OpeningDesign/Aalseth_Residence/Transfer/20181026 - from Sanitary District - Design drawings/3196 Aalseth.pdf

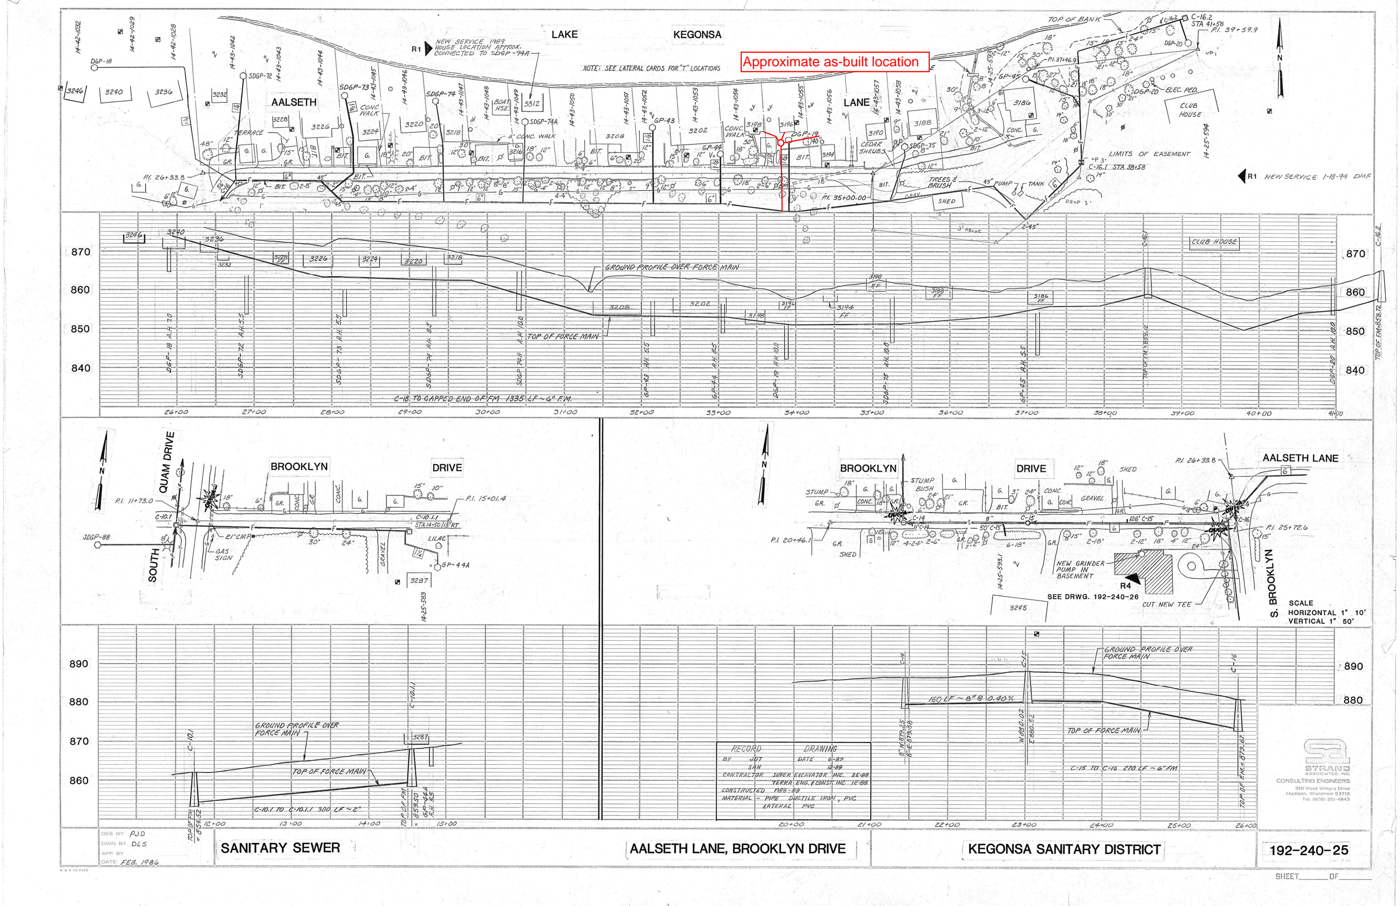
[picture p3: page 1]
