OpeningDesign/Aalseth_Residence/Transfer/20181026 - from Sanitary District - Design drawings/DH152-160002.pdf

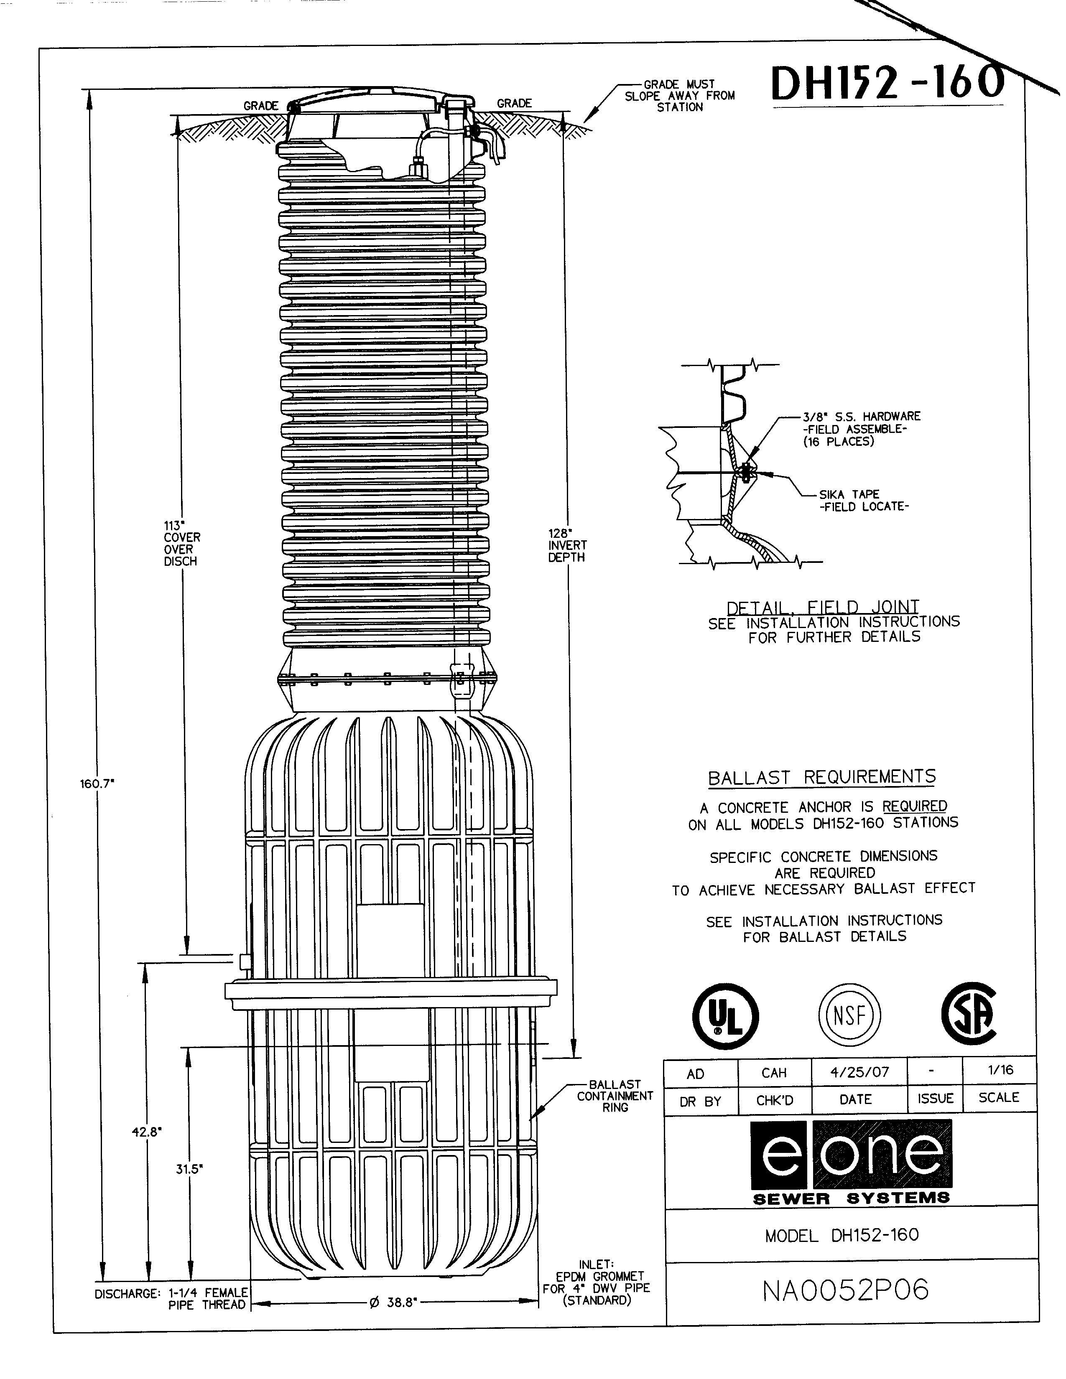
[picture p4: page 1]
