OpeningDesign/Aalseth_Residence/Transfer/20181026 - from Sanitary District - Design drawings/Easement and GP Lateral Card.pdf

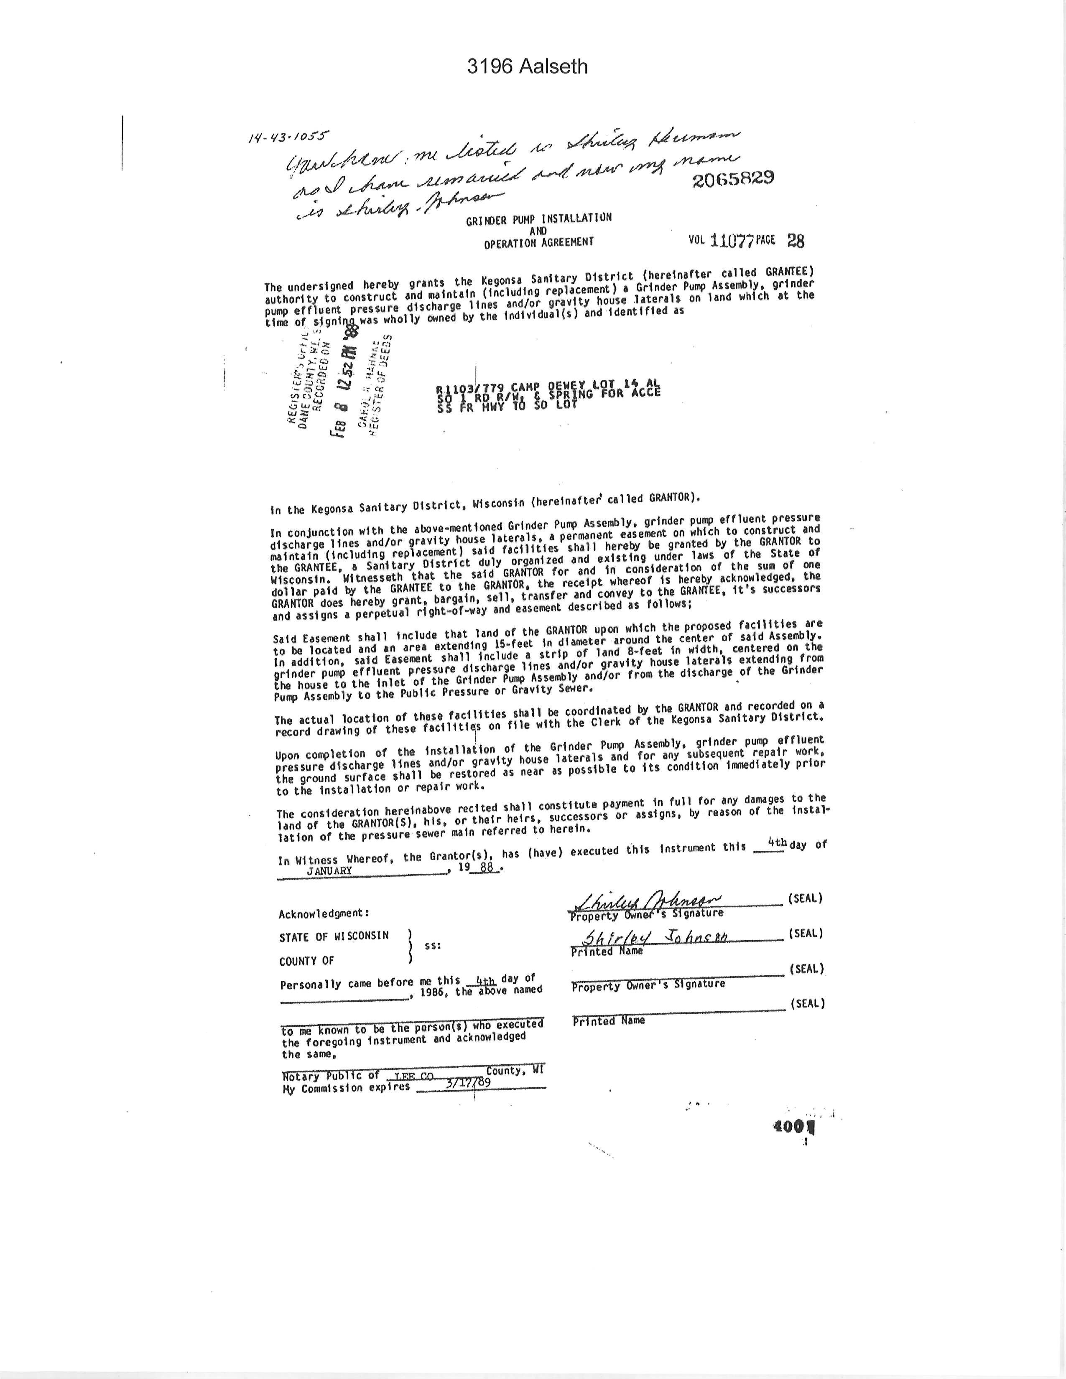
[picture p5: page 1]
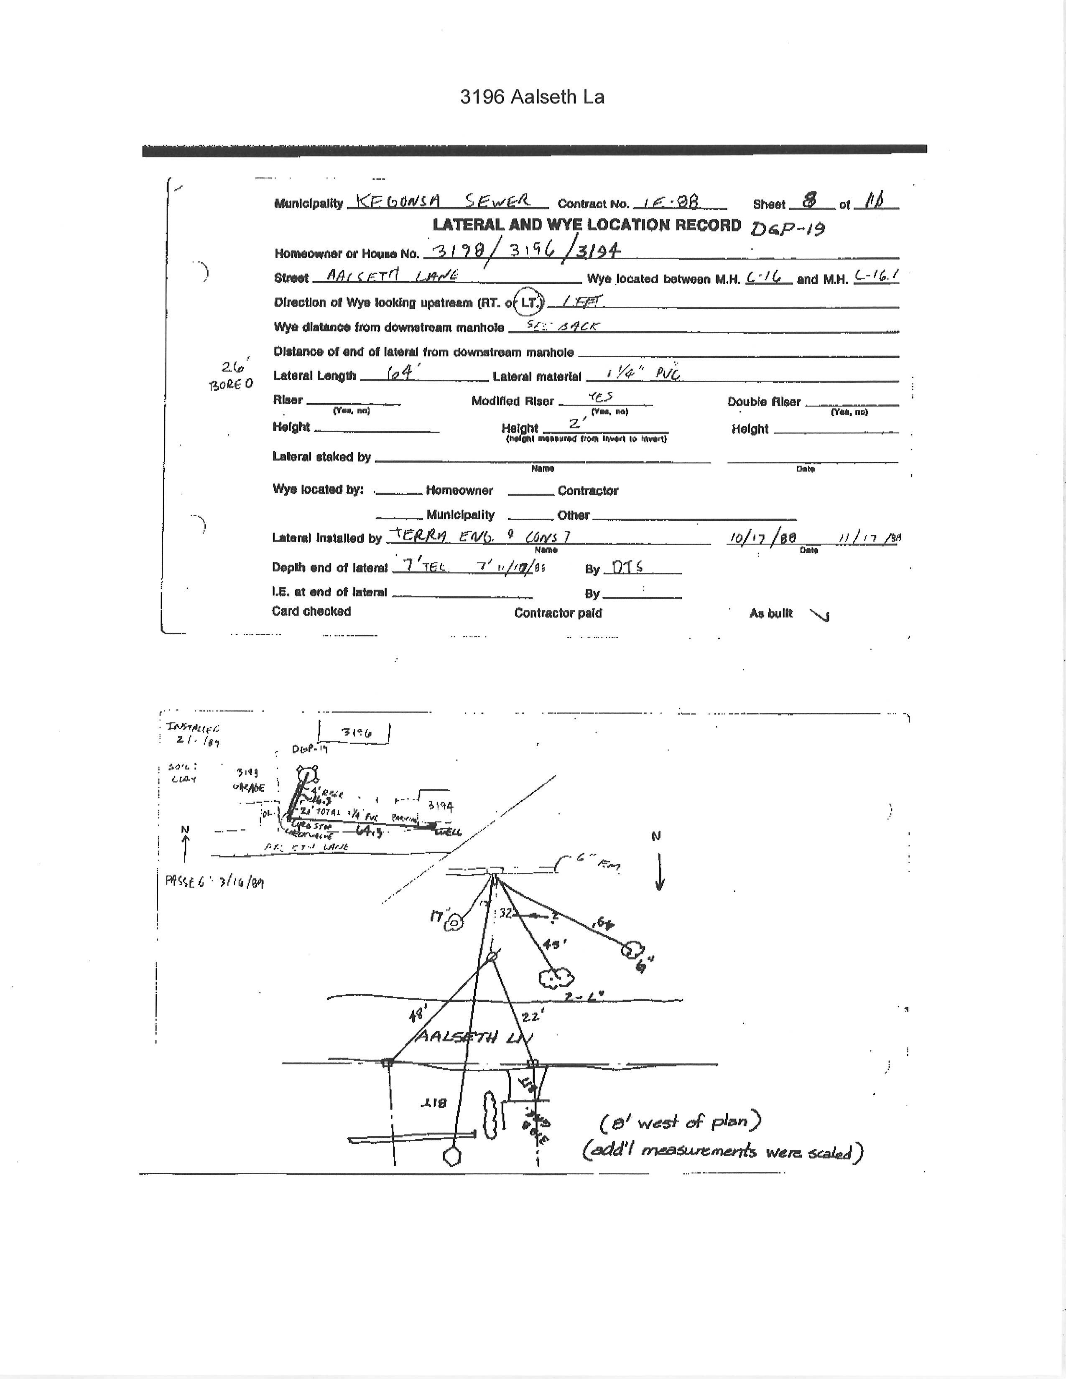
[picture p6: page 2]
