OpeningDesign/Aalseth_Residence/Transfer/20181026 - from Sanitary District - Design drawings/GP Detail.pdf

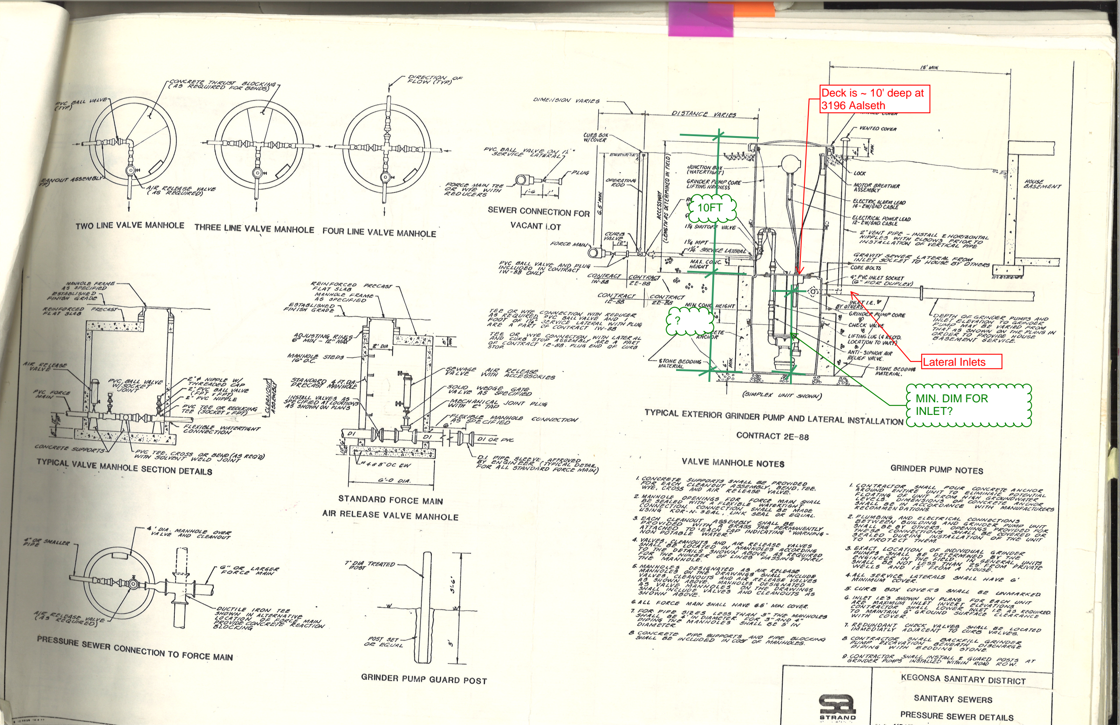
[picture p7: page 1]
