OpeningDesign/Aalseth_Residence/Transfer/20191013 - from STRUCT - stair details/2019-10-13 Cantilevered Stair Details.pdf

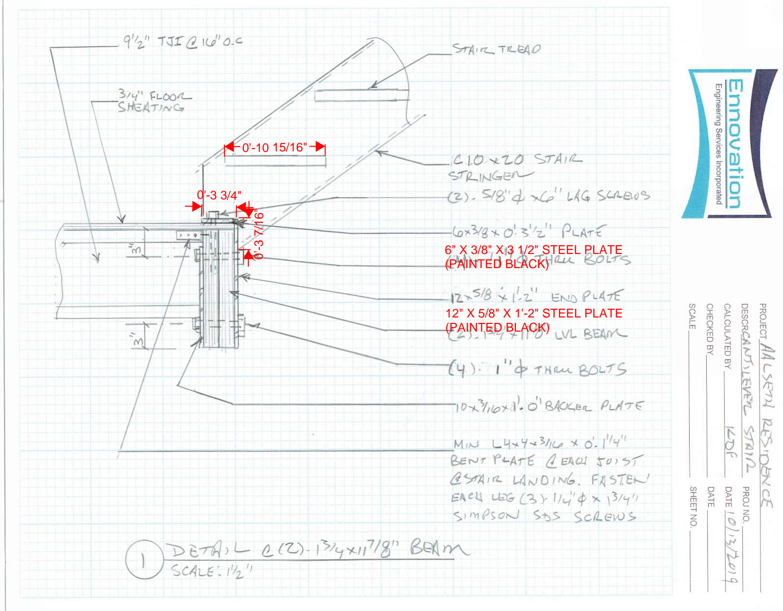
[picture p8: page 1]
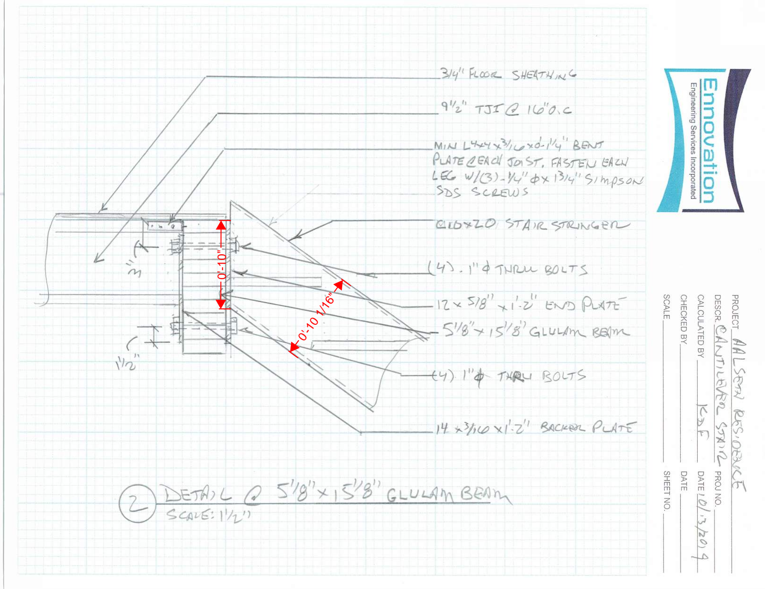
[picture p9: page 2]
