OpeningDesign/Aalseth_Residence/Models & CAD/BIM/Renderings/20191110 - stair/Enscape_2019-11-10-22-44-05.png

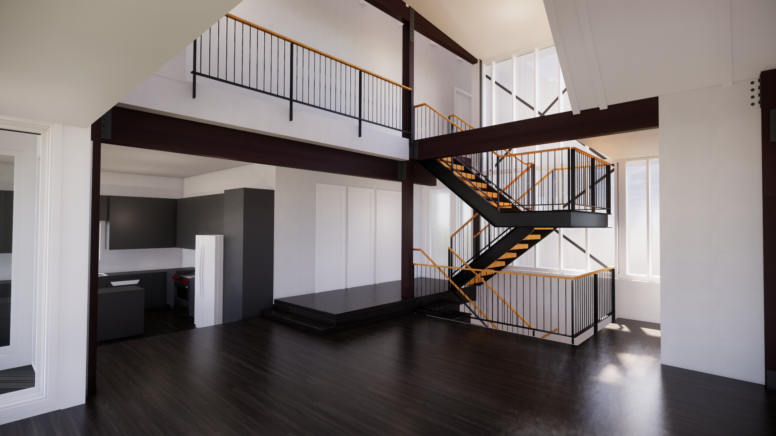
Models & CAD/BIM/Renderings/20191110 - stair/Enscape_2019-11-10-22-44-05.png
