OpeningDesign/Aalseth_Residence/Models & CAD/BIM/Renderings/20191110 - stair/Enscape_2019-11-10-23-39-31.png

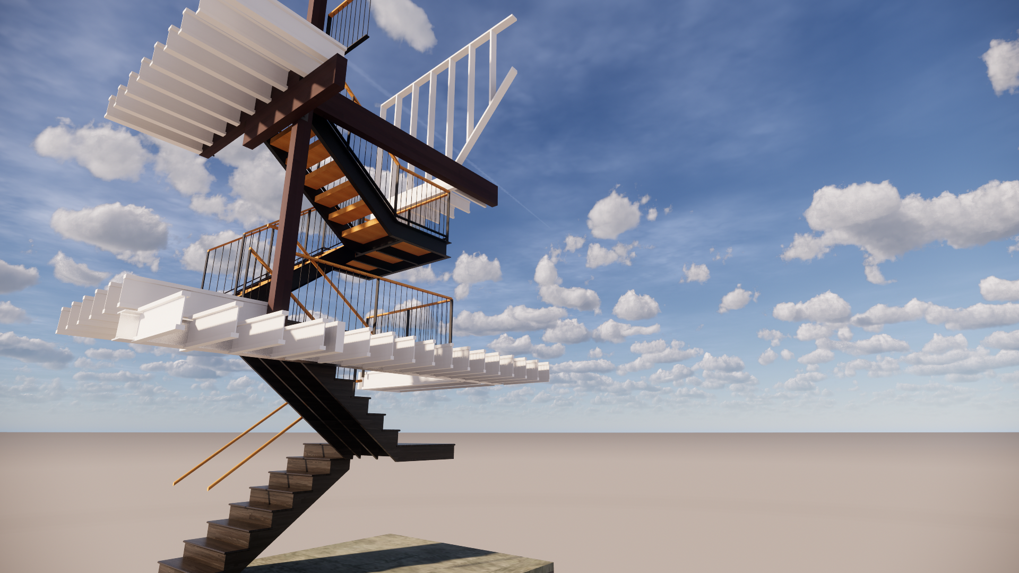
Models & CAD/BIM/Renderings/20191110 - stair/Enscape_2019-11-10-23-39-31.png
