OpeningDesign/Aalseth_Residence/Research and CA/Research and Submittals/_Existing Conditions & Code Research/Existing Conditions/2018-06-04_13-52-42_chrome.jpg

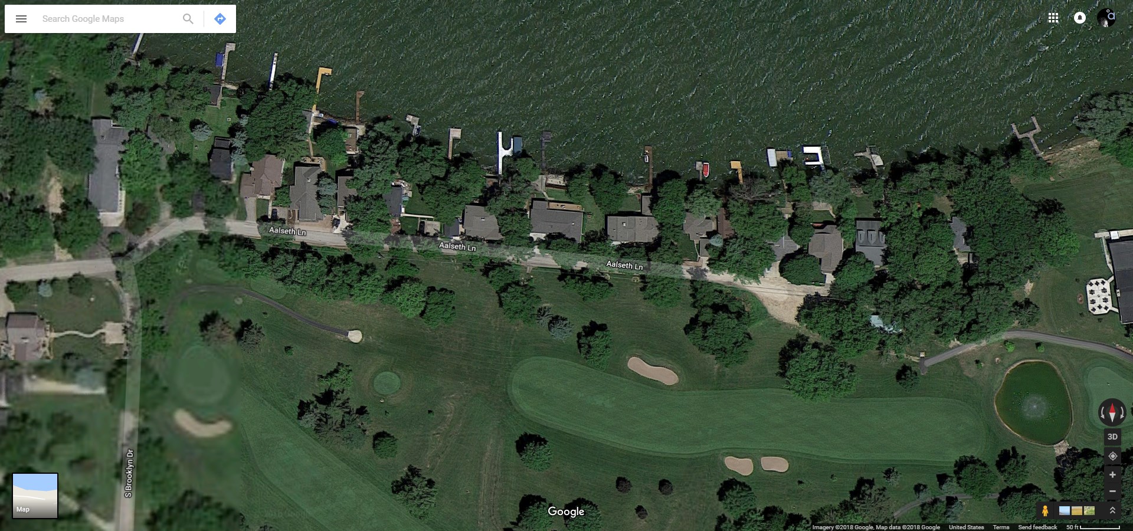
Research and CA/Research and Submittals/_Existing Conditions & Code Research/Existing Conditions/2018-06-04_13-52-42_chrome.jpg
