OpeningDesign/Aalseth_Residence/Research and CA/Research and Submittals/_Existing Conditions & Code Research/Existing Conditions/topo.jpg

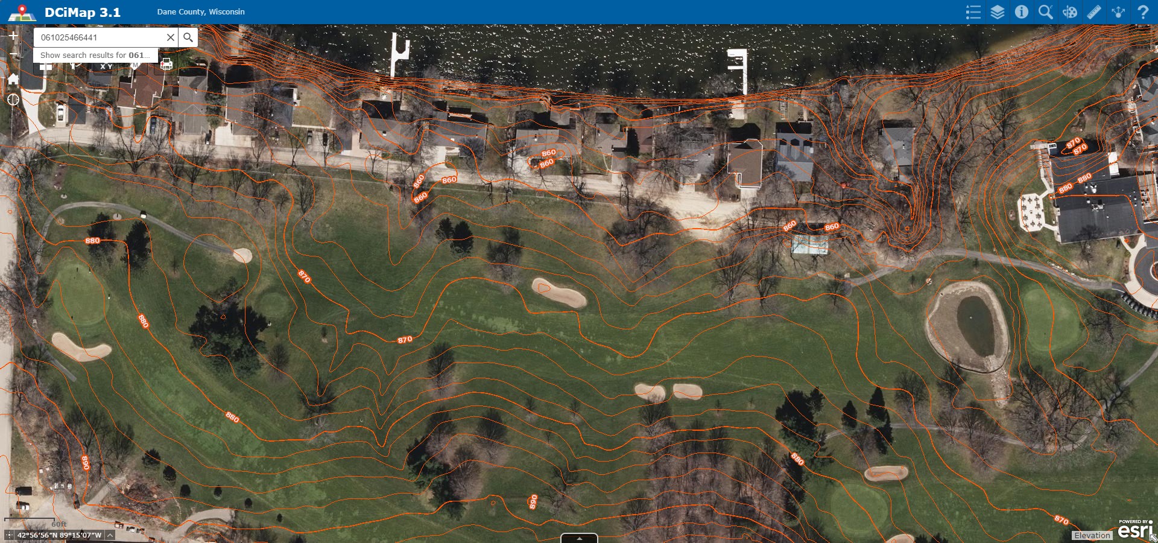
Research and CA/Research and Submittals/_Existing Conditions & Code Research/Existing Conditions/topo.jpg
