OpeningDesign/Aalseth_Residence/Research and CA/Research and Submittals/_Existing Conditions & Code Research/Existing Conditions/zoning area map.png

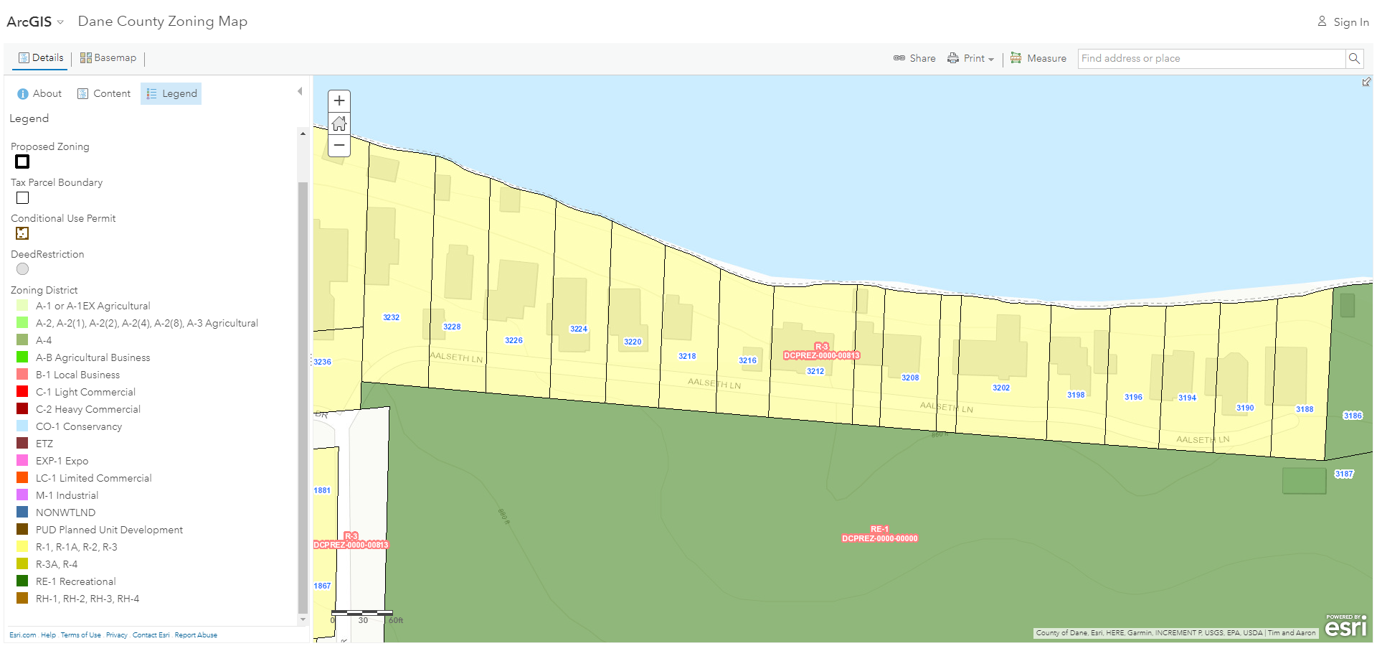
Research and CA/Research and Submittals/_Existing Conditions & Code Research/Existing Conditions/zoning area map.png
