OpeningDesign/Aalseth_Residence/Research and CA/Research and Submittals/A10 Foundations/A1010 Standard Foundations/Holddowns/2018-12-19_11-43-12.png

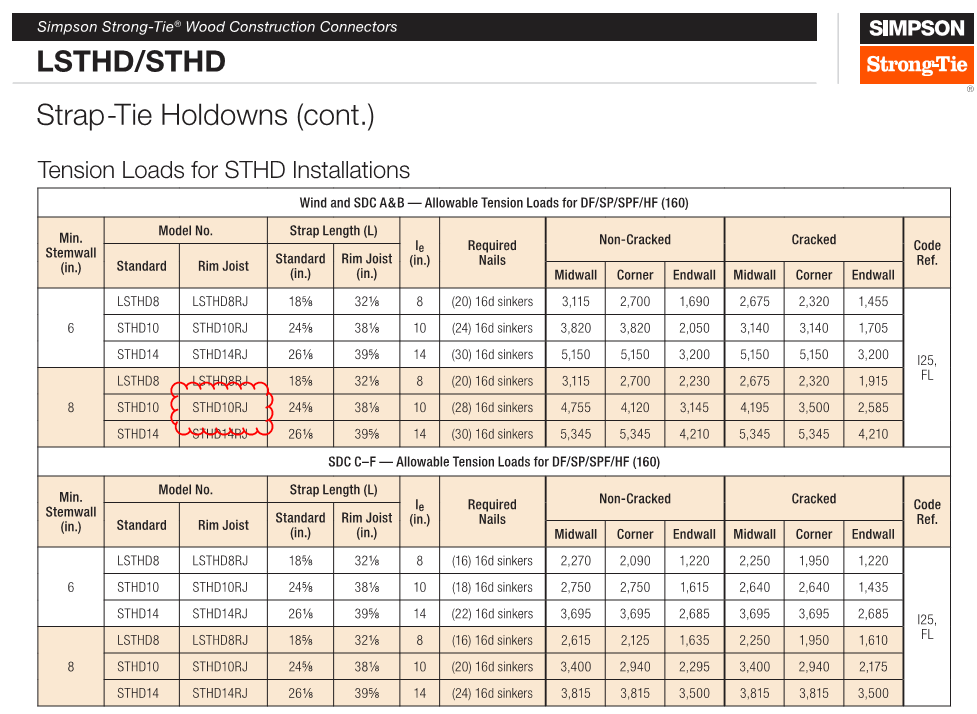
Research and CA/Research and Submittals/A10 Foundations/A1010 Standard Foundations/Holddowns/2018-12-19_11-43-12.png
