OpeningDesign/Aalseth_Residence/Research and CA/Site Reports and Photos/20190711_182300.jpg

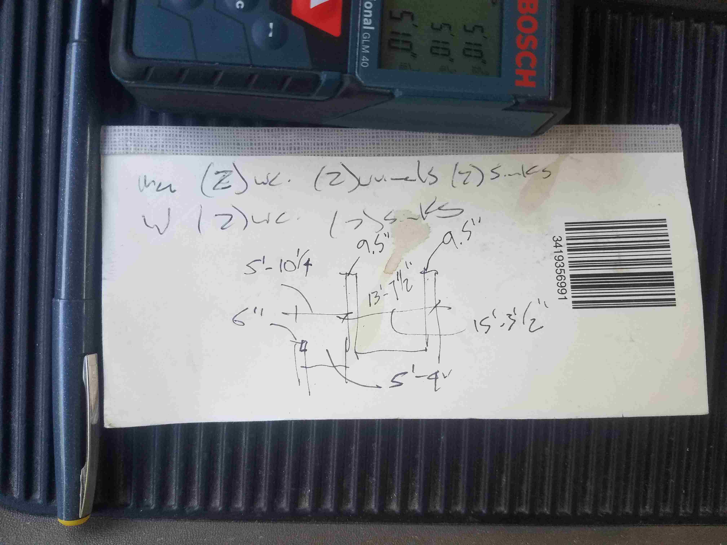
Research and CA/Site Reports and Photos/20190711_182300.jpg
