OpeningDesign/Aalseth_Residence/Transfer/20180706 - owner review/Enscape_2018-07-06-13-01-36.png

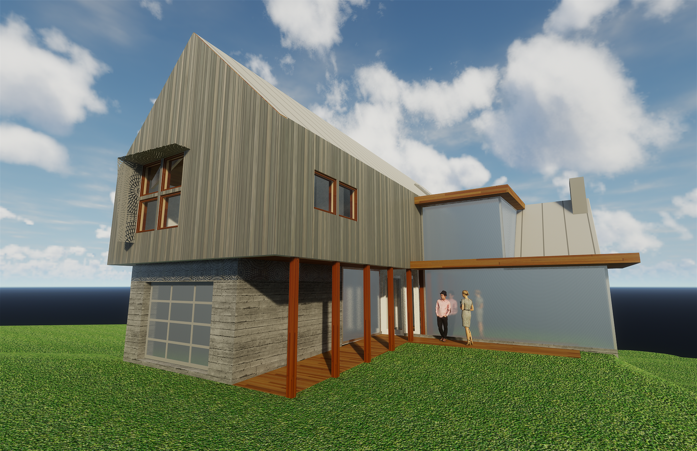
Transfer/20180706 - owner review/Enscape_2018-07-06-13-01-36.png
