OpeningDesign/Aalseth_Residence/Transfer/20180706 - owner review/jpgs/20180706 - Aalseth_Residence - Schematic Drawings Page 005.jpg

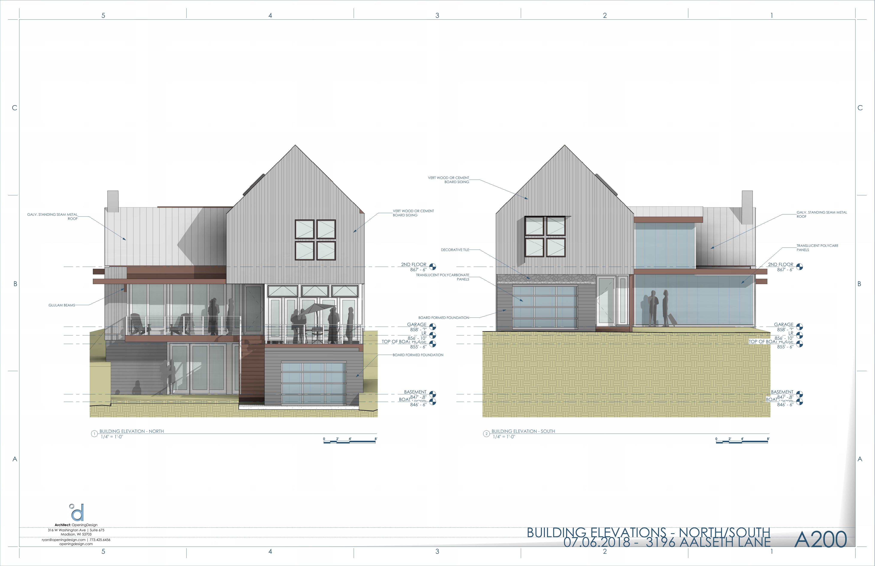
Transfer/20180706 - owner review/jpgs/20180706 - Aalseth_Residence - Schematic Drawings Page 005.jpg
