OpeningDesign/Aalseth_Residence/Transfer/20180711 - DWG to civil/20180711 - Aalseth_Residence - marked up Page 007.jpg

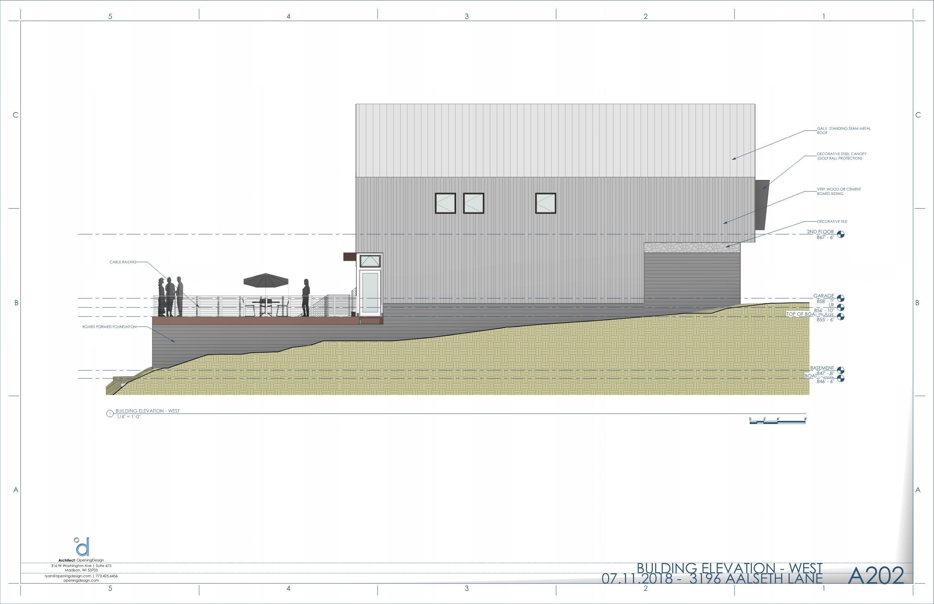
Transfer/20180711 - DWG to civil/20180711 - Aalseth_Residence - marked up Page 007.jpg
