OpeningDesign/Aalseth_Residence/Transfer/20181002 - from civil - marked up drawings/DitchVelocity Page 001.jpg

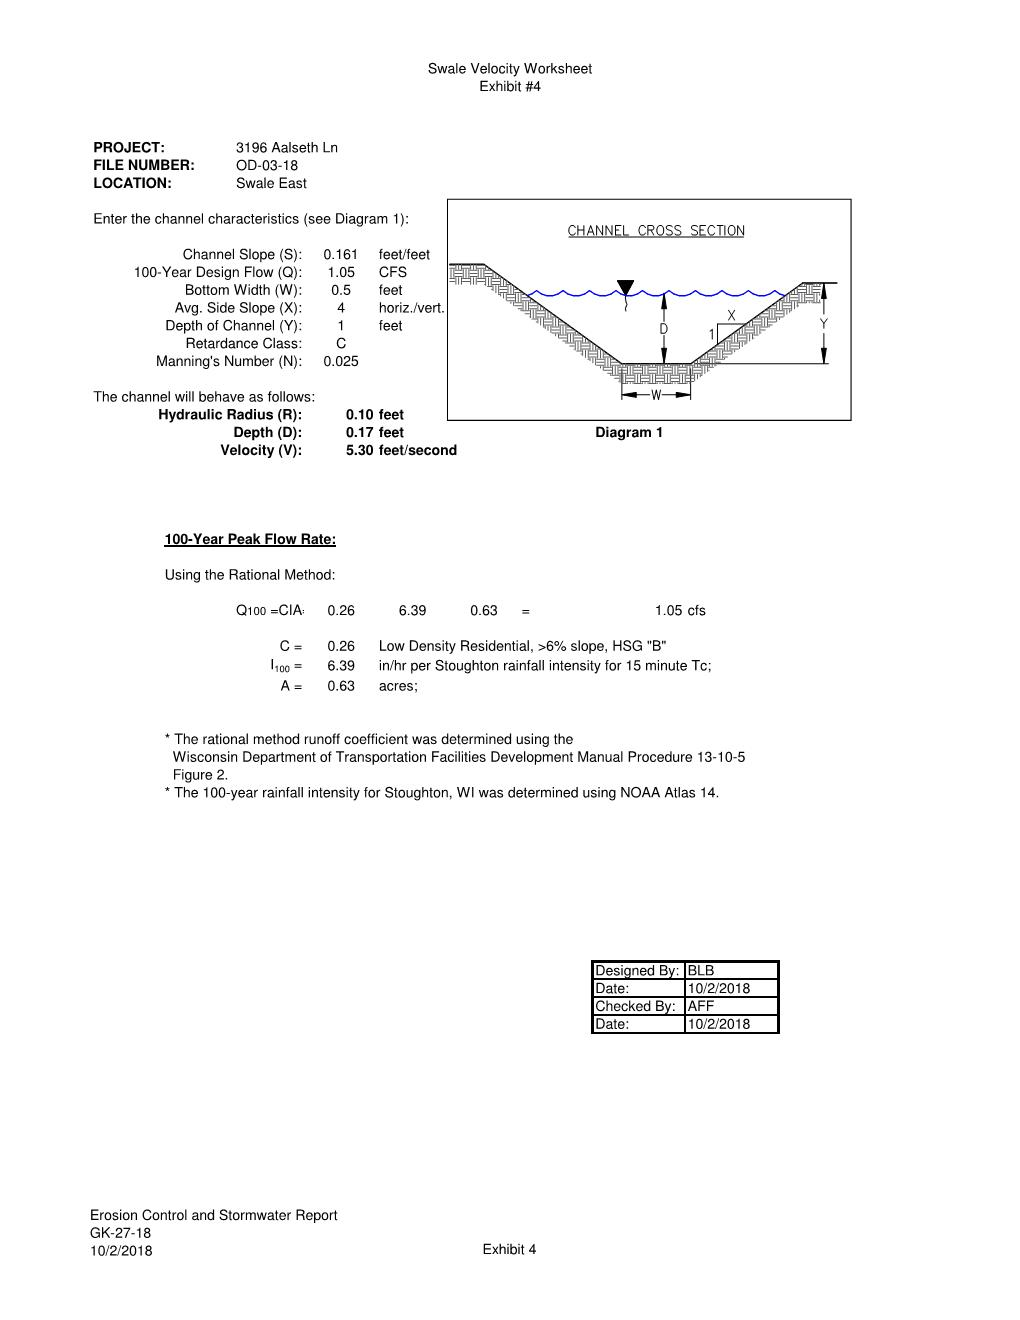
Transfer/20181002 - from civil - marked up drawings/DitchVelocity Page 001.jpg
