OpeningDesign/Aalseth_Residence/Transfer/20181002 - from civil - marked up drawings/ErosionMat.jpg

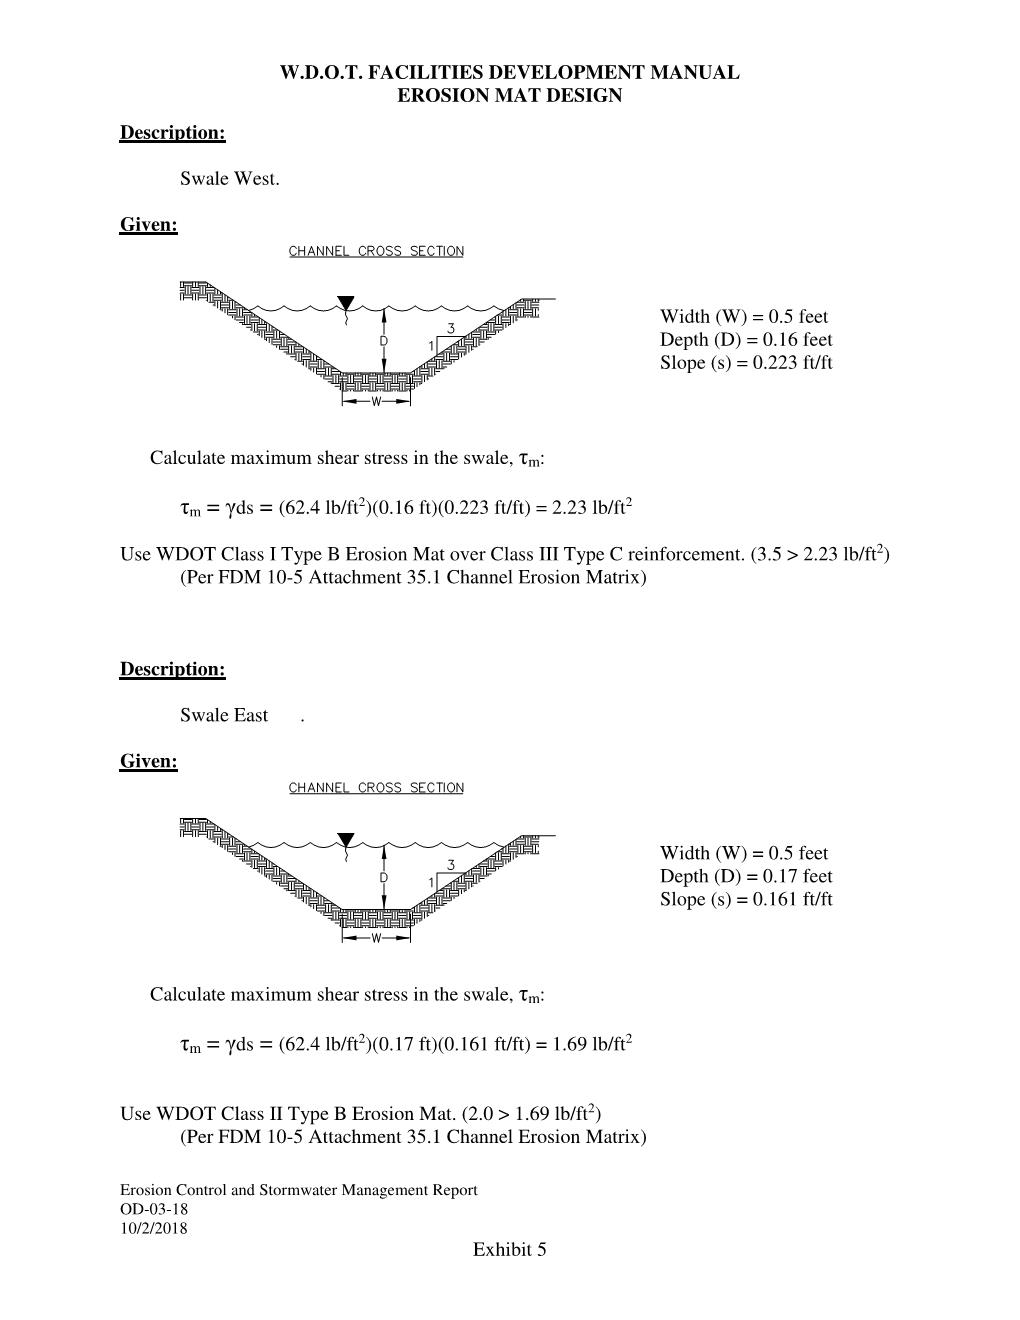
Transfer/20181002 - from civil - marked up drawings/ErosionMat.jpg
