OpeningDesign/Aalseth_Residence/Transfer/20181002 - from civil - marked up drawings/SwaleDetails.jpg

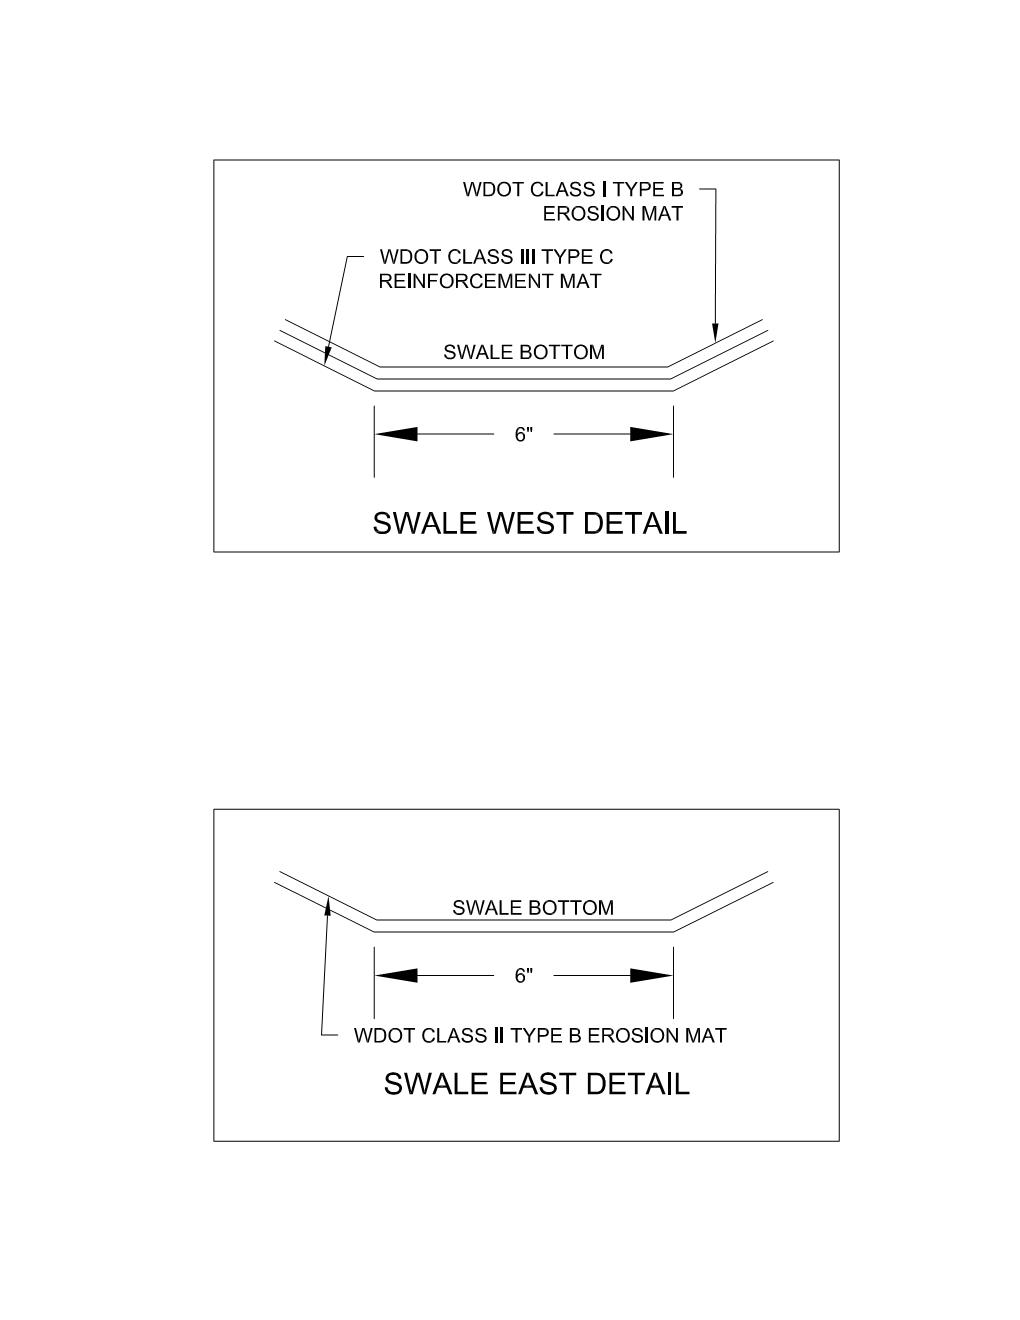
Transfer/20181002 - from civil - marked up drawings/SwaleDetails.jpg
