OpeningDesign/Aalseth_Residence/Transfer/20190108 - from Dane County - Notice to submit a location survey/20190125_095326.jpg

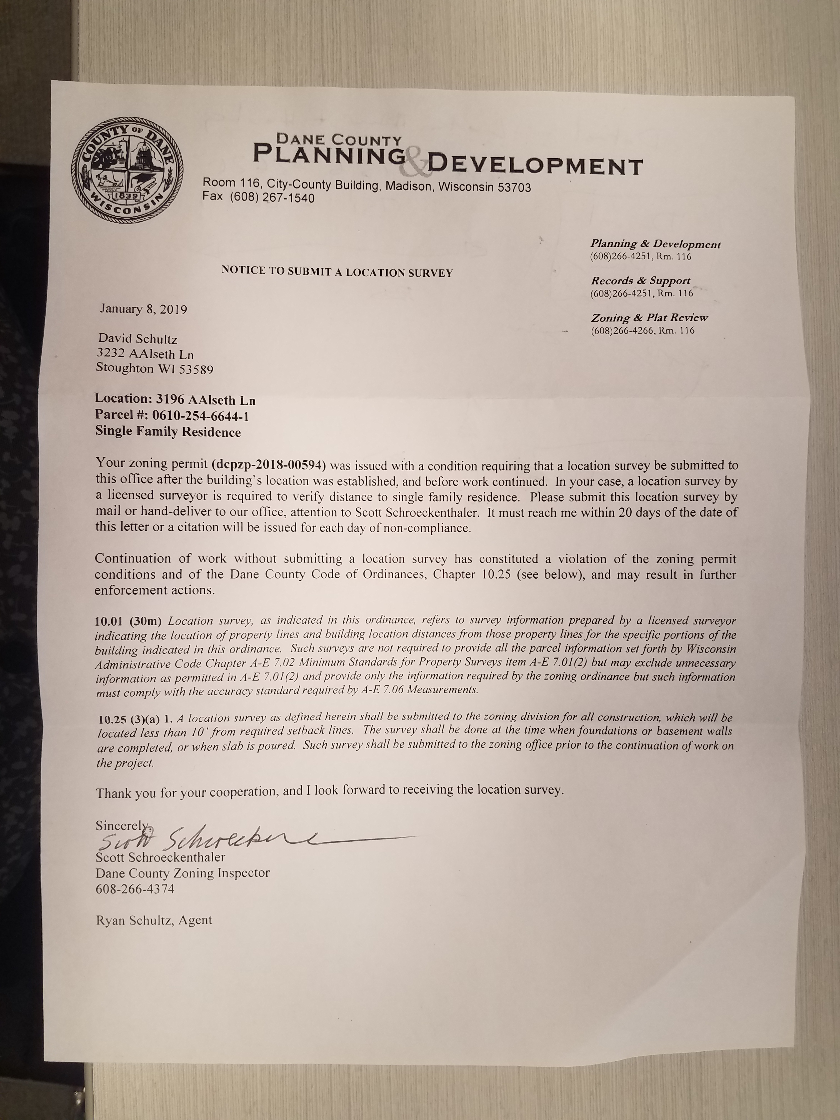
Transfer/20190108 - from Dane County - Notice to submit a location survey/20190125_095326.jpg
