OpeningDesign/Aalseth_Residence/Transfer/20190110 - ASK-01 - seam detail in concrete/20190110 - ASK-01 - seam detail in concrete2.jpg

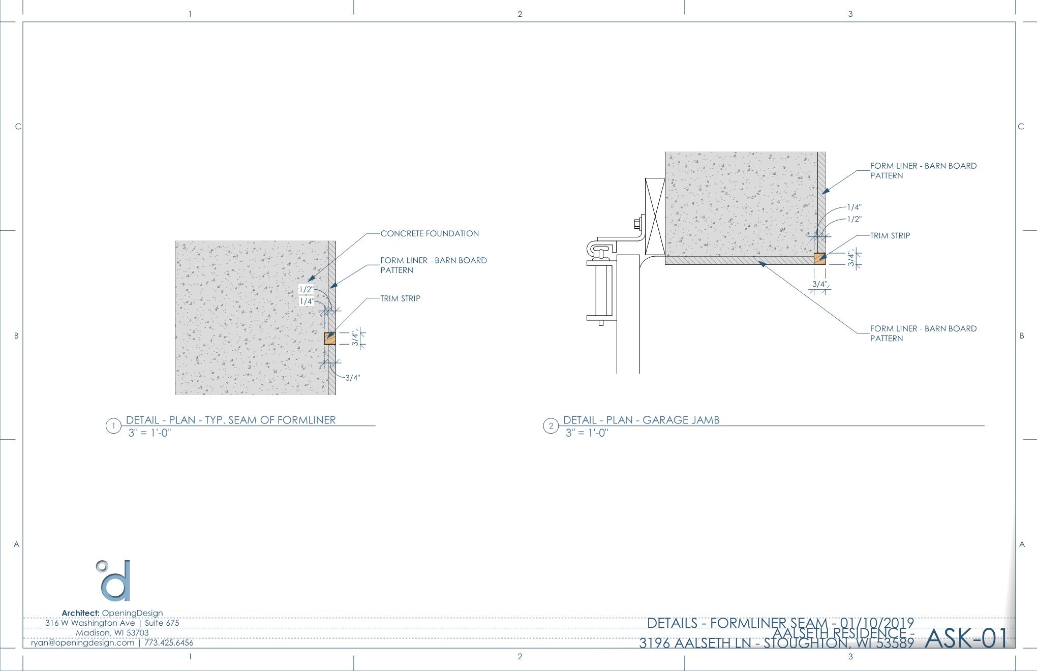
Transfer/20190110 - ASK-01 - seam detail in concrete/20190110 - ASK-01 - seam detail in concrete2.jpg
