OpeningDesign/Aalseth_Residence/Transfer/20190110 - ASK-01 - seam detail in concrete/201901101700 - ASK-01 - seam detail in concrete.jpg

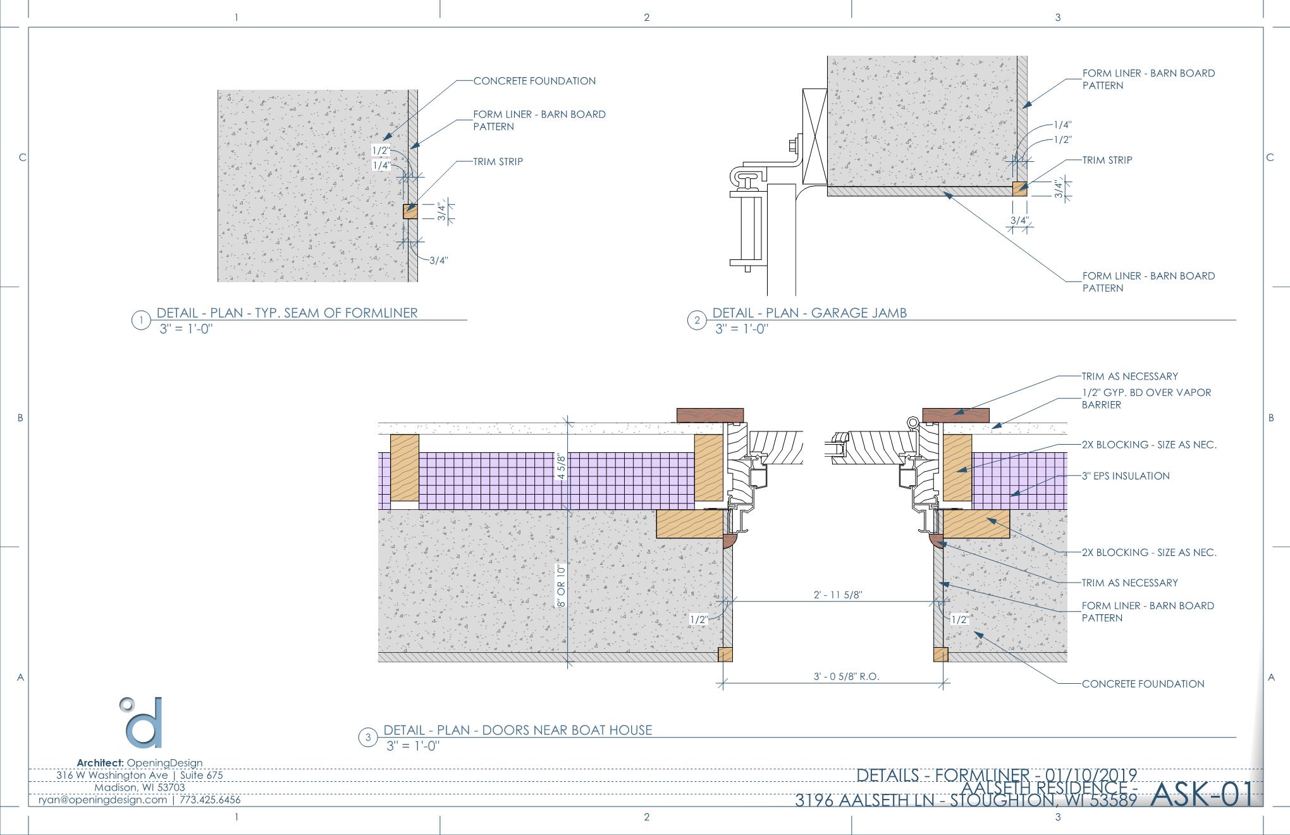
Transfer/20190110 - ASK-01 - seam detail in concrete/201901101700 - ASK-01 - seam detail in concrete.jpg
