OpeningDesign/Aalseth_Residence/Transfer/20190323 - meeting with potential owners/2019-03-21 18.45.19.jpg

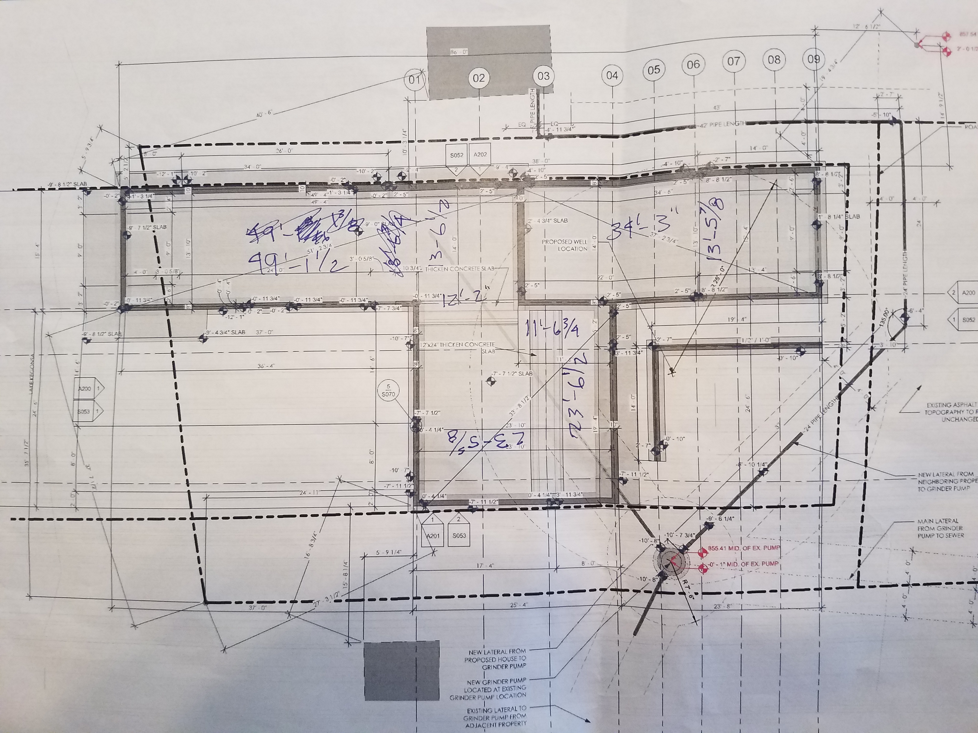
Transfer/20190323 - meeting with potential owners/2019-03-21 18.45.19.jpg
