OpeningDesign/Aalseth_Residence/Transfer/20190323 - meeting with potential owners/2019-03-23 11.27.37.jpg

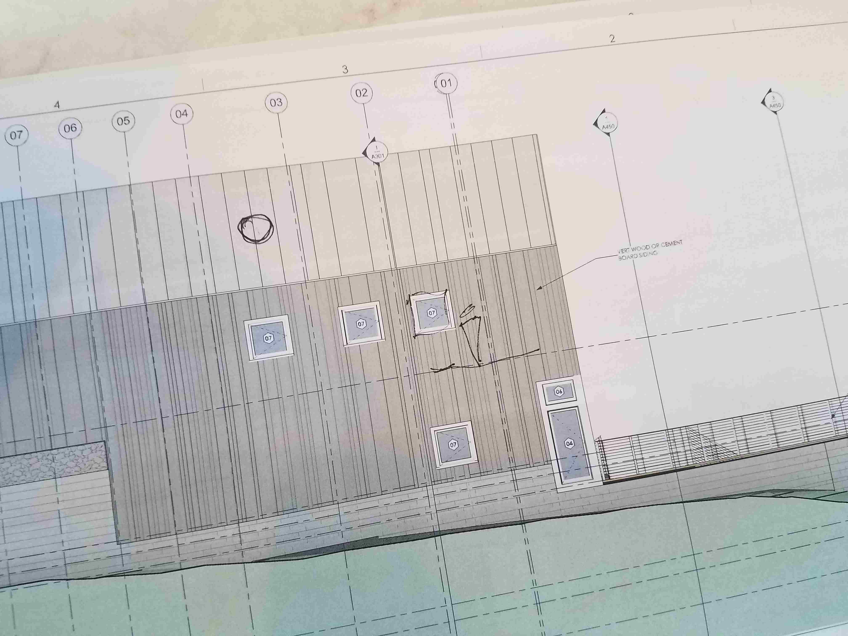
Transfer/20190323 - meeting with potential owners/2019-03-23 11.27.37.jpg
