OpeningDesign/Aalseth_Residence/Transfer/20190409 - Internal for Review/3196 Aalseth Lane 102.jpg

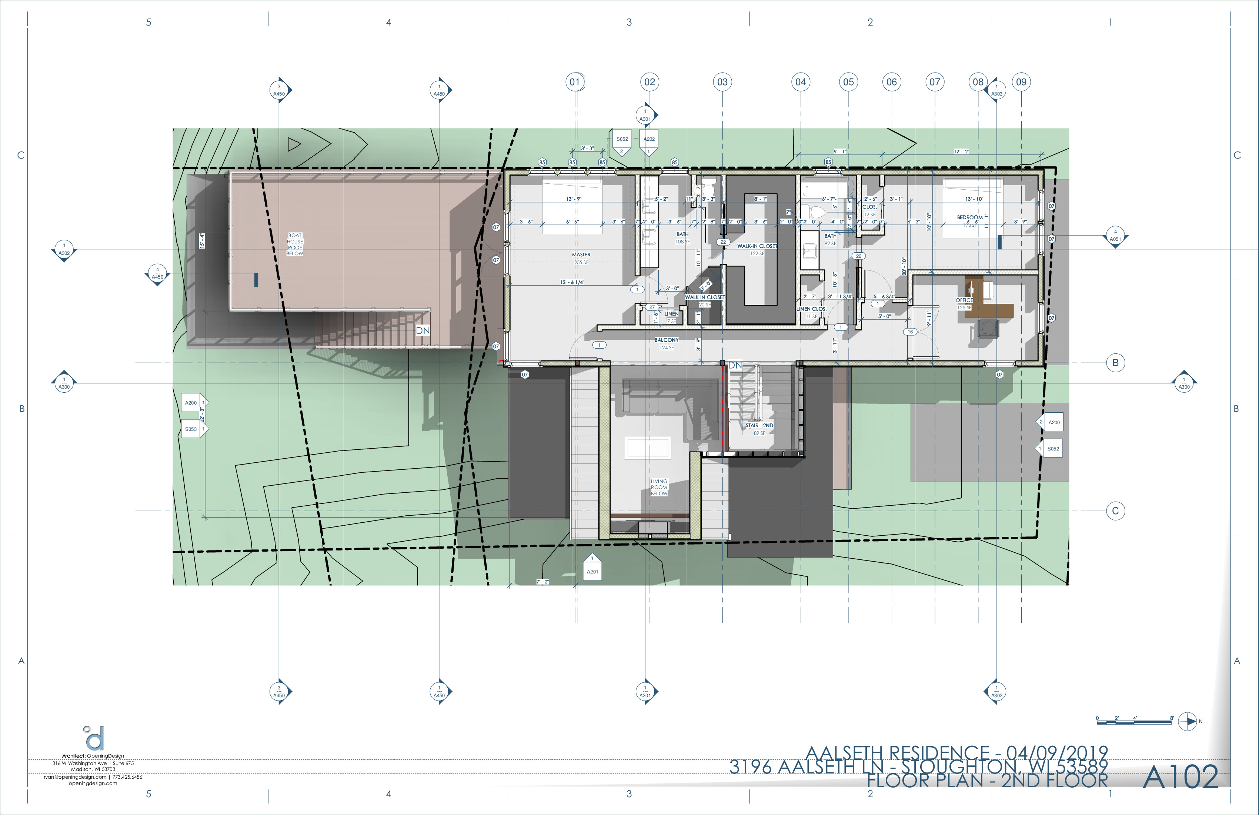
Transfer/20190409 - Internal for Review/3196 Aalseth Lane 102.jpg
