OpeningDesign/Aalseth_Residence/Transfer/20190414 - TO CONC. SUB - LATEST DETAILS/20190414 - 3196 Aalseth Lane - Foundation Details Page 001.jpg

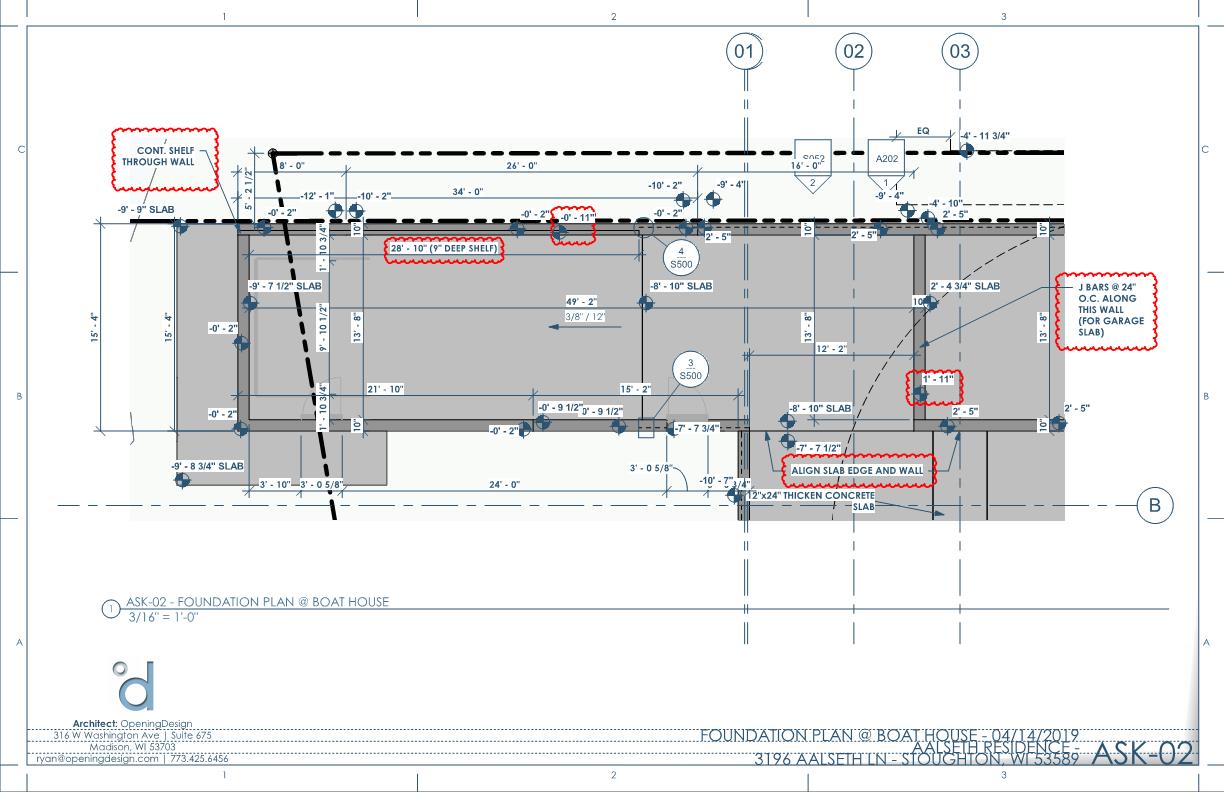
Transfer/20190414 - TO CONC. SUB - LATEST DETAILS/20190414 - 3196 Aalseth Lane - Foundation Details Page 001.jpg
