OpeningDesign/Aalseth_Residence/Transfer/20190603 - to conc sub - location of footings/20190603 - 3196 Aalseth Lane.jpg

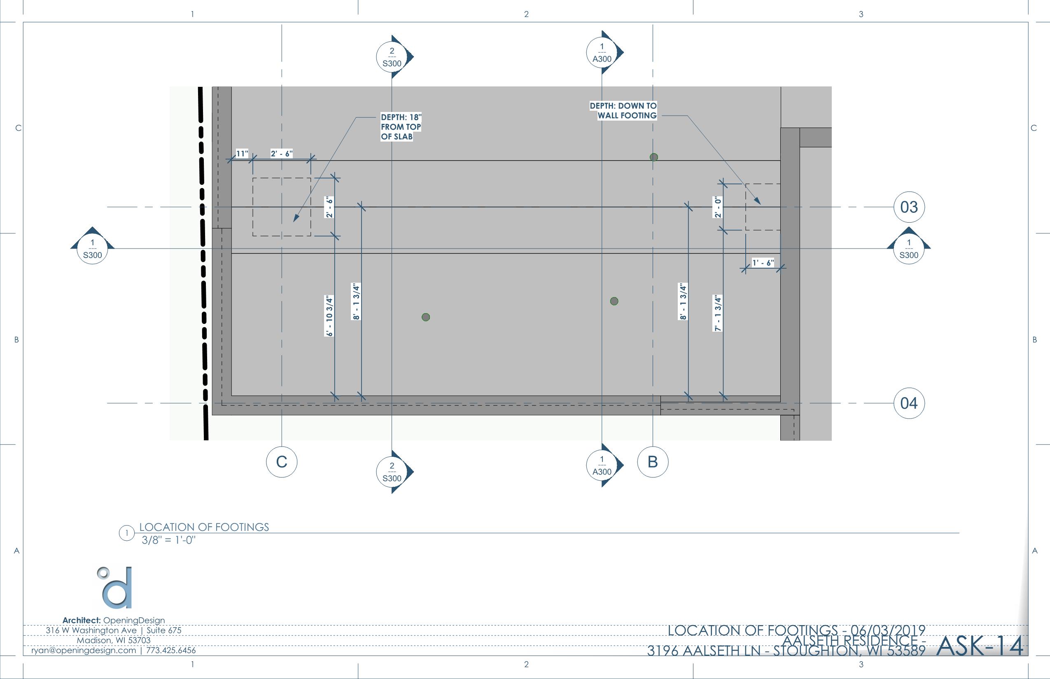
Transfer/20190603 - to conc sub - location of footings/20190603 - 3196 Aalseth Lane.jpg
