OpeningDesign/Aalseth_Residence/Transfer/20190605 - to concrete conc - knee wall clarifications/20190605 - 3196 Aalseth Lane.jpg

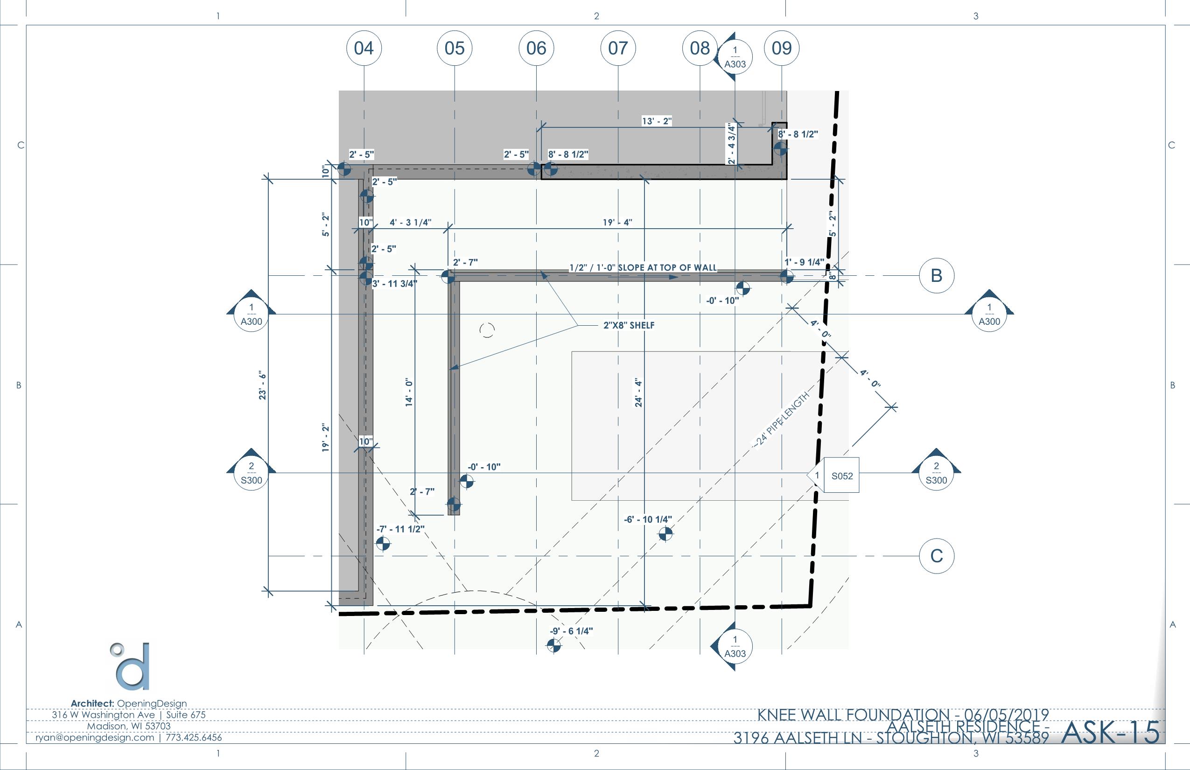
Transfer/20190605 - to concrete conc - knee wall clarifications/20190605 - 3196 Aalseth Lane.jpg
