OpeningDesign/Aalseth_Residence/Transfer/20190711 - from Lumber Yard - TJI spec/SCHULTZ AALSETH LIVING ROOM JOIST CANTILEVER Page 002.jpg

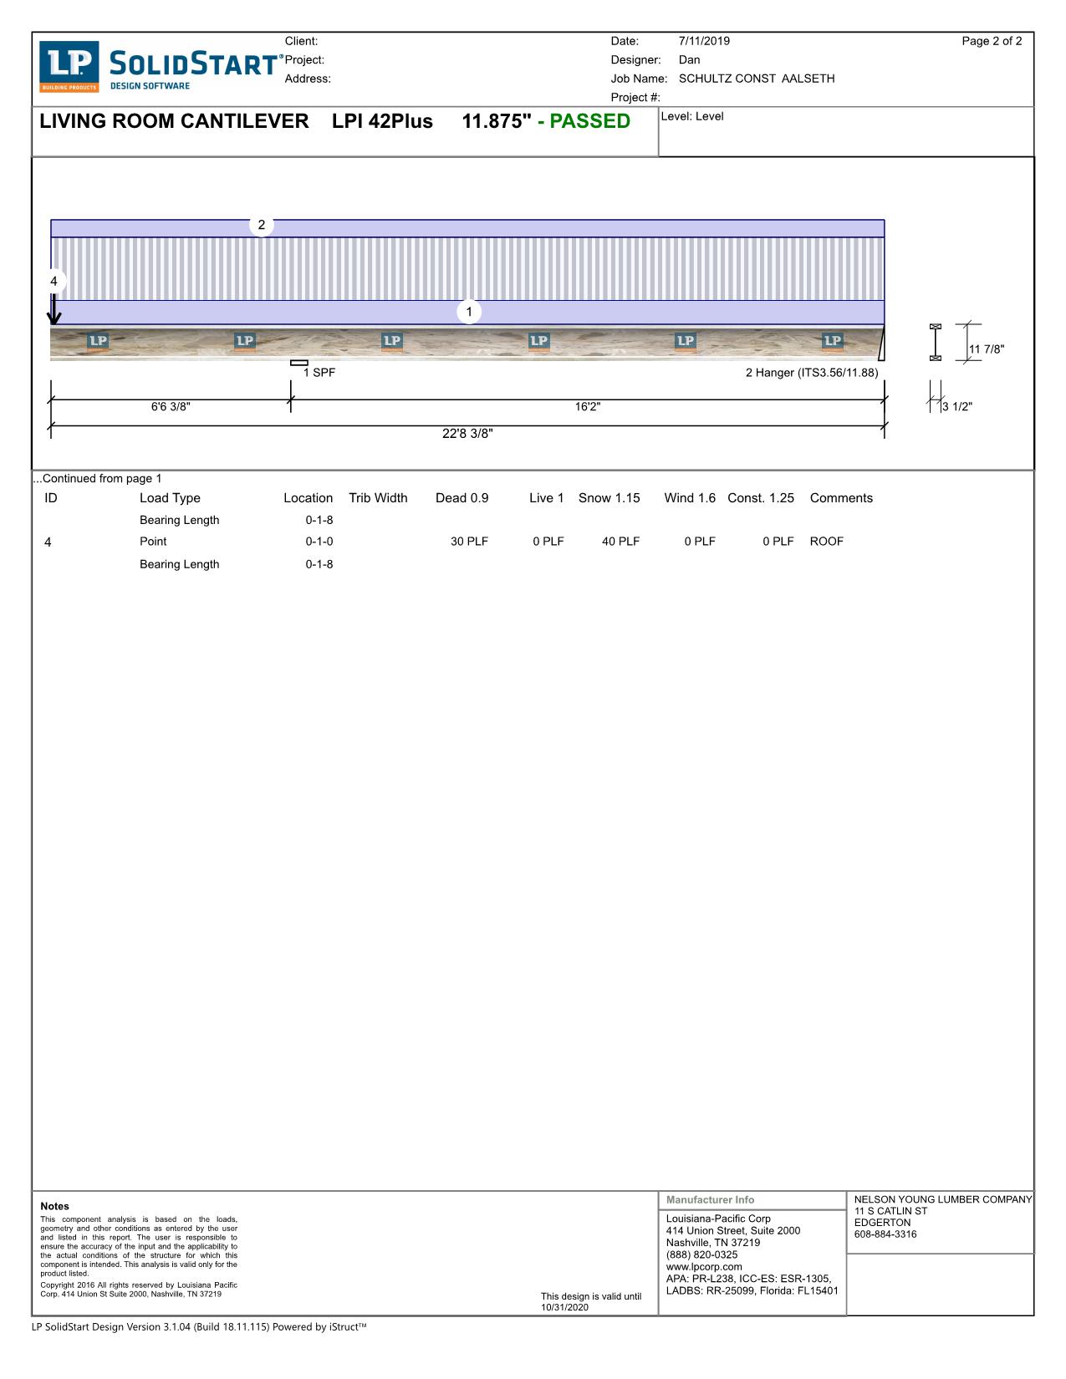
Transfer/20190711 - from Lumber Yard - TJI spec/SCHULTZ AALSETH LIVING ROOM JOIST CANTILEVER Page 002.jpg
