OpeningDesign/Aalseth_Residence/Transfer/20190603 - to steel fabricator - steel details/20190603 - 3196 Aalseth Lane - steel details.pdf

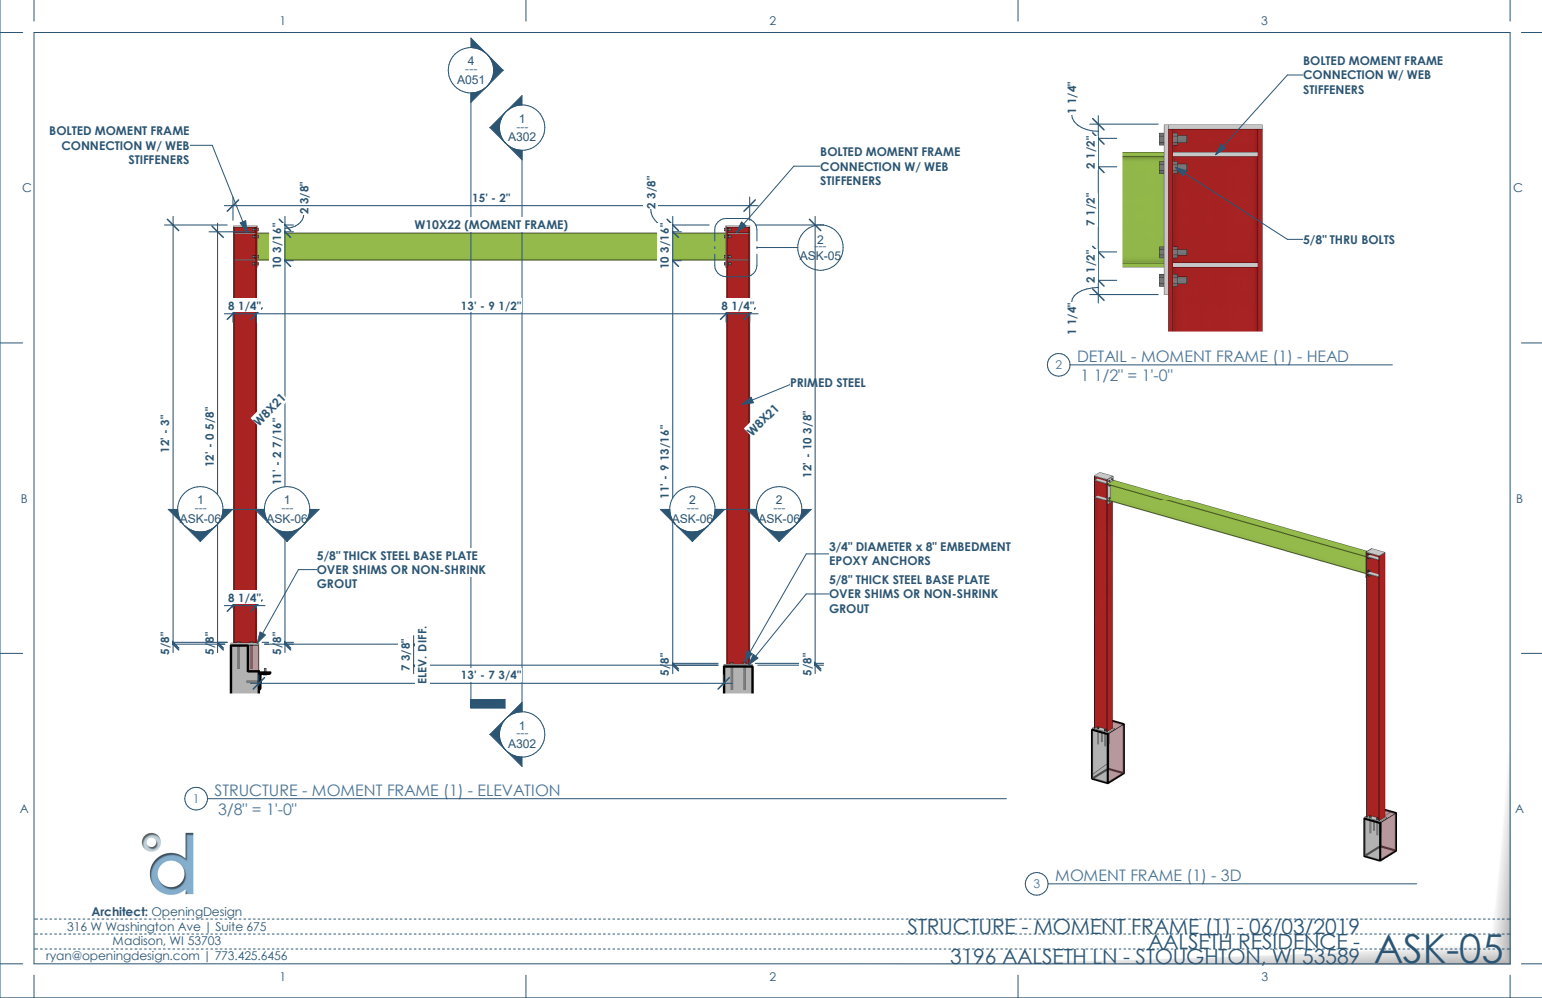
[picture p71: page 1]
PRIMED STEEL; --- ASK-05; W10X22 (MOMENT FRAME); STIFFENERS; ELEV. DIFF.; ASK-06; 5/8" THRU BOLTS; Madison, WI 53703; ryan@openingdesign.com | 773.425.6456; 3196 AALSETH LN - STOUGHTON, WI 53589 AALSETH RESIDENCE - STRUCTURE - MOMENT FRAME (1) - 06/03/2019 ASK-05; MOMENT FRAME (1) - 3D

BOLTED MOMENT FRAME
CONNECTION W/ WEB
STIFFENERS

DETAIL - MOMENT FRAME (1) - HEAD

3/4" DIAMETER x 8" EMBEDMENT
EPOXY ANCHORS
5/8" THICK STEEL BASE PLATE
OVER SHIMS OR NON-SHRINK
GROUT

STRUCTURE - MOMENT FRAME (1) - ELEVATION

Architect: OpeningDesign
316 W Washington Ave | Suite 675

3/4" DIAMETER x 8" EMBEDMENT; EPOXY ANCHORS; GROUT; Architect: OpeningDesign; ryan@openingdesign.com | 773.425.6456; 3196 AALSETH LN - STOUGHTON, WI 53589 AALSETH RESIDENCE - STRUCTURE - MOMENT FRAME (1) - BASE PLATES - 06/03/2019; ASK-06

OVER SHIMS OR NON-SHRINK

5/8" THICK STEEL BASE PLATE

1 PLAN DETAIL AT MOMENT FRAME (1) (EAST)

2 PLAN DETAIL AT MOMENT FRAME (1) (WEST)

C | B

ASK-08; Architect: OpeningDesign; ryan@openingdesign.com | 773.425.6456; 3196 AALSETH LN - STOUGHTON, WI 53589 AALSETH RESIDENCE - MOMENT FRAME (2) - 06/03/2019 ASK-07; STRUCTURE - MOMENT FRAME (2) - ELEVATION; MOMENT FRAME (2) - 3D

4"x6"x1/4" SHEAR TAB WITH (2)
3/4" DIAMETER A325 BOLTS

5/8" THICK STEEL BASE PLATE
OVER SHIMS OR NON-SHRINK
GROUT

3/4" DIAMETER x 8" EMBEDMENT; EPOXY ANCHORS; -SHRINK; GROUT; Architect: OpeningDesign; ryan@openingdesign.com | 773.425.6456; 3196 AALSETH LN - STOUGHTON, WI 53589 AALSETH RESIDENCE - STRUCTURE - MOMENT FRAME (2) - PLAN DETAILS - 06/03/2019; ASK-08

5/8" THICK STEEL BASE PLATE

OVER SHIMS OR NON

2 MOMENT FRAME (2) -BASE - WEST

MOMENT FRAME (2) -BASE - EAST

ASK-10; 3/4" DIAMETER X 5" EMBEDMENT EXPANSION ANCHORS @ 24" O.C.; 3/4" DIAMETER x 2" EMBEDMENT EXPANSION ANCHORS @ 3' -O" O.C.; GALVANIZED L6X4X1/2 (LLV) BEARING ANGLE; Architect: OpeningDesign; ryan@openingdesign.com | 773.425.6456; 3196 AALSETH LN - STOUGHTON, WI 53589 AALSETH RESIDENCE - BOAT HOUSE - STEEL ANGLES - 06/03/2019 ASK-11

STEEL ANGLE - BOAT HOUSE - LOOKING EAST

STEEL ANGLE - BOAT HOUSE - LOOKING WEST

01.1

(RAW STEEL); ASK-12; Architect: OpeningDesign; ryan@openingdesign.com | 773.425.6456; 3196 AALSETH LN - STOUGHTON, WI 53589 AALSETH RESIDENCE - GLULAM CONNECTIONS - 06/03/2019 ASK-12; GLULAM CONNECTIONS; Count; Type; Type Mark

5"x5"x5/16" BENT PLATE STEEL
(RAW STEEL)

3/4" LAG BOLT (THRU BOLT IF
PLATE ON OPP. SIDE OF STRUCT
MEMBER)

5/16" PLATE STEEL (RAW STEEL)

GLULAM CONNECTION (1) - VIEW 1

GLULAM CONNECTION (1) - VIEW 2

13 | GLULAM CONNECTION (1) | GL1
5 | GLULAM CONNECTION (2) | GL2

GLULAM CONNECTION (2) - VIEW 1

C | B

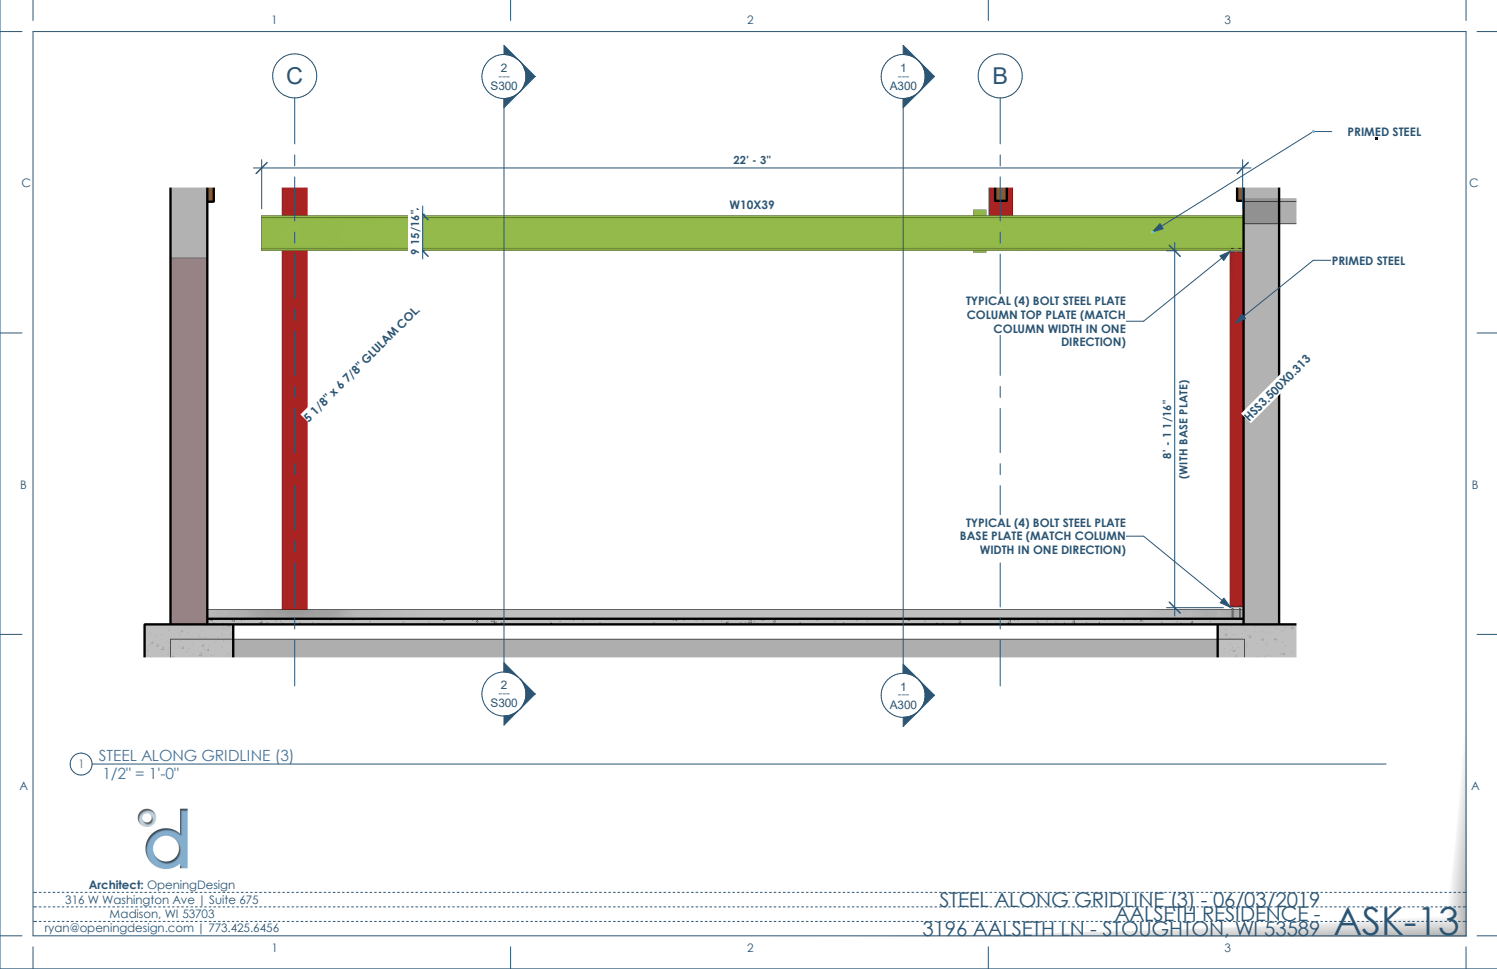
[picture p72: page 7]
PRIMED STEEL; HSS3.500X0.313; 5 1/8" x 6 7/8" GLULAM COL.; DIRECTION); Architect: OpeningDesign; ryan@openingdesign.com | 773.425.6456; 3196 AALSETH LN - STOUGHTON, WI 53589 AALSETH RESIDENCE - STEEL ALONG GRIDLINE (3) - 06/03/2019 ASK-13

TYPICAL (4) BOLT STEEL PLATE
COLUMN TOP PLATE (MATCH
COLUMN WIDTH IN ONE

(WITH BASE PLATE)

BASE PLATE (MATCH COLUMN
WIDTH IN ONE DIRECTION)

STEEL ALONG GRIDLINE (3)
