OpeningDesign/Aalseth_Residence/Research and CA/Research and Submittals/B20 Exterior Vertical Enclosures/B2050 Exterior Doors and Grilles/Garage Doors/Wayne Dalton/452/Track-Selection-Guide-Sectional-Steel-Doors.pdf

# Track Selection Guide

# Wayne Dalton Commercial Sectional Doors

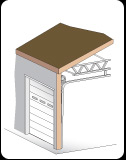
[picture p73: figure]
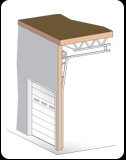
[picture p74: figure]
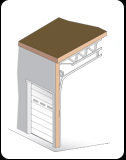
[picture p75: figure]

Standard Lift | High Lift | Roof Pitch
| (break-away standard; | (standard or high lift)
| no break-away available)

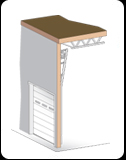
[picture p76: figure]
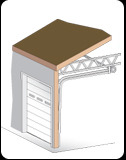
[picture p77: figure]
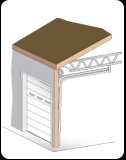
[picture p78: figure]

Vertical Lift | Low Headroom | Low Headroom
(break-away standard; | (rear mount torsion) | (front mount torsion)
no break-away available)
