OpeningDesign/Aalseth_Residence/Transfer/20181019 - to Dane County Zoning - Permit/Driveway Construction Permit.pdf

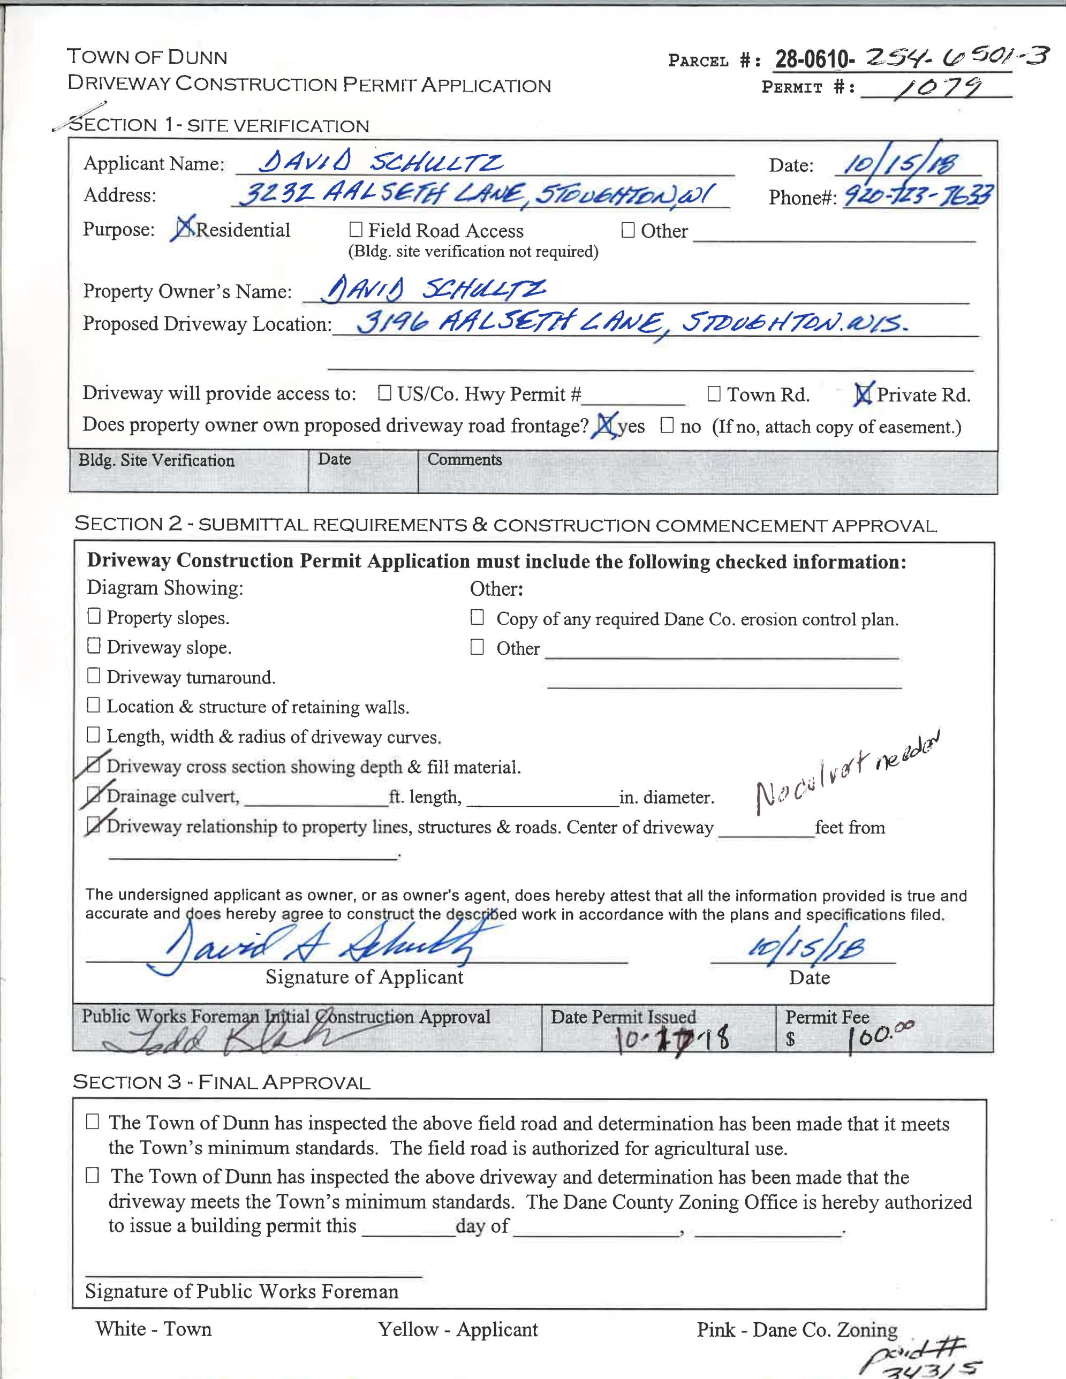
[picture p79: page 1]
