OpeningDesign/Aalseth_Residence/Research and CA/Research and Submittals/B20 Exterior Vertical Enclosures/B2050 Exterior Doors and Grilles/Garage Doors/Wayne Dalton/452/Door-Panel-SectionGuide-Aluminum-451-452.pdf

# Panel/Section Selection Guide

# Aluminum Full View Models 451 & 452

Door Width | Number of Panels | Door Height | Number of Sections
Up to 9'2" Wide | 2 | Up to 8’1" | 4
9'3" to 12'2" | 3 | 8'2" to 10'1" | 5
12'3" to 14'2" | 4 | 10'2" to 12'1" | 6
14'2" to 16'1"* | 4 | 14'2" to 16'1" | 8
16'2" & Up | Call
| Factory** | 16'2" & Up | Call Factory**

*Model 451 Only
**For assistance from the plant, please call (800) 827-3667
