OpeningDesign/Aalseth_Residence/Transfer/20190321 - to lumber yard - latest plans with door and window schedule/Sheet A600 - 3196 Aalseth Lane - Schedules.pdf

C

C

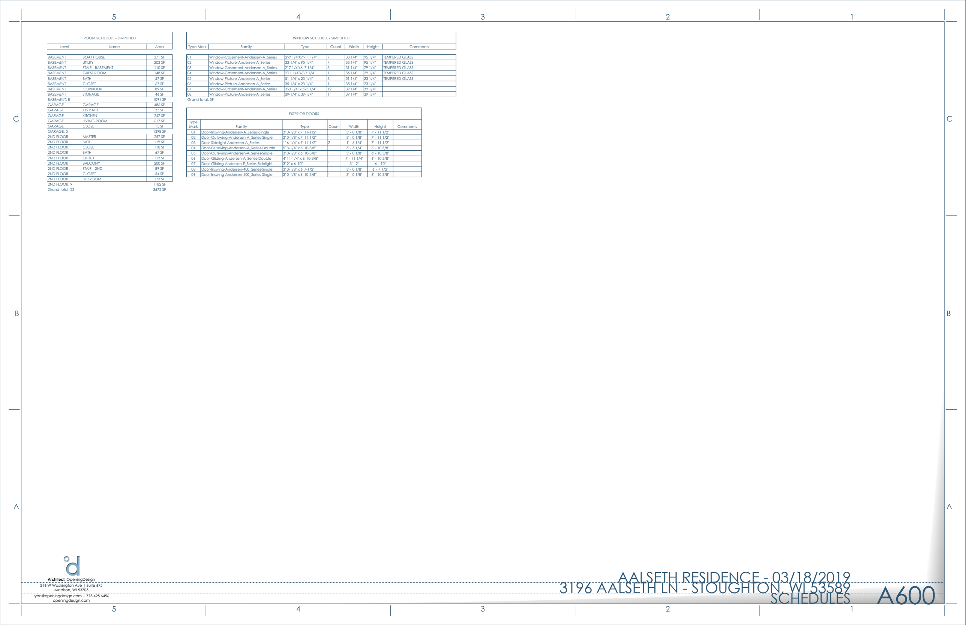
[picture p80: page 1]

5 | 4 | 3 | 2 | 1

A

B

A

B

5 | 4 | 3 | 2 | 1
316 W Washington Ave | Suite 675
Madison, WI 53703
ryan@openingdesign.com | 773.425.6456
openingdesign.com

Architect: OpeningDesign
A600

# 3196 AALSETH LN - STOUGHTON, WI 53589 SCHEDULES

# AALSETH RESIDENCE - 03/18/2019

ROOM SCHEDULE - SIMPLIFIED

Level | Name | Area
BASEMENT | BOAT HOUSE | 371 SF
BASEMENT | UTILITY | 203 SF
BASEMENT | STAIR - BASEMENT | 110 SF
BASEMENT | GUEST ROOM | 148 SF
BASEMENT | BATH | 57 SF
BASEMENT | CLOSET | 67 SF
BASEMENT | CORRIDOR | 89 SF
BASEMENT | STORAGE | 46 SF
BASEMENT: 8 | | 1091 SF
GARAGE | GARAGE | 486 SF
GARAGE | 1/2 BATH | 33 SF
GARAGE | KITCHEN | 247 SF
GARAGE | LIVING ROOM | 617 SF
GARAGE | CLOSET | 15 SF
GARAGE: 5 | | 1398 SF
2ND FLOOR | MASTER | 257 SF
2ND FLOOR | BATH | 119 SF
2ND FLOOR | CLOSET | 110 SF
2ND FLOOR | BATH | 67 SF
2ND FLOOR | OFFICE | 113 SF
2ND FLOOR | BALCONY | 200 SF
2ND FLOOR | STAIR - 2ND | 89 SF
2ND FLOOR | CLOSET | 54 SF
2ND FLOOR | BEDROOM | 173 SF
2ND FLOOR: 9 | | 1182 SF
Grand total: 22 | | 3672 SF

EXTERIOR DOORS

Type Mark | Family | Type | Count | Width | Height | Comments
01 | Door-Inswing-Andersen-A_Series-Single | 3' 0-1/8" x 7' 11-1/2" | 1 | 3' - 0 1/8" | 7' - 11 1/2"
02 | Door-Outswing-Andersen-A_Series-Single | 3' 0-1/8" x 7' 11-1/2" | 1 | 3' - 0 1/8" | 7' - 11 1/2"
03 | Door-Sidelight-Andersen-A_Series | 1' 6-1/4" x 7' 11-1/2" | 2 | 1' - 6 1/4" | 7' - 11 1/2"
04 | Door-Outswing-Andersen-A_Series-Double | 5' 3-1/4" x 6' 10-3/8" | 1 | 5' - 3 1/4" | 6' - 10 3/8"
05 | Door-Outswing-Andersen-A_Series-Single | 3' 0-1/8" x 6' 10-3/8" | 1 | 3' - 0 1/8" | 6' - 10 3/8"
06 | Door-Gliding-Andersen-A_Series-Double | 4' 11-1/4" x 6' 10-3/8" | 1 | 4' - 11 1/4" | 6' - 10 3/8"
07 | Door-Gliding-Andersen-E_Series-Sidelight | 3' 2" x 6' 10" | 1 | 3' - 2" | 6' - 10"
08 | Door-Inswing-Andersen-400_Series-Single | 3' 0-1/8" x 6' 7-1/2" | 1 | 3' - 0 1/8" | 6' - 7 1/2"
09 | Door-Inswing-Andersen-400_Series-Single | 3' 0-1/8" x 6' 10-3/8" | 1 | 3' - 0 1/8" | 6' - 10 3/8"

WINDOW SCHEDULE - SIMPLIFIED

Type Mark | Family | Type | Count | Width | Height | Comments
01 | Window-Casement-Andersen-A_Series | 2'-9 1/4"X7'-11 1/4" | 7 | 33 1/4" | 95 1/4" | TEMPERED GLASS
02 | Window-Picture-Andersen-A_Series | 33-1/4" x 95-1/4" | 4 | 33 1/4" | 95 1/4" | TEMPERED GLASS
03 | Window-Casement-Andersen-A_Series | 2'-7 1/4"x6'-7 1/4" | 3 | 31 1/4" | 79 1/4" | TEMPERED GLASS
04 | Window-Casement-Andersen-A_Series | 2'11 1/4"x6'-7 1/4" | 1 | 35 1/4" | 79 1/4" | TEMPERED GLASS
05 | Window-Picture-Andersen-A_Series | 51-1/4" x 23-1/4" | 3 | 51 1/4" | 23 1/4" | TEMPERED GLASS
06 | Window-Picture-Andersen-A_Series | 35-1/4" x 23-1/4" | 1 | 35 1/4" | 23 1/4"
07 | Window-Casement-Andersen-A_Series | 3'-3 1/4" x 3'-3 1/4" | 19 | 39 1/4" | 39 1/4"
08 | Window-Picture-Andersen-A_Series | 39-1/4" x 39-1/4" | 1 | 39 1/4" | 39 1/4"
Grand total: 39
