OpeningDesign/Aalseth_Residence/Transfer/20190321 - to lumber yard - latest plans with door and window schedule/20190318 - 3196 Aalseth Lane Page 006.jpg

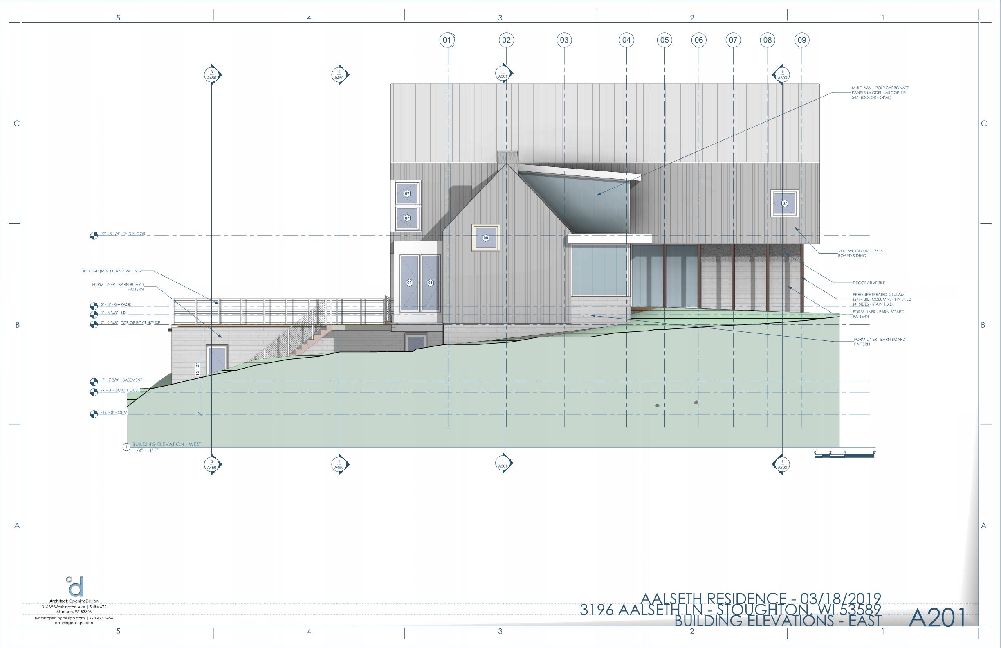
Transfer/20190321 - to lumber yard - latest plans with door and window schedule/20190318 - 3196 Aalseth Lane Page 006.jpg
