OpeningDesign/Aalseth_Residence/Transfer/20181212 - to excavator - small changes/2018-12-12_11-40-07_RevitAutodesk_Revit_2019_-_[3196_Aalseth_Lane.rvt_-_SheRevit.png

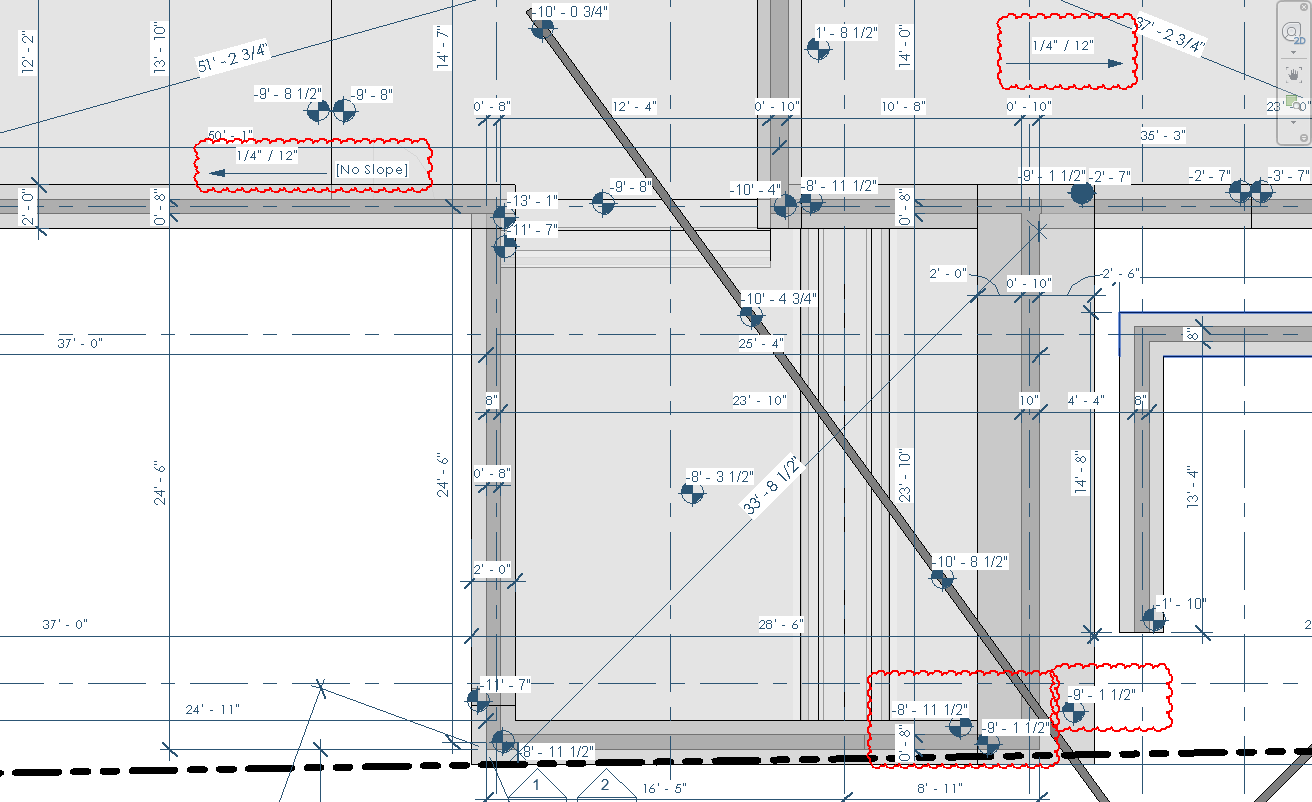
Transfer/20181212 - to excavator - small changes/2018-12-12_11-40-07_RevitAutodesk_Revit_2019_-_[3196_Aalseth_Lane.rvt_-_SheRevit.png
