OpeningDesign/Aalseth_Residence/Transfer/20190719 - from Lumber Yard - Truss Shop Drawings/20190719 - Aalseth - Truss.pdf

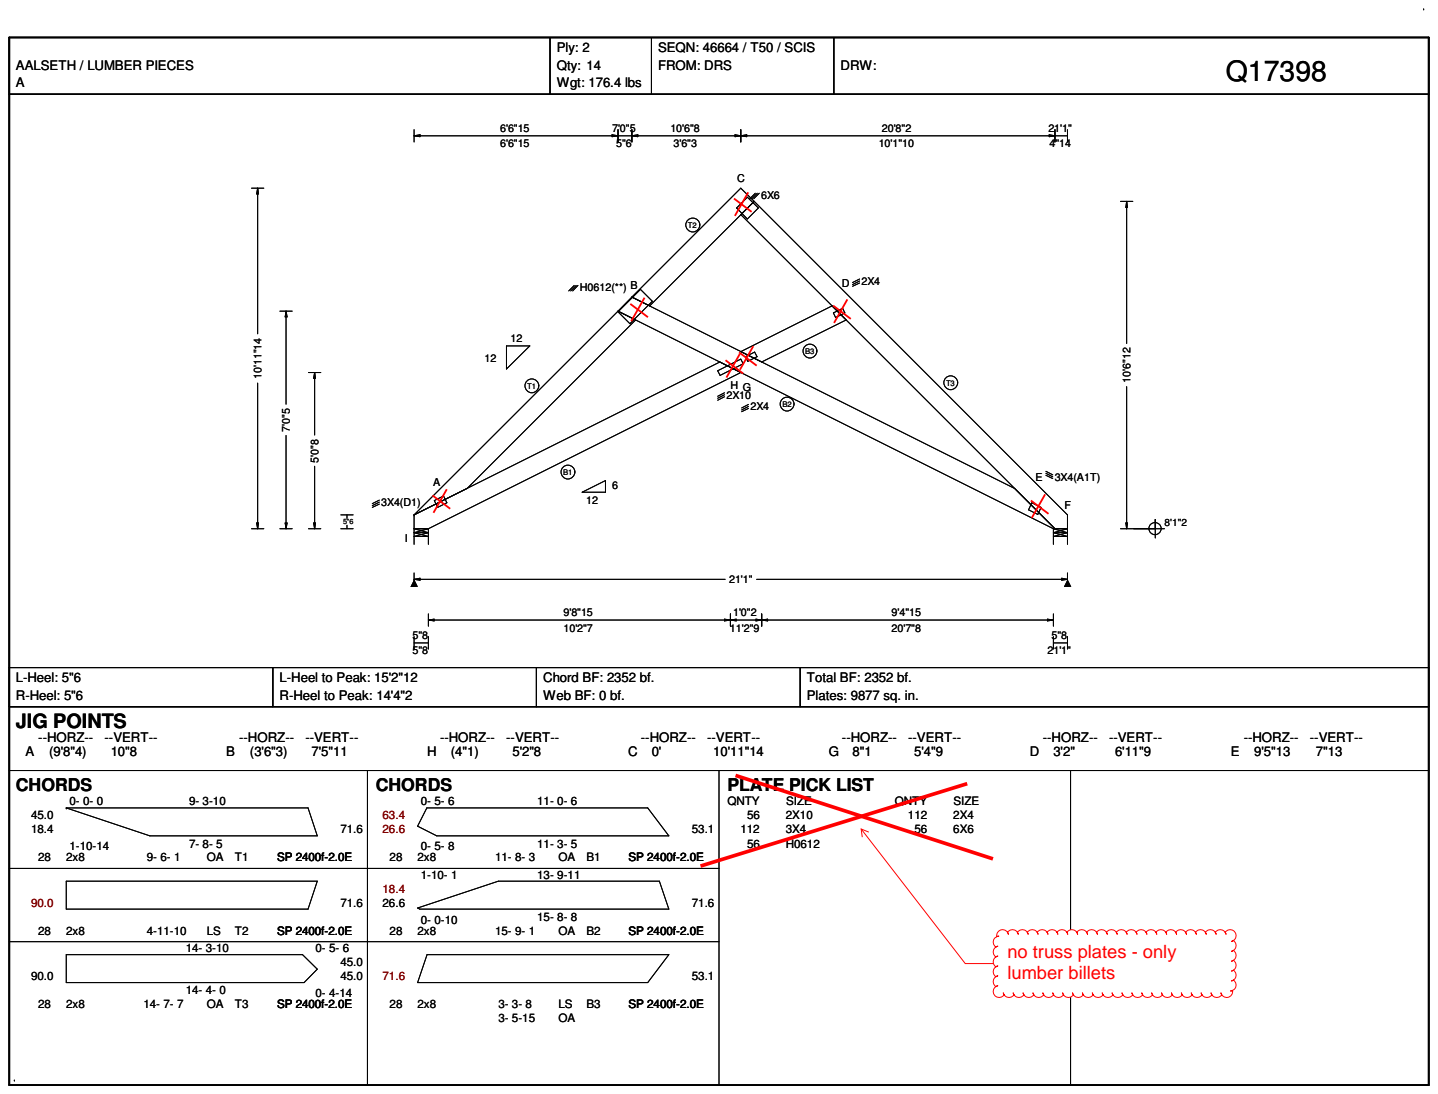
[picture p108: page 1]
L-Heel: 5"6 R-Heel: 5"6; Ply: 2 Qty: 14 Wgt: 176.4 lbs; SEQN: 46664 / T50 / SCIS; FROM: DRS; DRW:; JIG POINTS; --HORZ-- --VERT--; CHORDS; QNTY; SIZE

Q17398 AALSETH / LUMBER PIECES A

L-Heel to Peak: 15'2"12
R-Heel to Peak: 14'4"2

Chord BF: 2352 bf.
Web BF: 0 bf.

Total BF: 2352 bf.
Plates: 9877 sq. in.

PLATE PICK LIST

A

20'8"2

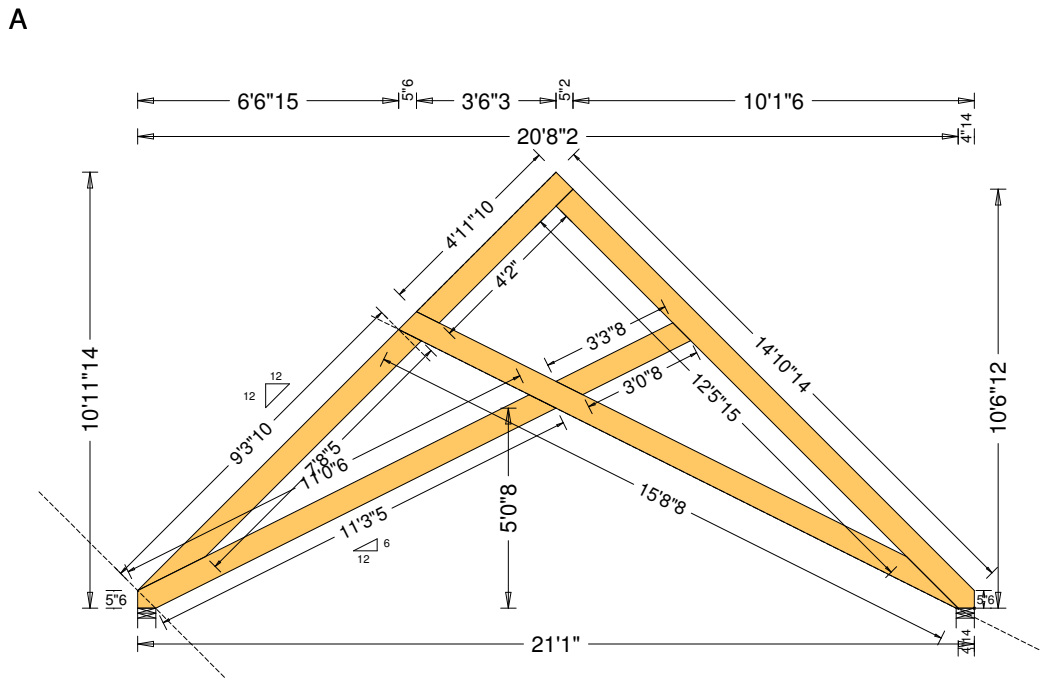
[picture p109: page 2]

A

6X6

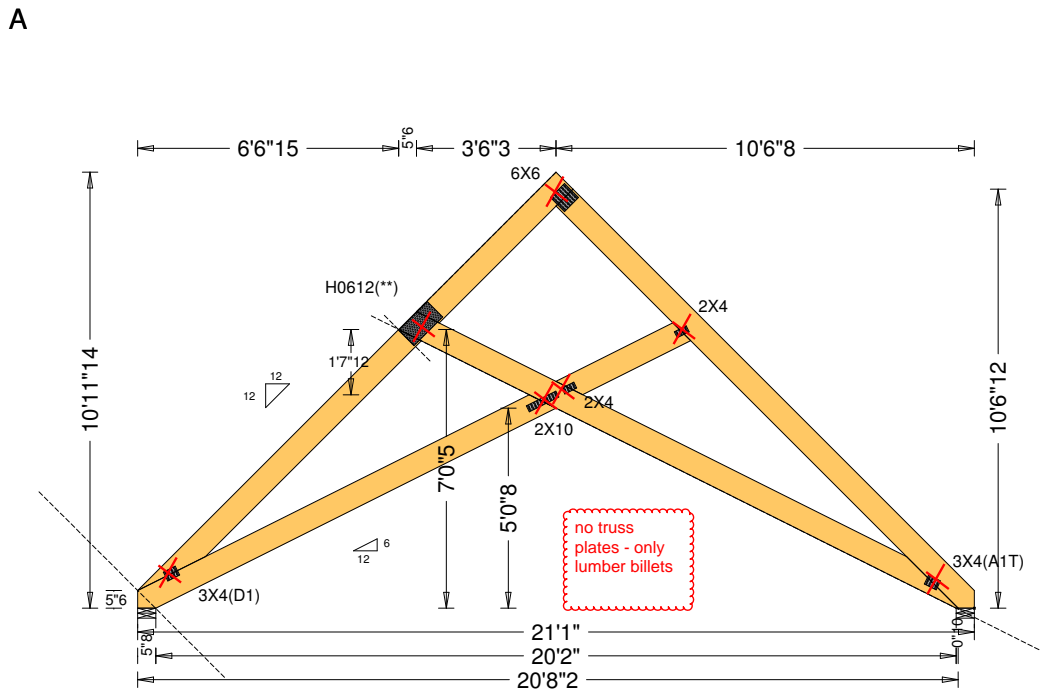
[picture p110: page 3]
