OpeningDesign/Aalseth_Residence/Transfer/20190731 - to Glazer - Polycarbonate/20190731 - 3196 Aalseth.pdf

B | C
C | B

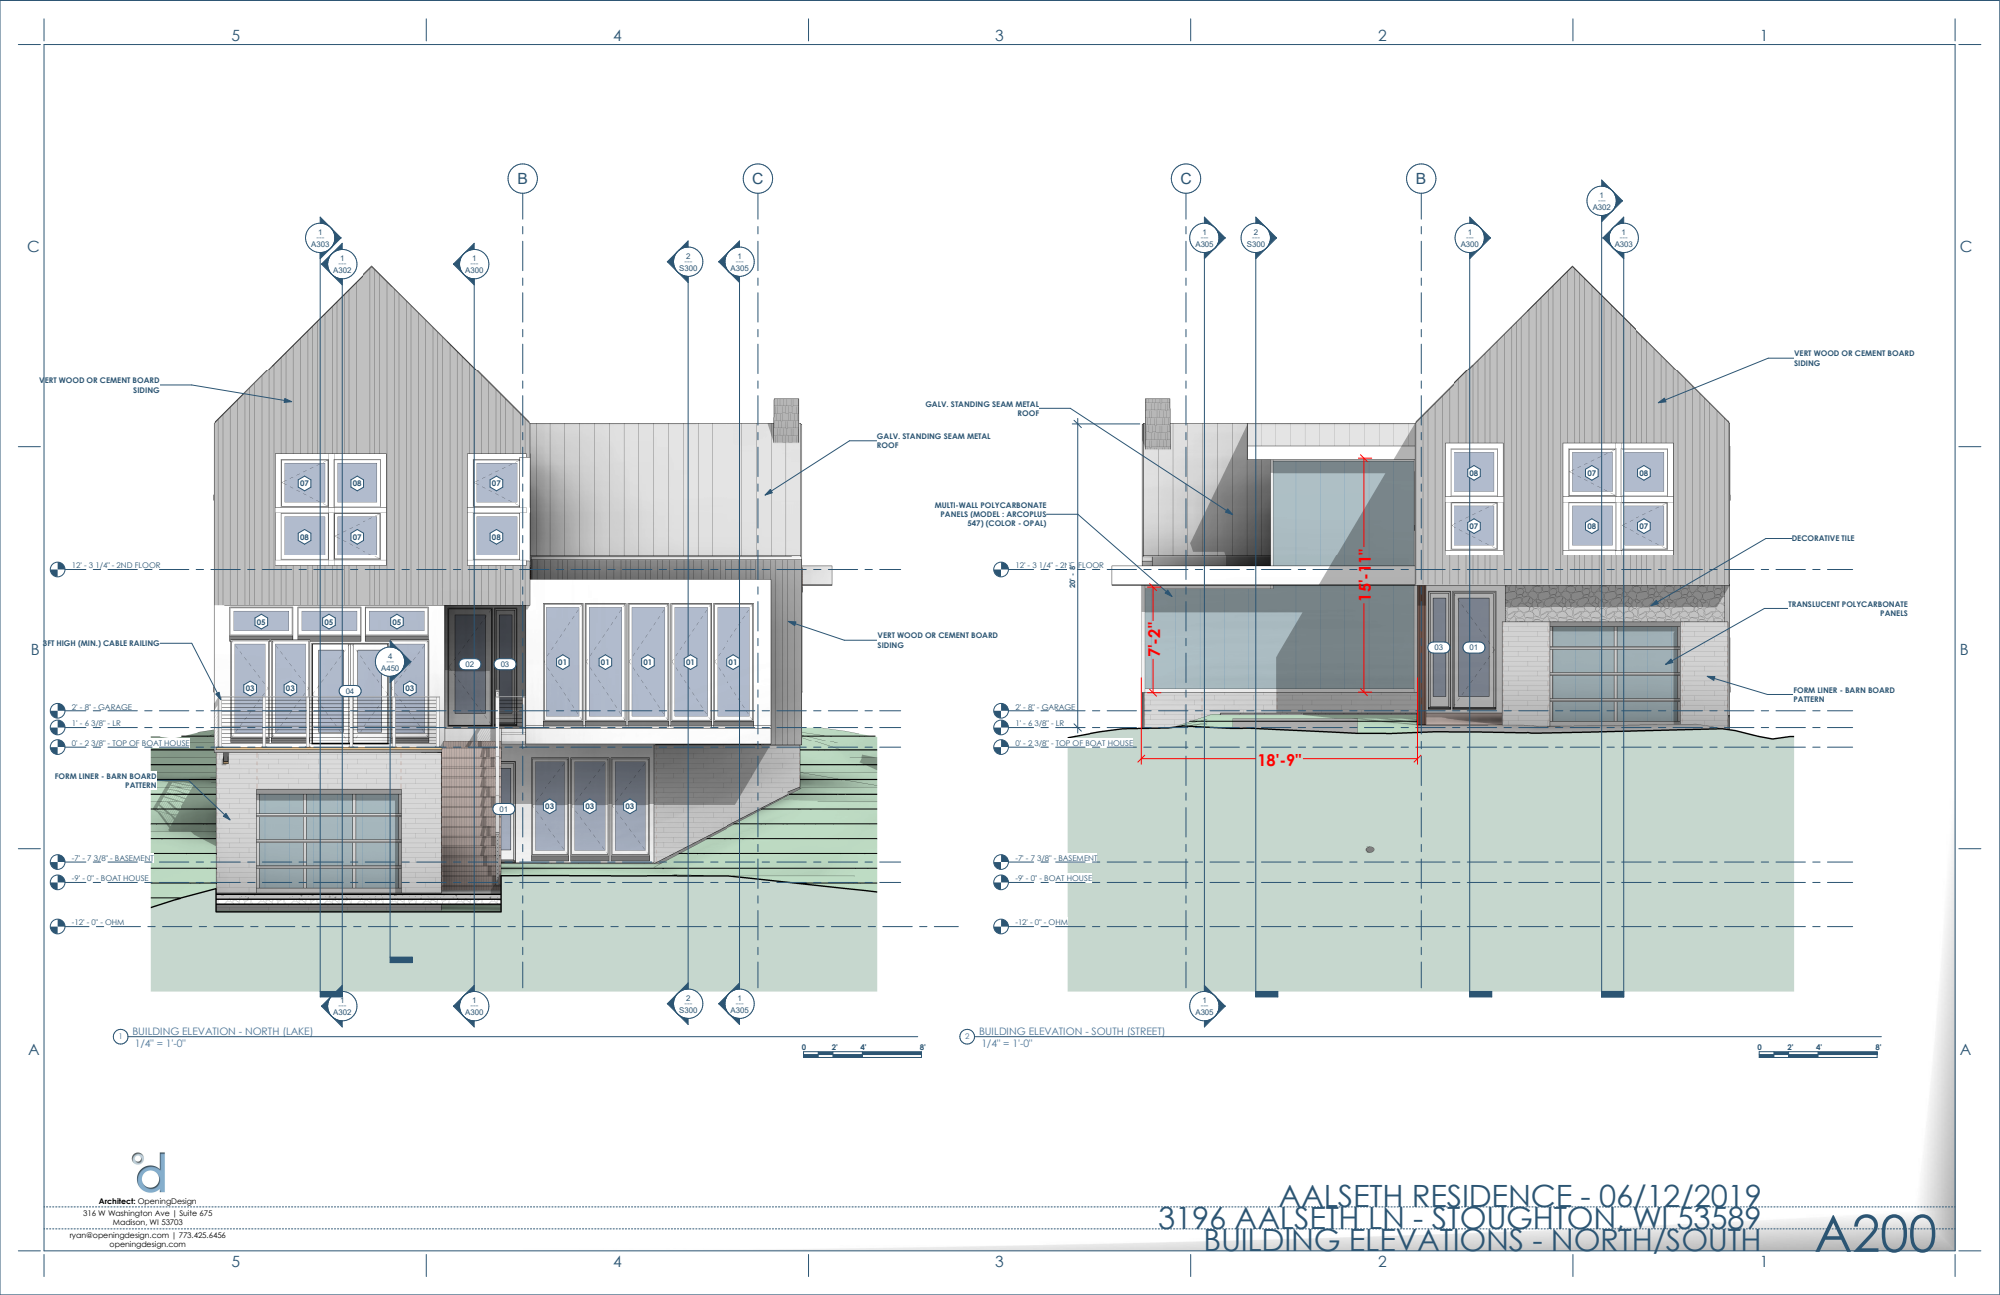
[picture p111: page 1]
2' - 8" - GARAGE; 12' - 3 1/4" - 2ND FLOOR; -9' - 0" - BOAT HOUSE; -7' - 7 3/8" - BASEMENT; -12' - 0" - OHM; PATTERN; SIDING; DECORATIVE TILE; TRANSLUCENT POLYCARBONATE PANELS; 547) (COLOR - OPAL); ROOF; Madison, WI 53703; openingdesign.com; BUILDING ELEVATION - SOUTH (STREET)

VERT WOOD OR CEMENT BOARD
SIDING

GALV. STANDING SEAM METAL

ROOF

MULTI-WALL POLYCARBONATE
PANELS (MODEL : ARCOPLUS

3FT HIGH (MIN.) CABLE RAILING

FORM LINER - BARN BOARD
PATTERN

0' - 2 3/8" - TOP OF BOAT HOUSE

BUILDING ELEVATION - NORTH (LAKE)

AALSETH RESIDENCE - 06/12/2019
BUILDING ELEVATIONS - NORTH/SOUTH

Architect: OpeningDesign
316 W Washington Ave | Suite 675

3196 AALSETH LN - STOUGHTON, WI 53589

ryan@openingdesign.com | 773.425.6456

02 | 03

01.1

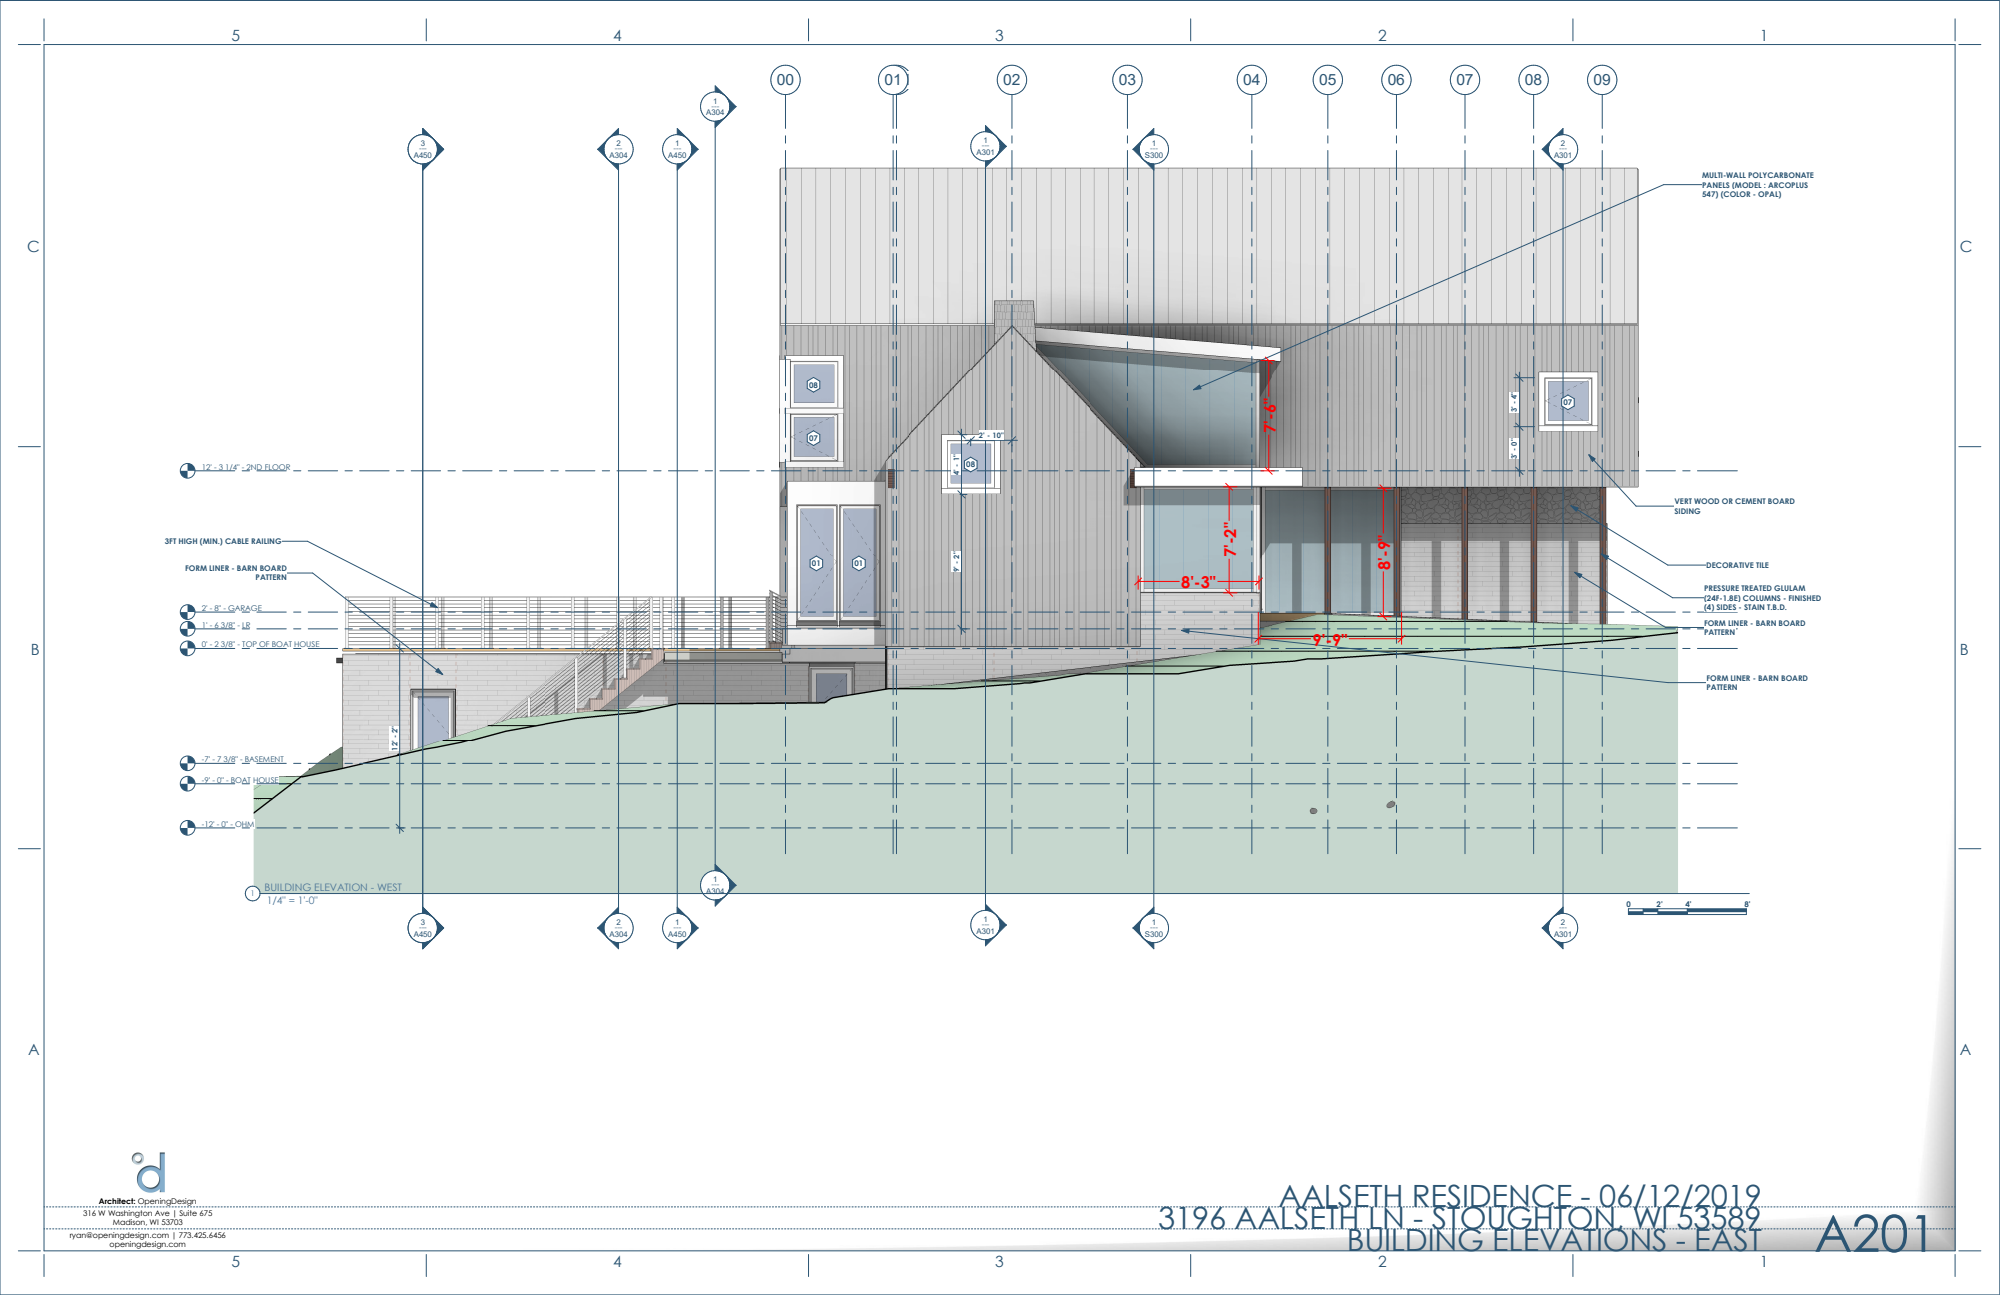
[picture p112: page 2]
2' - 8" - GARAGE; 12' - 3 1/4" - 2ND FLOOR; -9' - 0" - BOAT HOUSE; -7' - 7 3/8" - BASEMENT; -12' - 0" - OHM; DECORATIVE TILE; PATTERN; Madison, WI 53703; openingdesign.com

MULTI-WALL POLYCARBONATE
PANELS (MODEL : ARCOPLUS
547) (COLOR - OPAL)

VERT WOOD OR CEMENT BOARD
SIDING

3FT HIGH (MIN.) CABLE RAILING

FORM LINER - BARN BOARD

PRESSURE TREATED GLULAM
(24F-1.8E) COLUMNS - FINISHED
(4) SIDES - STAIN T.B.D.

PATTERN

0' - 2 3/8" - TOP OF BOAT HOUSE

BUILDING ELEVATION - WEST

AALSETH RESIDENCE - 06/12/2019
BUILDING ELEVATIONS - EAST

Architect: OpeningDesign
316 W Washington Ave | Suite 675

3196 AALSETH LN - STOUGHTON, WI 53589

ryan@openingdesign.com | 773.425.6456
