OpeningDesign/Aalseth_Residence/Transfer/20190715 - to Framer - Latest Set/20190612 - 3196 Aalseth - 11x17.pdf

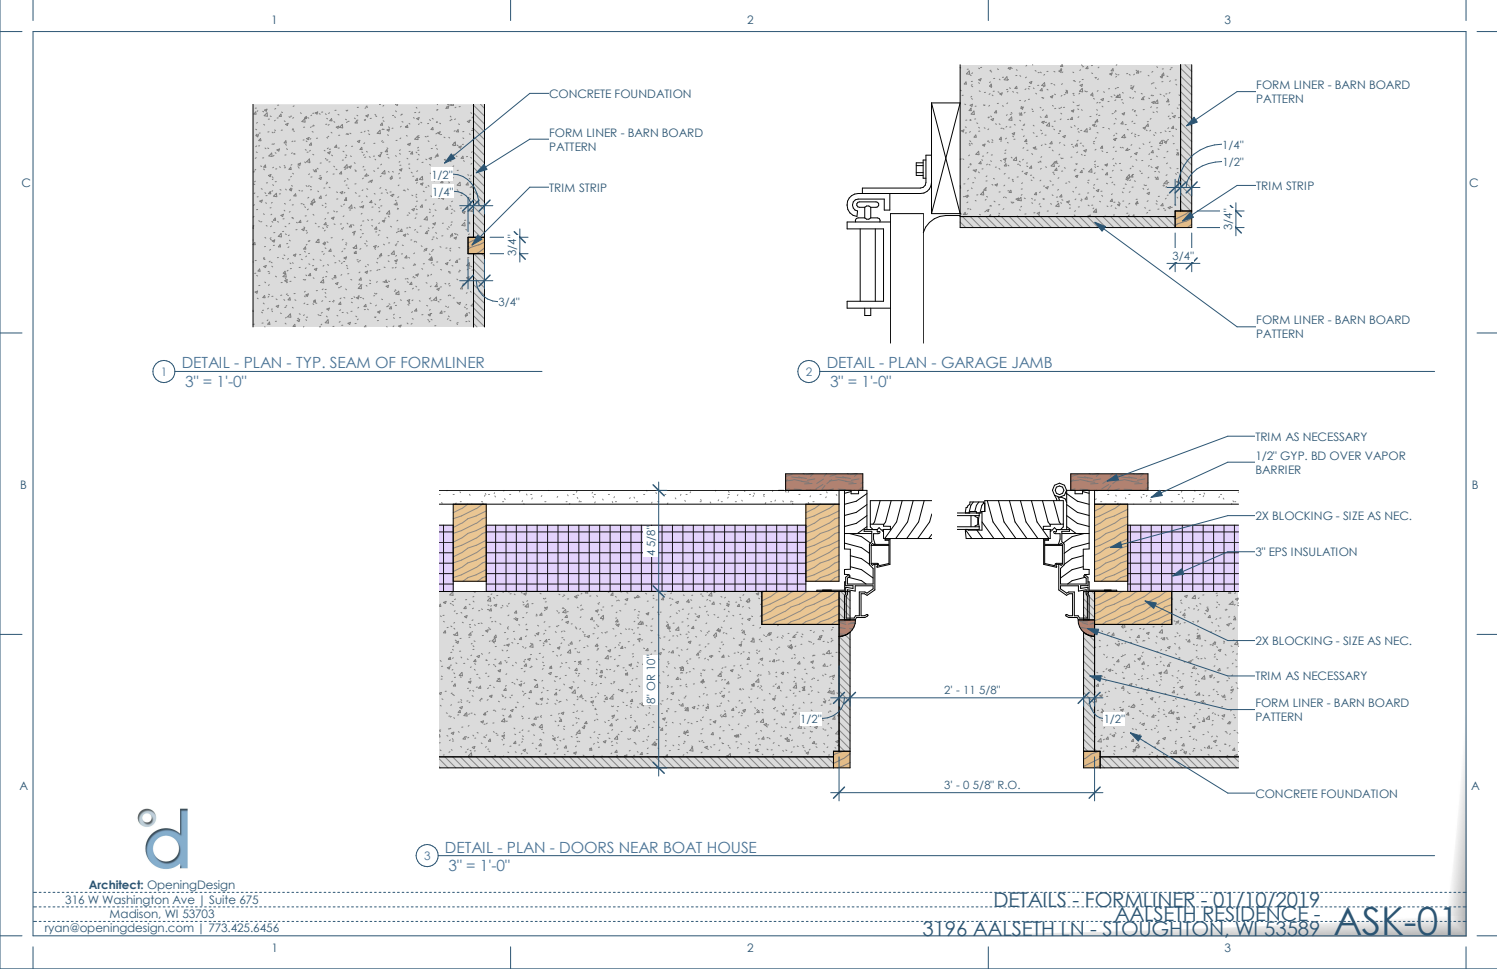
[picture p113: page 1]
TRIM STRIP; CONCRETE FOUNDATION; 3" EPS INSULATION; Madison, WI 53703; ryan@openingdesign.com | 773.425.6456; 3196 AALSETH LN - STOUGHTON, WI 53589 AALSETH RESIDENCE - DETAILS - FORMLINER - 01/10/2019 ASK-01

FORM LINER - BARN BOARD
PATTERN

DETAIL - PLAN - TYP. SEAM OF FORMLINER

DETAIL - PLAN - GARAGE JAMB

TRIM AS NECESSARY
1/2" GYP. BD OVER VAPOR
BARRIER

2X BLOCKING - SIZE AS NEC.

DETAIL - PLAN - DOORS NEAR BOAT HOUSE

Architect: OpeningDesign
316 W Washington Ave | Suite 675

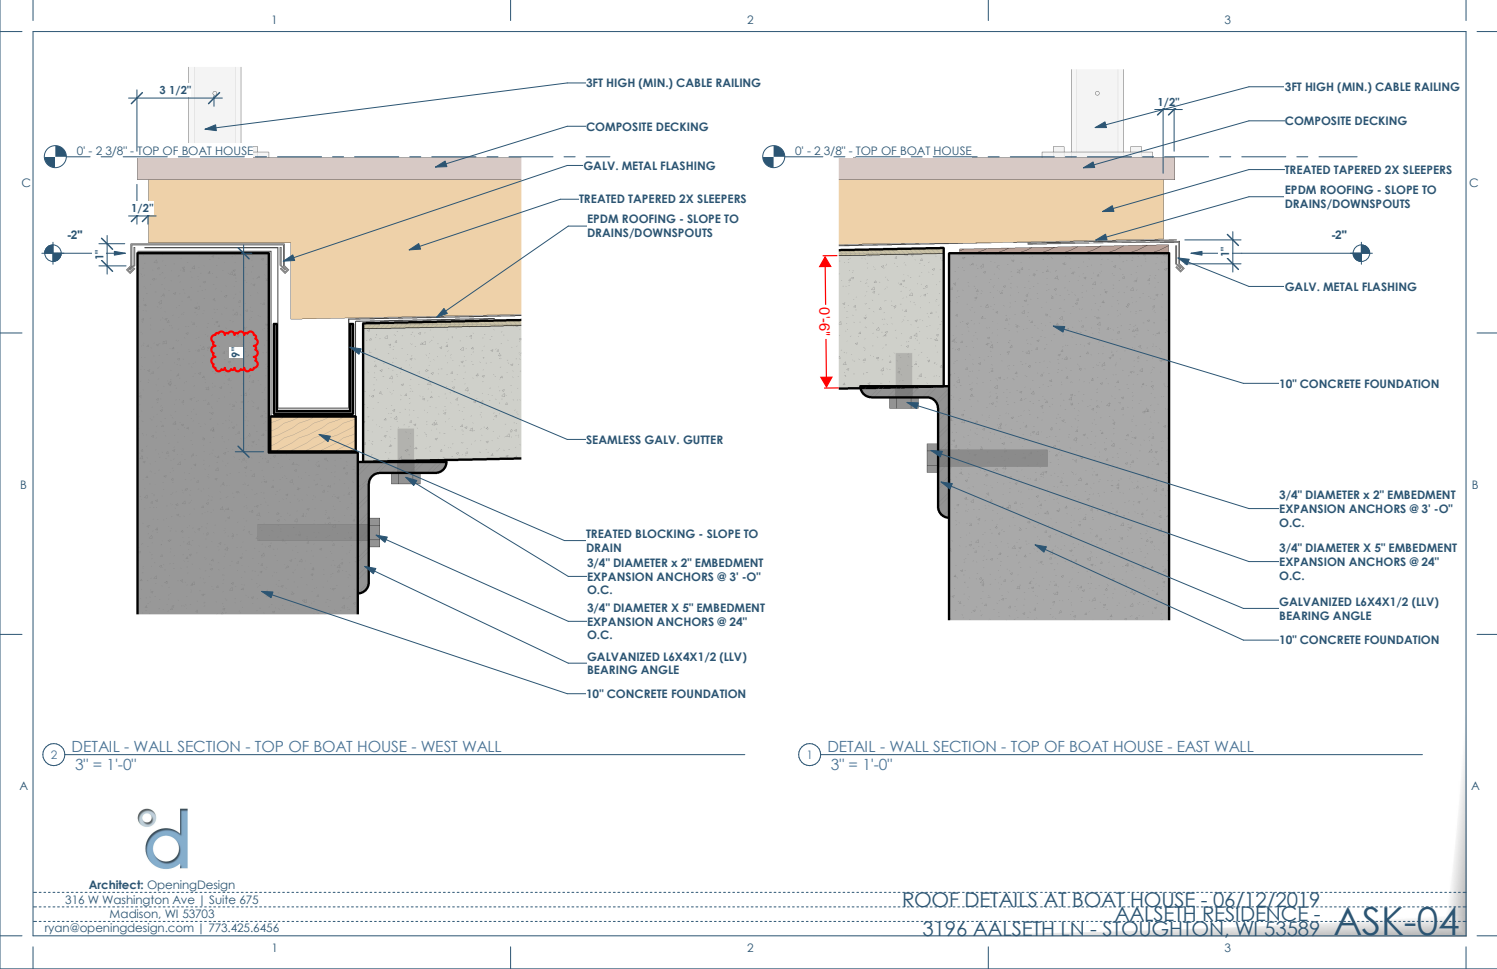
[picture p114: page 2]
COMPOSITE DECKING; 10" CONCRETE FOUNDATION; GALVANIZED L6X4X1/2 (LLV) BEARING ANGLE; 3/4" DIAMETER X 5" EMBEDMENT EXPANSION ANCHORS @ 24" O.C.; 3/4" DIAMETER x 2" EMBEDMENT EXPANSION ANCHORS @ 3' -O" O.C.; Architect: OpeningDesign; ryan@openingdesign.com | 773.425.6456; 3196 AALSETH LN - STOUGHTON, WI 53589 AALSETH RESIDENCE - ROOF DETAILS AT BOAT HOUSE - 06/12/2019 ASK-04

3FT HIGH (MIN.) CABLE RAILING

0' - 2 3/8" - TOP OF BOAT HOUSE9"

0' - 2 3/8" - TOP OF BOAT HOUSE

GALV. METAL FLASHING

TREATED TAPERED 2X SLEEPERS
EPDM ROOFING - SLOPE TO
DRAINS/DOWNSPOUTS

SEAMLESS GALV. GUTTER

TREATED BLOCKING - SLOPE TO
DRAIN
3/4" DIAMETER x 2" EMBEDMENT
EXPANSION ANCHORS @ 3' -O"
3/4" DIAMETER X 5" EMBEDMENT
EXPANSION ANCHORS @ 24"

DETAIL - WALL SECTION - TOP OF BOAT HOUSE - WEST WALL

DETAIL - WALL SECTION - TOP OF BOAT HOUSE - EAST WALL

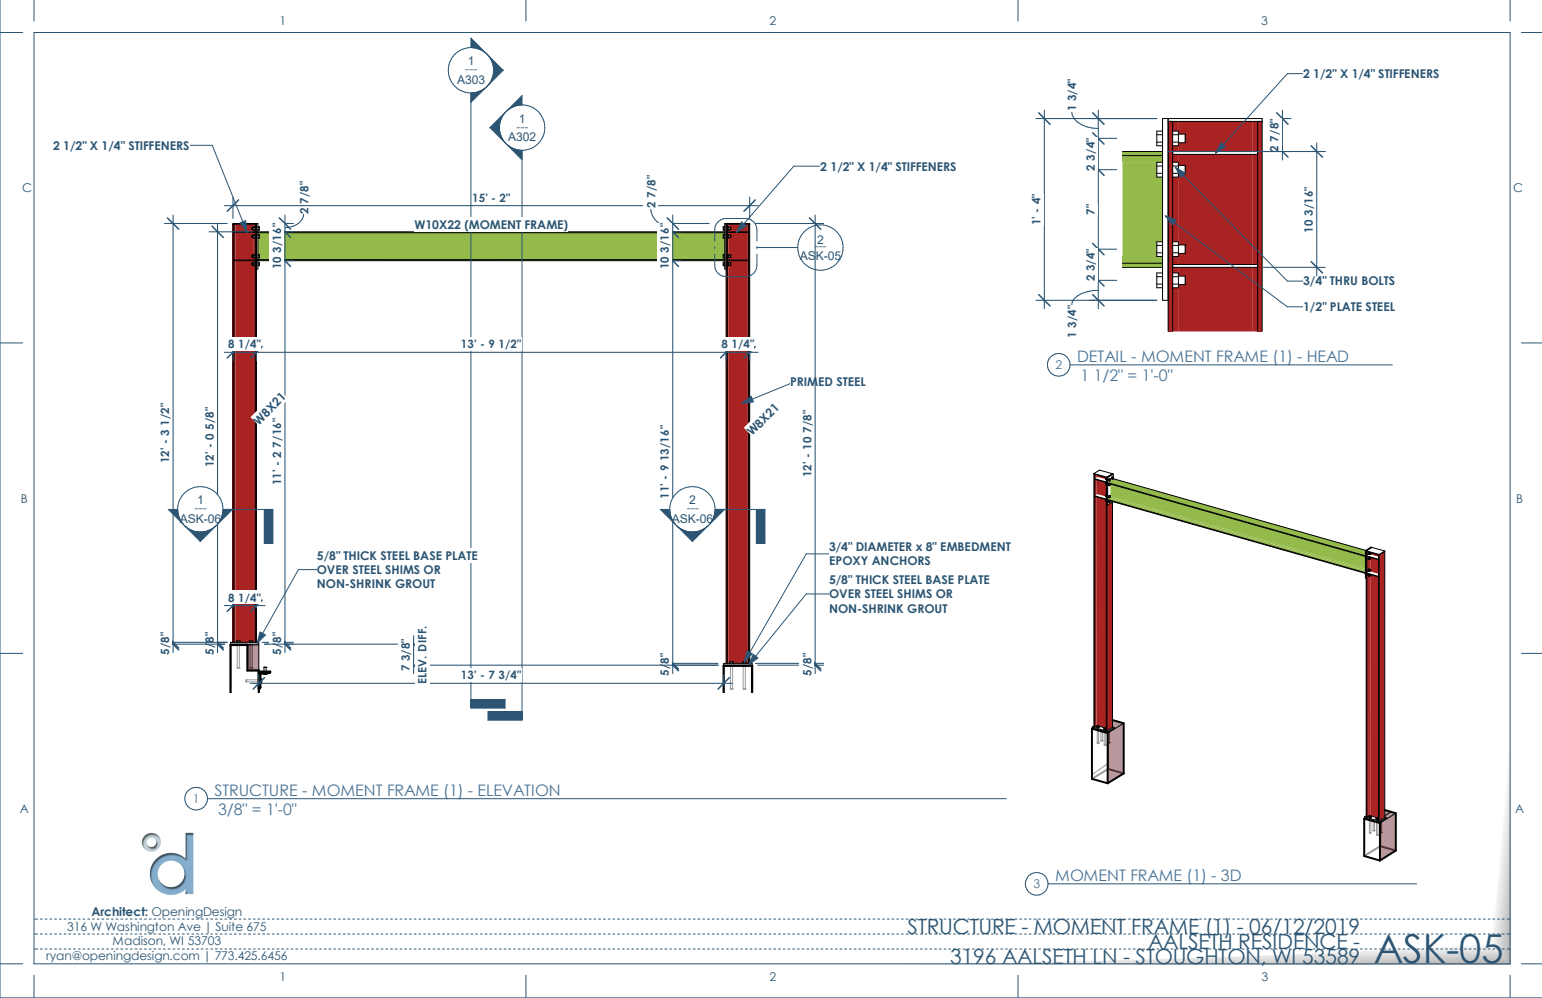
[picture p115: page 3]
PRIMED STEEL; --- ASK-05; W10X22 (MOMENT FRAME); 2 1/2" X 1/4" STIFFENERS; ELEV. DIFF.; ASK-06; 3/4" THRU BOLTS; 1/2" PLATE STEEL; Architect: OpeningDesign; ryan@openingdesign.com | 773.425.6456; 3196 AALSETH LN - STOUGHTON, WI 53589 AALSETH RESIDENCE - STRUCTURE - MOMENT FRAME (1) - 06/12/2019 ASK-05; MOMENT FRAME (1) - 3D

DETAIL - MOMENT FRAME (1) - HEAD

3/4" DIAMETER x 8" EMBEDMENT
EPOXY ANCHORS
5/8" THICK STEEL BASE PLATE
OVER STEEL SHIMS OR
NON-SHRINK GROUT

STRUCTURE - MOMENT FRAME (1) - ELEVATION

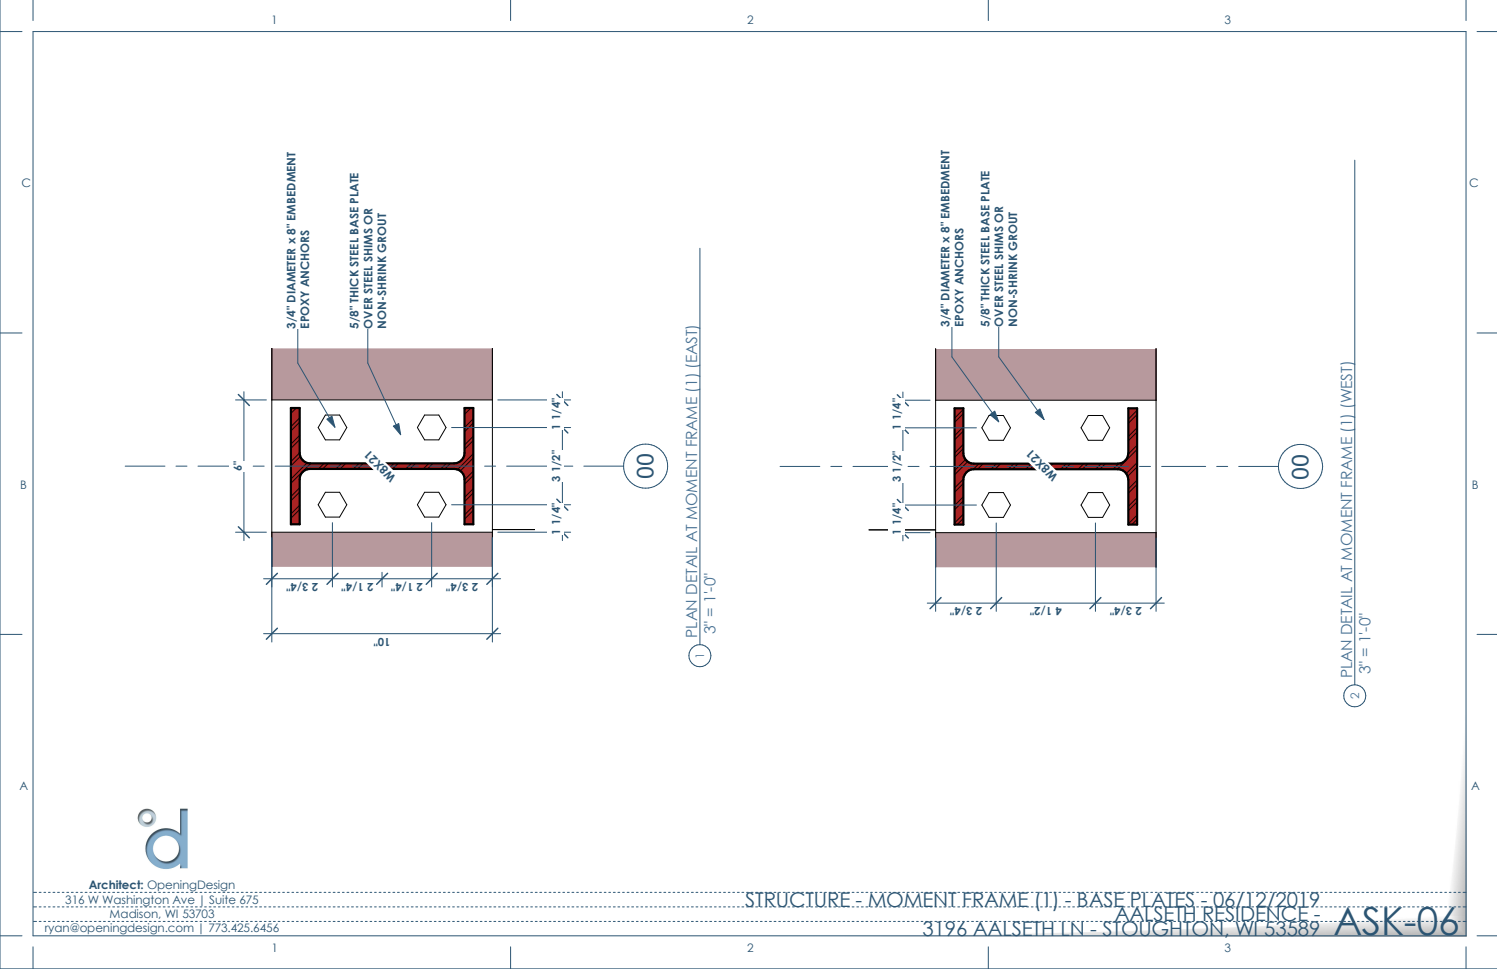
[picture p116: page 4]
3/4" DIAMETER x 8" EMBEDMENT; EPOXY ANCHORS; Architect: OpeningDesign; ryan@openingdesign.com | 773.425.6456; 3196 AALSETH LN - STOUGHTON, WI 53589 AALSETH RESIDENCE - STRUCTURE - MOMENT FRAME (1) - BASE PLATES - 06/12/2019; ASK-06

5/8" THICK STEEL BASE PLATE

OVER STEEL SHIMS OR

NON-SHRINK GROUT

1 PLAN DETAIL AT MOMENT FRAME (1) (EAST)

2 PLAN DETAIL AT MOMENT FRAME (1) (WEST)

C | B

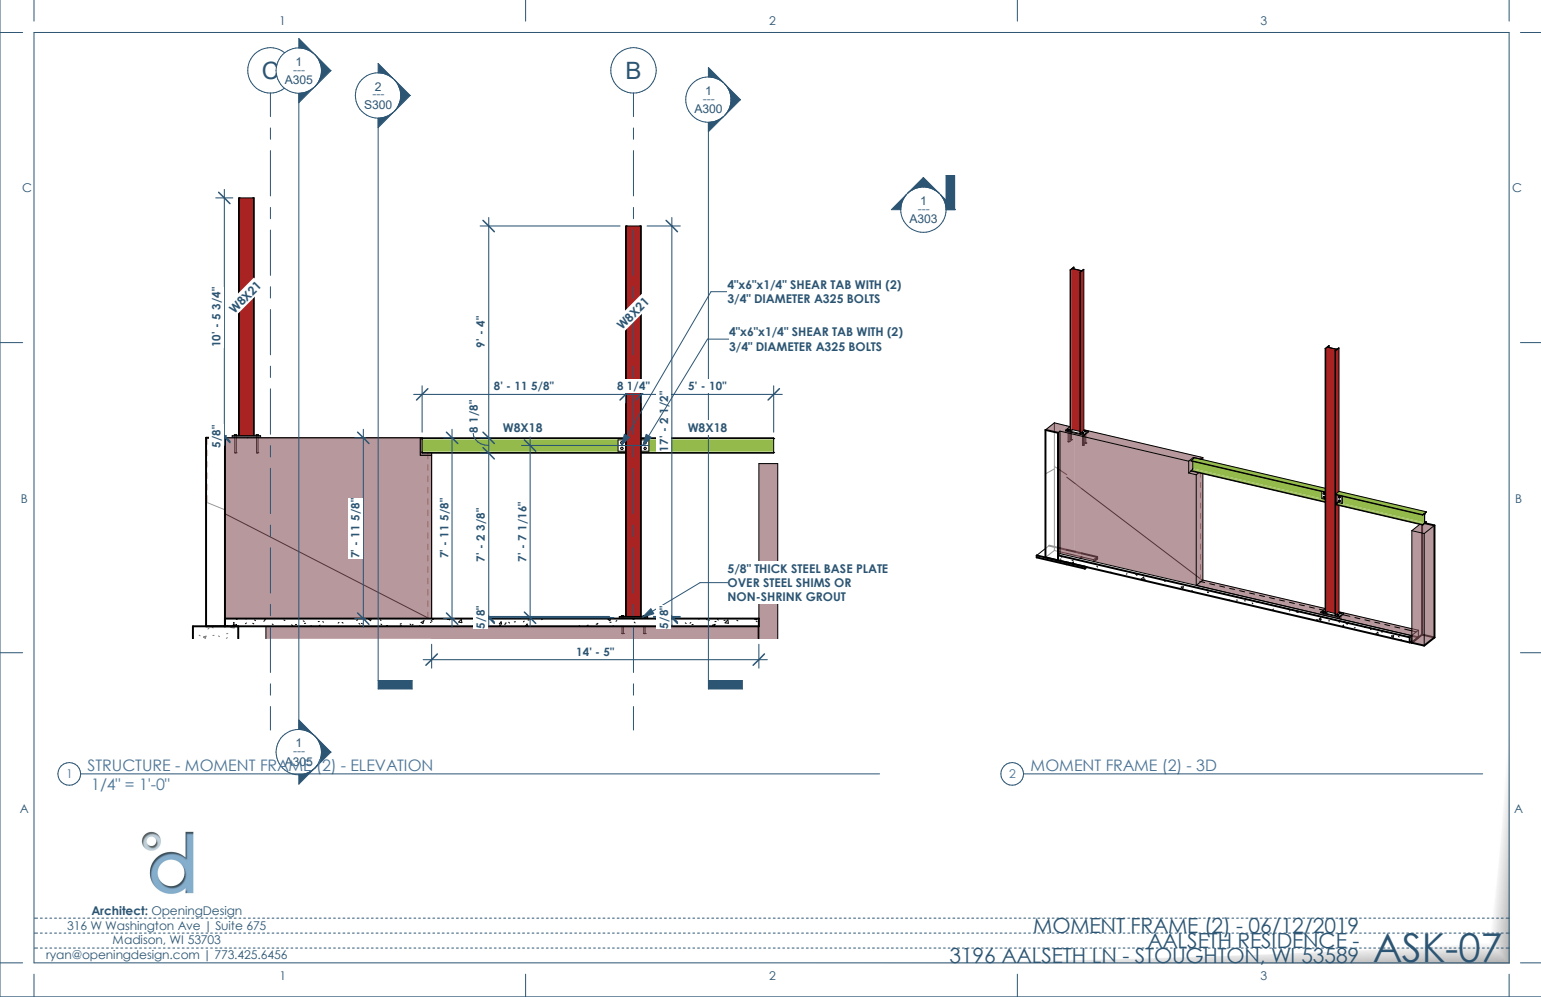
[picture p117: page 5]
Architect: OpeningDesign; ryan@openingdesign.com | 773.425.6456; 3196 AALSETH LN - STOUGHTON, WI 53589 AALSETH RESIDENCE - MOMENT FRAME (2) - 06/12/2019 ASK-07; STRUCTURE - MOMENT FRAME (2) - ELEVATION; MOMENT FRAME (2) - 3D

4"x6"x1/4" SHEAR TAB WITH (2)
3/4" DIAMETER A325 BOLTS

5/8" THICK STEEL BASE PLATE
OVER STEEL SHIMS OR
NON-SHRINK GROUT

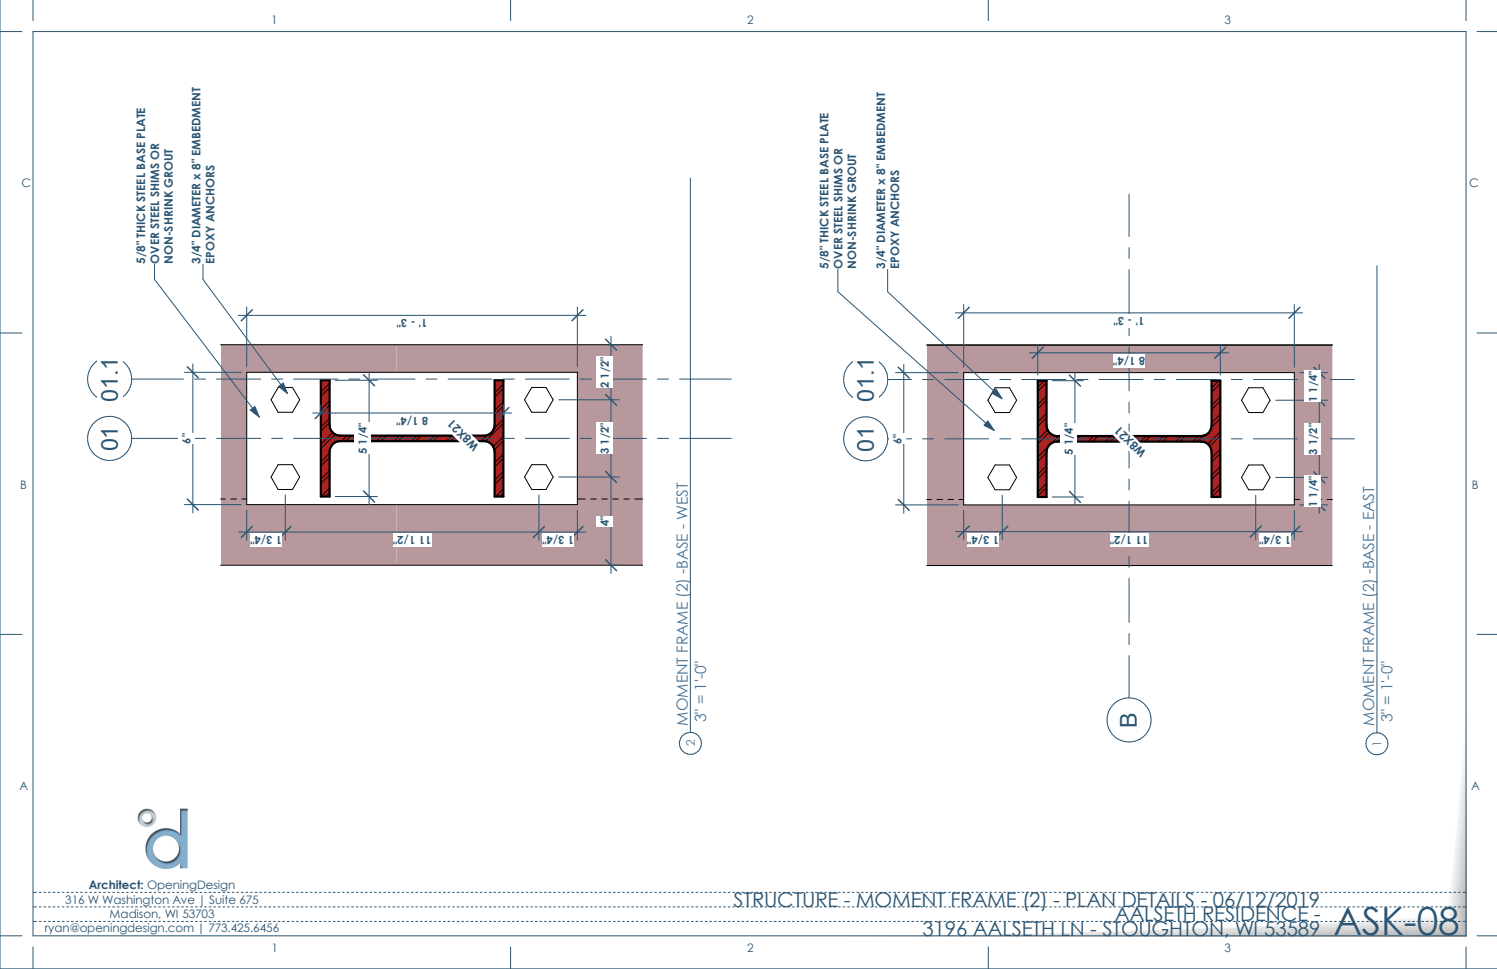
[picture p118: page 6]
NON; 3/4" DIAMETER x 8" EMBEDMENT; EPOXY ANCHORS; -SHRINK GROUT; Architect: OpeningDesign; ryan@openingdesign.com | 773.425.6456; 3196 AALSETH LN - STOUGHTON, WI 53589 AALSETH RESIDENCE - STRUCTURE - MOMENT FRAME (2) - PLAN DETAILS - 06/12/2019; ASK-08

5/8" THICK STEEL BASE PLATE

OVER STEEL SHIMS OR

2 MOMENT FRAME (2) -BASE - WEST

MOMENT FRAME (2) -BASE - EAST

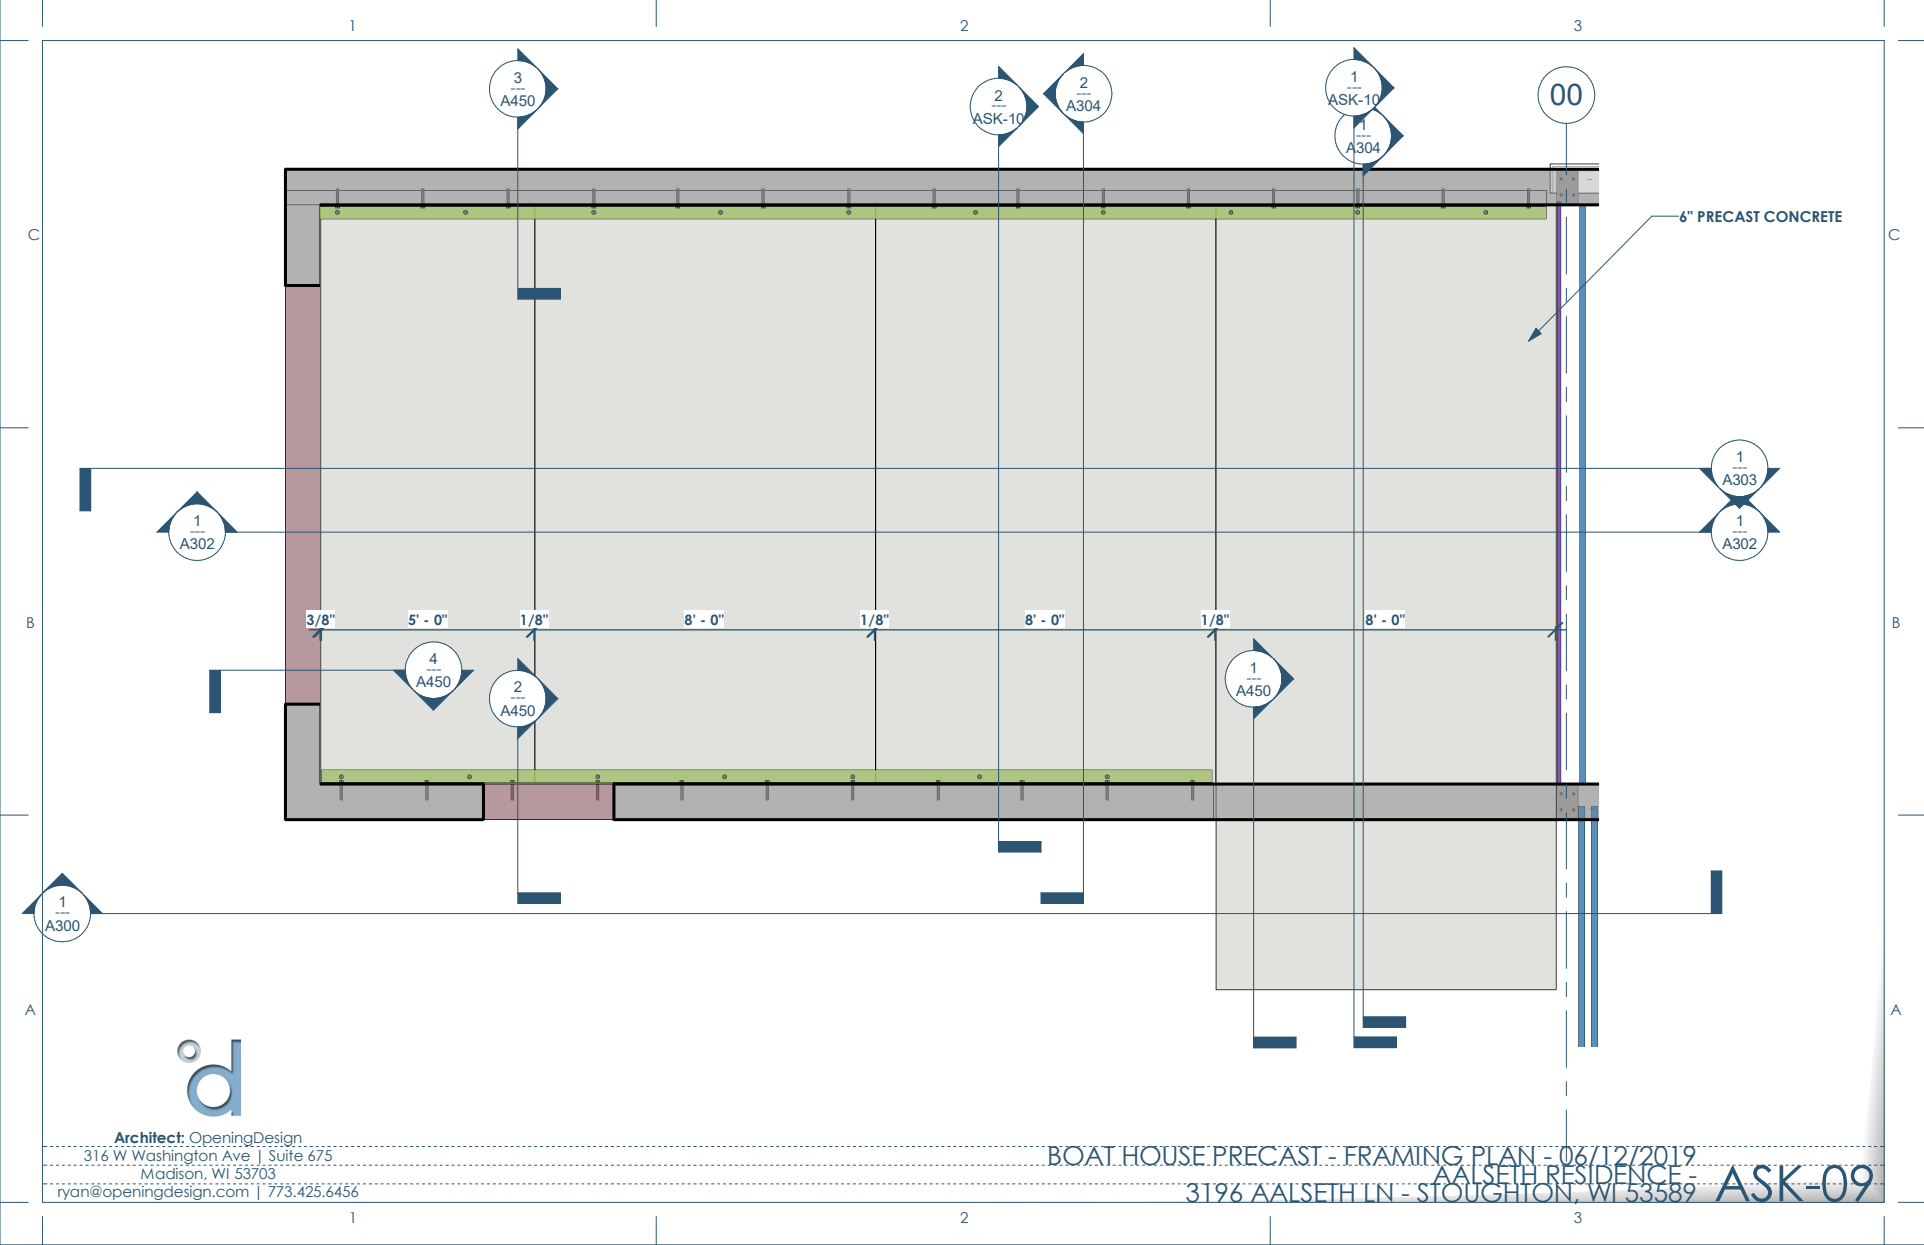
[picture p119: page 7]
ASK-10; 6" PRECAST CONCRETE; Architect: OpeningDesign; ryan@openingdesign.com | 773.425.6456; 3196 AALSETH LN - STOUGHTON, WI 53589 AALSETH RESIDENCE - BOAT HOUSE PRECAST - FRAMING PLAN - 06/12/2019 ASK-09

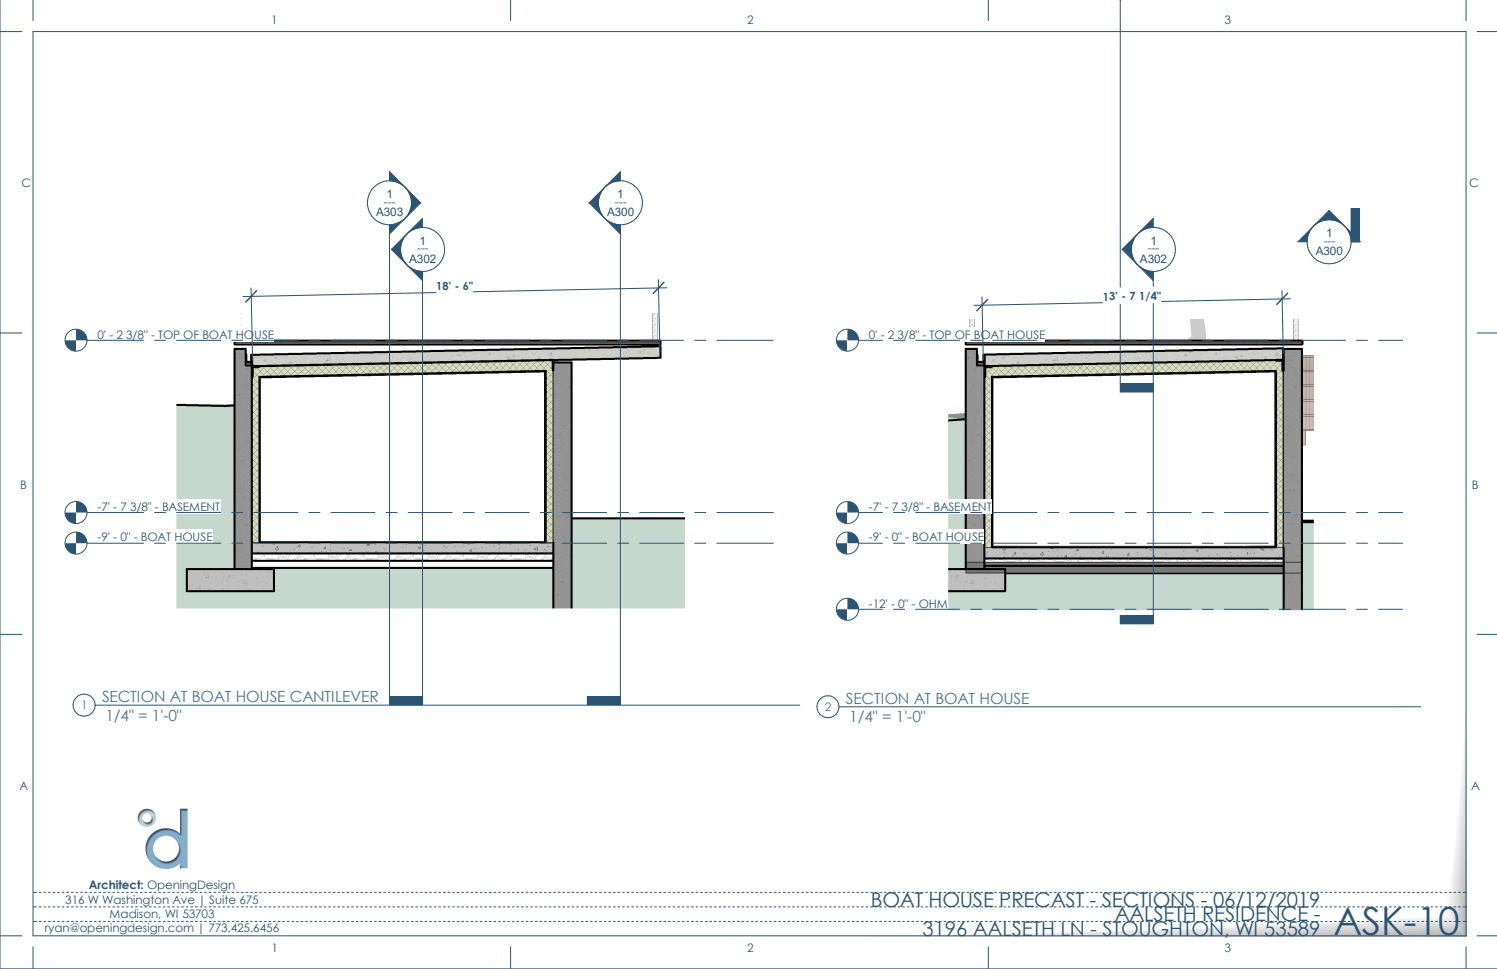
[picture p120: page 8]
-9' - 0" - BOAT HOUSE; -7' - 7 3/8" - BASEMENT; -12' - 0" - OHM; Architect: OpeningDesign; ryan@openingdesign.com | 773.425.6456; 3196 AALSETH LN - STOUGHTON, WI 53589 AALSETH RESIDENCE - BOAT HOUSE PRECAST - SECTIONS - 06/12/2019 ASK-10

0' - 2 3/8" - TOP OF BOAT HOUSE

SECTION AT BOAT HOUSE CANTILEVER

SECTION AT BOAT HOUSE

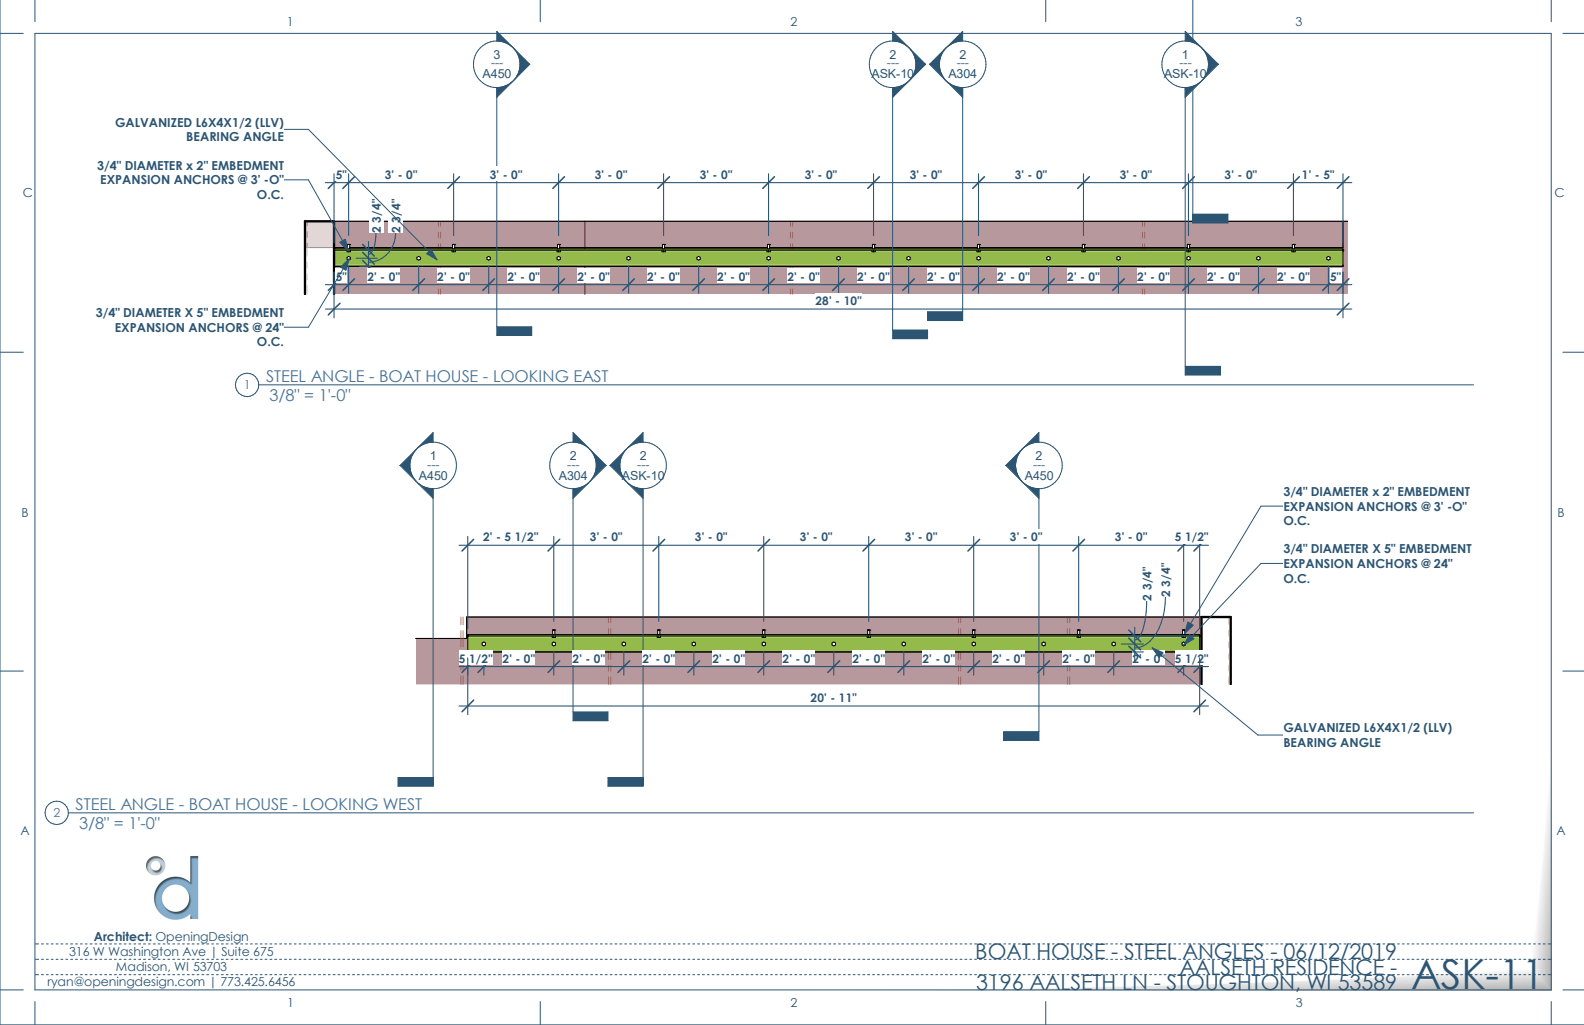
[picture p121: page 9]
ASK-10; 3/4" DIAMETER X 5" EMBEDMENT EXPANSION ANCHORS @ 24" O.C.; 3/4" DIAMETER x 2" EMBEDMENT EXPANSION ANCHORS @ 3' -O" O.C.; GALVANIZED L6X4X1/2 (LLV) BEARING ANGLE; Architect: OpeningDesign; ryan@openingdesign.com | 773.425.6456; 3196 AALSETH LN - STOUGHTON, WI 53589 AALSETH RESIDENCE - BOAT HOUSE - STEEL ANGLES - 06/12/2019 ASK-11

STEEL ANGLE - BOAT HOUSE - LOOKING EAST

STEEL ANGLE - BOAT HOUSE - LOOKING WEST

01.1

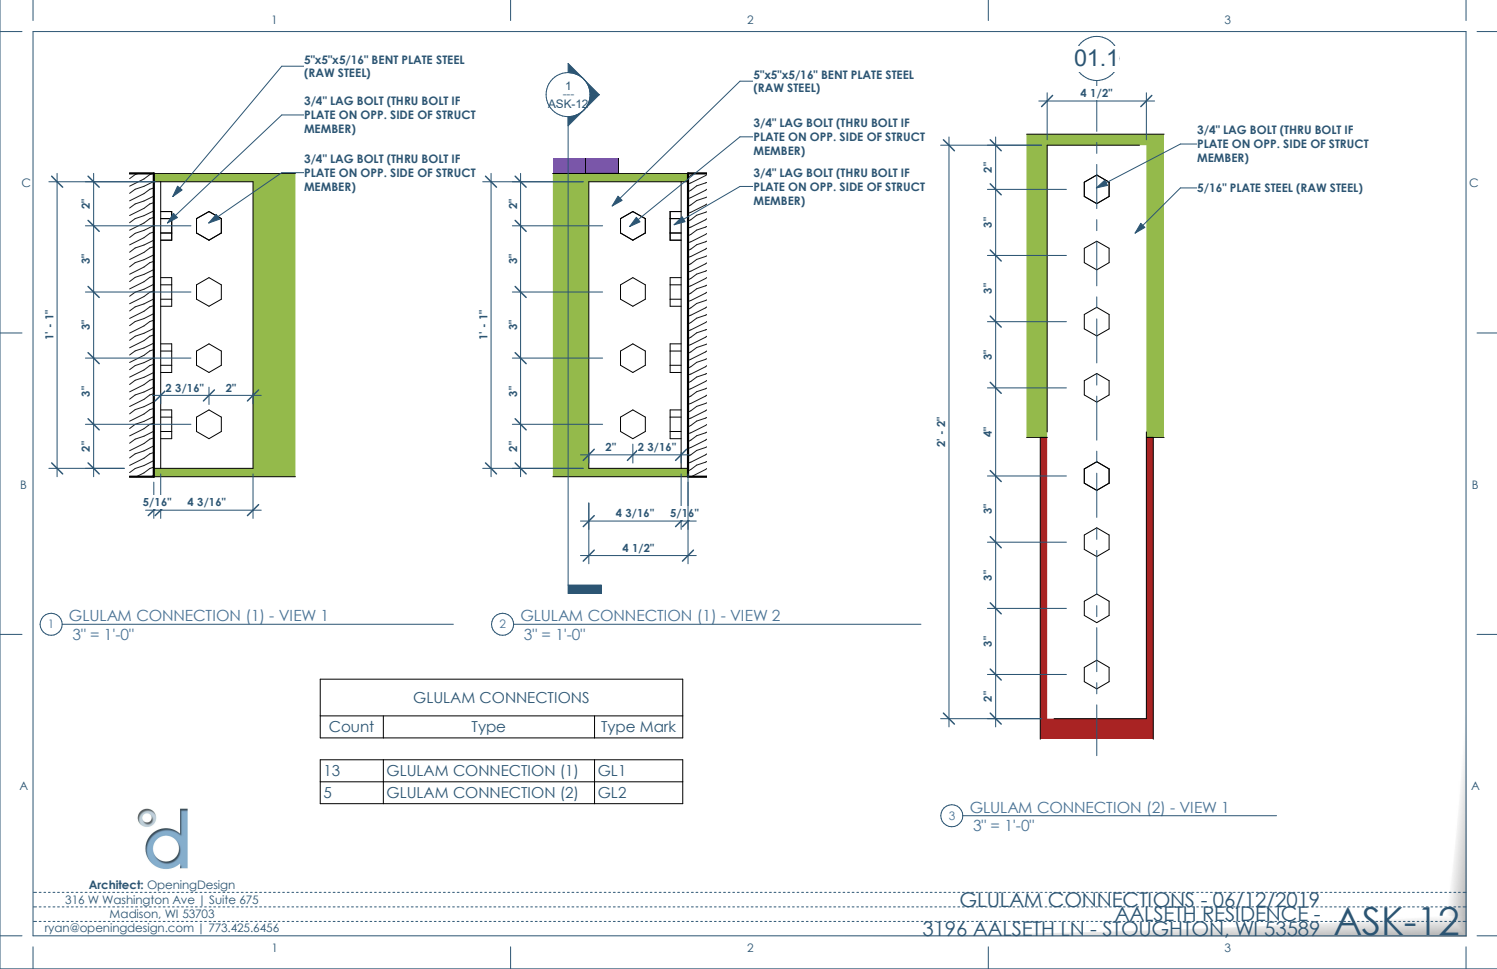
[picture p122: page 10]
(RAW STEEL); ASK-12; Architect: OpeningDesign; ryan@openingdesign.com | 773.425.6456; 3196 AALSETH LN - STOUGHTON, WI 53589 AALSETH RESIDENCE - GLULAM CONNECTIONS - 06/12/2019 ASK-12; GLULAM CONNECTIONS; Count; Type; Type Mark

5"x5"x5/16" BENT PLATE STEEL
(RAW STEEL)

3/4" LAG BOLT (THRU BOLT IF
PLATE ON OPP. SIDE OF STRUCT
MEMBER)

5/16" PLATE STEEL (RAW STEEL)

GLULAM CONNECTION (1) - VIEW 1

GLULAM CONNECTION (1) - VIEW 2

13 | GLULAM CONNECTION (1) | GL1
5 | GLULAM CONNECTION (2) | GL2

GLULAM CONNECTION (2) - VIEW 1

C | B
C

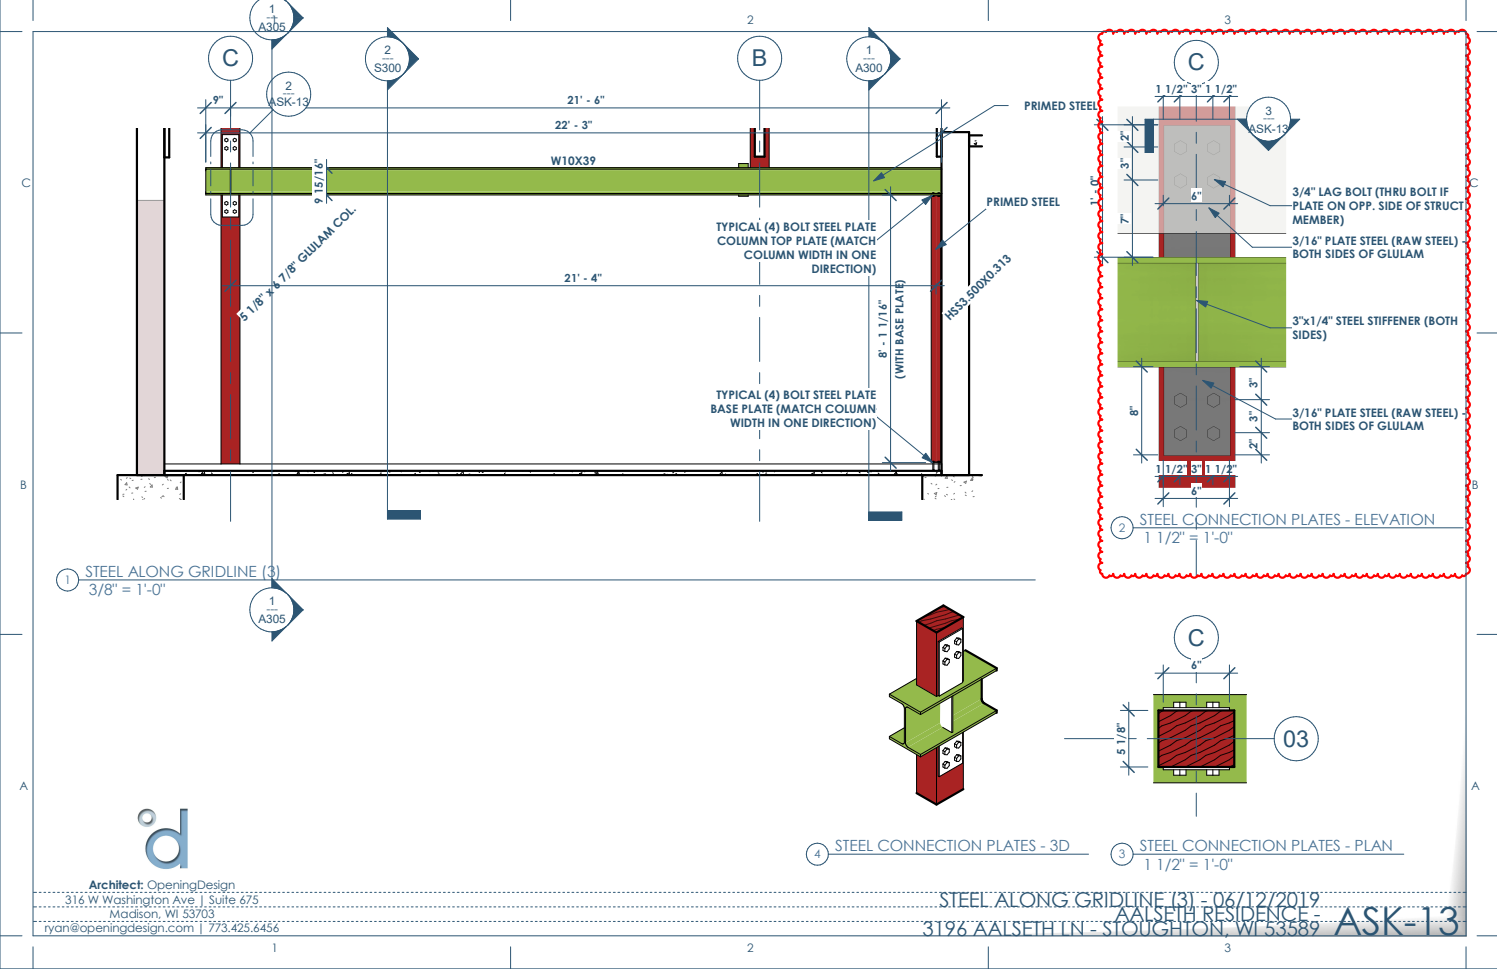
[picture p123: page 11]
PRIMED STEEL; HSS3.500X0.313; 5 1/8" x 6 7/8" GLULAM COL.; DIRECTION); ASK-13; Architect: OpeningDesign; ryan@openingdesign.com | 773.425.6456; 3196 AALSETH LN - STOUGHTON, WI 53589 AALSETH RESIDENCE - STEEL ALONG GRIDLINE (3) - 06/12/2019 ASK-13

3/4" LAG BOLT (THRU BOLT IF
PLATE ON OPP. SIDE OF STRUCT
MEMBER)
3/16" PLATE STEEL (RAW STEEL) -
BOTH SIDES OF GLULAM

TYPICAL (4) BOLT STEEL PLATE COLUMN TOP PLATE (MATCH COLUMN WIDTH IN ONE

(WITH BASE PLATE)

3"x1/4" STEEL STIFFENER (BOTH
SIDES)

TYPICAL (4) BOLT STEEL PLATE BASE PLATE (MATCH COLUMN WIDTH IN ONE DIRECTION)

STEEL CONNECTION PLATES - ELEVATION

STEEL ALONG GRIDLINE (3)

STEEL CONNECTION PLATES - PLAN 4

STEEL CONNECTION PLATES - 3D
