OpeningDesign/Aalseth_Residence/Transfer/20190414 - TO CONC. SUB - LATEST DETAILS/20190414 - 3196 Aalseth Lane - Foundation Details.pdf

02 | 03

01.1

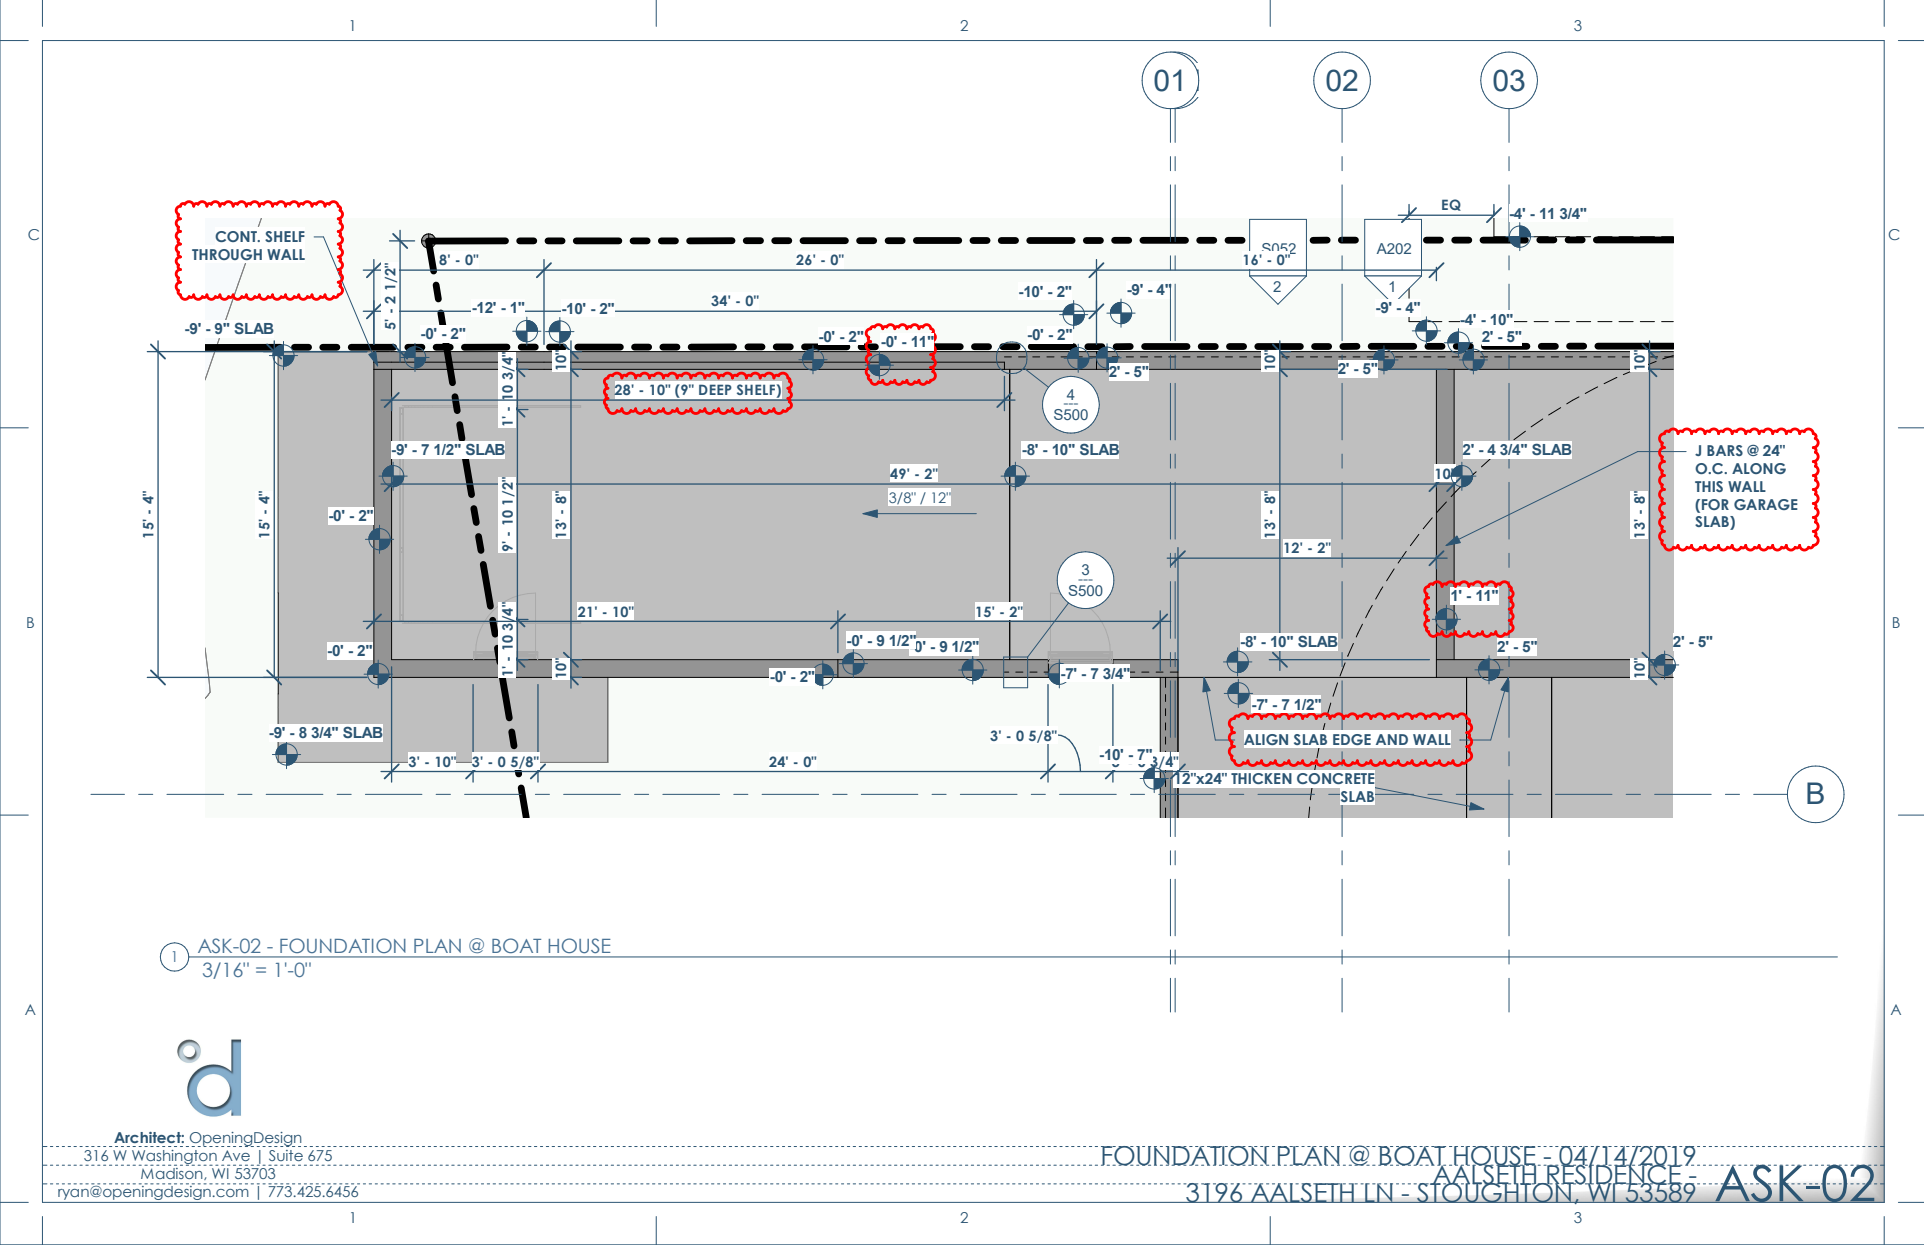
[picture p124: page 1]
-9' - 8 3/4" SLAB; -9' - 9" SLAB; -9' - 7 1/2" SLAB; -8' - 10" SLAB; 2' - 4 3/4" SLAB; 12"x24" THICKEN CONCRETE SLAB; 01 --- S500 3 28' - 10" (9" DEEP SHELF); CONT. SHELF THROUGH WALL; J BARS @ 24" O.C. ALONG THIS WALL (FOR GARAGE SLAB); Madison, WI 53703; ryan@openingdesign.com | 773.425.6456; 3196 AALSETH LN - STOUGHTON, WI 53589 AALSETH RESIDENCE - FOUNDATION PLAN @ BOAT HOUSE - 04/14/2019 ASK-02

-8' - 10" SLAB

ALIGN SLAB EDGE AND WALL

3/16" = 1'-0" ¹ ASK-02 - FOUNDATION PLAN @ BOAT HOUSE

Architect: OpeningDesign
316 W Washington Ave | Suite 675

02

03

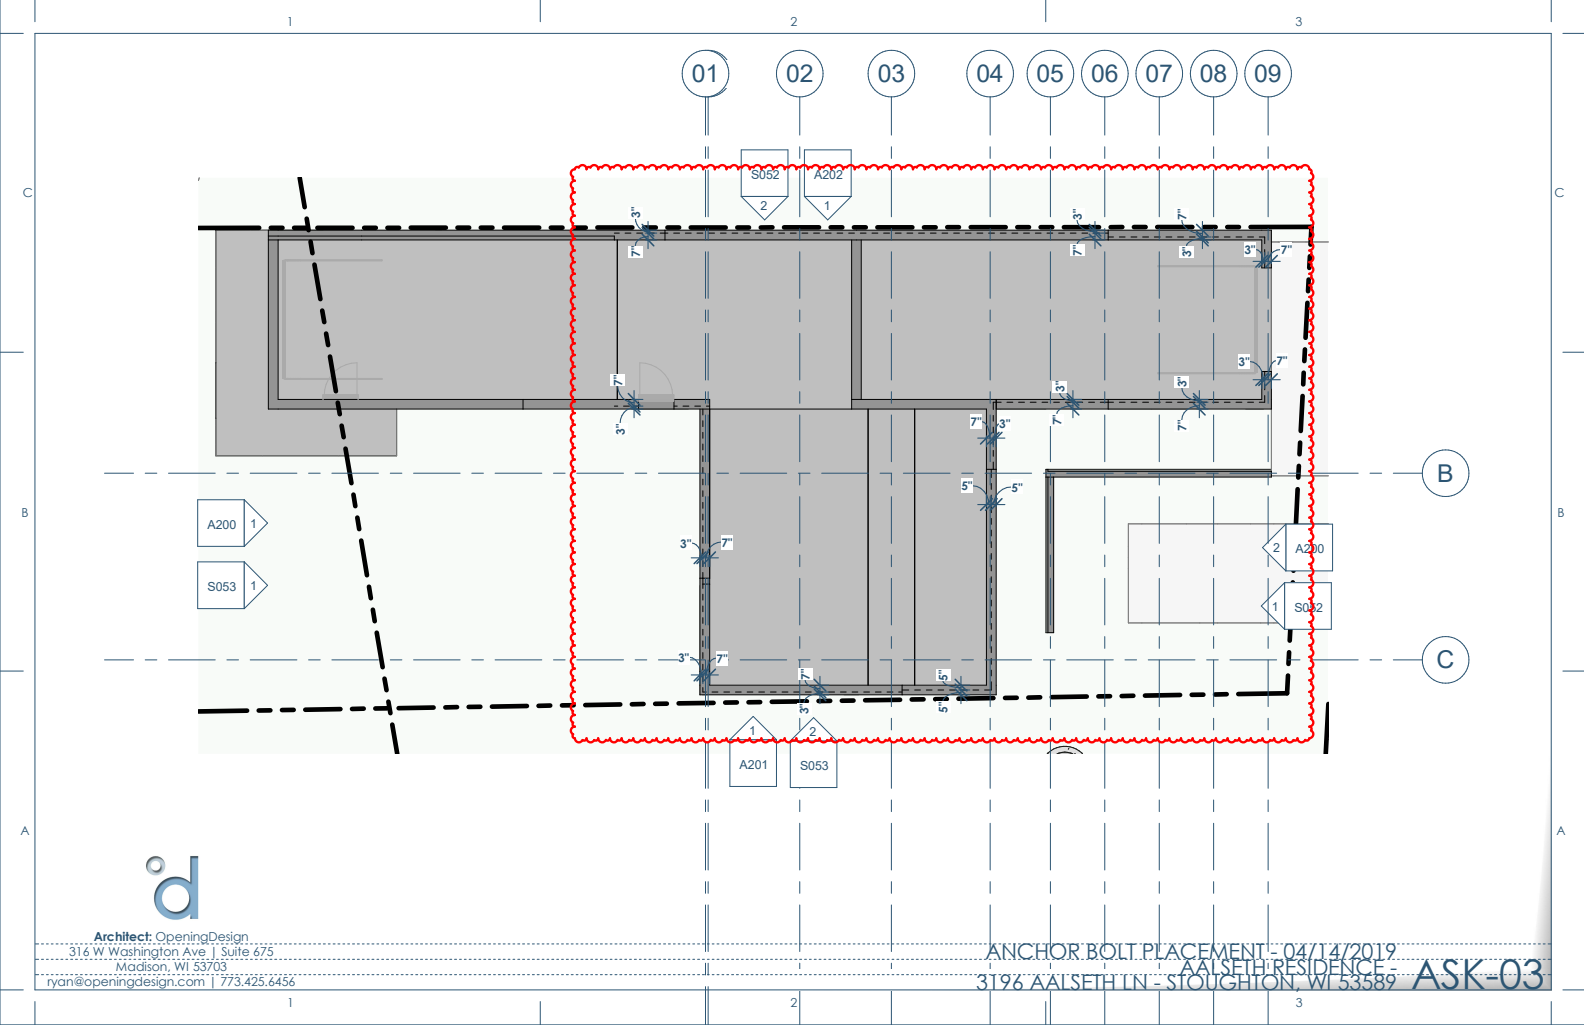
[picture p125: page 2]
Architect: OpeningDesign; ryan@openingdesign.com | 773.425.6456; 3196 AALSETH LN - STOUGHTON, WI 53589 AALSETH RESIDENCE - ANCHOR BOLT PLACEMENT - 04/14/2019 ASK-03

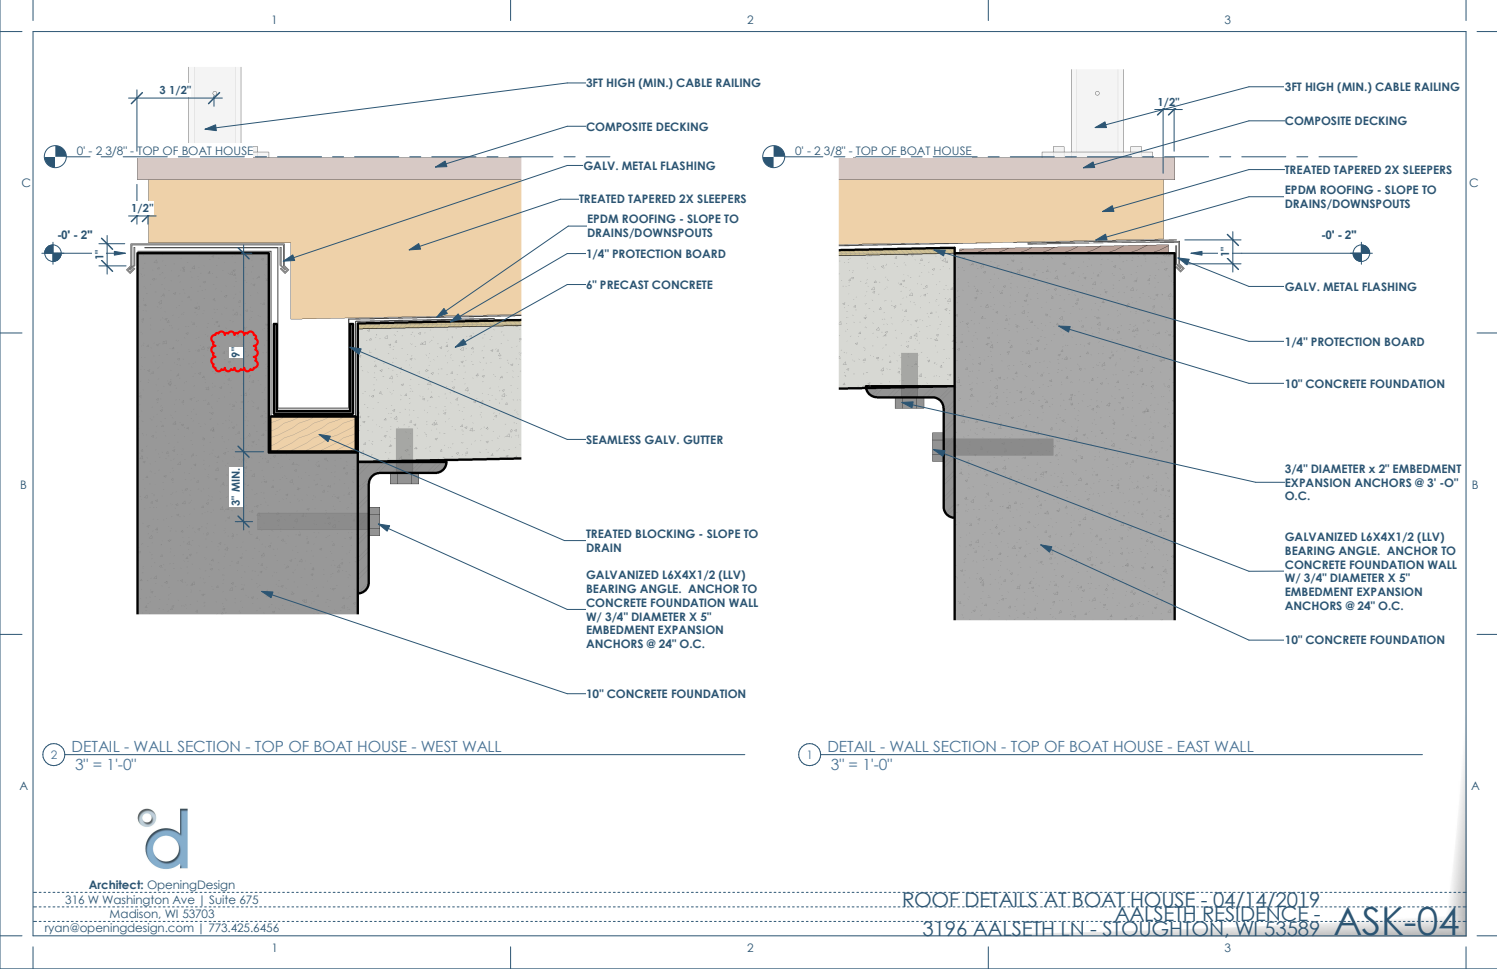
[picture p126: page 3]
COMPOSITE DECKING; 1/4" PROTECTION BOARD; 10" CONCRETE FOUNDATION; 3/4" DIAMETER x 2" EMBEDMENT EXPANSION ANCHORS @ 3' -O" O.C.; 3" MIN. 9"; 6" PRECAST CONCRETE; Architect: OpeningDesign; ryan@openingdesign.com | 773.425.6456; 3196 AALSETH LN - STOUGHTON, WI 53589 AALSETH RESIDENCE - ROOF DETAILS AT BOAT HOUSE - 04/14/2019 ASK-04

3FT HIGH (MIN.) CABLE RAILING

0' - 2 3/8" - TOP OF BOAT HOUSE

GALV. METAL FLASHING

TREATED TAPERED 2X SLEEPERS
EPDM ROOFING - SLOPE TO
DRAINS/DOWNSPOUTS

1/4" PROTECTION BOARD

SEAMLESS GALV. GUTTER

TREATED BLOCKING - SLOPE TO
DRAIN

GALVANIZED L6X4X1/2 (LLV)
BEARING ANGLE. ANCHOR TO
CONCRETE FOUNDATION WALL
W/ 3/4" DIAMETER X 5"
EMBEDMENT EXPANSION
ANCHORS @ 24" O.C.

3" = 1'-0" ¹ DETAIL - WALL SECTION - TOP OF BOAT HOUSE - EAST WALL 3" = 1'-0" ² DETAIL - WALL SECTION - TOP OF BOAT HOUSE - WEST WALL
