OpeningDesign/Aalseth_Residence/Transfer/20190506 - to HVAC contractor - newly proposed duct routing/20190506 - 3196 Aalseth Lane.pdf

02

03

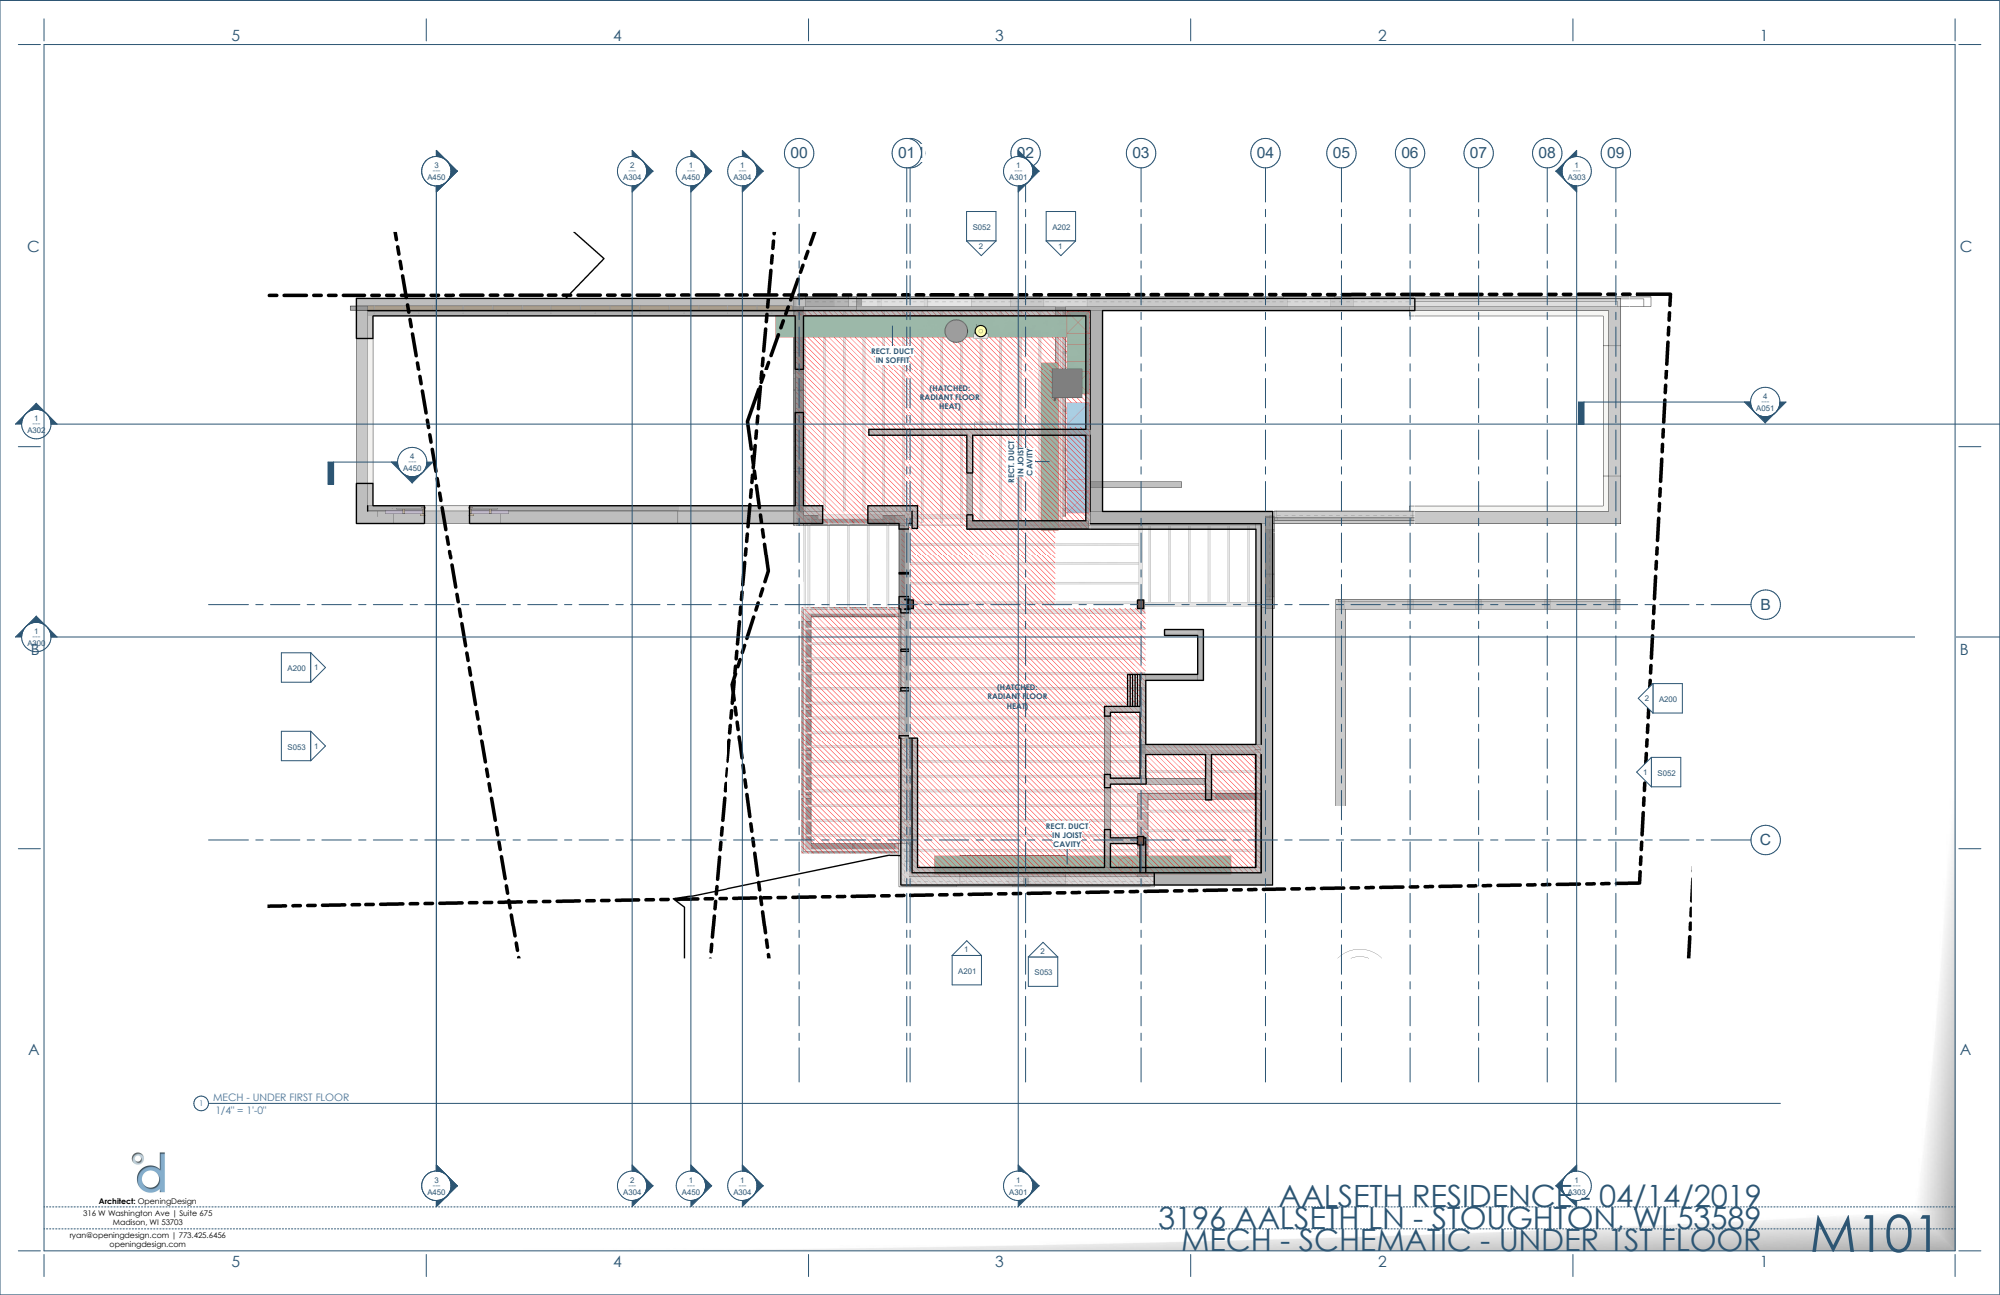
[picture p127: page 1]
(HATCHED: RADIANT FLOOR HEAT); RECT. DUCT; IN JOIST; CAVITY; RECT. DUCT IN SOFFIT; RECT. DUCT IN JOIST CAVITY; Madison, WI 53703; openingdesign.com; AALSETH RESIDENCE - 04/14/2019

1/4" = 1'-0" ¹ MECH - UNDER FIRST FLOOR

Architect: OpeningDesign
316 W Washington Ave | Suite 675

3196 AALSETH LN - STOUGHTON, WI 53589
MECH - SCHEMATIC - UNDER 1ST FLOOR

ryan@openingdesign.com | 773.425.6456

02

03

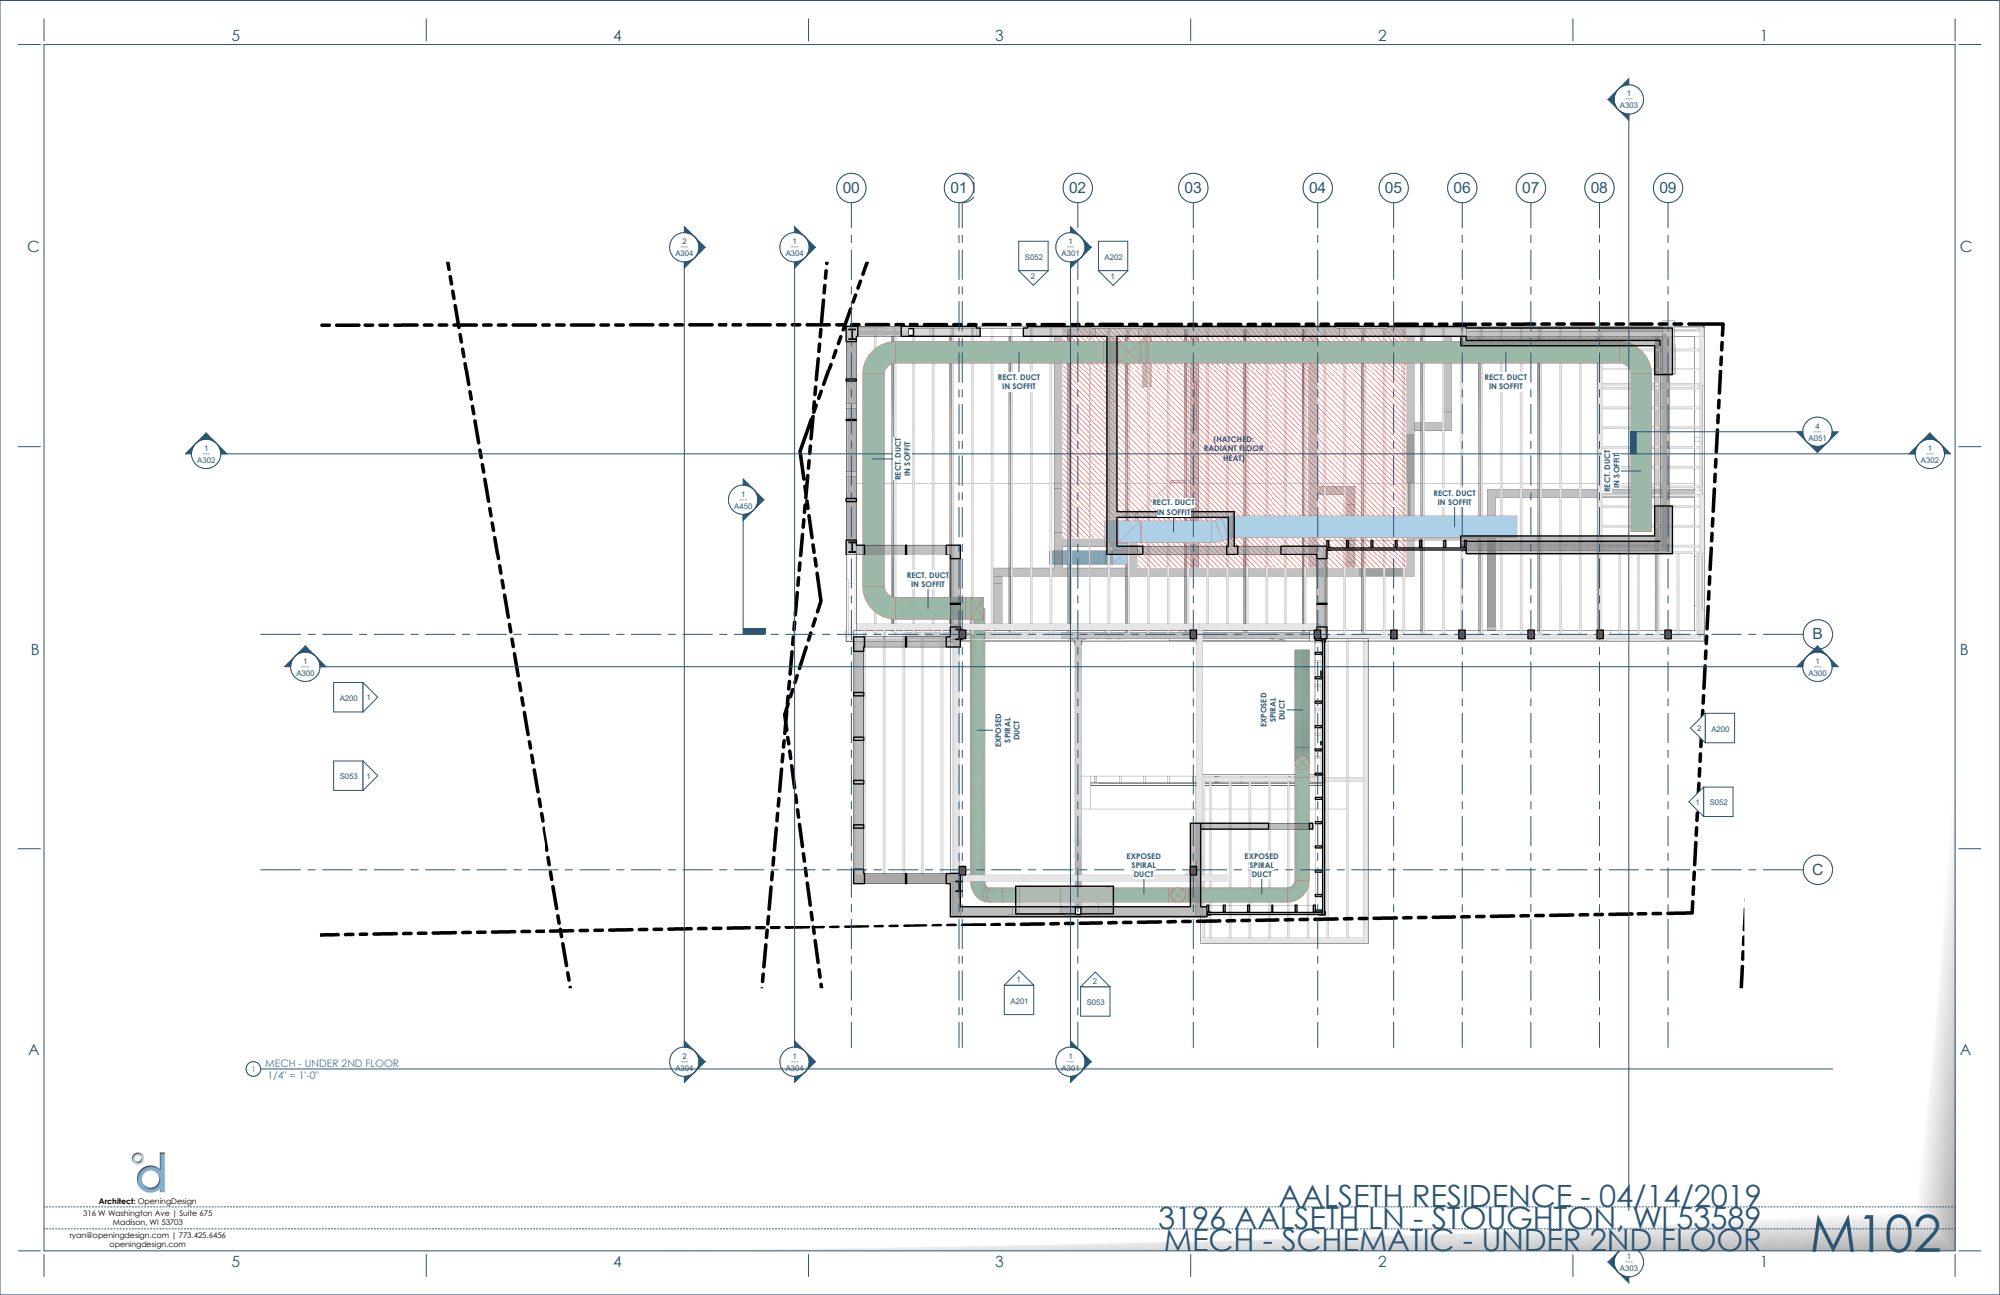
[picture p128: page 2]
09 EXPOSED SPIRAL DUCT; RECT. DUCT IN SOFFIT; RECT. DUCT; IN SOFFIT; EXPOSED SPIRAL; DUCTEXPOSED SPIRAL; DUCT; (HATCHED: RADIANT FLOOR HEAT); EXPOSED SPIRAL DUCT

MECH - UNDER 2ND FLOOR

MECH - SCHEMATIC - UNDER 2ND FLOOR

02

03

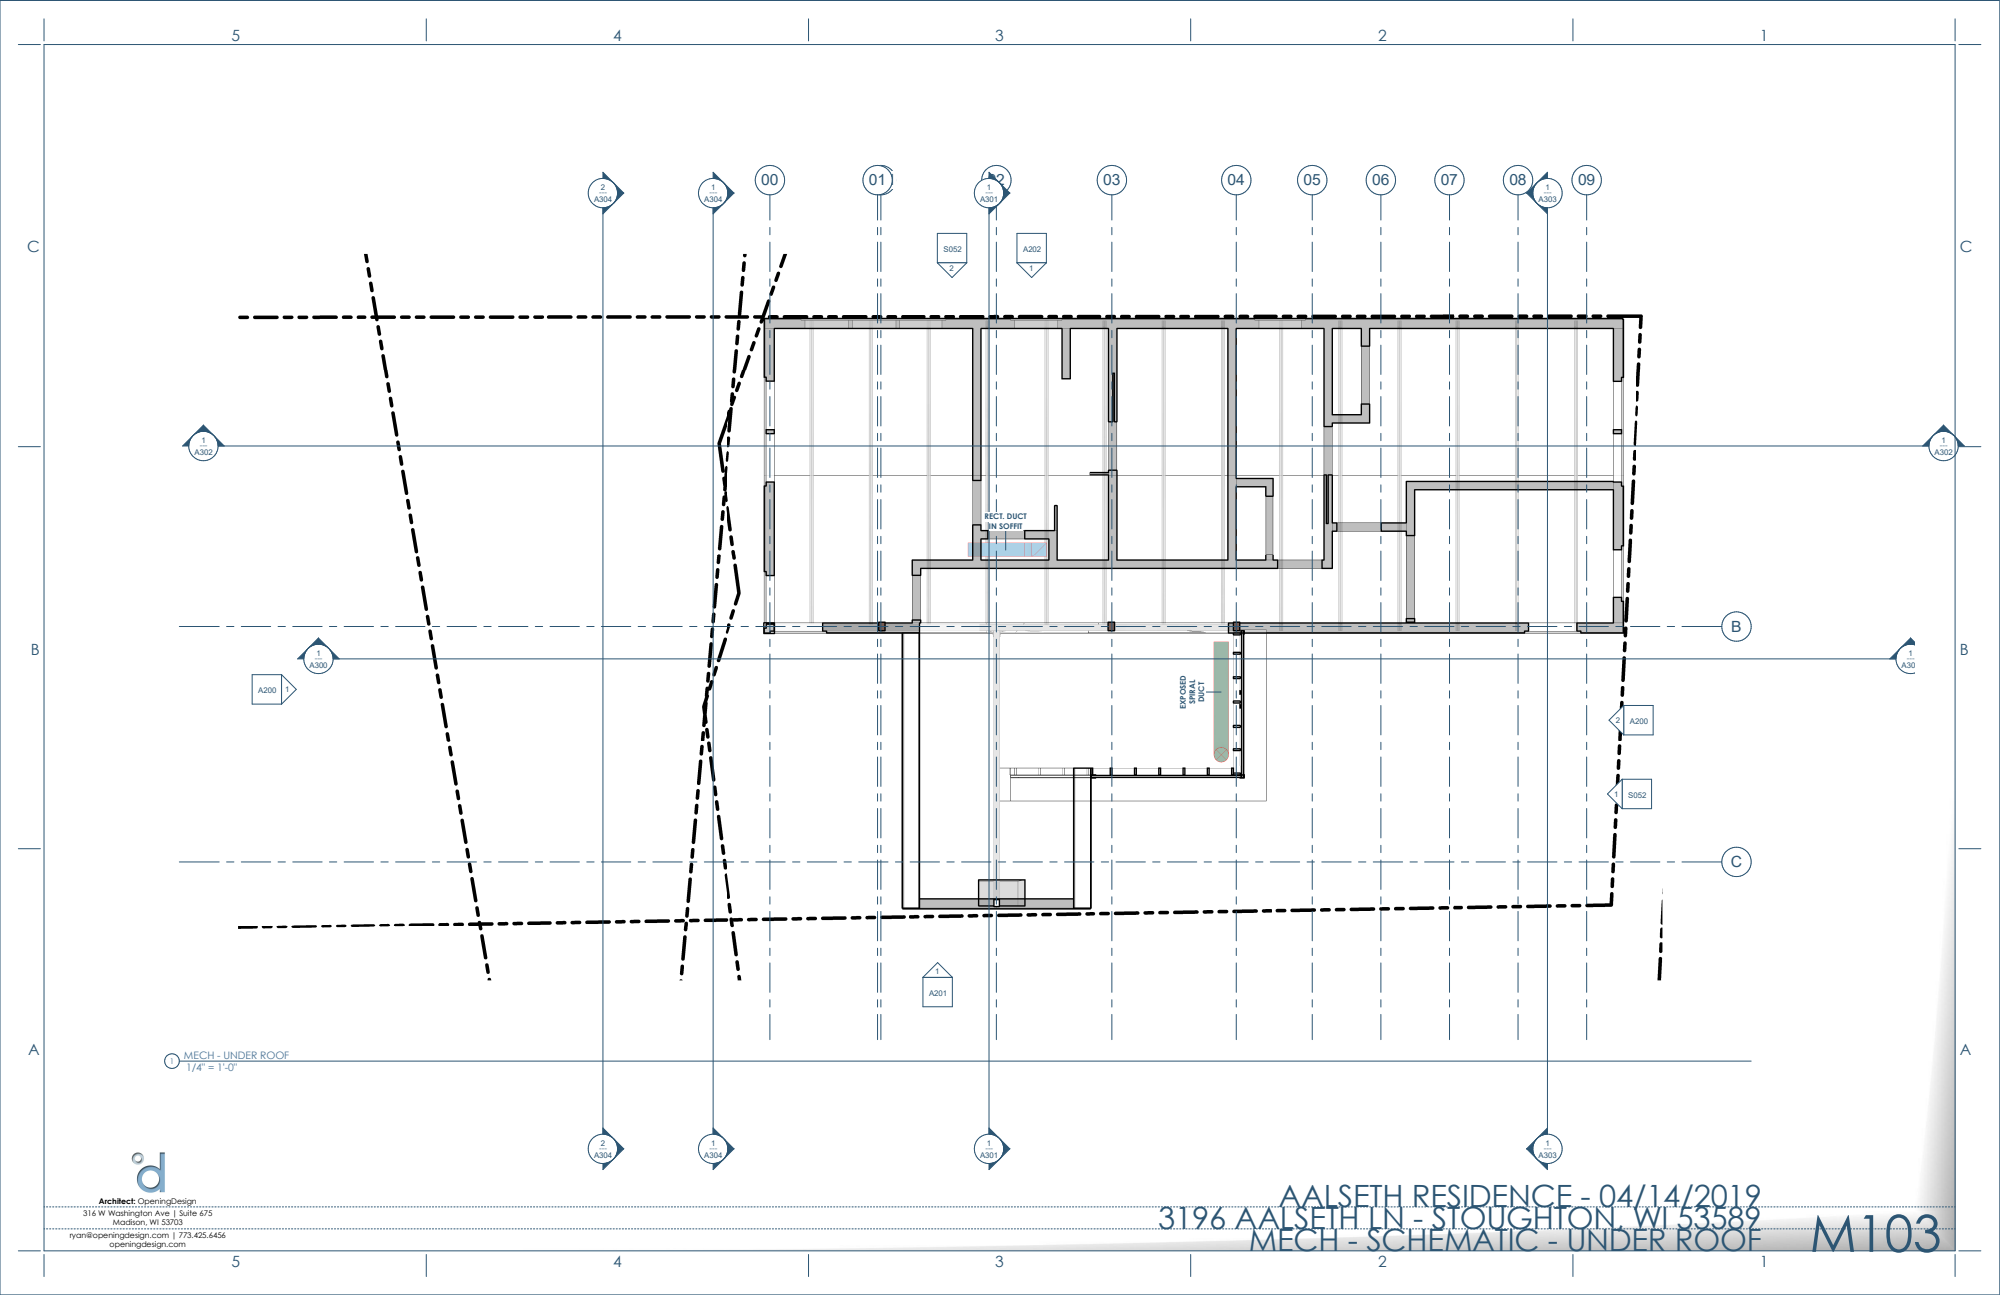
[picture p129: page 3]
09 EXPOSED SPIRAL DUCT; RECT. DUCT IN SOFFIT

MECH - UNDER ROOF

MECH - SCHEMATIC - UNDER ROOF
