OpeningDesign/Aalseth_Residence/Transfer/20190110 - ASK-01 - seam detail in concrete/20190110 - ASK-01 - seam detail in concrete.pdf

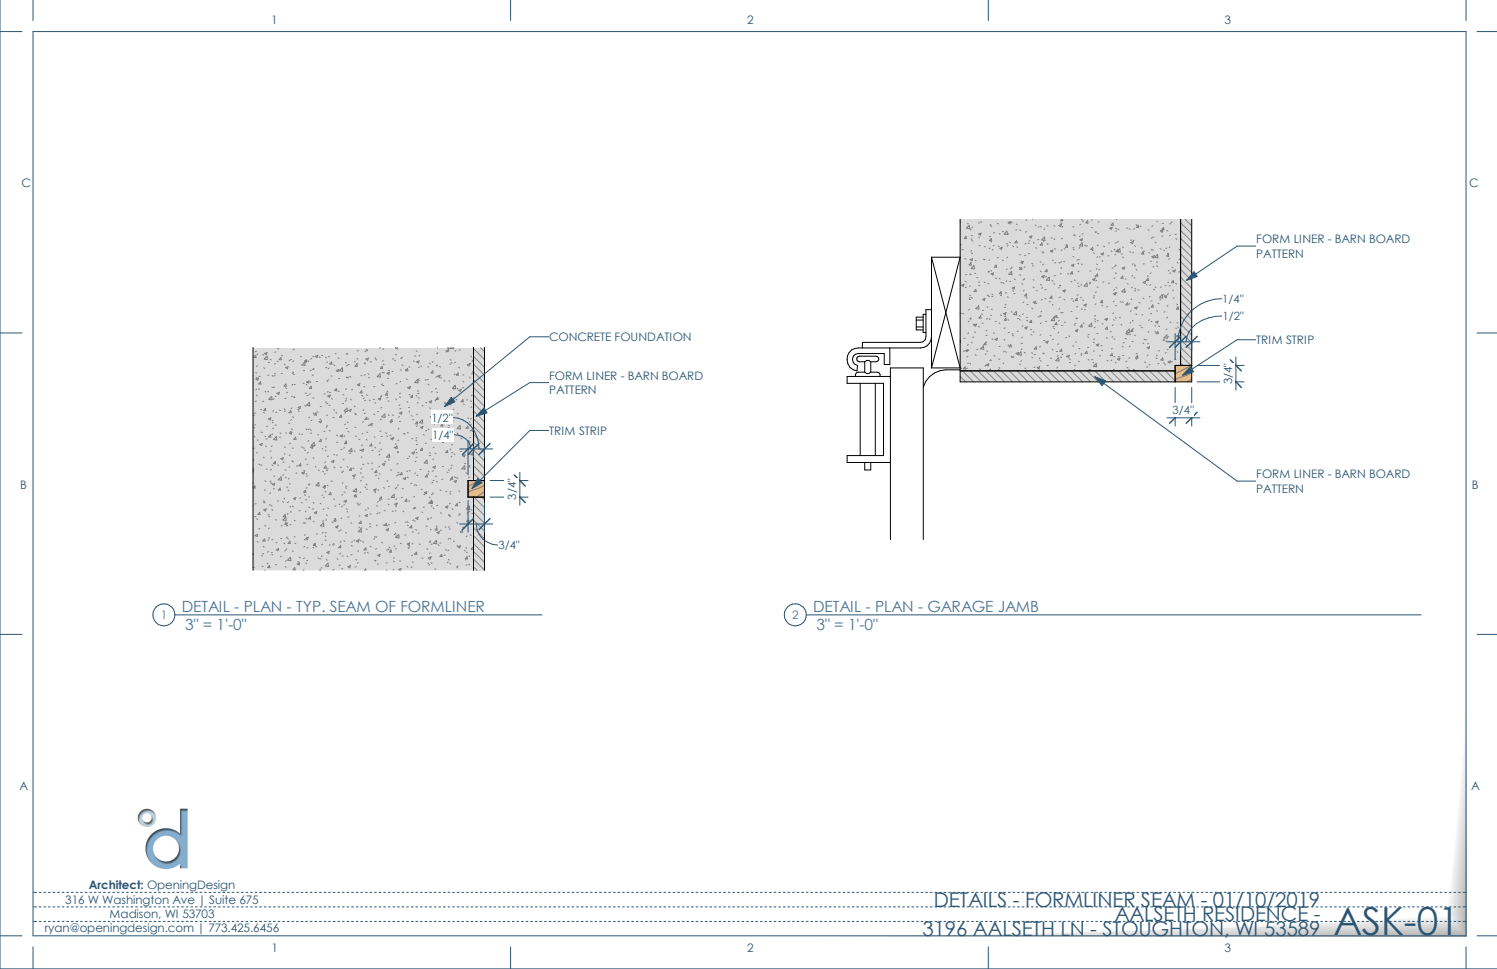
[picture p130: page 1]
TRIM STRIP; CONCRETE FOUNDATION; Madison, WI 53703; ryan@openingdesign.com | 773.425.6456; 3196 AALSETH LN - STOUGHTON, WI 53589 AALSETH RESIDENCE - DETAILS - FORMLINER SEAM - 01/10/2019 ASK-01

FORM LINER - BARN BOARD
PATTERN

DETAIL - PLAN - TYP. SEAM OF FORMLINER

DETAIL - PLAN - GARAGE JAMB

Architect: OpeningDesign
316 W Washington Ave | Suite 675
