OpeningDesign/Aalseth_Residence/Transfer/20190601 - to structural - beam proposal/20190601 - 3196 Aalseth Lane - Beam Proposal.pdf

02

03

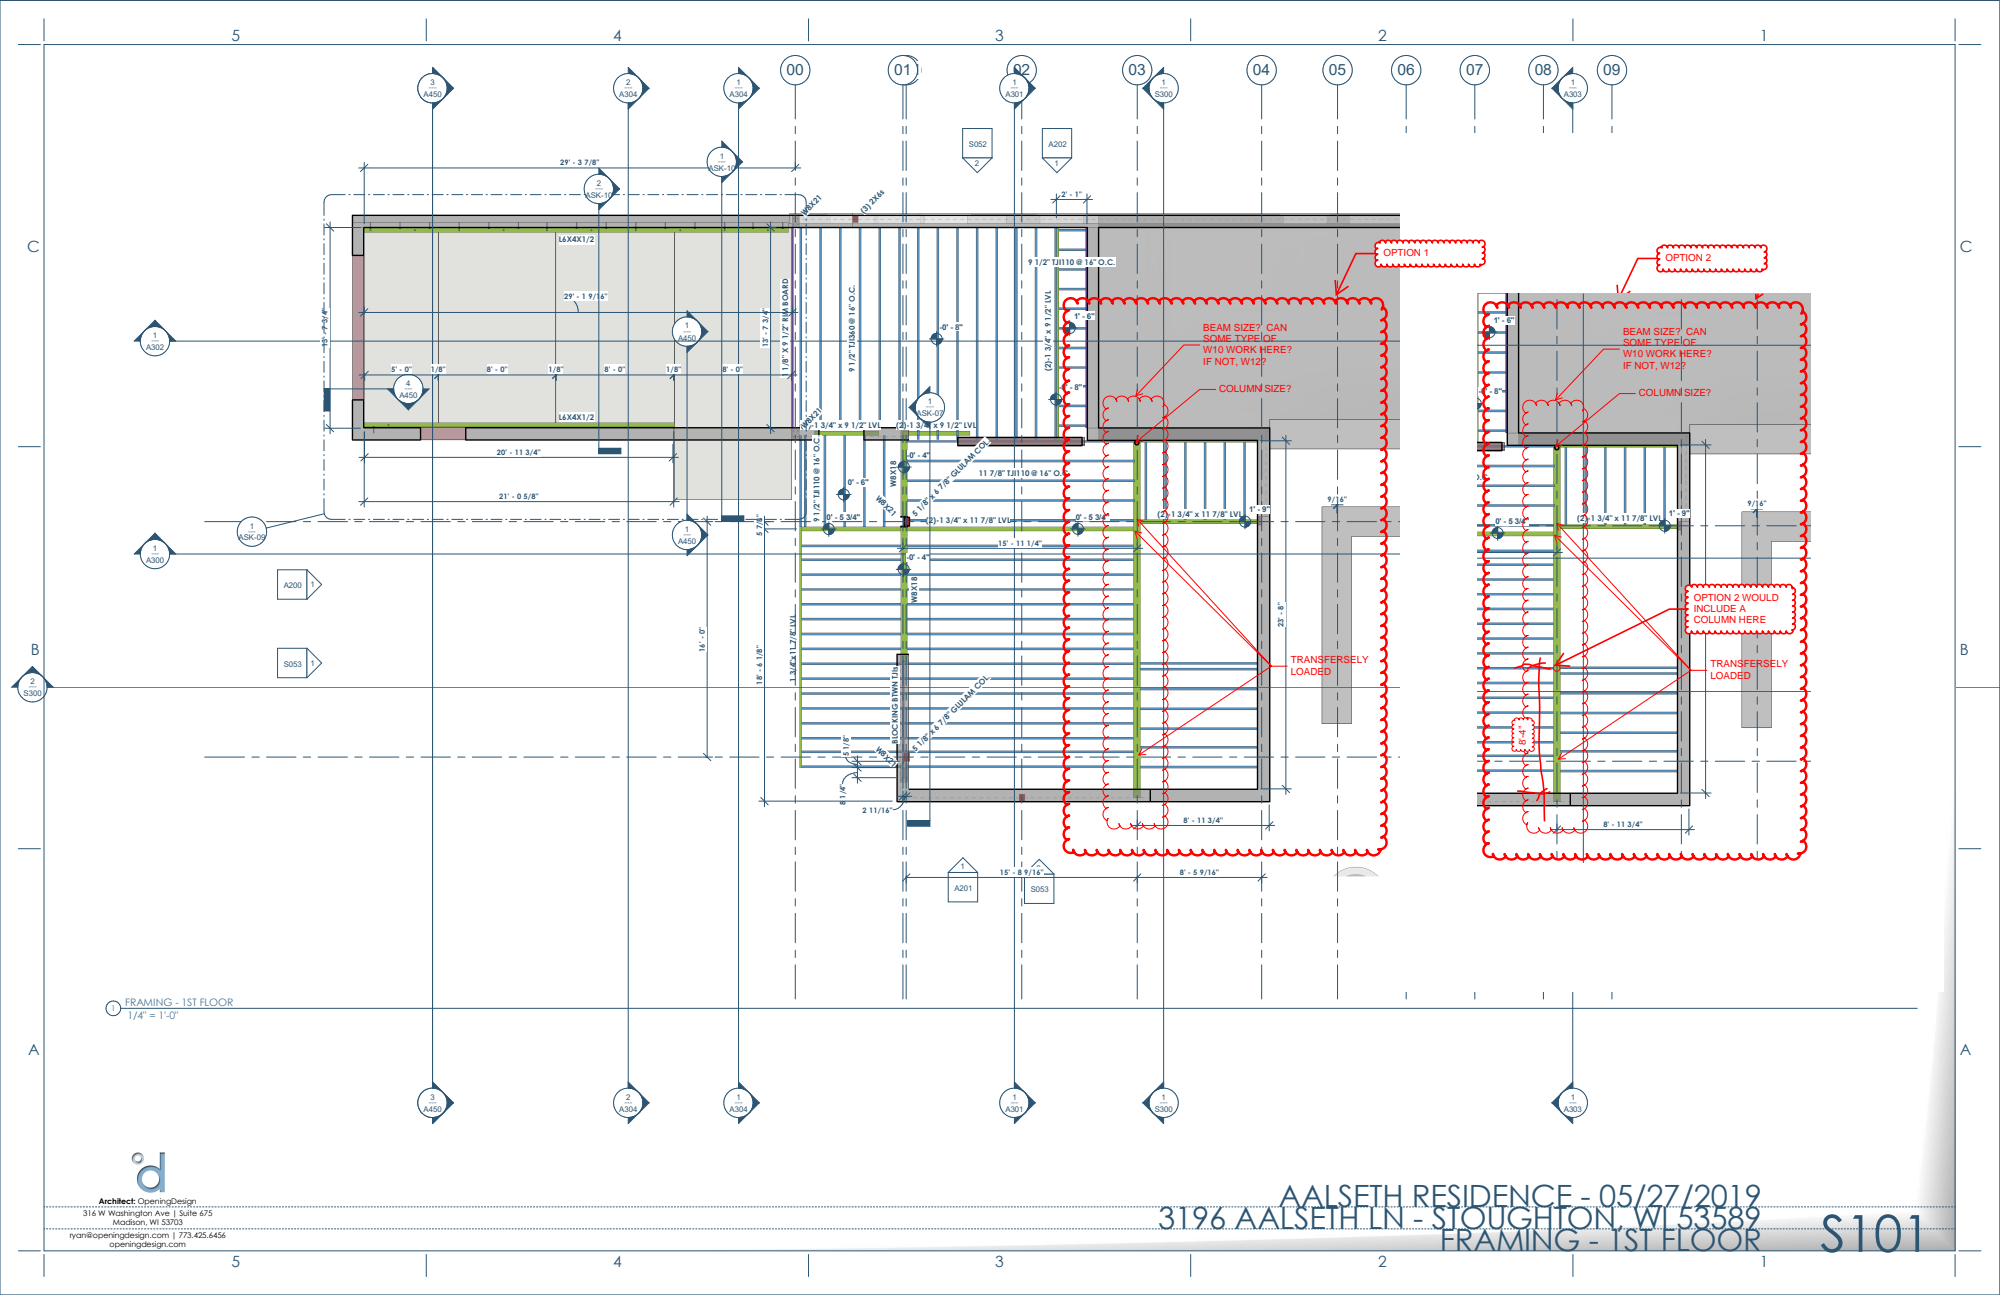
[picture p133: page 1]
9 1/2" TJI360 @ 16" O.C.; 9 1/2" TJI110 @ 16" O.C.; (2)-1 3/4" x 11 7/8" LVL; 5 1/8" x 6 7/8" GLULAM COL. W8X18; (2)-1 3/4" x 9 1/2" LVL; 5 1/8" x 6 7/8" GLULAM COL.; 11 7/8" TJI110 @ 16" O.C.; 1 1/8" X 9 1/2" RIM BOARD; 1 3/4"x11 7/8" LVL; ASK-07; ASK-10; --- ASK-09; Madison, WI 53703; openingdesign.com; FRAMING - 1ST FLOOR; AALSETH RESIDENCE - 05/27/2019

BLOCKING BTWN TJIs

Architect: OpeningDesign
316 W Washington Ave | Suite 675

3196 AALSETH LN - STOUGHTON, WI 53589

ryan@openingdesign.com | 773.425.6456

02

03

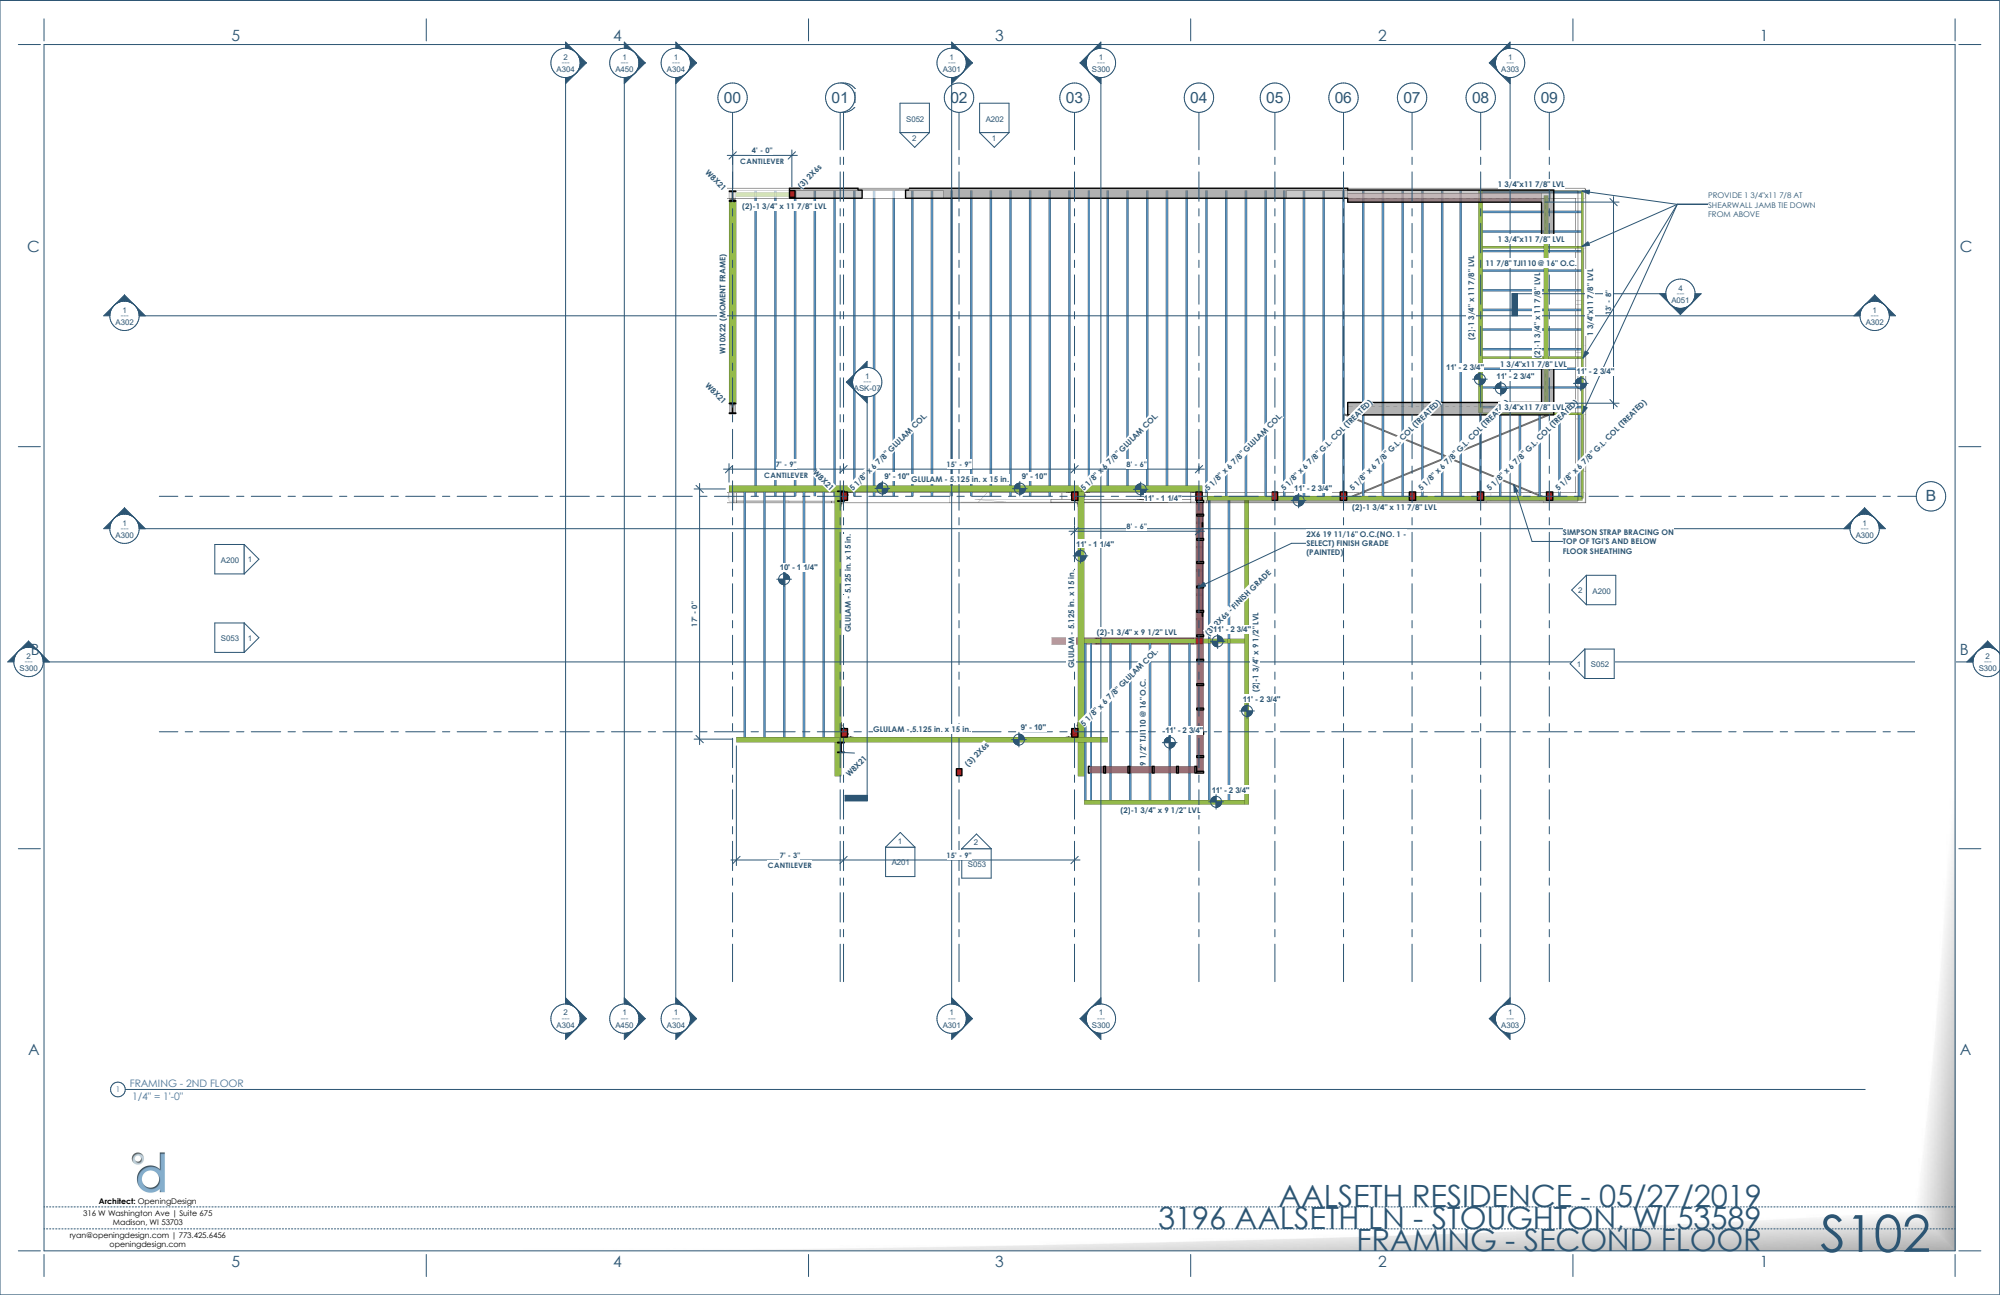
[picture p134: page 2]
09 (2⁾⁻1 3/4" x 11 7/8" LVL; 5 1/8" x 6 7/8" G.L. COL (TREATED); 5 1/8" x 6 7/8" GLULAM COL.; (2)-1 3/4" x 9 1/2" LVL; (2)-1 3/4" x 11 7/8" LVL; (3) 2X6s - FINISH GRADE; CANTILEVER; W10X22 (MOMENT FRAME); (2)-1 3/4" x 9 1/2" LVL 9 1/2" TJI110 @ ¹⁶" O.C.; 1 3/4"x11 7/8" LVL; 11 7/8" TJI110 @ 16" O.C.; ASK-07; FRAMING - 2ND FLOOR

PROVIDE 1 3/4"x11 7/8 AT
SHEARWALL JAMB TIE DOWN
FROM ABOVE

GLULAM - 5.125 in. x 15 in.

SELECT) FINISH GRADE
(PAINTED)

SIMPSON STRAP BRACING ON
TOP OF TGI'S AND BELOW
FLOOR SHEATHING

FRAMING - SECOND FLOOR

02

03

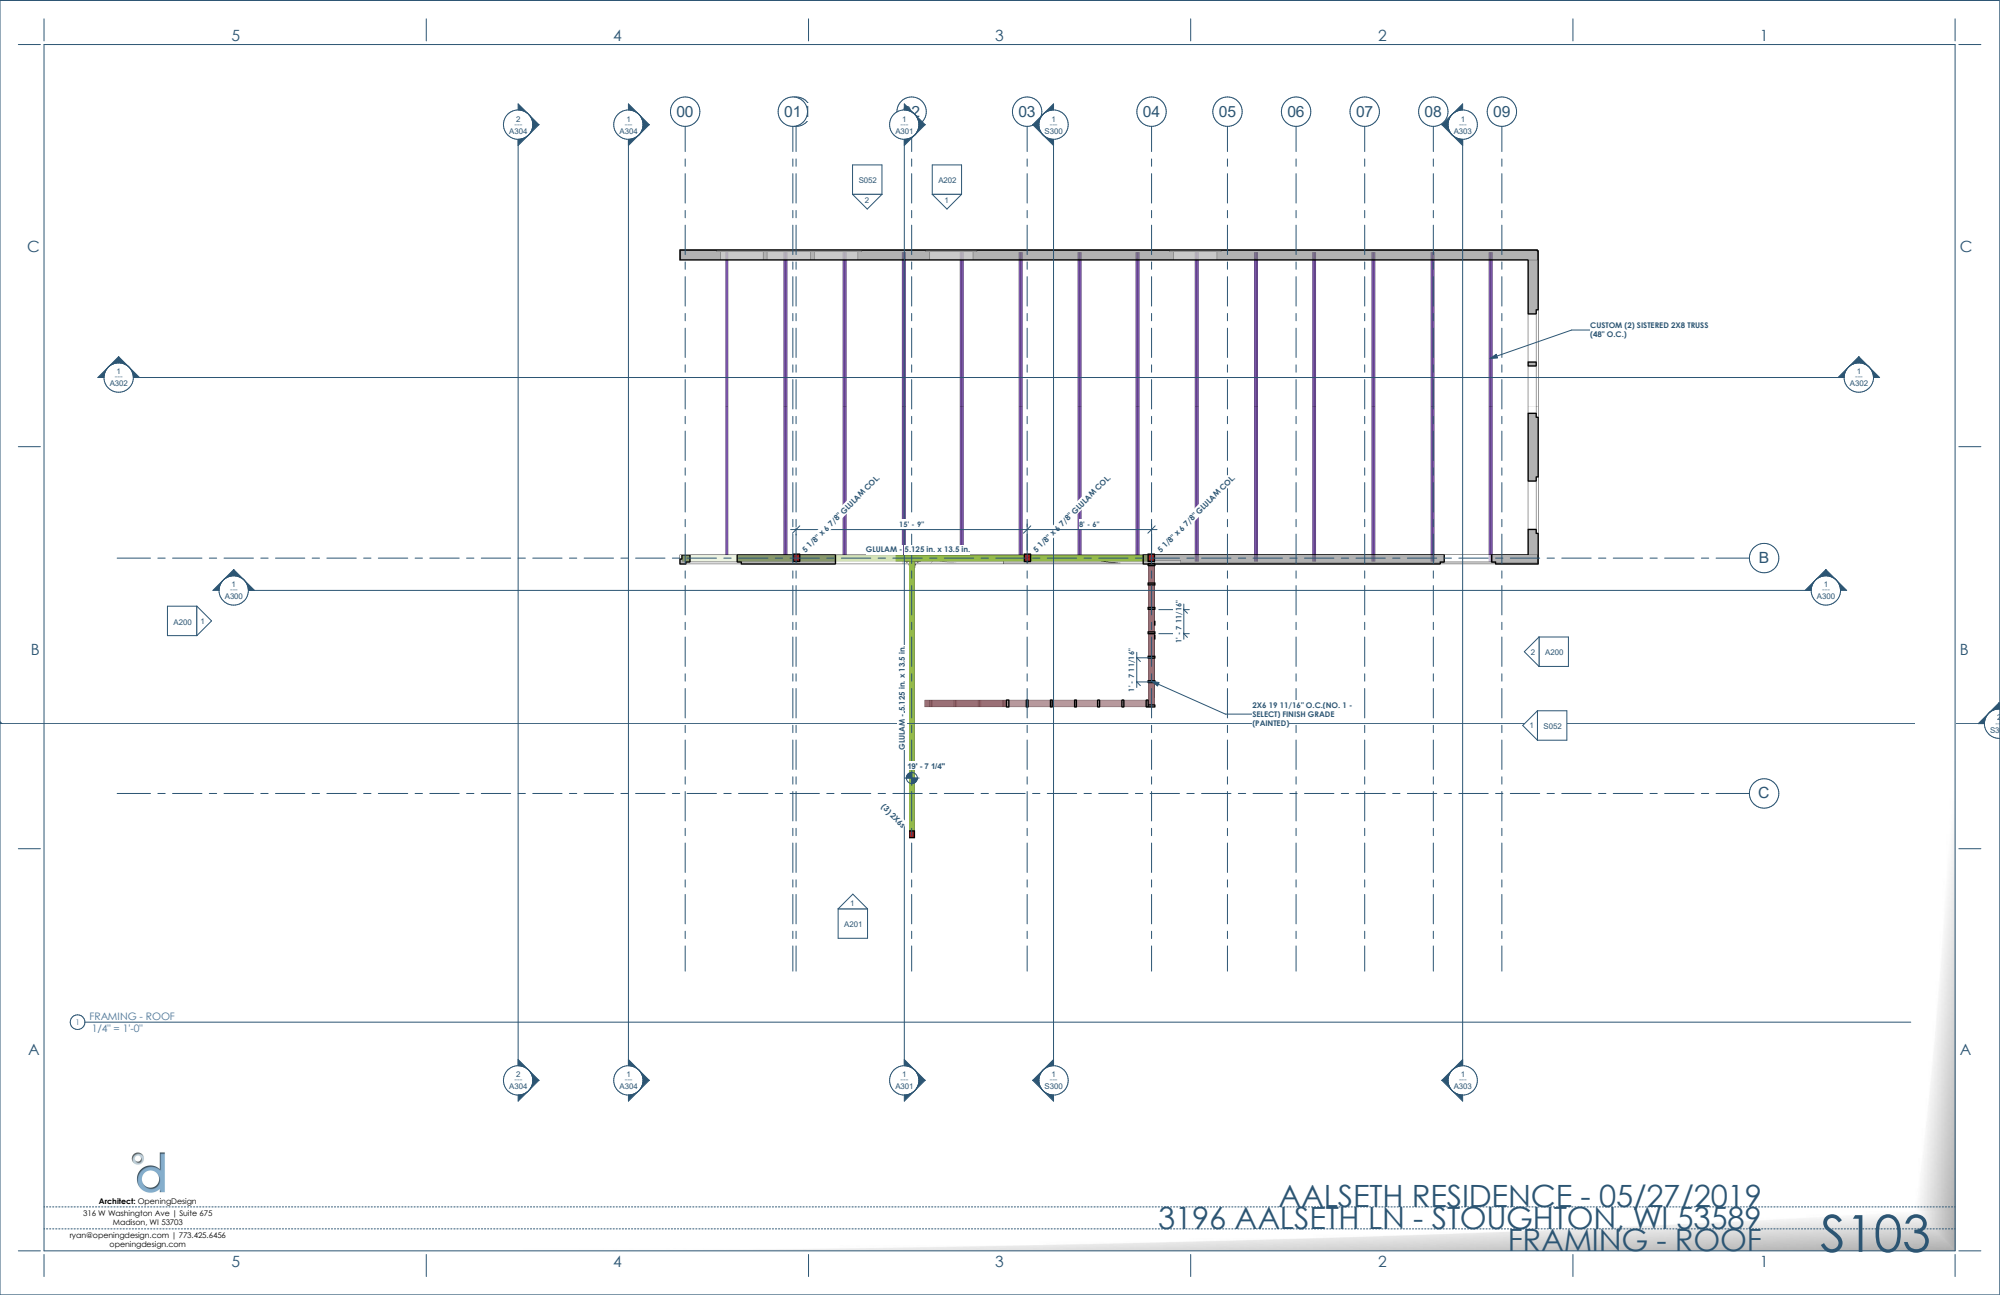
[picture p135: page 3]
5 1/8" x 6 7/8" GLULAM COL.; FRAMING - ROOF

CUSTOM (2) SISTERED 2X8 TRUSS

GLULAM - 5.125 in. x 13.5 in.

SELECT) FINISH GRADE
(PAINTED)

C

C

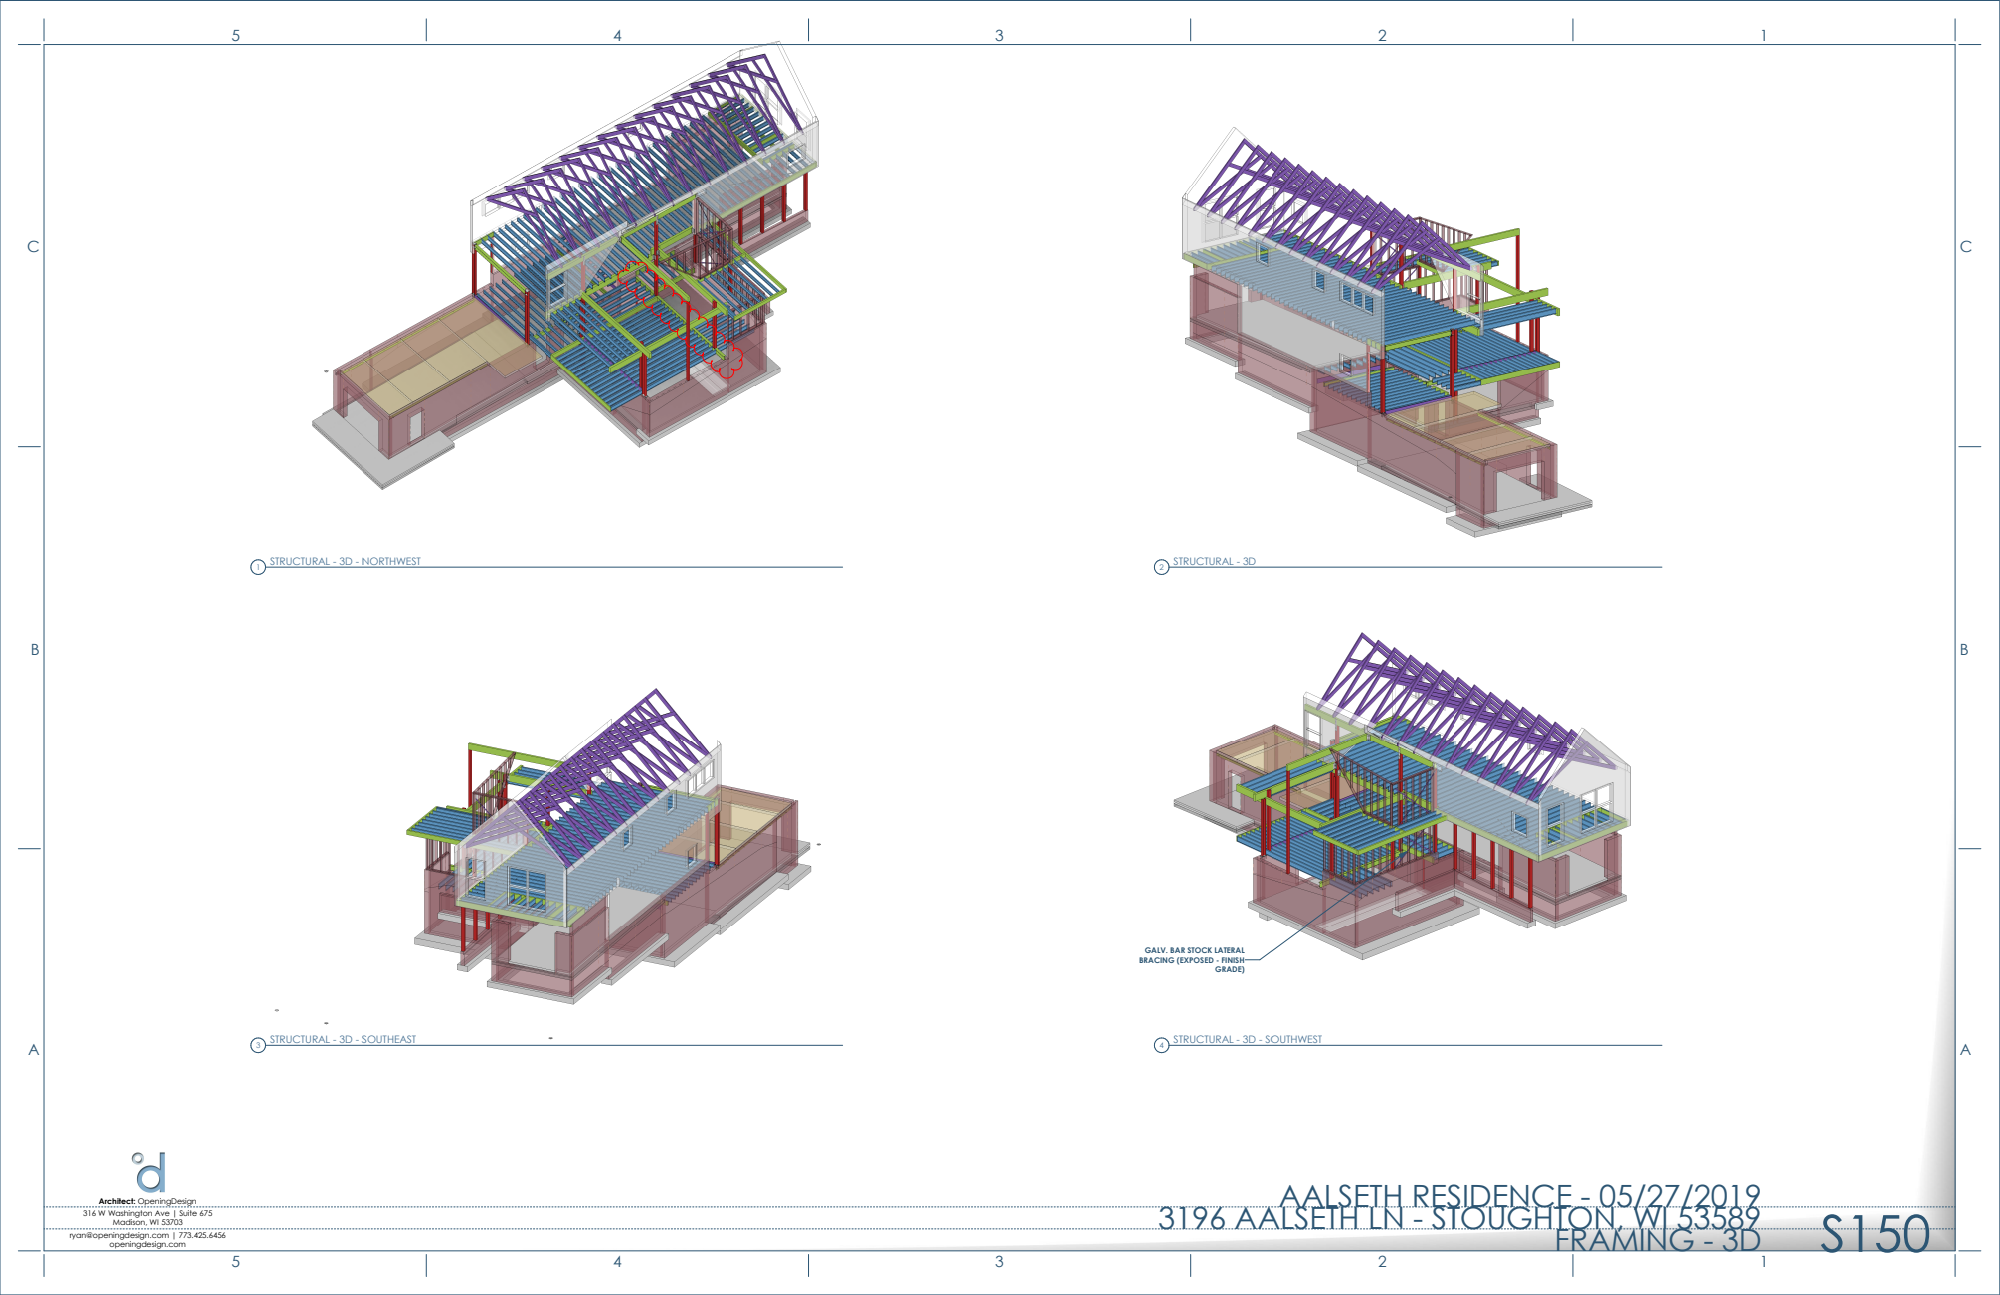
[picture p136: page 4]
GRADE); FRAMING - 3D; STRUCTURAL - 3D - NORTHWEST; STRUCTURAL - 3D; STRUCTURAL - 3D - SOUTHEAST; STRUCTURAL - 3D - SOUTHWEST

GALV. BAR STOCK LATERAL
BRACING (EXPOSED - FINISH

C | B
02 | 03

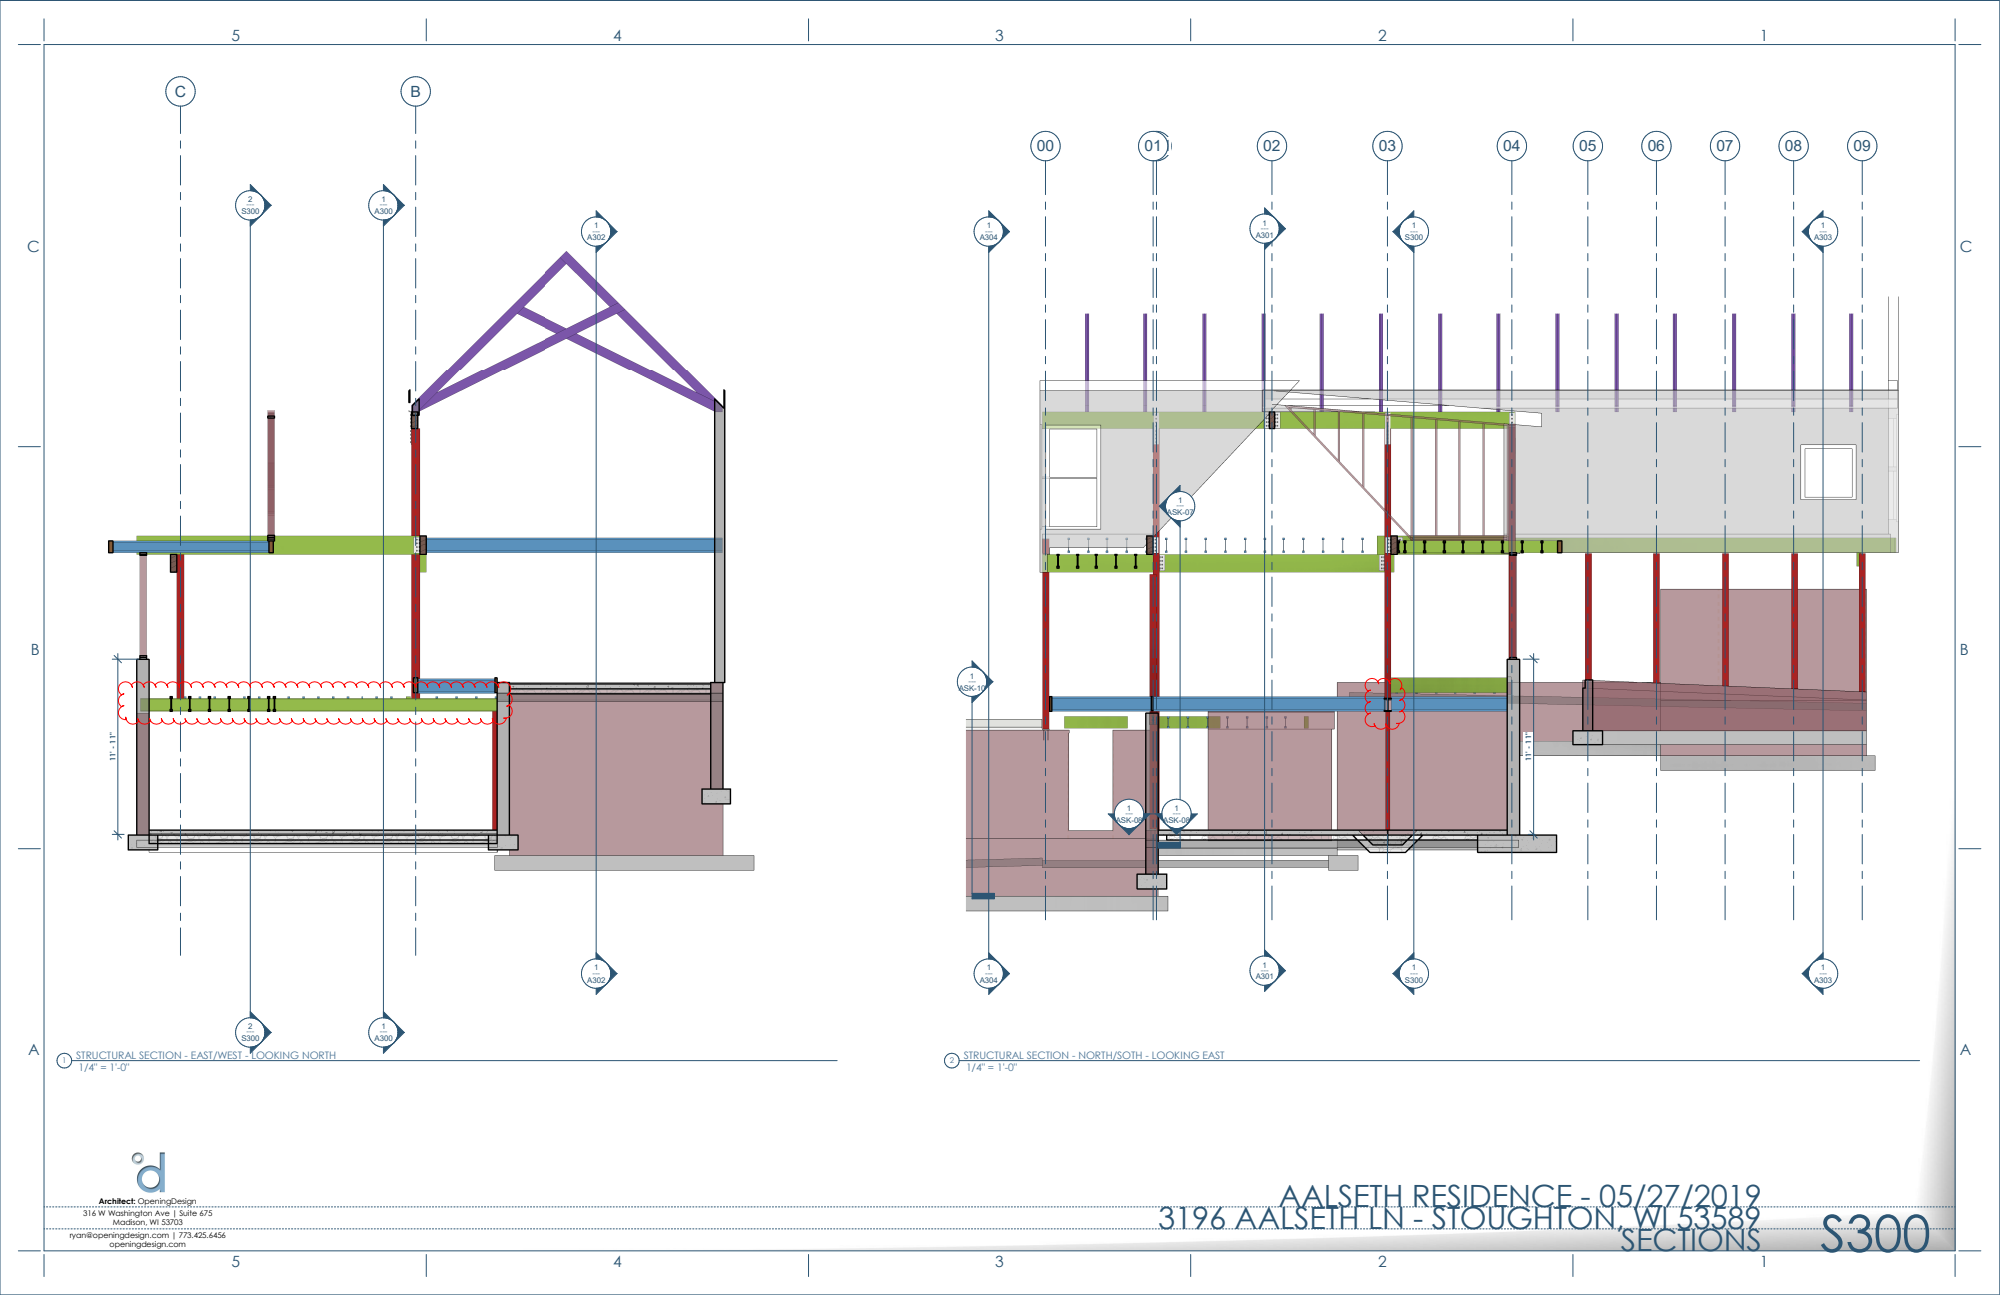
[picture p137: page 5]
ASK-07; ASK-10; ASK-08; SECTIONS

STRUCTURAL SECTION - EAST/WEST - LOOKING NORTH

STRUCTURAL SECTION - NORTH/SOTH - LOOKING EAST
