OpeningDesign/Aalseth_Residence/Transfer/20190514 - to Precast Manu - Boathouse precast/20190514 -  3196 Aalseth Lane - Precast Measurements.pdf

00

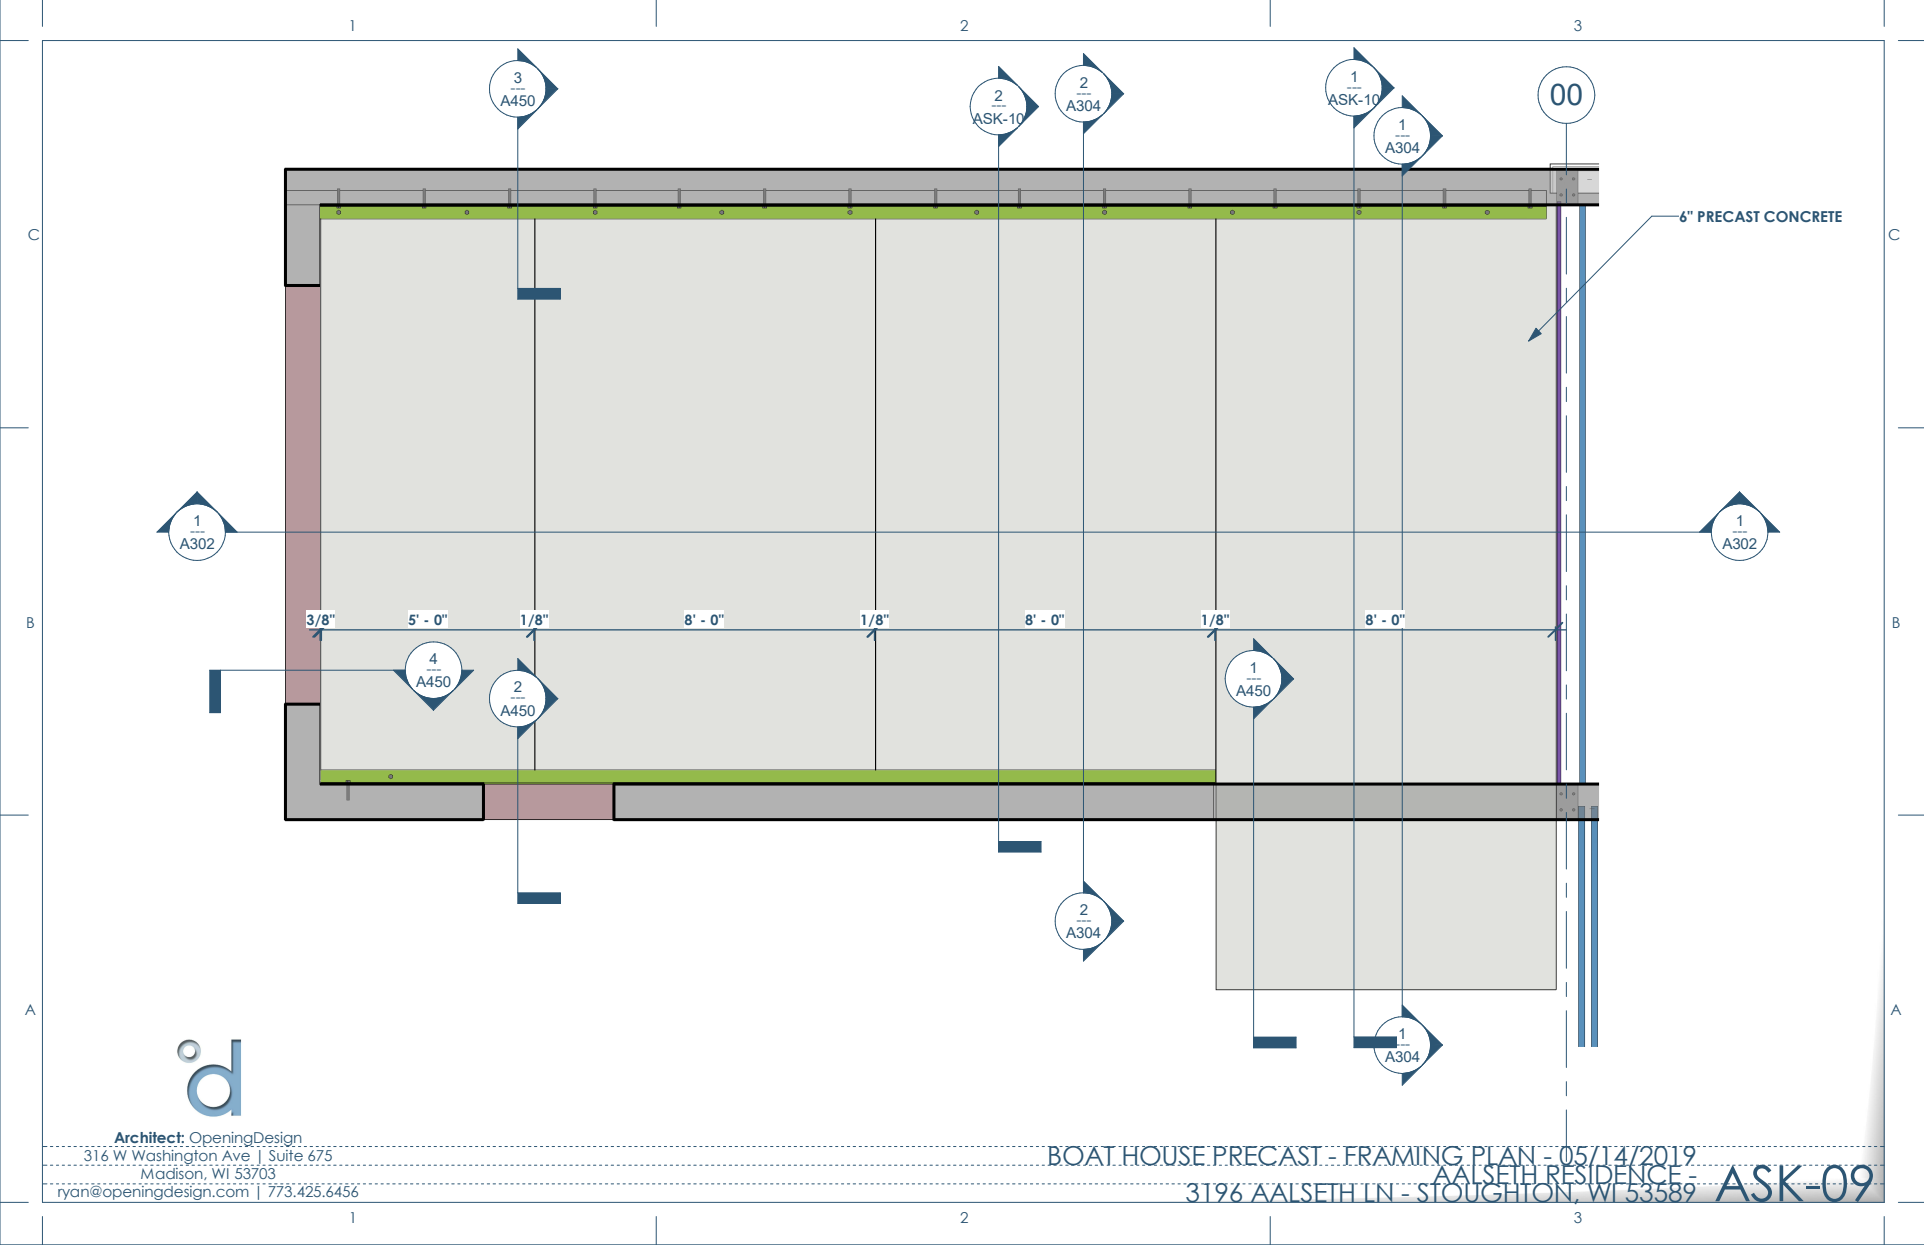
[picture p138: page 1]
ASK-10; 6" PRECAST CONCRETE; Madison, WI 53703; ryan@openingdesign.com | 773.425.6456; 3196 AALSETH LN - STOUGHTON, WI 53589 AALSETH RESIDENCE - BOAT HOUSE PRECAST - FRAMING PLAN - 05/14/2019 ASK-09

Architect: OpeningDesign
316 W Washington Ave | Suite 675

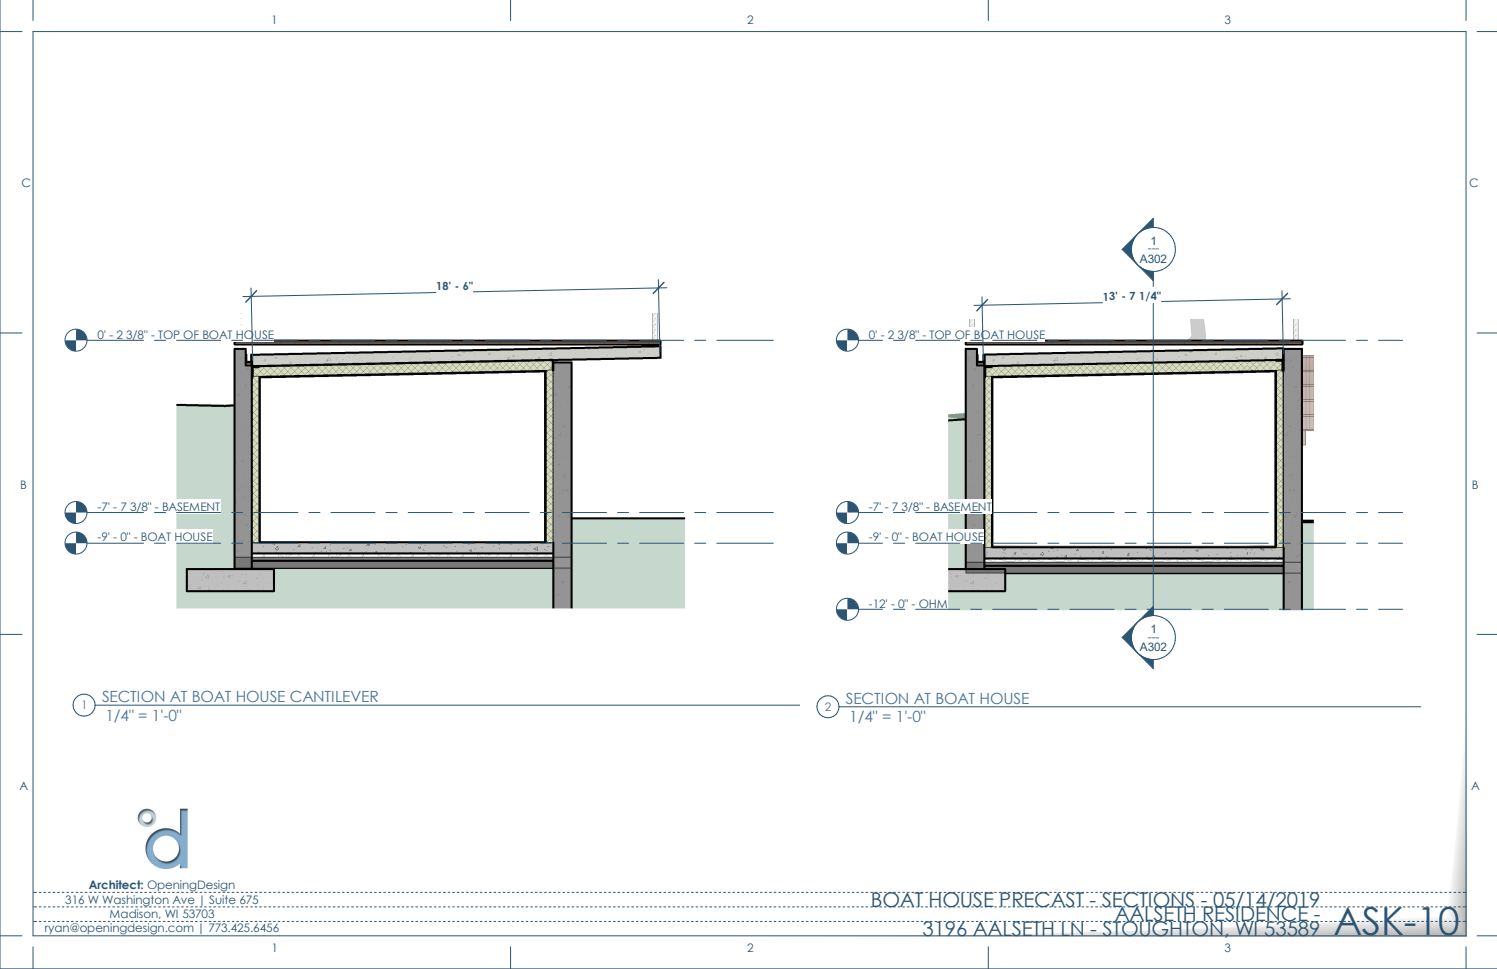
[picture p139: page 2]
-9' - 0" - BOAT HOUSE; -7' - 7 3/8" - BASEMENT; -12' - 0" - OHM; Madison, WI 53703; ryan@openingdesign.com | 773.425.6456; 3196 AALSETH LN - STOUGHTON, WI 53589 AALSETH RESIDENCE - BOAT HOUSE PRECAST - SECTIONS - 05/14/2019 ASK-10

0' - 2 3/8" - TOP OF BOAT HOUSE

SECTION AT BOAT HOUSE CANTILEVER

SECTION AT BOAT HOUSE

Architect: OpeningDesign
316 W Washington Ave | Suite 675
