OpeningDesign/Aalseth_Residence/Transfer/20190317 - from lumber yard - truss design/fwrevisedquoteforaalsethq17025b/Q17025B_detail#1.pdf

A2

A2

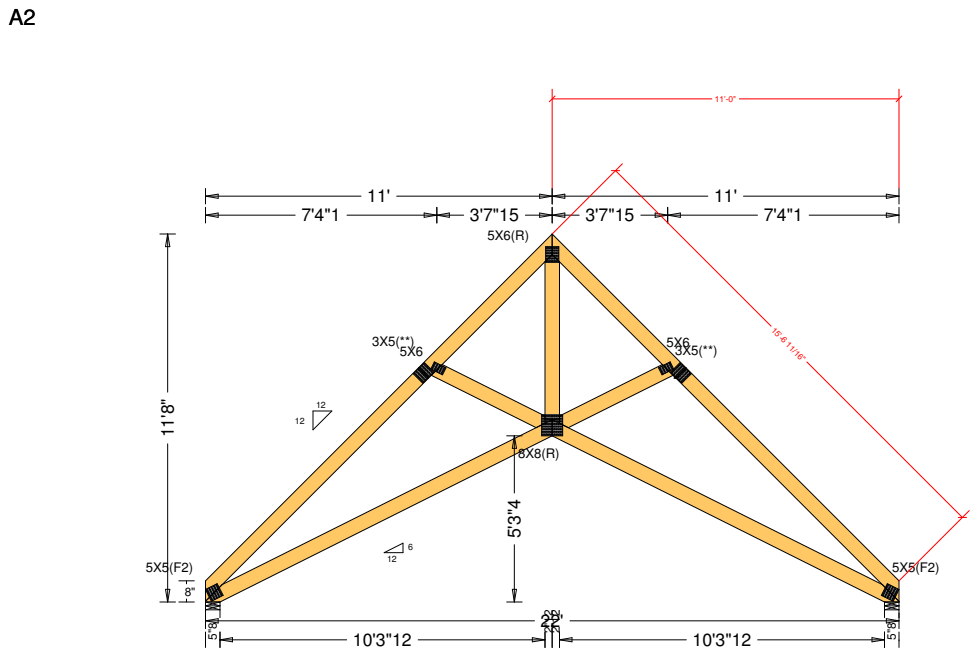
[picture p140: page 1]
