OpeningDesign/Aalseth_Residence/Transfer/20190317 - from lumber yard - truss design/fwrevisedquoteforaalsethq17025b/Q17025B_detail#2.pdf

## H1ARCH

## H1ARCH

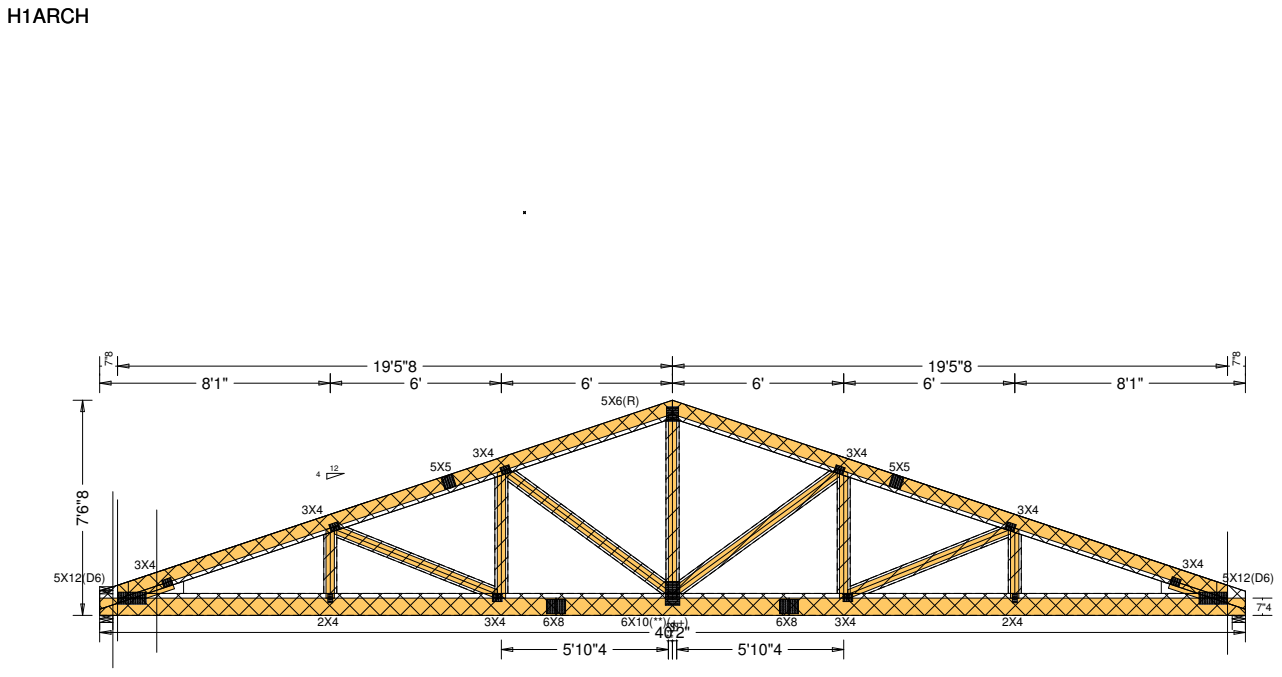
[picture p141: page 1]
