OpeningDesign/Aalseth_Residence/Transfer/20191110 - to framer - basement stairs/20191110 - 3196 Aalseth Lane - Basement Stairs.pdf

03

A300 --- 2

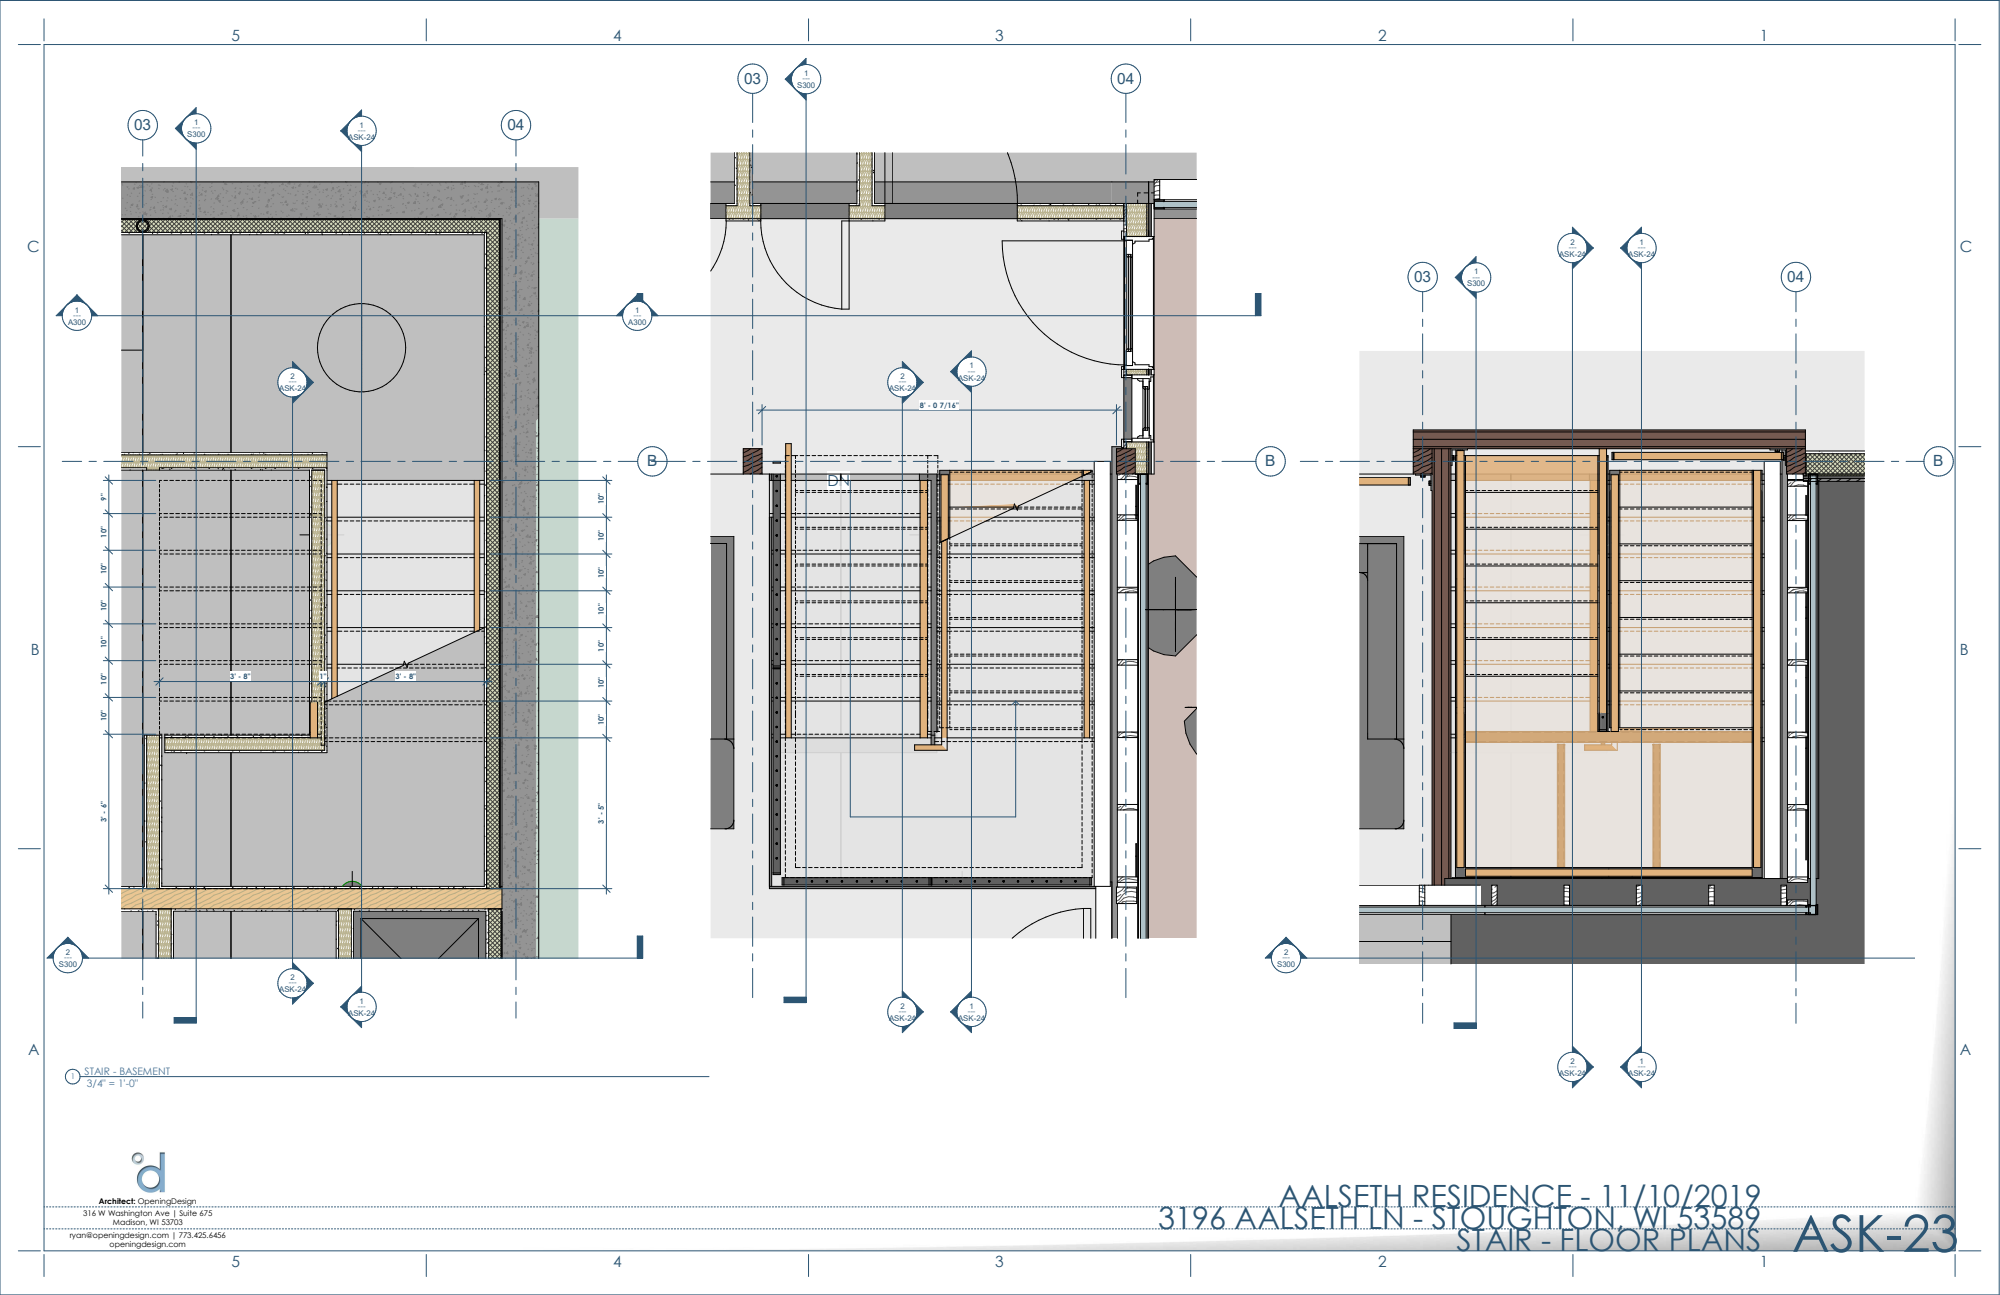
[picture p142: page 1]
04 ASK-24 ---1; ASK-24 ---¹ ASK-24 --- 2 ASK-24 ---² ASK-24 ---; 1 ASK-24 ---1; ASK-24 --- ² ASK-24 ---2 ASK-24 --- 5; ABC ABC; Madison, WI 53703; openingdesign.com; 3/4" = 1'-0" ¹ STAIR - BASEMENT

ASK-24 --- ² ASK-24 ---² ASK-24 ---

ASK-23 ³¹⁹⁶ AALSETH LN - STOUGHTON, WI 53589 STAIR - FLOOR PLANS AALSETH RESIDENCE - 11/10/2019

Architect: OpeningDesign
316 W Washington Ave | Suite 675

ryan@openingdesign.com | 773.425.6456

12' - 2 1/8" - 2ND FLOOR -7' - 7 3/8" - BASEMENT 0' - 2 3/8" - TOP OF BOAT HOUSE 1' - 6 5/8" - LR

B ²

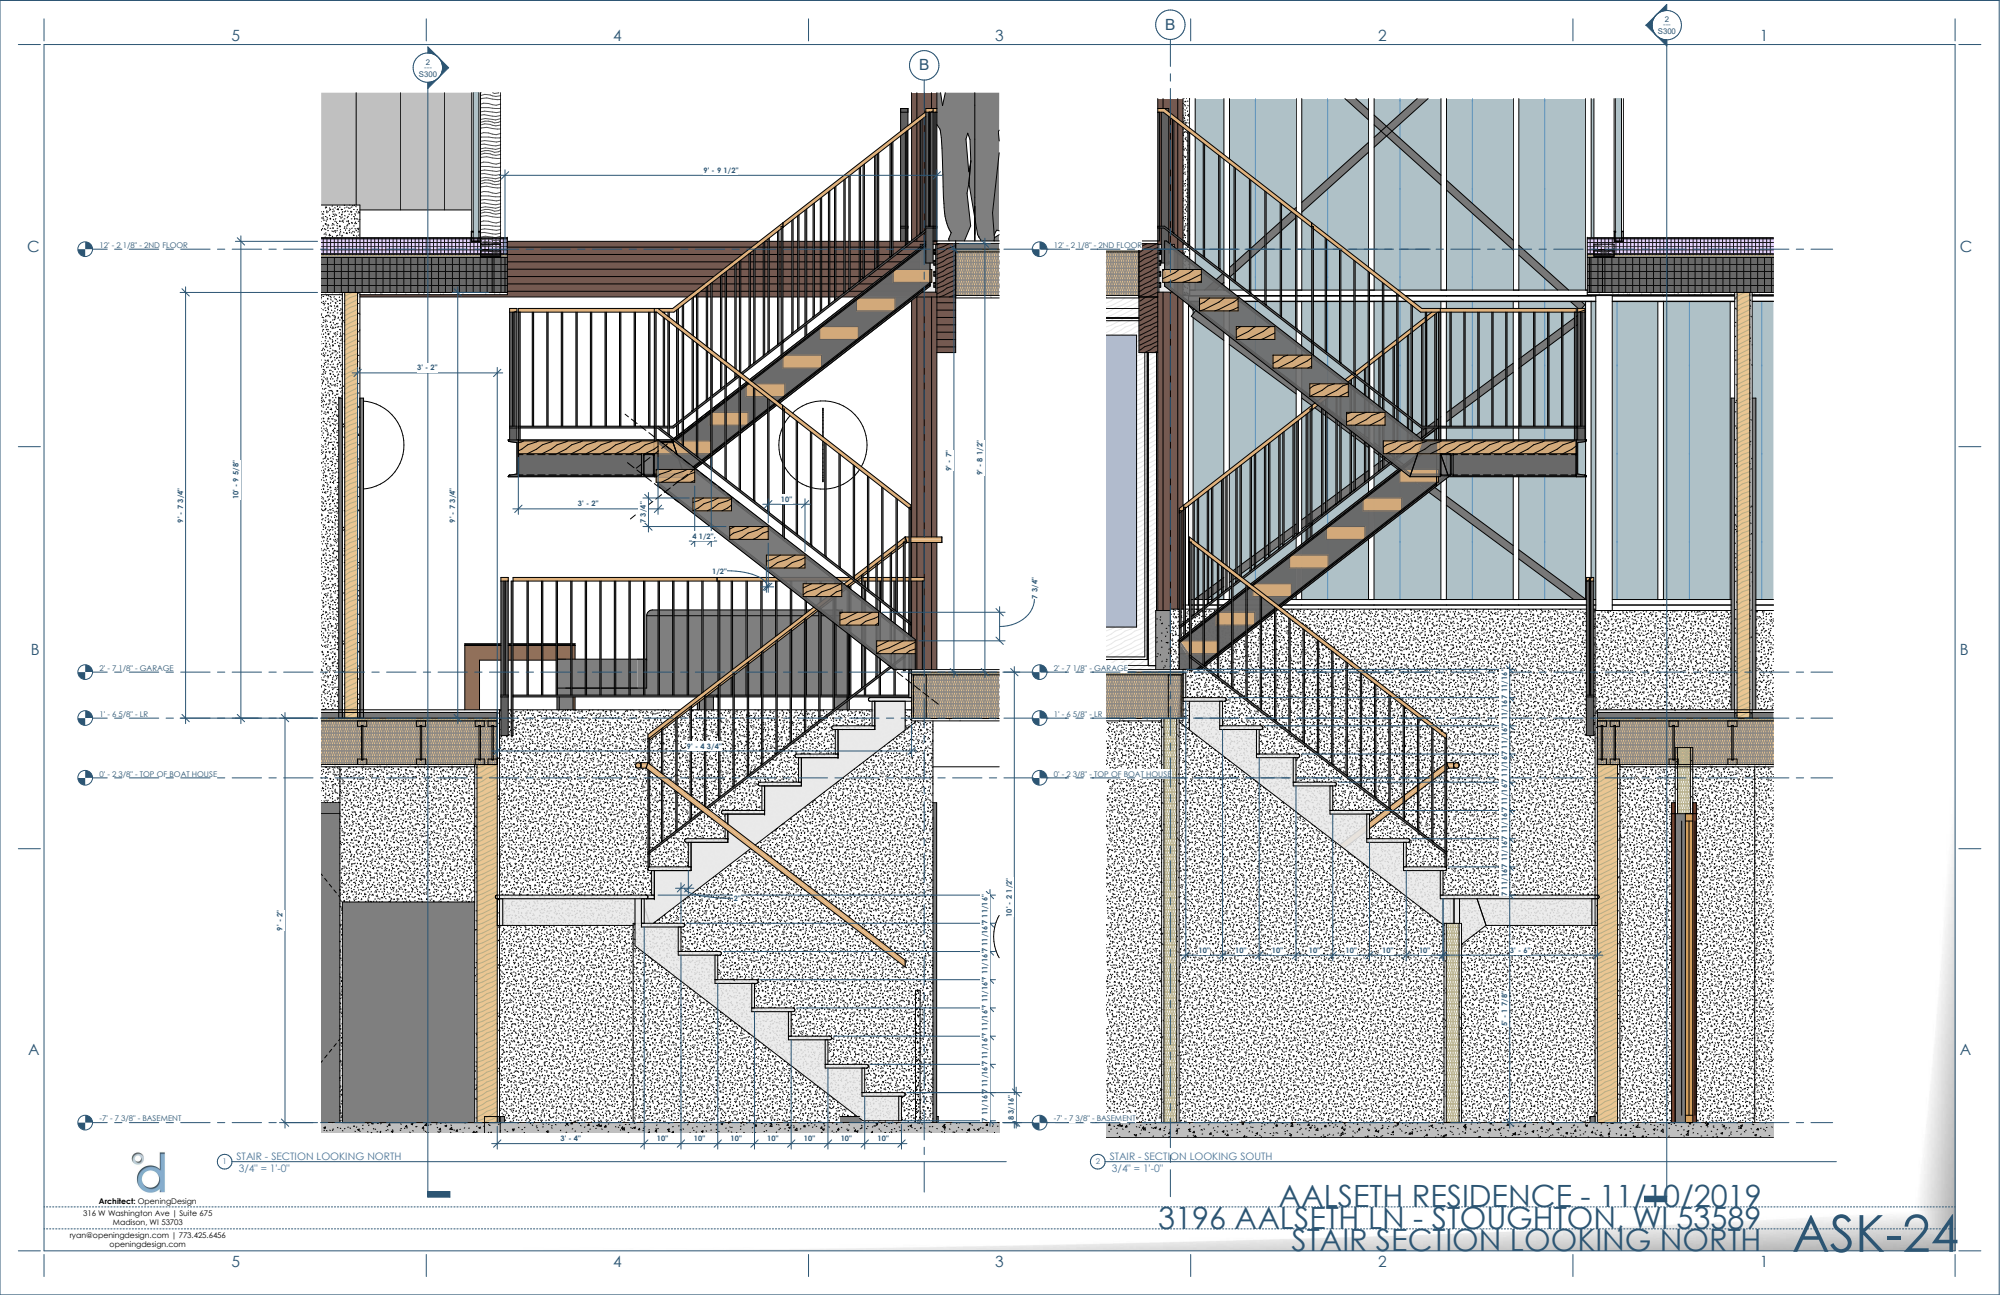
[picture p143: page 2]
2' - 7 1/8" - GARAGE; Madison, WI 53703; openingdesign.com; 3/4" = 1'-0" ¹ STAIR - SECTION LOOKING NORTH; 3/4" = 1'-0" ² STAIR - SECTION LOOKING SOUTH

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

ASK-24 ³¹⁹⁶ AALSETH LN - STOUGHTON, WI 53589 STAIR SECTION LOOKING NORTH AALSETH RESIDENCE - 11/10/2019

Architect: OpeningDesign
316 W Washington Ave | Suite 675

ryan@openingdesign.com | 773.425.6456
