OpeningDesign/Aalseth_Residence/Transfer/20191106 - to Flasher - details/20191106 - 3196 Aalseth Lane.pdf

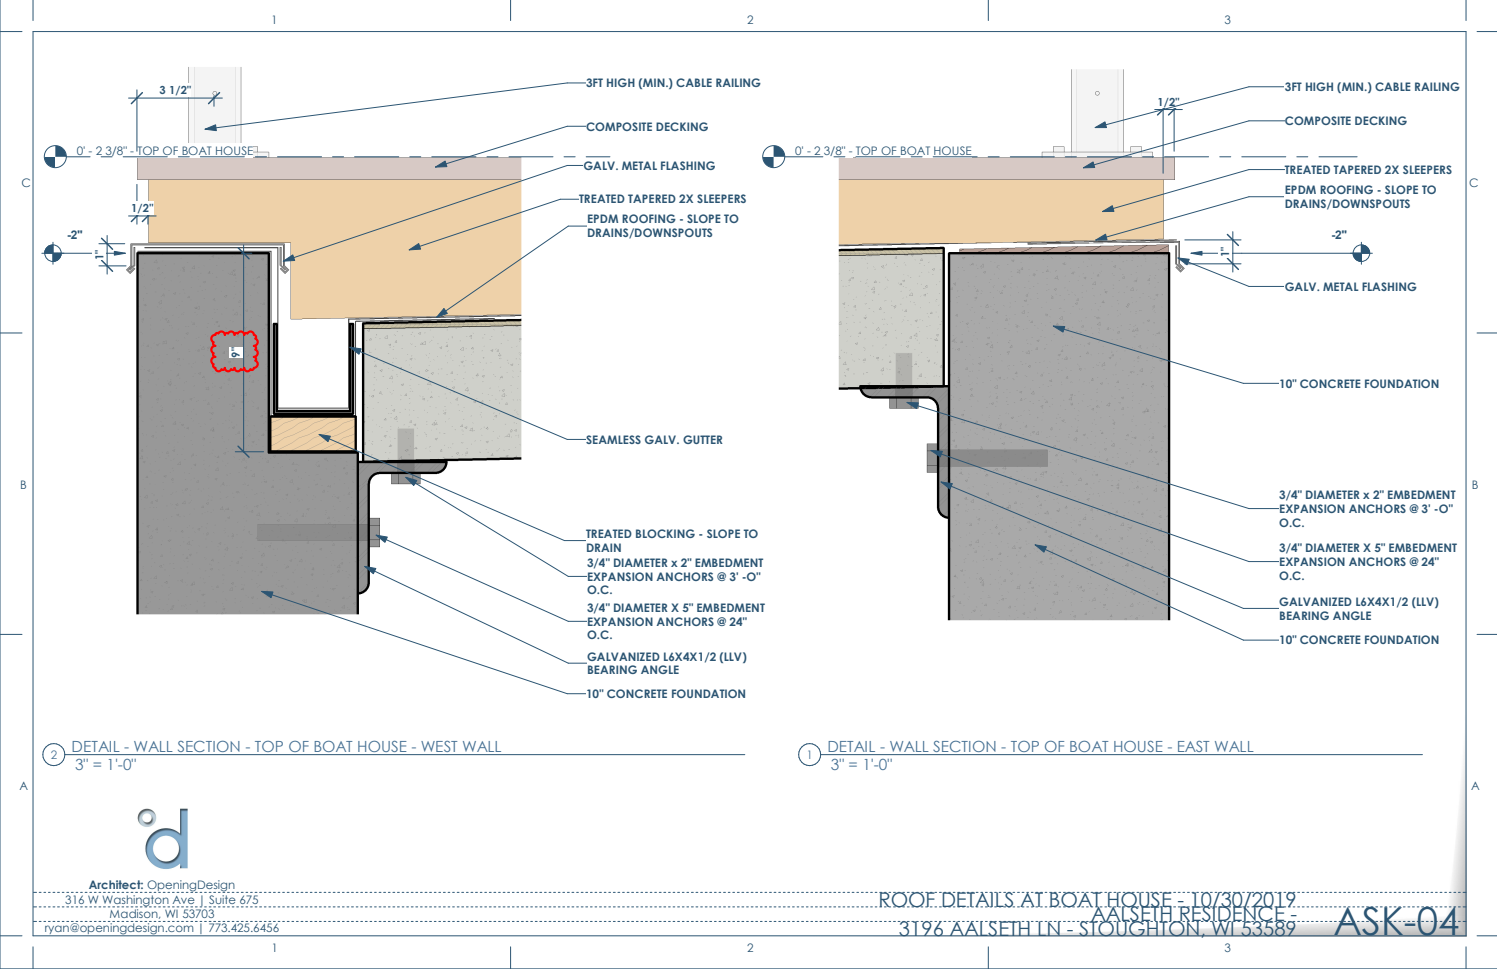
[picture p144: page 1]
COMPOSITE DECKING; 10" CONCRETE FOUNDATION; GALVANIZED L6X4X1/2 (LLV) BEARING ANGLE; 3/4" DIAMETER X 5" EMBEDMENT EXPANSION ANCHORS @ 24" O.C.; 3/4" DIAMETER x 2" EMBEDMENT EXPANSION ANCHORS @ 3' -O" O.C.; Madison, WI 53703; ryan@openingdesign.com | 773.425.6456; 3196 AALSETH LN - STOUGHTON, WI 53589 AALSETH RESIDENCE - ROOF DETAILS AT BOAT HOUSE - 10/30/2019; ASK-04

3FT HIGH (MIN.) CABLE RAILING

0' - 2 3/8" - TOP OF BOAT HOUSE9"

0' - 2 3/8" - TOP OF BOAT HOUSE

GALV. METAL FLASHING

TREATED TAPERED 2X SLEEPERS
EPDM ROOFING - SLOPE TO
DRAINS/DOWNSPOUTS

SEAMLESS GALV. GUTTER

TREATED BLOCKING - SLOPE TO
DRAIN
3/4" DIAMETER x 2" EMBEDMENT
EXPANSION ANCHORS @ 3' -O"
3/4" DIAMETER X 5" EMBEDMENT
EXPANSION ANCHORS @ 24"

DETAIL - WALL SECTION - TOP OF BOAT HOUSE - WEST WALL

DETAIL - WALL SECTION - TOP OF BOAT HOUSE - EAST WALL

Architect: OpeningDesign
316 W Washington Ave | Suite 675

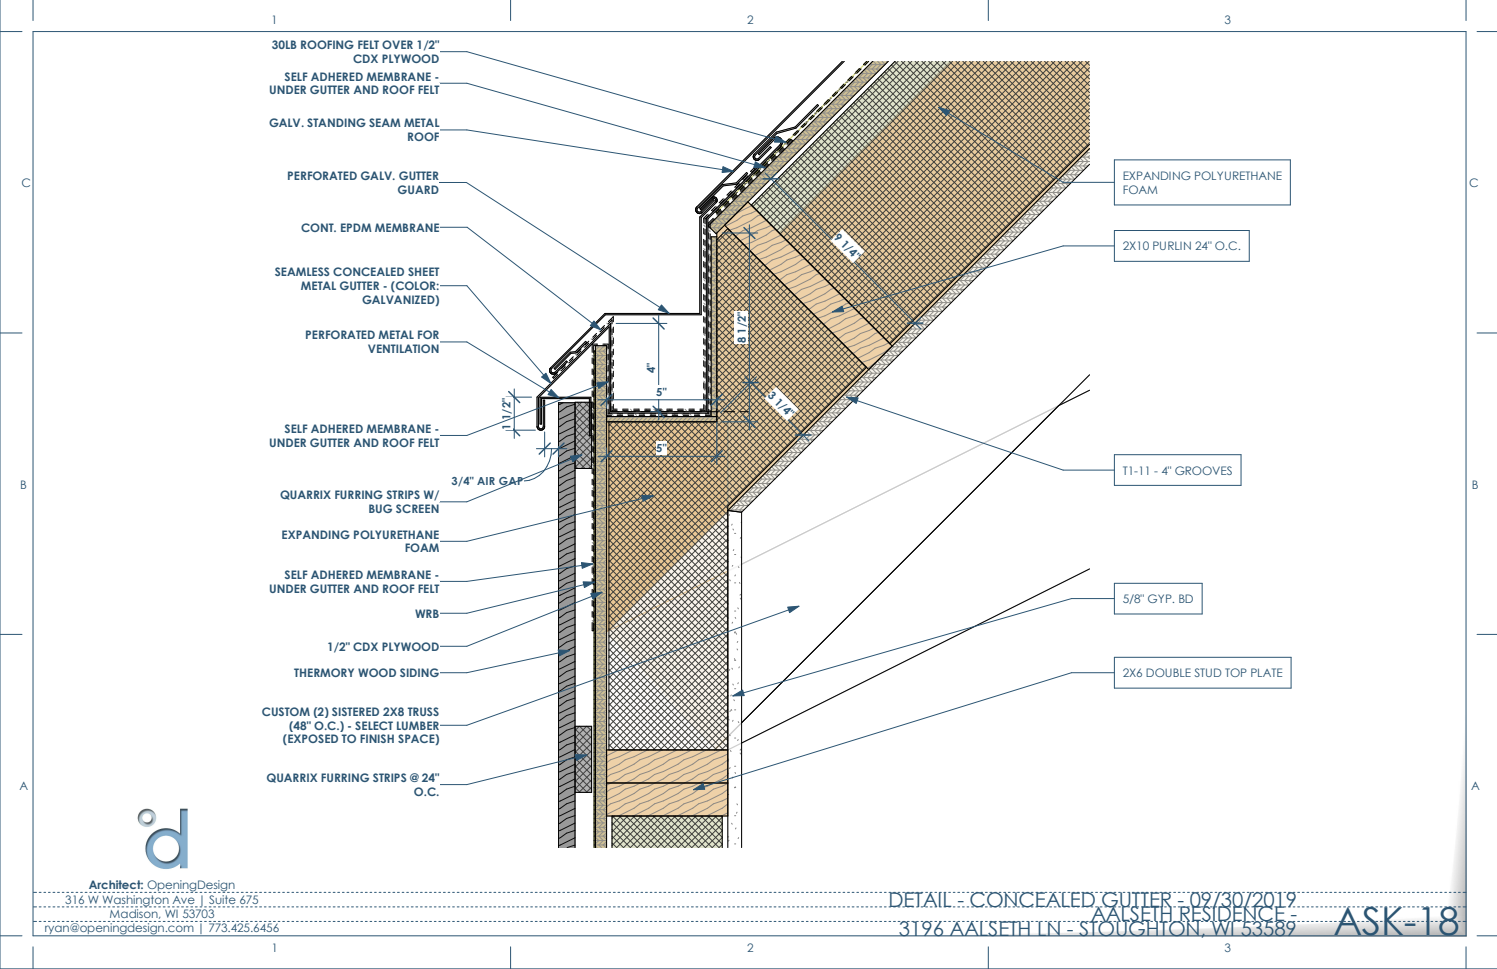
[picture p145: page 2]
3/4" AIR GAP; 1/2" CDX PLYWOOD; WRB; EXPANDING POLYURETHANE FOAM; BUG SCREEN; VENTILATION; GALVANIZED); GUARD; ROOF; CDX PLYWOOD; T1-11 - 4" GROOVES; 5/8" GYP. BD; 2X10 PURLIN 24" O.C.; EXPANDING POLYURETHANE FOAM C; Madison, WI 53703; ryan@openingdesign.com | 773.425.6456; 3196 AALSETH LN - STOUGHTON, WI 53589 AALSETH RESIDENCE - DETAIL - CONCEALED GUTTER - 09/30/2019; ASK-18

30LB ROOFING FELT OVER 1/2"

SELF ADHERED MEMBRANE -
UNDER GUTTER AND ROOF FELT

GALV. STANDING SEAM METAL

PERFORATED GALV. GUTTER

CONT. EPDM MEMBRANE

SEAMLESS CONCEALED SHEET
METAL GUTTER - (COLOR:

PERFORATED METAL FOR

QUARRIX FURRING STRIPS W/

THERMORY WOOD SIDING

2X6 DOUBLE STUD TOP PLATE

CUSTOM (2) SISTERED 2X8 TRUSS
(48" O.C.) - SELECT LUMBER
(EXPOSED TO FINISH SPACE)

QUARRIX FURRING STRIPS @ 24"

Architect: OpeningDesign
316 W Washington Ave | Suite 675

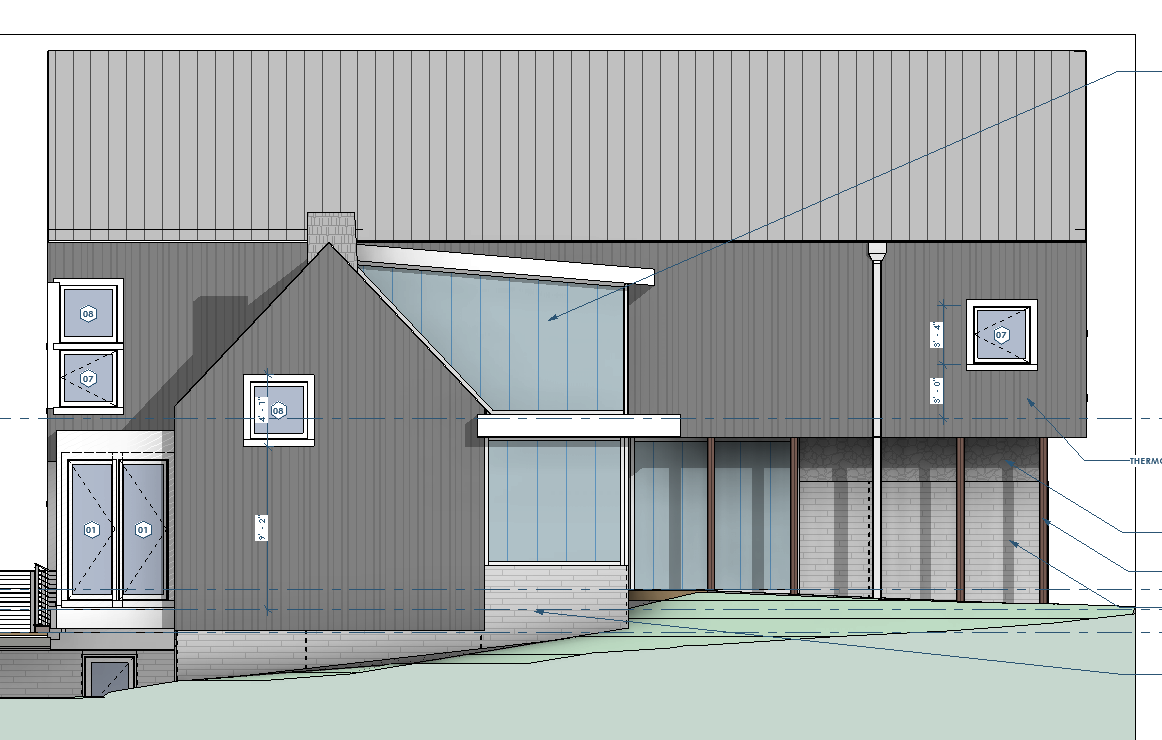
[picture p146: page 3]
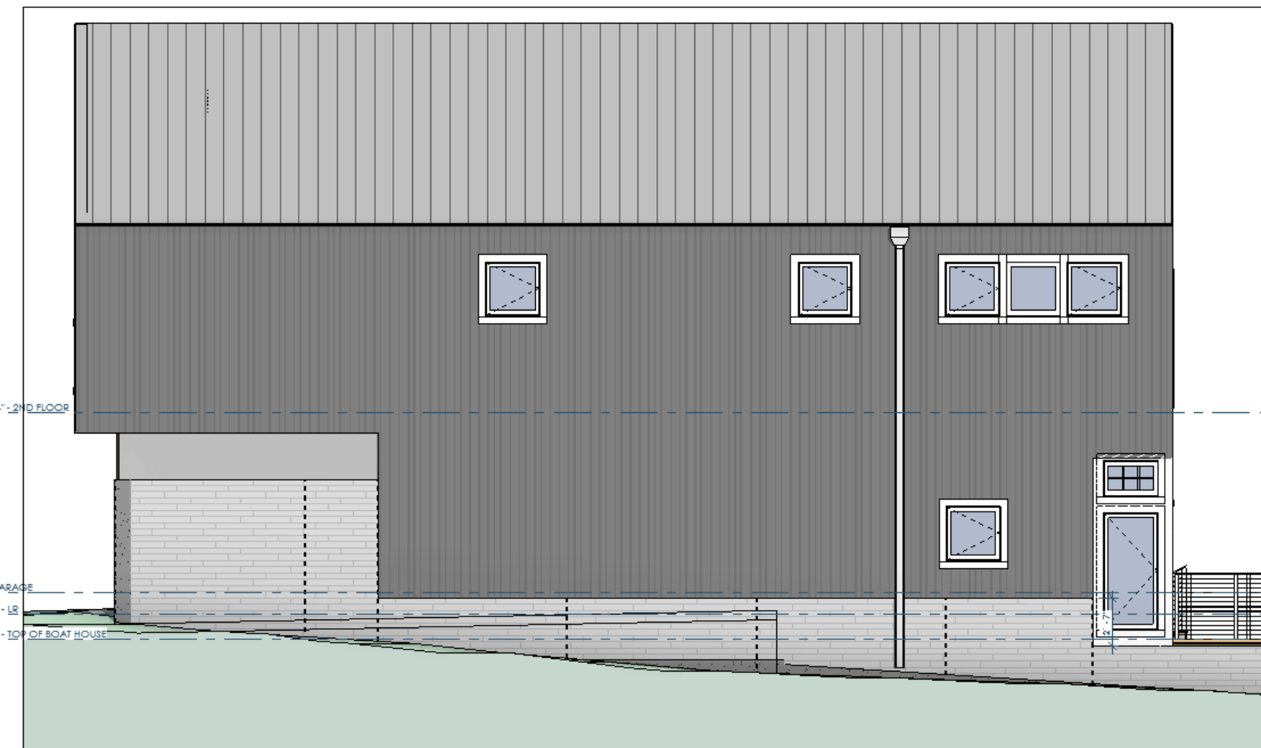
[picture p147: page 4]
