OpeningDesign/Aalseth_Residence/Transfer/20191006 - to plumber - layouts/3196 Aalseth Lane.pdf

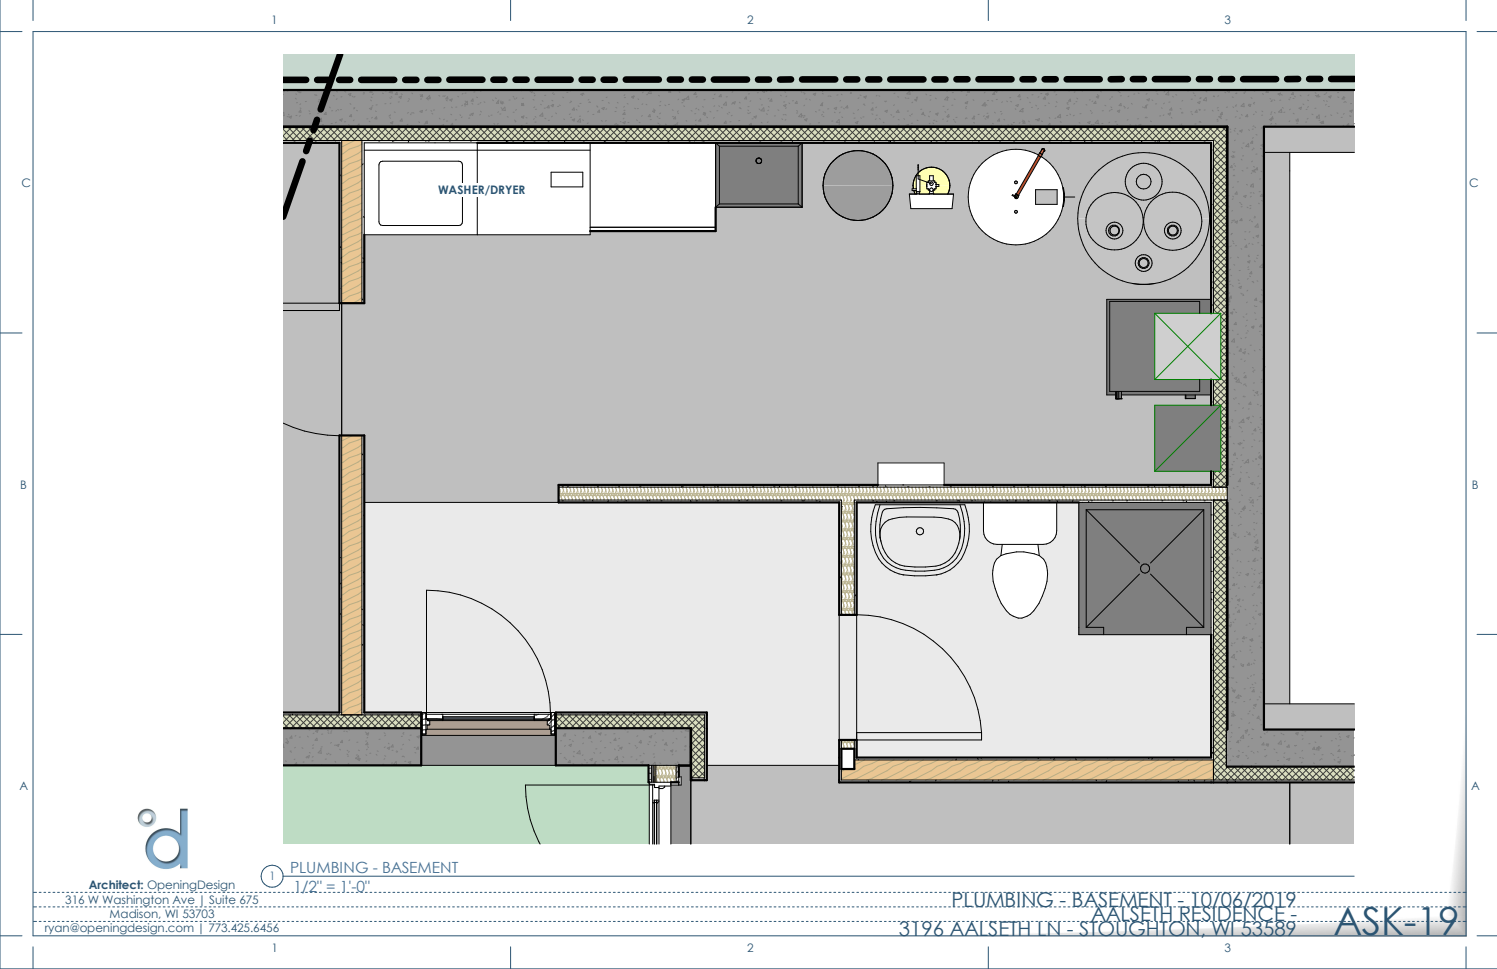
[picture p148: page 1]
WASHER/DRYER C; Madison, WI 53703; ryan@openingdesign.com | 773.425.6456; 3196 AALSETH LN - STOUGHTON, WI 53589 AALSETH RESIDENCE - PLUMBING - BASEMENT - 10/06/2019; ASK-19; PLUMBING - BASEMENT

Architect: OpeningDesign
316 W Washington Ave | Suite 675

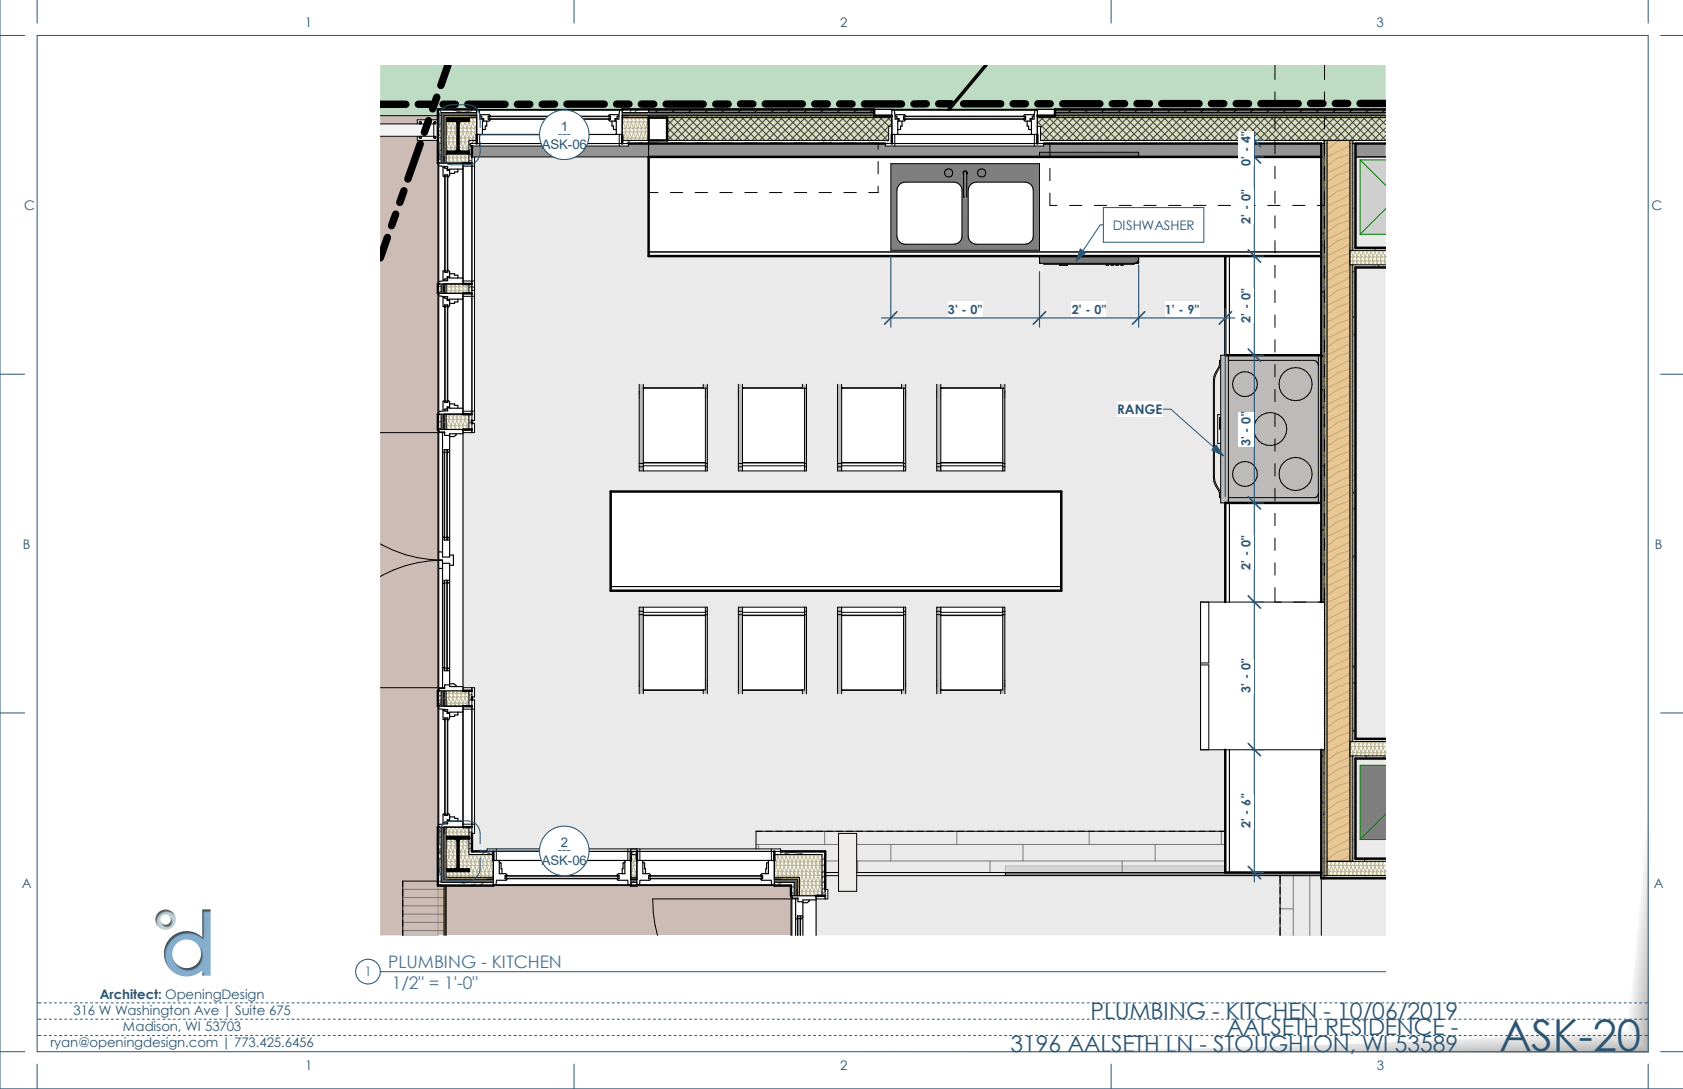
[picture p149: page 2]
--- ASK-06; DISHWASHER; RANGE; Architect: OpeningDesign; ryan@openingdesign.com | 773.425.6456; 3196 AALSETH LN - STOUGHTON, WI 53589 AALSETH RESIDENCE - PLUMBING - KITCHEN - 10/06/2019; ASK-20; PLUMBING - KITCHEN

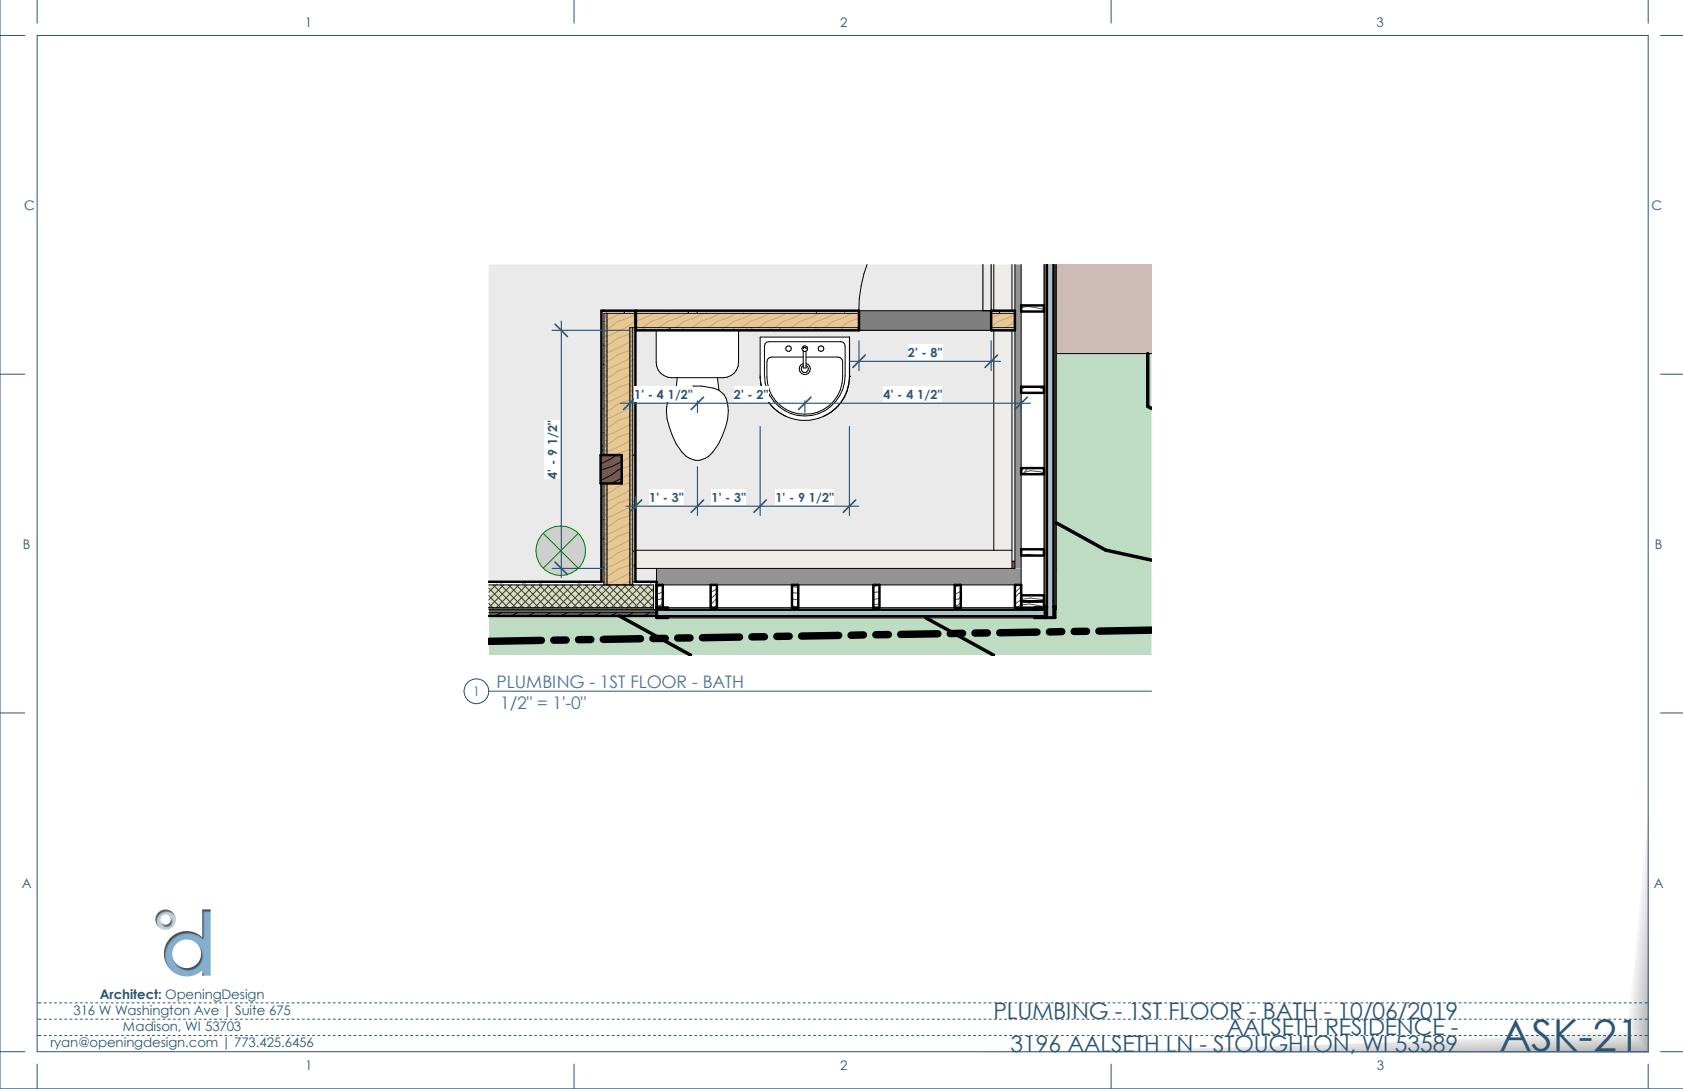
[picture p150: page 3]
Architect: OpeningDesign; ryan@openingdesign.com | 773.425.6456; 3196 AALSETH LN - STOUGHTON, WI 53589 AALSETH RESIDENCE - PLUMBING - 1ST FLOOR - BATH - 10/06/2019; ASK-21

PLUMBING - 1ST FLOOR - BATH

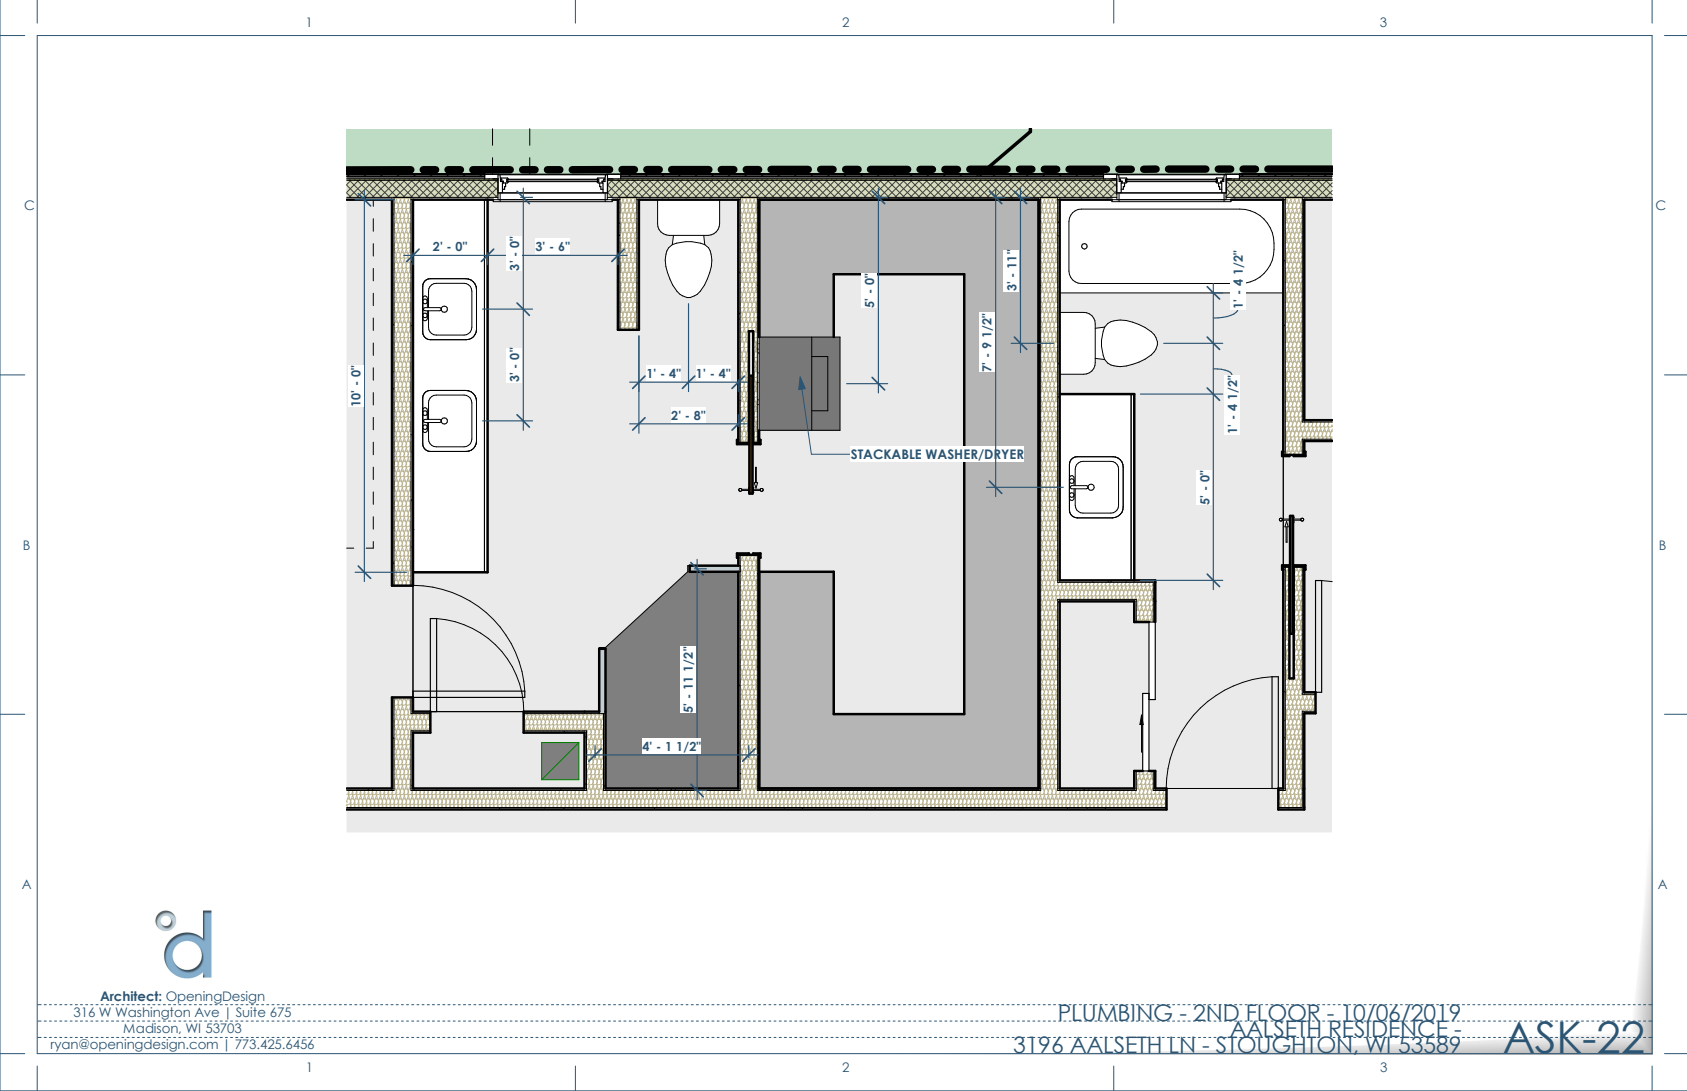
[picture p151: page 4]
Architect: OpeningDesign; ryan@openingdesign.com | 773.425.6456; 3196 AALSETH LN - STOUGHTON, WI 53589 AALSETH RESIDENCE - PLUMBING - 2ND FLOOR - 10/06/2019; ASK-22

STACKABLE WASHER/DRYER
