OpeningDesign/Aalseth_Residence/Transfer/20190820 - to framer - framing plans/20190820 - 3196 Aalseth Lane - Framing Plans.pdf

02

03

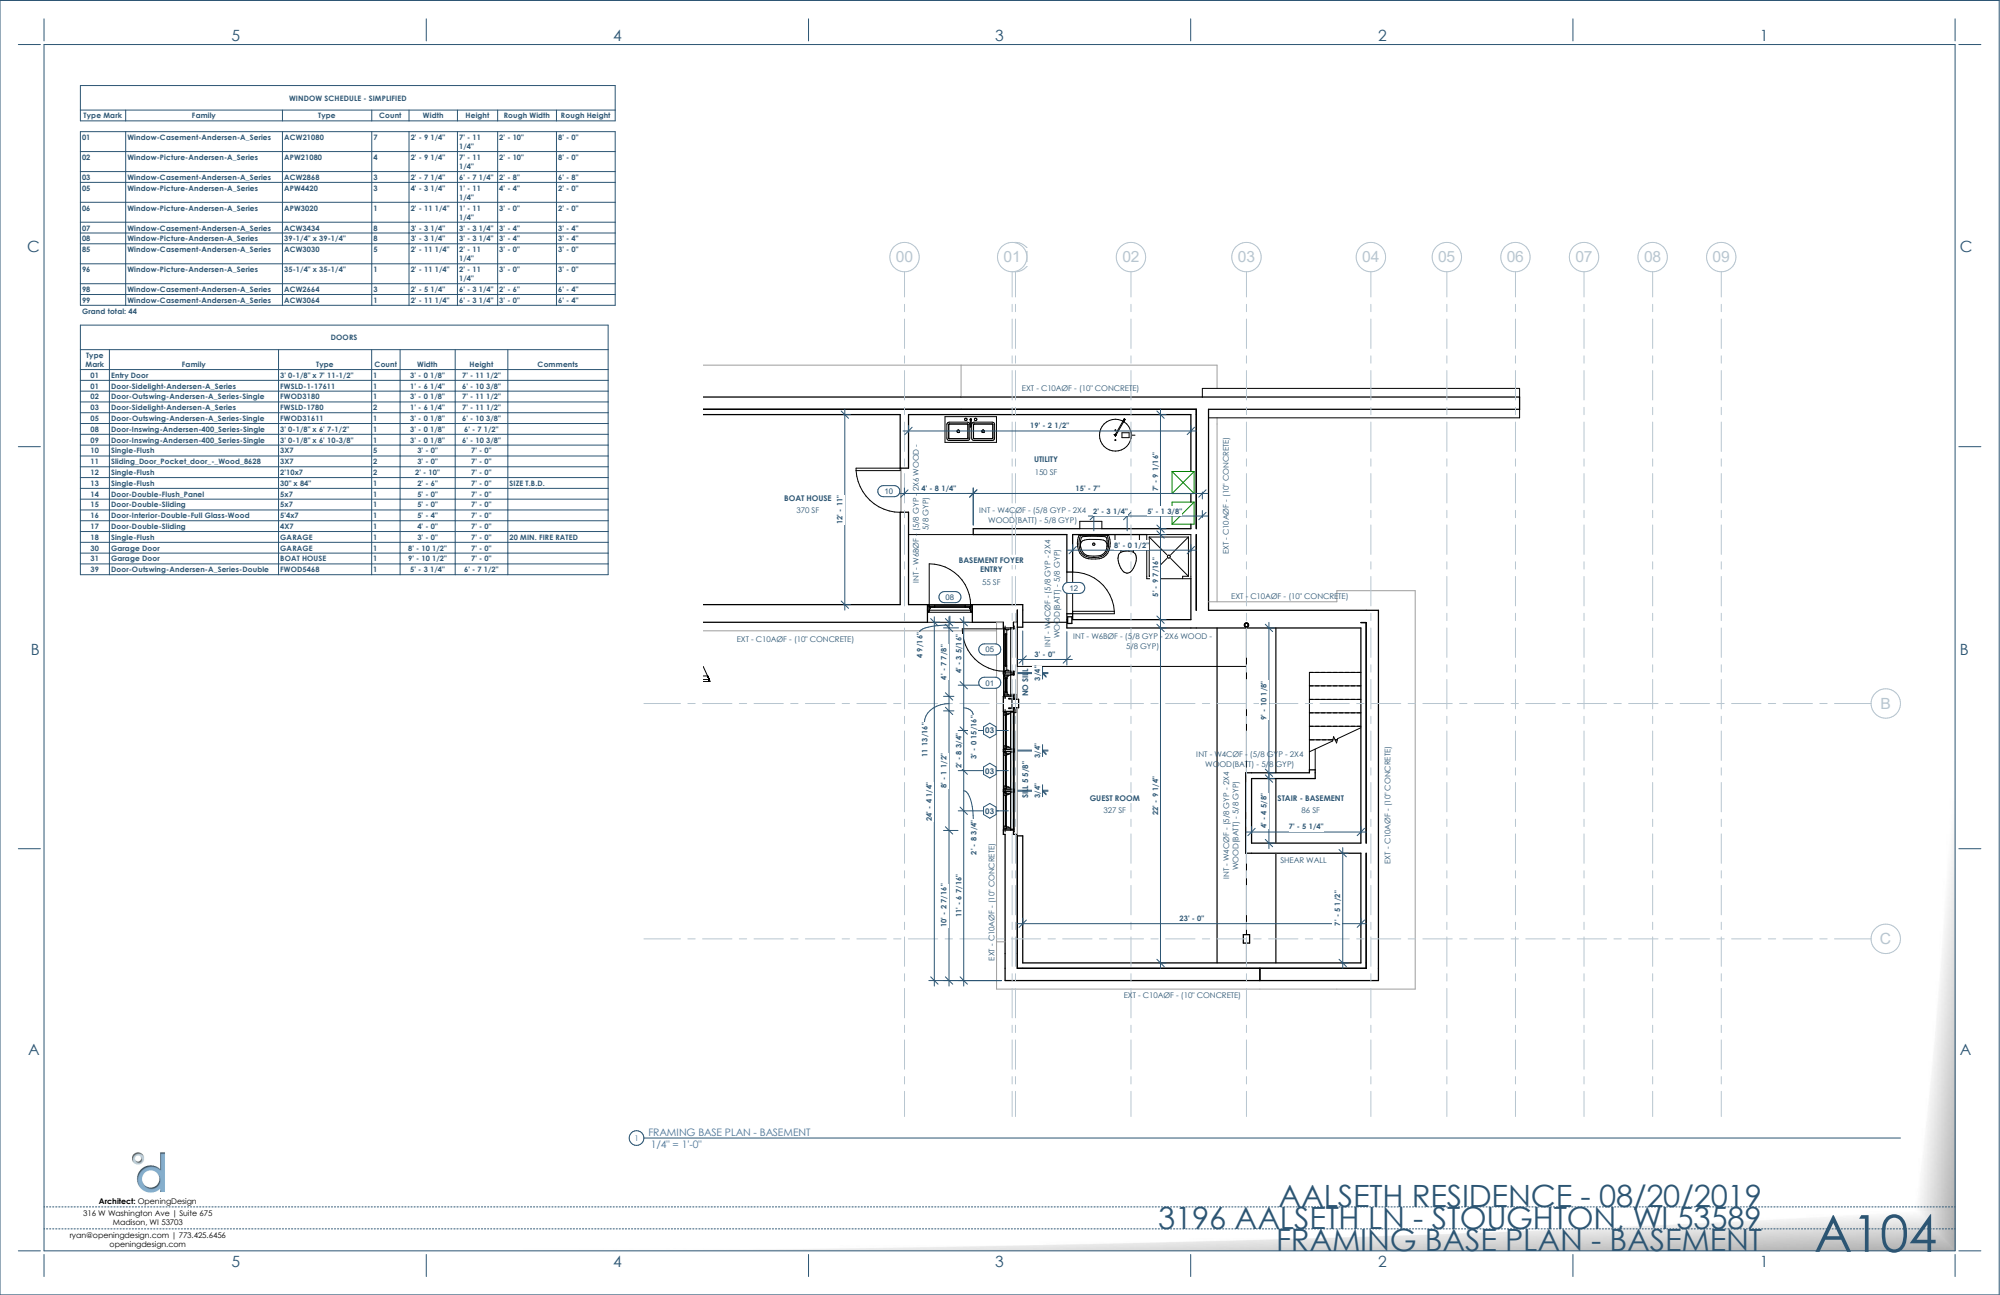
[picture p152: page 1]
BOAT HOUSE; UTILITY; BASEMENT FOYER ENTRY; GUEST ROOM; STAIR - BASEMENT; 5/8 GYP); INT - W4CØF - (5/8 GYP - 2X4; EXT - C10AØF - (10" CONCRETE); Madison, WI 53703; openingdesign.com; Type Mark; Family; Type; Count; Width; Height; Rough Width; Rough Height; Grand total: 44; DOORS

WINDOW SCHEDULE - SIMPLIFIED

01 | Window-Casement-Andersen-A_Series | ACW21080 | 7 | 2' - 9 1/4" | 7' - 11 1/4" | 2' - 10" | 8' - 0"

02 | Window-Picture-Andersen-A_Series | APW21080 | 4 | 2' - 9 1/4" | 7' - 11 1/4" | 2' - 10" | 8' - 0"

03 | Window-Casement-Andersen-A_Series | ACW2868 | 3 | 2' - 7 1/4" | 6' - 7 1/4" | 2' - 8" | 6' - 8"
05 | Window-Picture-Andersen-A_Series | APW4420 | 3 | 4' - 3 1/4" | 1' - 11 1/4" | 4' - 4" | 2' - 0"

06 | Window-Picture-Andersen-A_Series | APW3020 | 1 | 2' - 11 1/4" | 1' - 11 1/4" | 3' - 0" | 2' - 0"

07 | Window-Casement-Andersen-A_Series | ACW3434 | 8 | 3' - 3 1/4" | 3' - 3 1/4" | 3' - 4" | 3' - 4"
08 | Window-Picture-Andersen-A_Series | 39-1/4" x 39-1/4" | 8 | 3' - 3 1/4" | 3' - 3 1/4" | 3' - 4" | 3' - 4"
85 | Window-Casement-Andersen-A_Series | ACW3030 | 5 | 2' - 11 1/4" | 2' - 11 1/4" | 3' - 0" | 3' - 0"

96 | Window-Picture-Andersen-A_Series | 35-1/4" x 35-1/4" | 1 | 2' - 11 1/4" | 2' - 11 1/4" | 3' - 0" | 3' - 0"

98 | Window-Casement-Andersen-A_Series | ACW2664 | 3 | 2' - 5 1/4" | 6' - 3 1/4" | 2' - 6" | 6' - 4"
99 | Window-Casement-Andersen-A_Series | ACW3064 | 1 | 2' - 11 1/4" | 6' - 3 1/4" | 3' - 0" | 6' - 4"

Type Mark | Family | Type | Count | Width | Height | Comments

01 | Entry Door | 3' 0-1/8" x 7' 11-1/2" | 1 | 3' - 0 1/8" | 7' - 11 1/2"
01 | Door-Sidelight-Andersen-A_Series | FWSLD-1-17611 | 1 | 1' - 6 1/4" | 6' - 10 3/8"
02 | Door-Outswing-Andersen-A_Series-Single | FWOD3180 | 1 | 3' - 0 1/8" | 7' - 11 1/2"
03 | Door-Sidelight-Andersen-A_Series | FWSLD-1780 | 2 | 1' - 6 1/4" | 7' - 11 1/2"
05 | Door-Outswing-Andersen-A_Series-Single | FWOD31611 | 1 | 3' - 0 1/8" | 6' - 10 3/8"
08 | Door-Inswing-Andersen-400_Series-Single | 3' 0-1/8" x 6' 7-1/2" | 1 | 3' - 0 1/8" | 6' - 7 1/2"
09 | Door-Inswing-Andersen-400_Series-Single | 3' 0-1/8" x 6' 10-3/8" | 1 | 3' - 0 1/8" | 6' - 10 3/8"
10 | Single-Flush | 3X7 | 5 | 3' - 0" | 7' - 0"
11 | Sliding_Door_Pocket_door_-_Wood_8628 | 3X7 | 2 | 3' - 0" | 7' - 0"
12 | Single-Flush | 2'10x7 | 2 | 2' - 10" | 7' - 0"
13 | Single-Flush | 30" x 84" | 1 | 2' - 6" | 7' - 0" | SIZE T.B.D.
14 | Door-Double-Flush_Panel | 5x7 | 1 | 5' - 0" | 7' - 0"
15 | Door-Double-Sliding | 5x7 | 1 | 5' - 0" | 7' - 0"
16 | Door-Interior-Double-Full Glass-Wood | 5'4x7 | 1 | 5' - 4" | 7' - 0"
17 | Door-Double-Sliding | 4X7 | 1 | 4' - 0" | 7' - 0"
18 | Single-Flush | GARAGE | 1 | 3' - 0" | 7' - 0" | 20 MIN. FIRE RATED
30 | Garage Door | GARAGE | 1 | 8' - 10 1/2" | 7' - 0"
31 | Garage Door | BOAT HOUSE | 1 | 9' - 10 1/2" | 7' - 0"
39 | Door-Outswing-Andersen-A_Series-Double | FWOD5468 | 1 | 5' - 3 1/4" | 6' - 7 1/2"

INT - W6BØF - (5/8 GYP - 2X6 WOOD -

INT - W4CØF - (5/8 GYP - 2X4
WOOD(BATT) - 5/8 GYP)

WOOD(BATT) - 5/8 GYP) EXT - C10AØF - (10" CONCRETE)

SILL 5 5/8" NO SILL

SHEAR WALL

1/4" = 1'-0" ¹ FRAMING BASE PLAN - BASEMENT

A104 ³¹⁹⁶ AALSETH LN - STOUGHTON, WI 53589 FRAMING BASE PLAN - BASEMENT AALSETH RESIDENCE - 08/20/2019

Architect: OpeningDesign
316 W Washington Ave | Suite 675

ryan@openingdesign.com | 773.425.6456

02

03

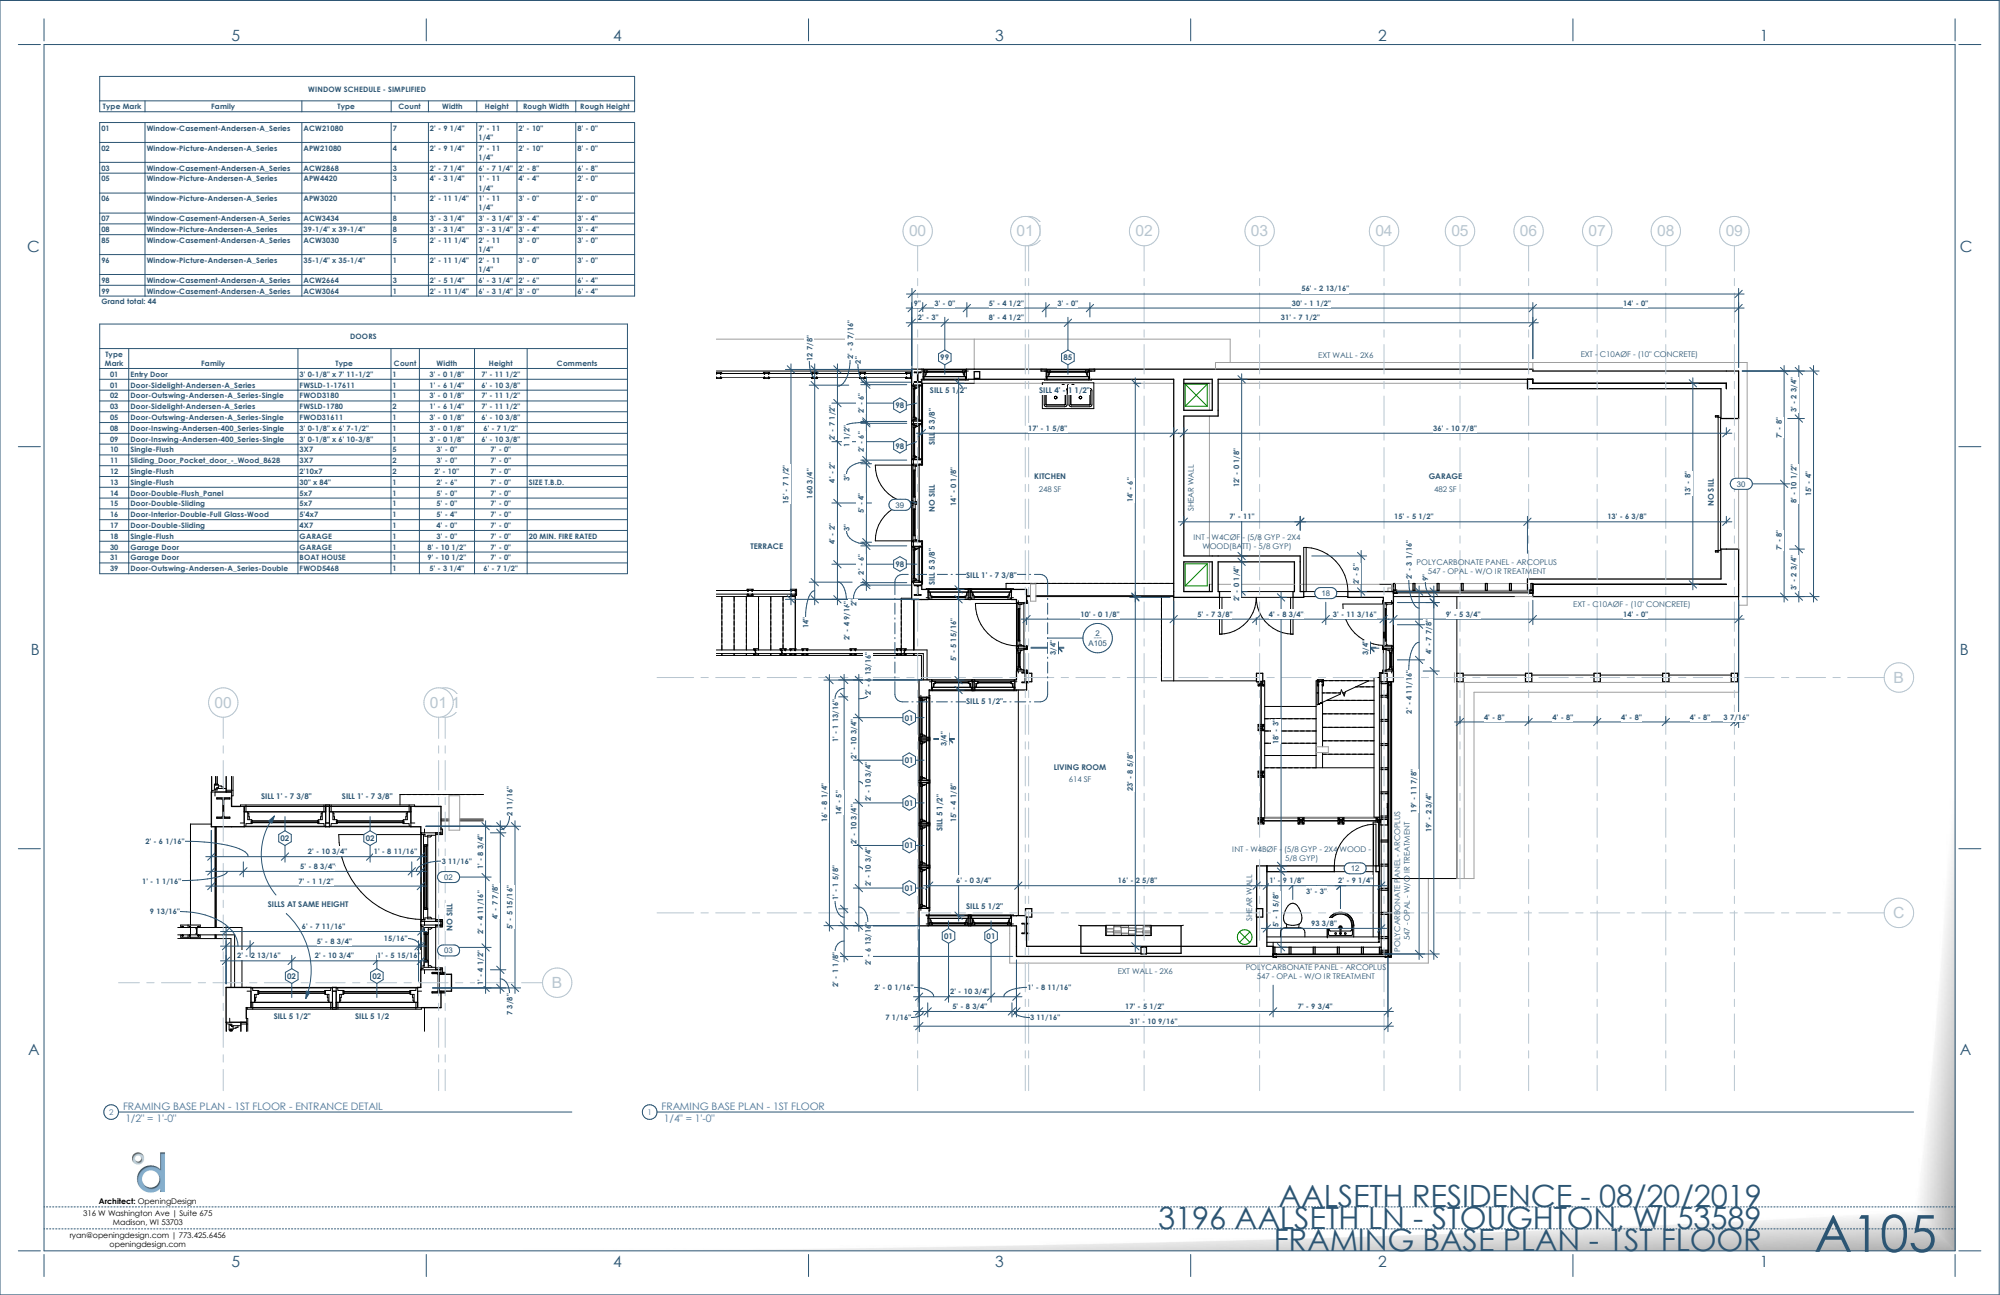
[picture p153: page 2]
EXT WALL - 2X6; EXT - C10AØF - (10" CONCRETE) EXT - C10AØF - (10" CONCRETE) POLYCARBONATE PANEL - ARCOPLUS 547 - OPAL - W/O IR TREATMENT; SHEAR WALL; POLYCARBONATE PANEL - ARCOPLUS 547 - OPAL - W/O IR TREATMENT; 5/8 GYP); SILL 5 1/2"; SILL 4' - 1 1/2"; SILL 1' - 7 3/8"; NO SILL; GARAGE; KITCHEN; LIVING ROOM; SILL 5 1/2; Type Mark; Family; Type; Count; Width; Height; Rough Width; Rough Height; Window-Casement-Andersen-A_Series; ACW21080; Window-Picture-Andersen-A_Series; APW21080; ACW2868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

SILL 5 3/8" SILL 5 3/8" NO SILL

INT - W4CØF - (5/8 GYP - 2X4
WOOD(BATT) - 5/8 GYP)

POLYCARBONATE PANEL - ARCOPLUS

547 - OPAL - W/O IR TREATMENT

INT - W4BØF - (5/8 GYP - 2X4 WOOD -

SILLS AT SAME HEIGHT

1/4" = 1'-0" ¹ FRAMING BASE PLAN - 1ST FLOOR 1/2" = 1'-0" ² FRAMING BASE PLAN - 1ST FLOOR - ENTRANCE DETAIL

A105 ³¹⁹⁶ AALSETH LN - STOUGHTON, WI 53589 FRAMING BASE PLAN - 1ST FLOOR AALSETH RESIDENCE - 08/20/2019

02

03

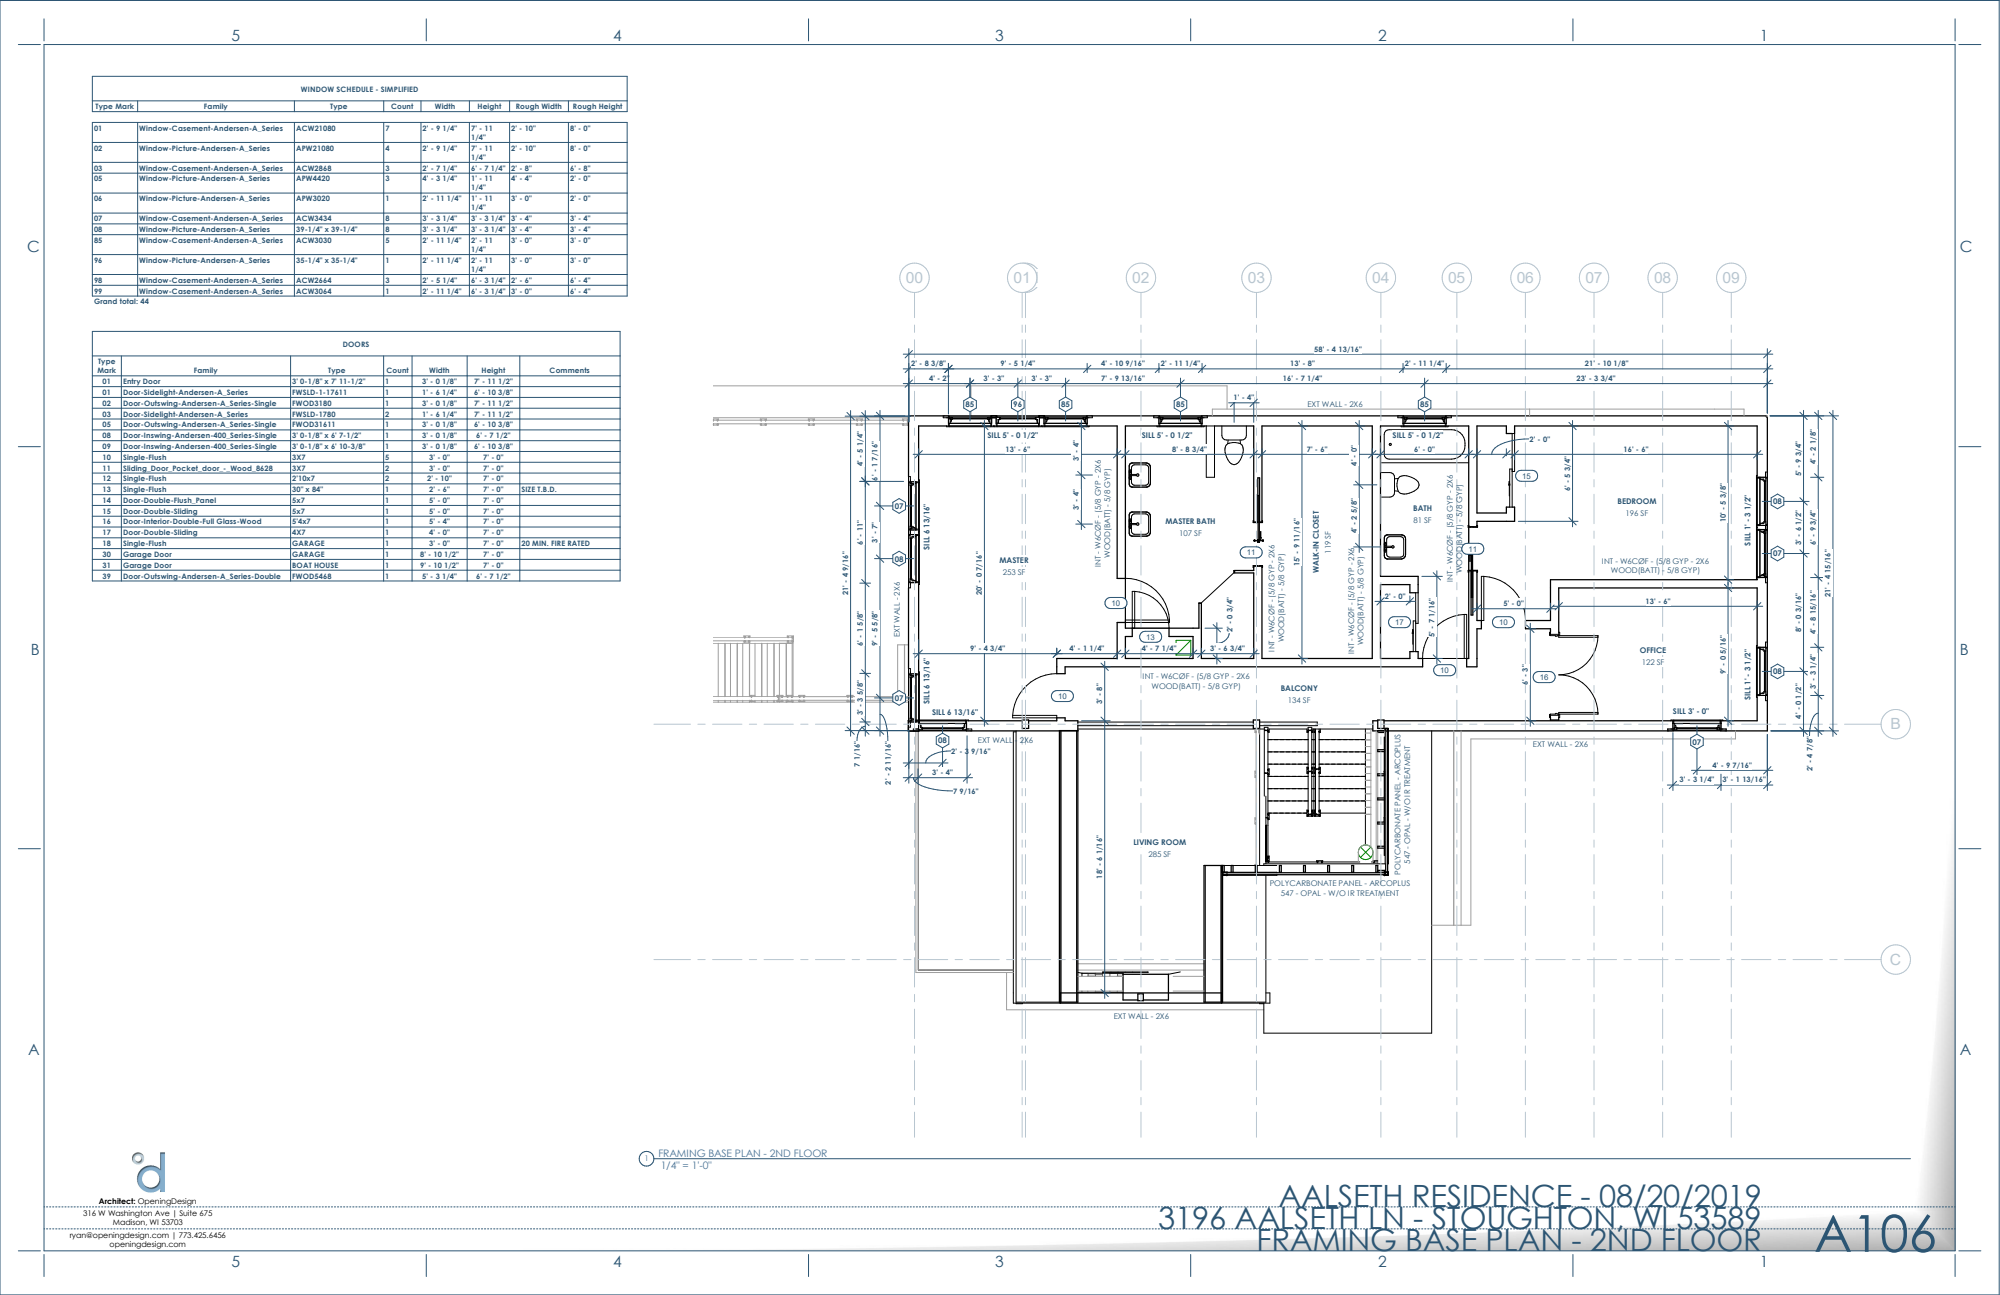
[picture p154: page 3]
EXT WALL - 2X6; INT - W6CØF - (5/8 GYP - 2X6; SILL 5' - 0 1/2"; SILL 6 13/16"; SILL 6 13/16" SILL 6 13/16"; SILL 1'; - 3 1/2" SILL 1' - 3 1/2"; SILL 3' - 0"; BEDROOM; OFFICE; MASTER BATH; MASTER; WALK; BATH; BALCONY; LIVING ROOM; Window-Casement-Andersen-A_Series; ACW21080; Window-Picture-Andersen-A_Series; APW21080; ACW2868; APW4420; APW3020; ACW3434; ACW3030; ACW2664; ACW3064; Grand total: 44; DOORS; Type; Mark; Family; Count; Width; Height; Comments; Entry Door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

WOOD(BATT) - 5/8 GYP)

-IN CLOSET 81 SF

INT - W6CØF - (5/8 GYP - 2X6

POLYCARBONATE PANEL - ARCOPLUS

547 - OPAL - W/O IR TREATMENT

1/4" = 1'-0" ¹ FRAMING BASE PLAN - 2ND FLOOR

A106 ³¹⁹⁶ AALSETH LN - STOUGHTON, WI 53589 FRAMING BASE PLAN - 2ND FLOOR AALSETH RESIDENCE - 08/20/2019

B | C
C | B

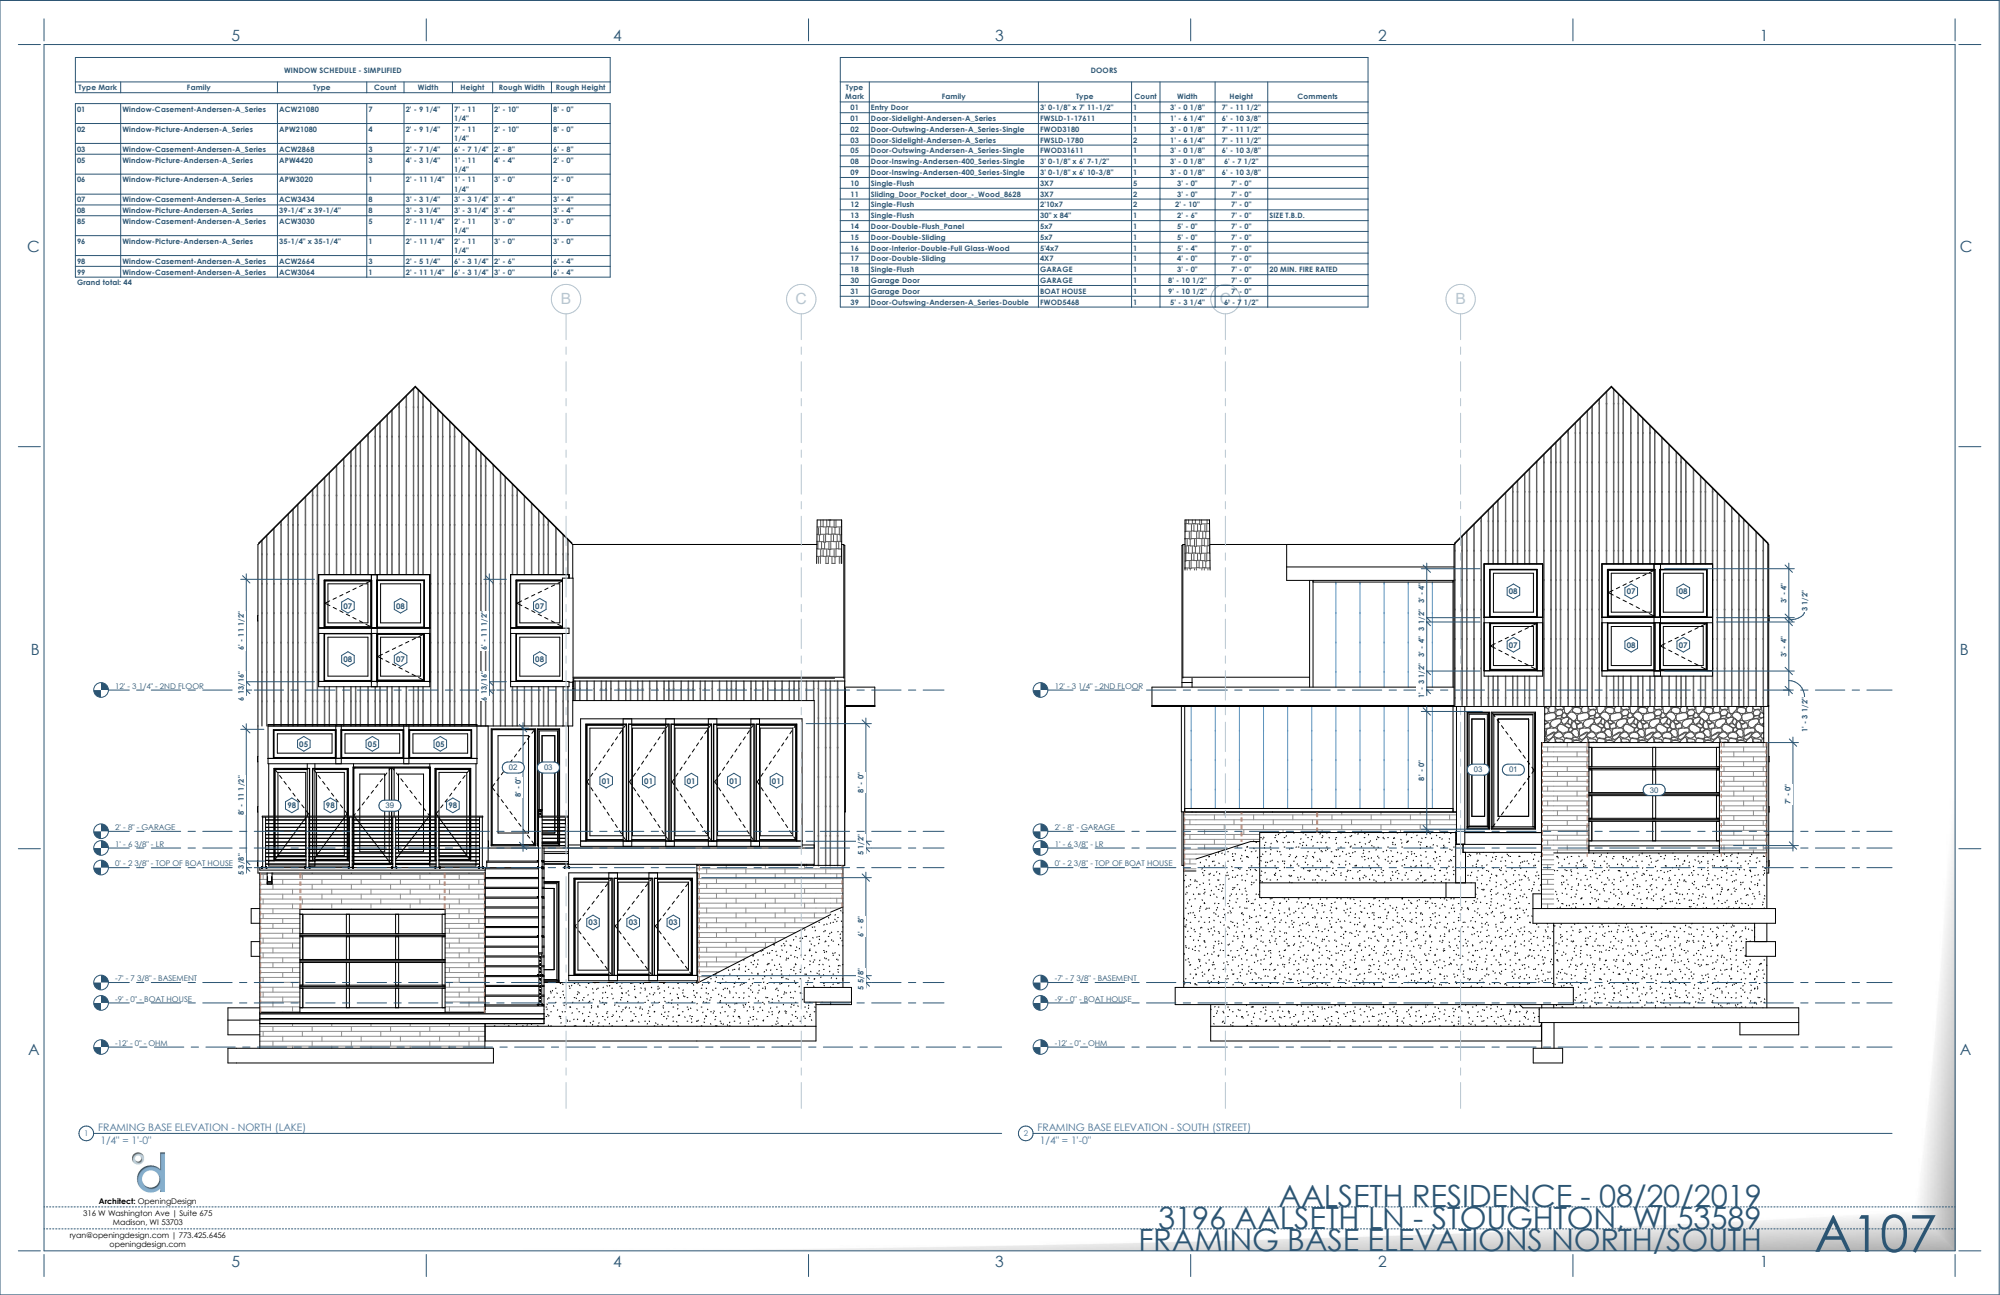
[picture p155: page 4]
2' - 8" - GARAGE; 5 1/2" 8' - 0" 5 5/8" 6' - 8" 2' - 8" - GARAGE; 1/4" = 1'-0" ¹ FRAMING BASE ELEVATION - NORTH (LAKE); 1/4" = 1'-0" ² FRAMING BASE ELEVATION - SOUTH (STREET); Window-Casement-Andersen-A_Series; ACW21080; Window-Picture-Andersen-A_Series; APW21080; ACW2868; APW4420; APW3020; ACW3434; ACW3030; ACW2664; ACW3064; Grand total: 44; DOORS; Type; Mark; Family; Count; Width; Height; Comments; Entry Door; Door-Sidelight-Andersen-A_Series; FWSLD-1-17611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

12' - 3 1/4" - 2ND FLOOR -9' - 0" - BOAT HOUSE -7' - 7 3/8" - BASEMENT 0' - 2 3/8" - TOP OF BOAT HOUSE 1' - 6 3/8" - LR -12' - 0" - OHM

A107 ³¹⁹⁶ AALSETH LN - STOUGHTON, WI 53589 FRAMING BASE ELEVATIONS NORTH/SOUTH AALSETH RESIDENCE - 08/20/2019

09 | 08 | 07 | 06 | 05 | 04 | 03 | 02 | 01.1 01 | 00

C

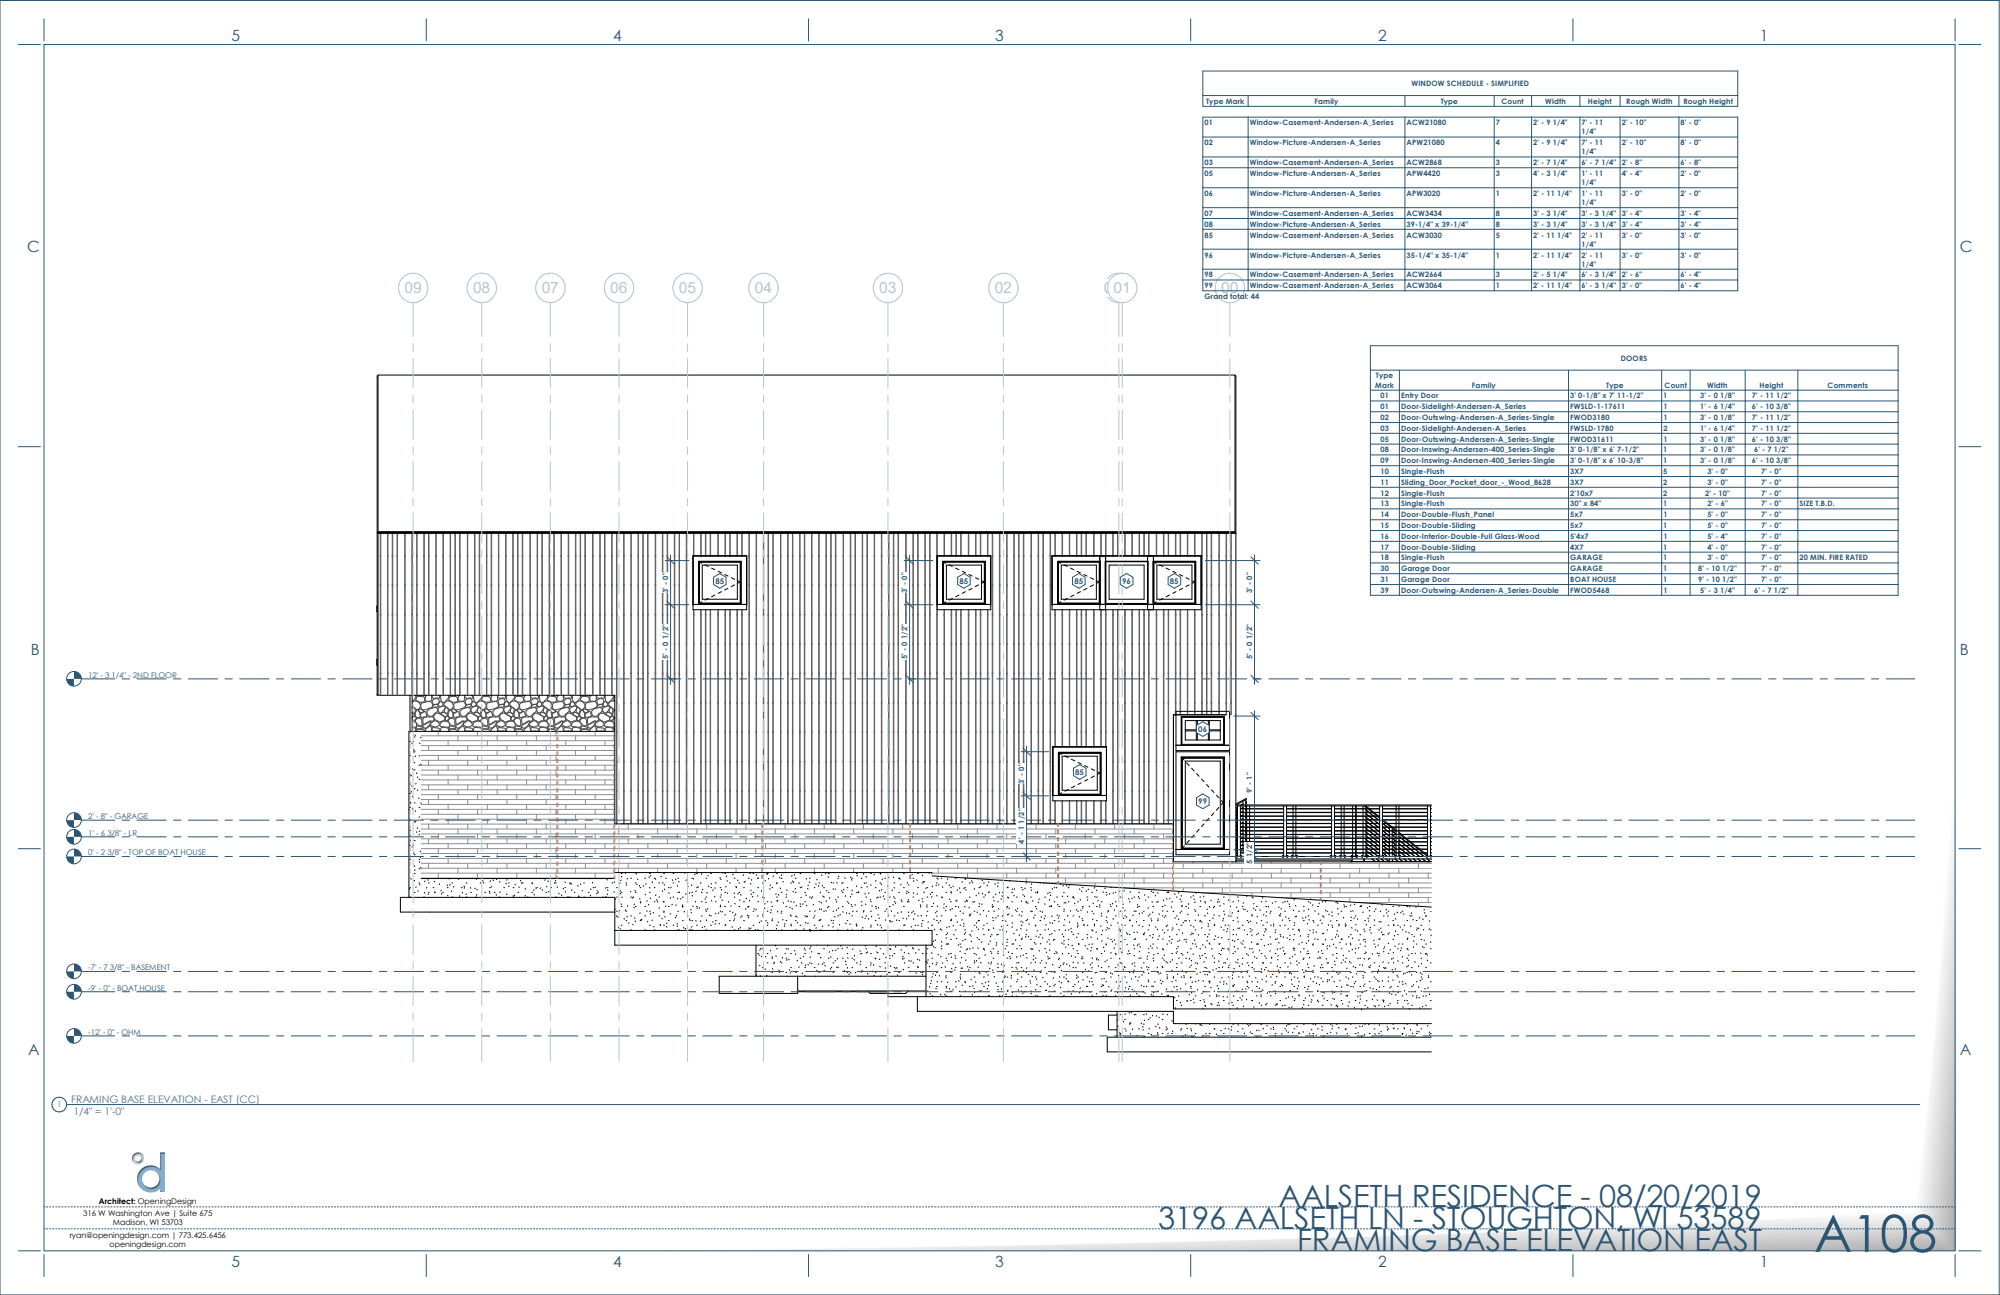
[picture p156: page 5]
2' - 8" - GARAGE; Window-Casement-Andersen-A_Series; ACW21080; Window-Picture-Andersen-A_Series; APW21080; ACW2868; APW4420; APW3020; ACW3434; ACW3030; ACW2664; ACW3064; Grand total: 44; DOORS; Type; Mark; Family; Count; Width; Height; Comments; Entry Door; Door-Sidelight-Andersen-A_Series; FWSLD-1-17611; Door-Outswing-Andersen-A_Series-Single; FWOD3180; FWSLD-1780; FWOD31611; Door-Inswing-Andersen-400_Series-Single; Single-Flush; Sliding_Door_Pocket_door_-_Wood_8628; SIZE T.B.D.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

1/4" = 1'-0" ¹ FRAMING BASE ELEVATION - EAST (CC)

A108 ³¹⁹⁶ AALSETH LN - STOUGHTON, WI 53589 FRAMING BASE ELEVATION EAST AALSETH RESIDENCE - 08/20/2019

00 | 01.1 01 | 02 | 03 | 04 | 05 | 06 | 07 | 08 | 09

C

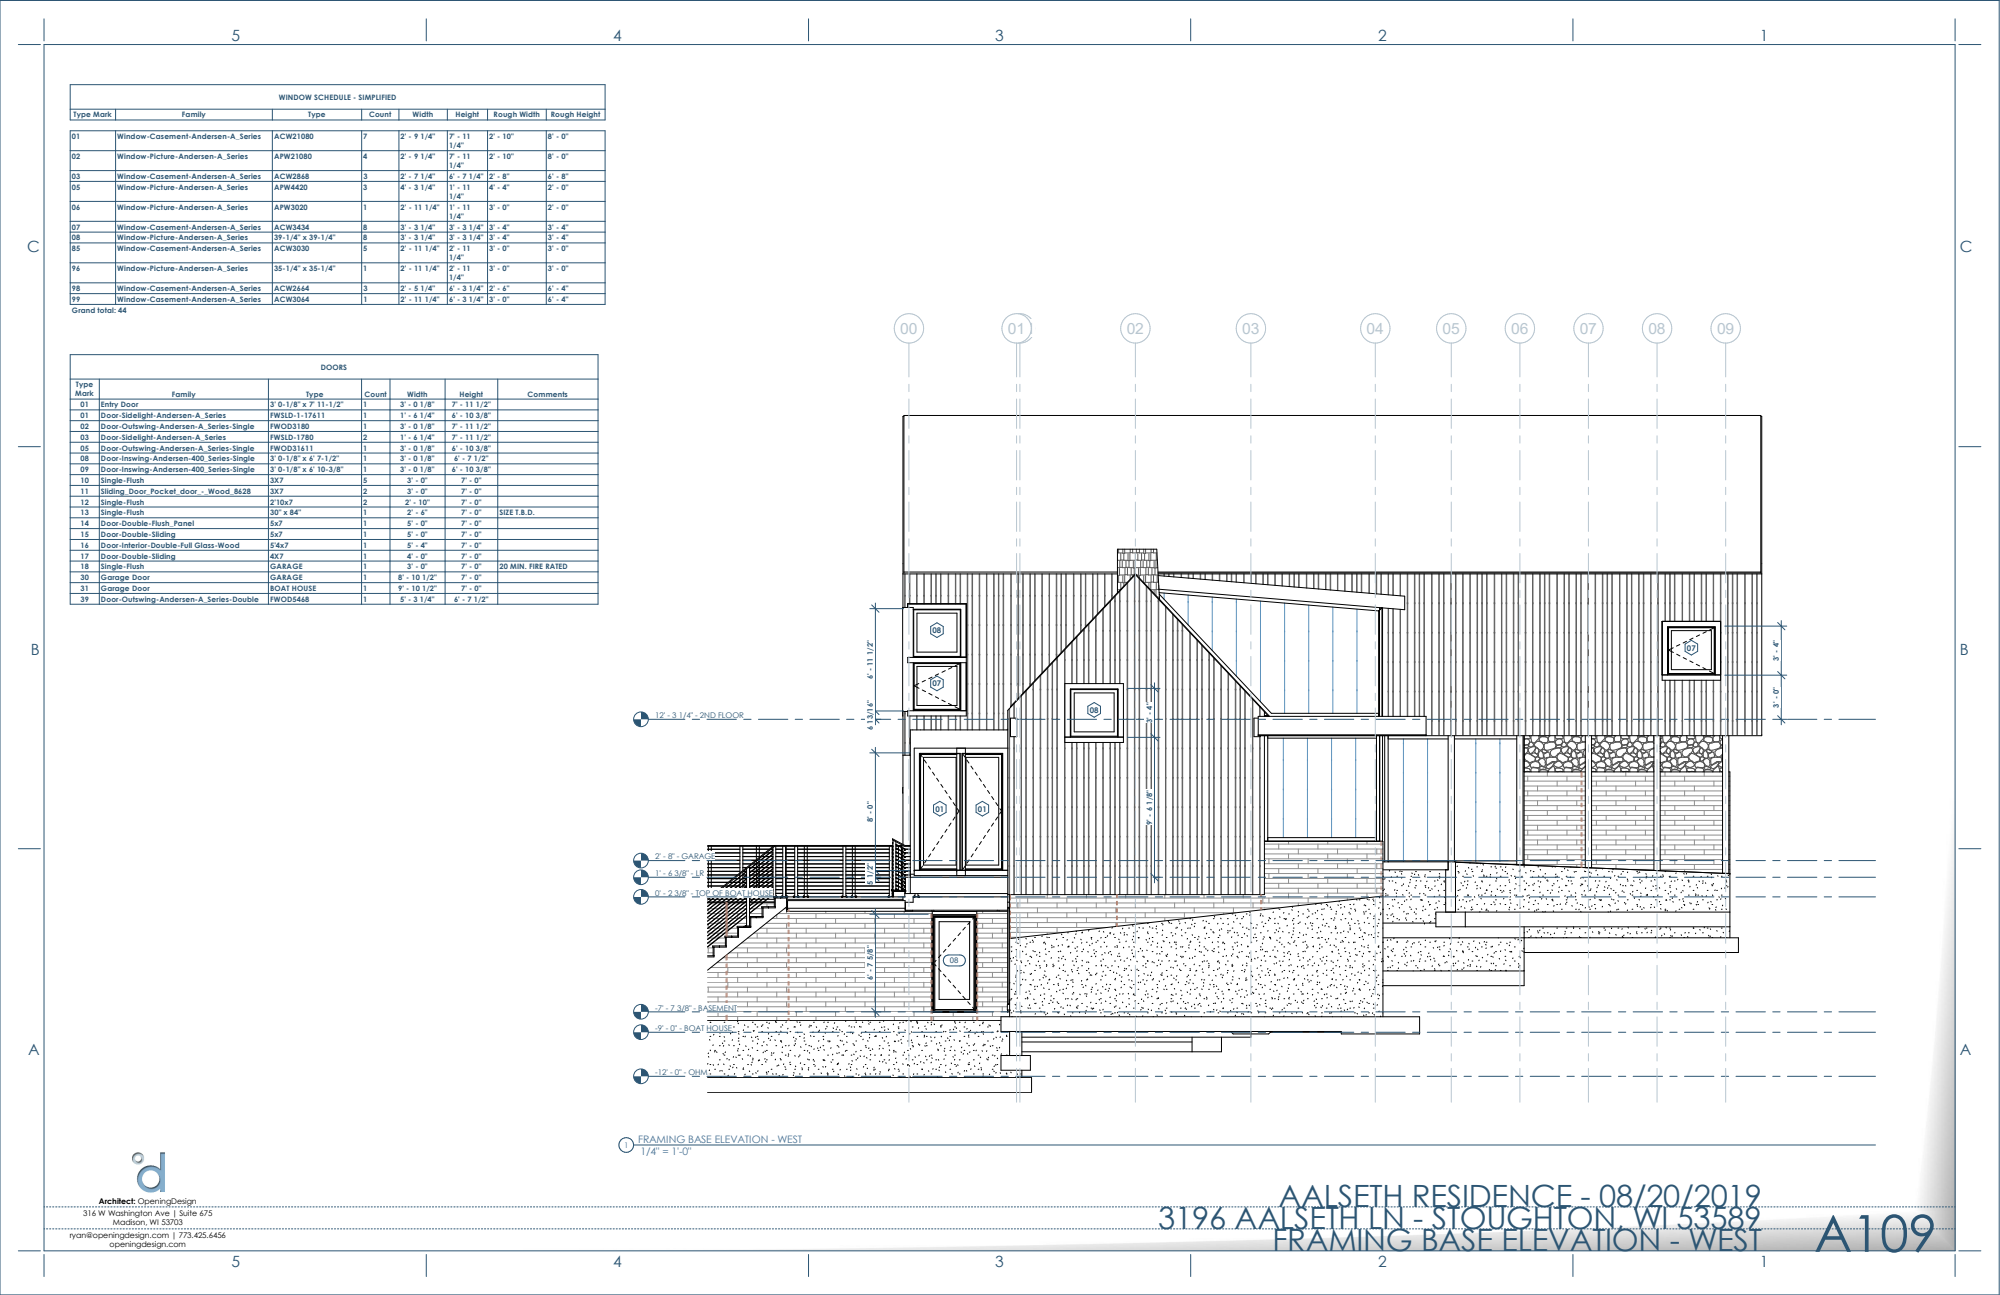
[picture p157: page 6]
2' - 8" - GARAGE; Type Mark; Family; Type; Count; Width; Height; Rough Width; Rough Height; Window-Casement-Andersen-A_Series; ACW21080; Window-Picture-Andersen-A_Series; APW21080; ACW2868; APW4420; APW3020; ACW3434; ACW3030; ACW2664; ACW3064; Grand total: 44; DOORS; Mark; Comments; Entry Door; Door-Sidelight-Andersen-A_Series; FWSLD-1-17611; Door-Outswing-Andersen-A_Series-Single; FWOD3180; FWSLD-1780; FWOD31611; Door-Inswing-Andersen-400_Series-Single; Single-Flush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

1/4" = 1'-0" ¹ FRAMING BASE ELEVATION - WEST

A109 ³¹⁹⁶ AALSETH LN - STOUGHTON, WI 53589 FRAMING BASE ELEVATION - WEST AALSETH RESIDENCE - 08/20/2019
