OpeningDesign/Aalseth_Residence/Transfer/20190723 - to Framer - Beam lengths called out/3196 Aalseth Lane 20190723 - Beam lengths called out.pdf

C

C

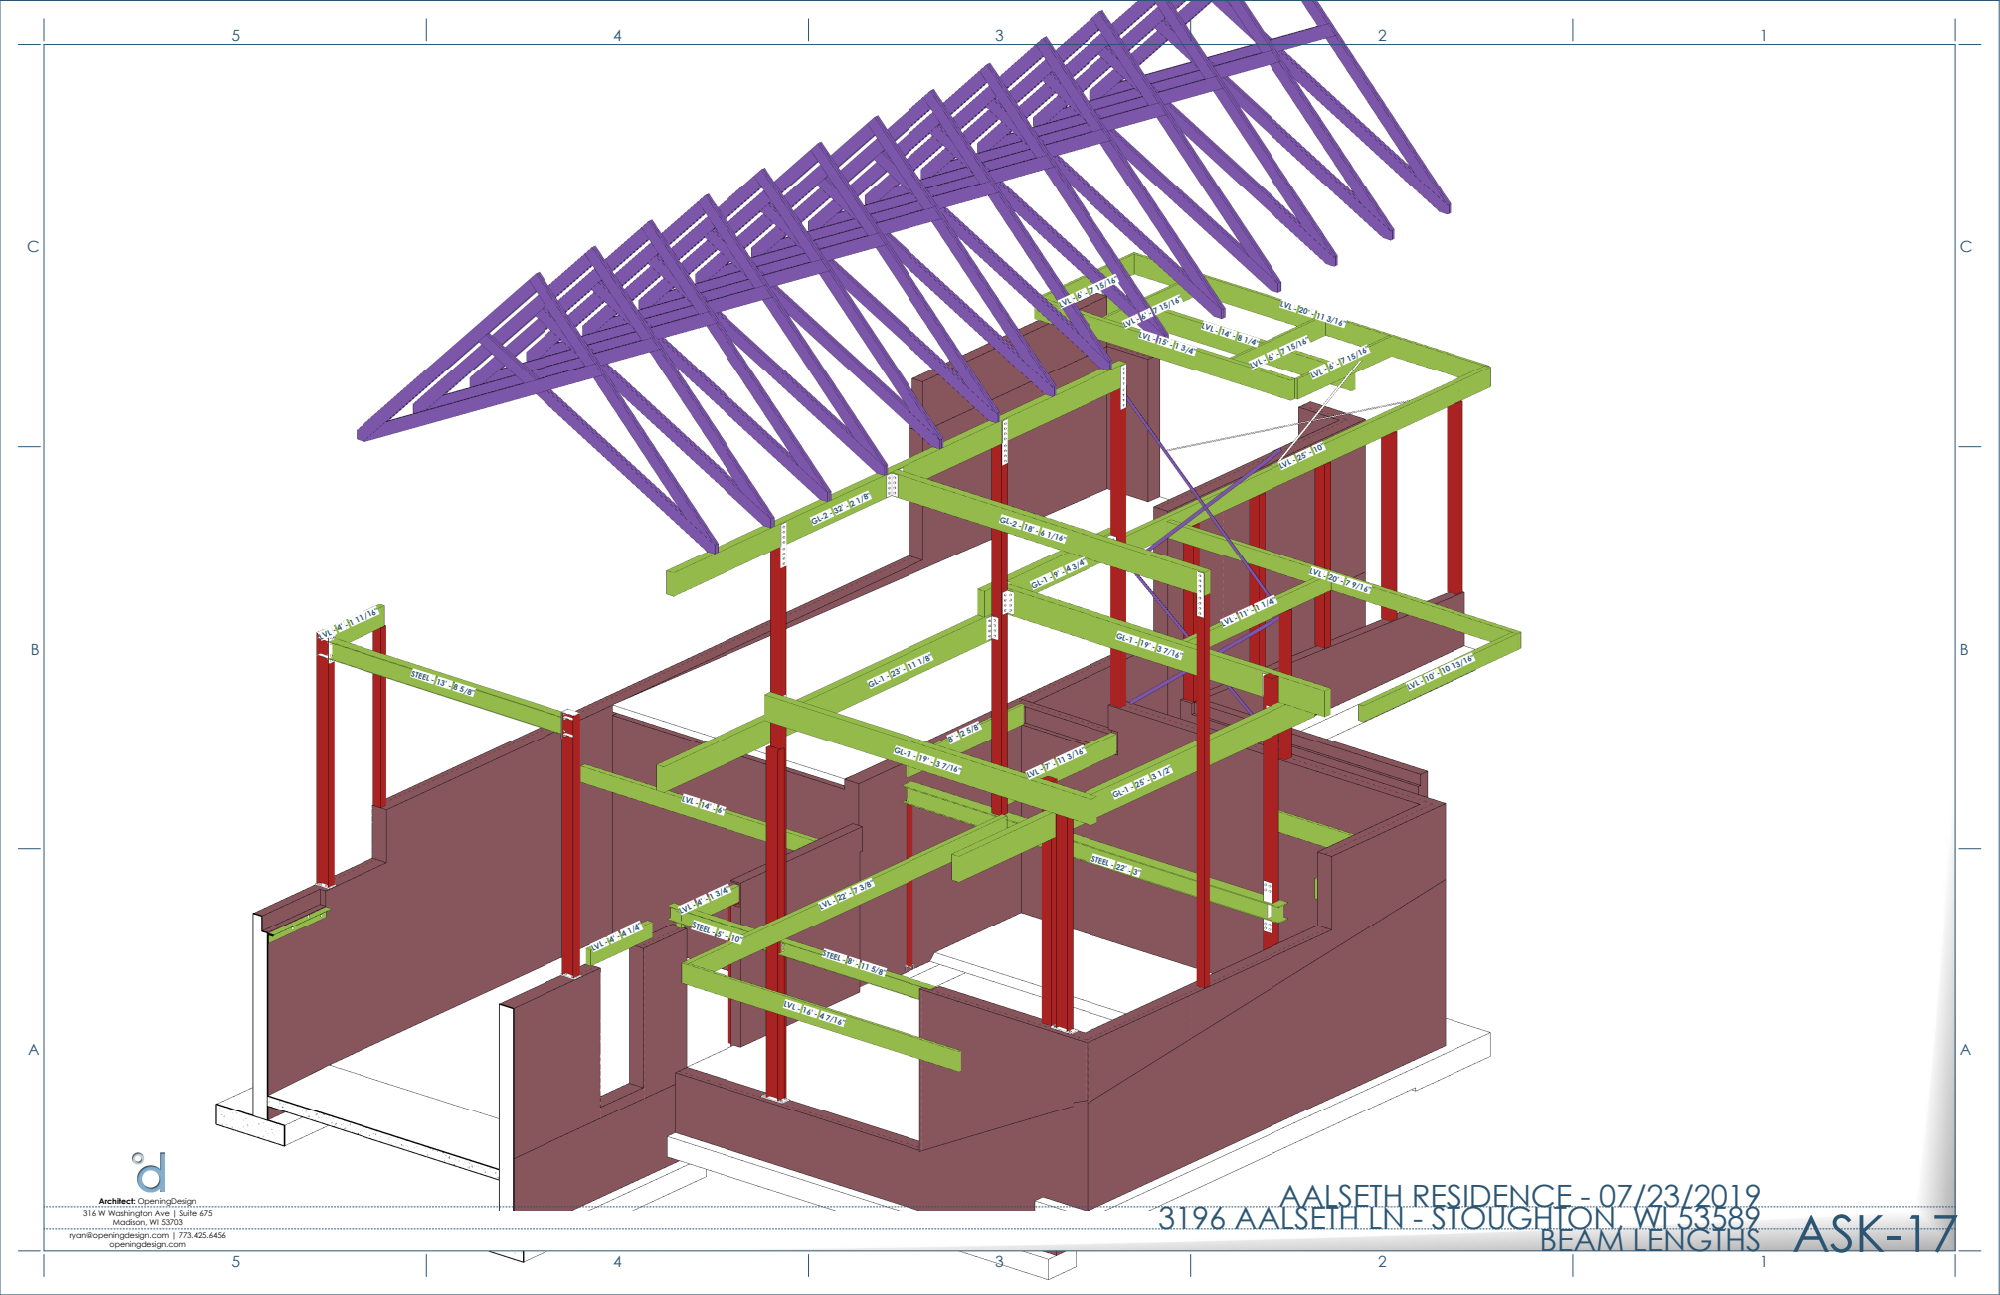
[picture p158: page 1]
LVL - 22' - 7 3/8"; LVL - 16' - 4 7/16"; LVL - 25' - 10"; LVL - 20' - 11 3/16"; LVL - 6' - 7 15/16" LVL - 6' - 7 15/16"; LVL - 20' - 7 9/16"; LVL - 10' - 10 13/16"; LVL - 11' - 1 1/4"; STEEL - 8' - 11 5/8"; STEEL - 5' - 10"; STEEL - 22' - 3"; LVL - 4' - 4 1/4"; LVL - 4' - 1 3/4"; LVL - 14' - 6"; STEEL - 13' - 8 5/8"; LVL - 4' - 1 11/16"; LVL - 7' - 11 3/16"; Madison, WI 53703; openingdesign.com

LVL - 6' - 7 15/16" LVL - 14' - 8 1/4" LVL - 15' - 1 3/4" LVL - 6' - 7 15/16"

ASK-17 ³¹⁹⁶ AALSETH LN - STOUGHTON, WI 53589 BEAM LENGTHS AALSETH RESIDENCE - 07/23/2019

Architect: OpeningDesign
316 W Washington Ave | Suite 675

ryan@openingdesign.com | 773.425.6456
