OpeningDesign/Aalseth_Residence/Transfer/20190605 - to concrete conc - knee wall clarifications/20190605 - 3196 Aalseth Lane.pdf

05 | 06 | 07 | 08 | 09

C

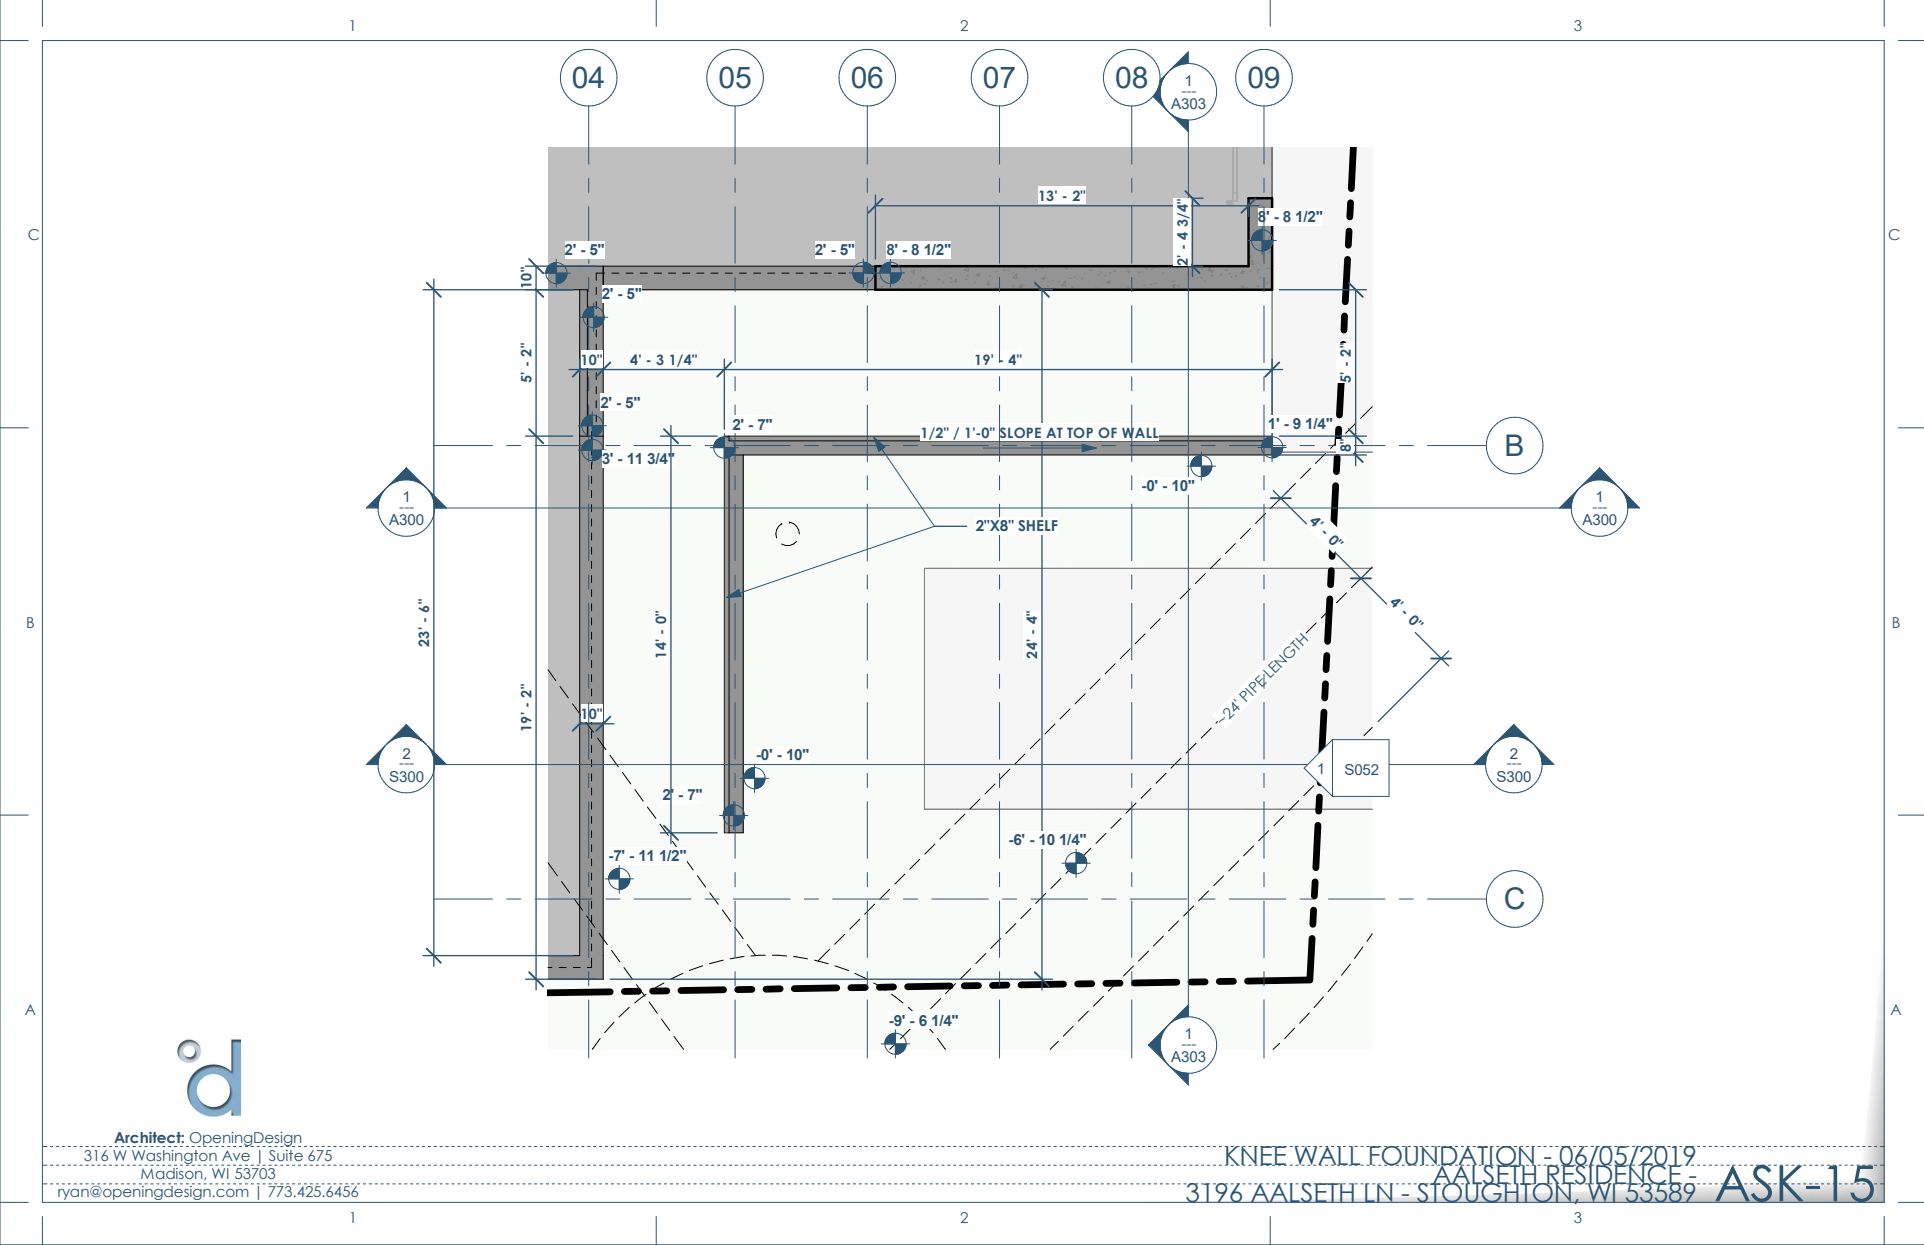
[picture p159: page 1]
~24' PIPE LENGTH; SLOPE; AT TOP OF WALL 2' - 7"; 2"X8" SHELF; Madison, WI 53703; ryan@openingdesign.com | 773.425.6456; 3196 AALSETH LN - STOUGHTON, WI 53589 AALSETH RESIDENCE - KNEE WALL FOUNDATION - 06/05/2019 ASK-15

Architect: OpeningDesign
316 W Washington Ave | Suite 675
