OpeningDesign/Aalseth_Residence/Transfer/20190603 - to conc sub - location of footings/20190603 - 3196 Aalseth Lane.pdf

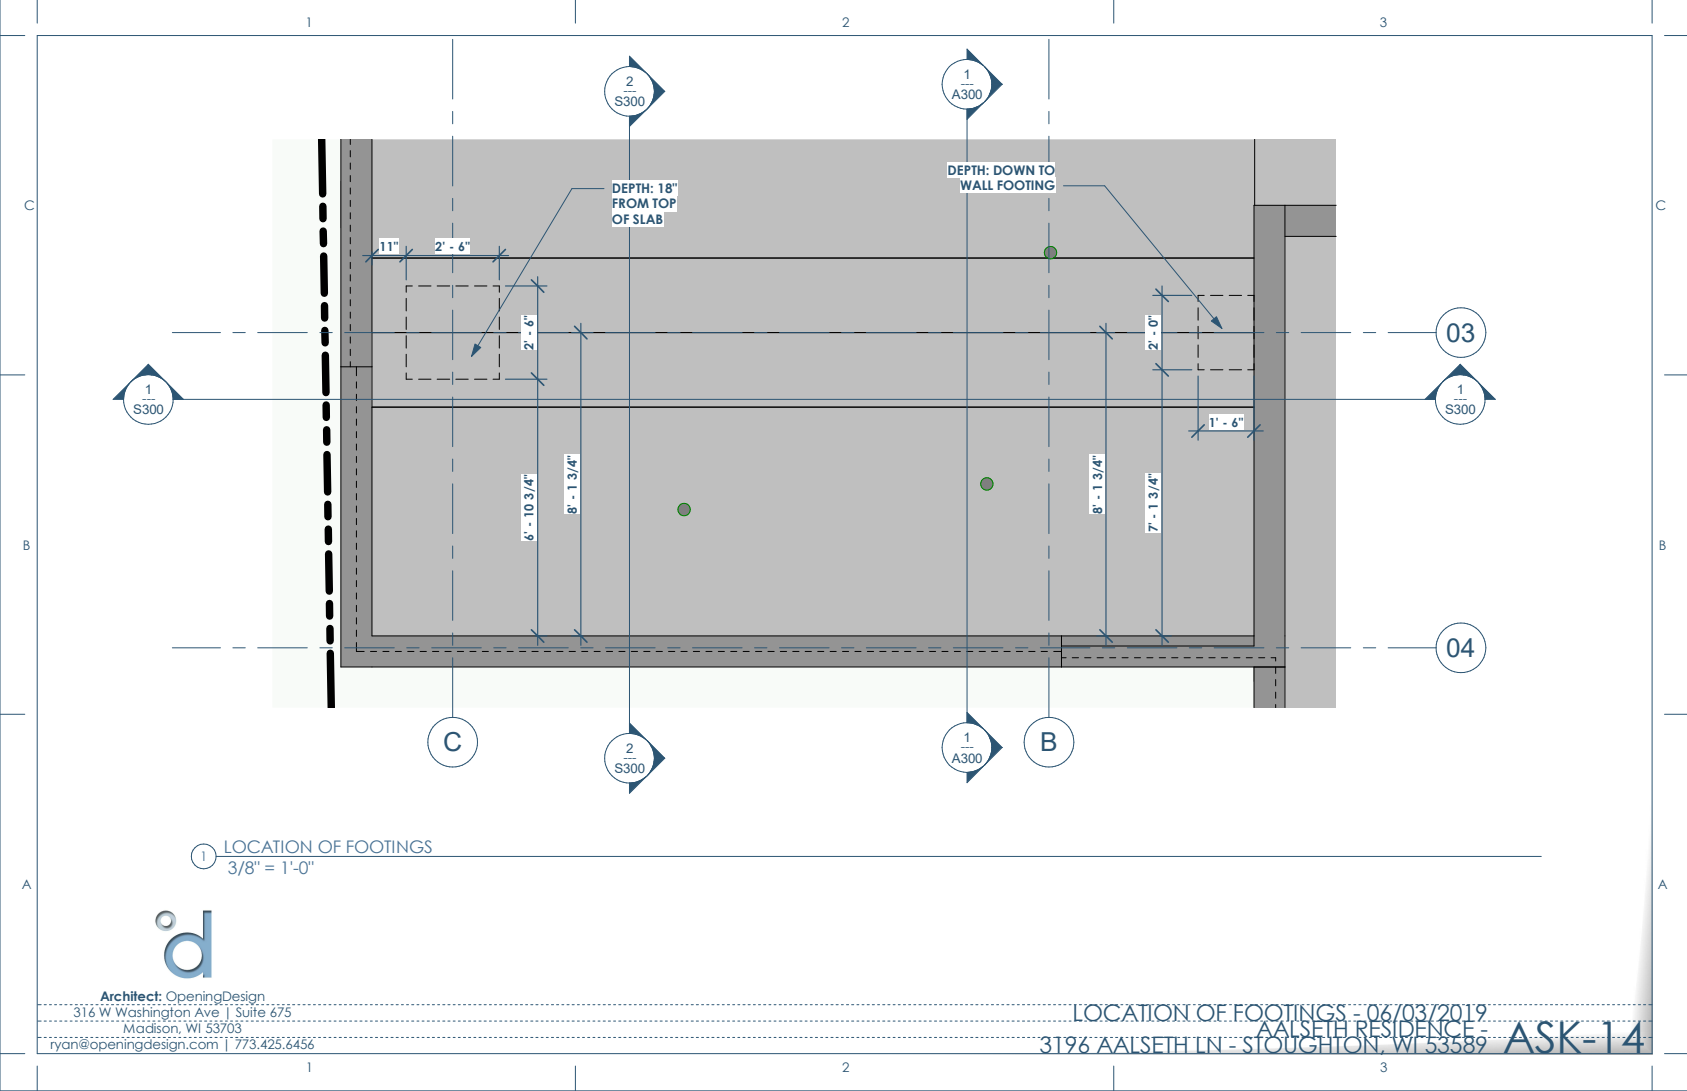
[picture p160: page 1]
DEPTH: 18" FROM TOP; SLAB; Madison, WI 53703; ryan@openingdesign.com | 773.425.6456; 3196 AALSETH LN - STOUGHTON, WI 53589 AALSETH RESIDENCE - LOCATION OF FOOTINGS - 06/03/2019 ASK-14

DEPTH: DOWN TO
WALL FOOTING

LOCATION OF FOOTINGS

Architect: OpeningDesign
316 W Washington Ave | Suite 675
