OpeningDesign/Aalseth_Residence/Transfer/20190508 - to plumber & hvac sub - site visit/20190508 - 3196 Aalseth Lane.pdf

02

03

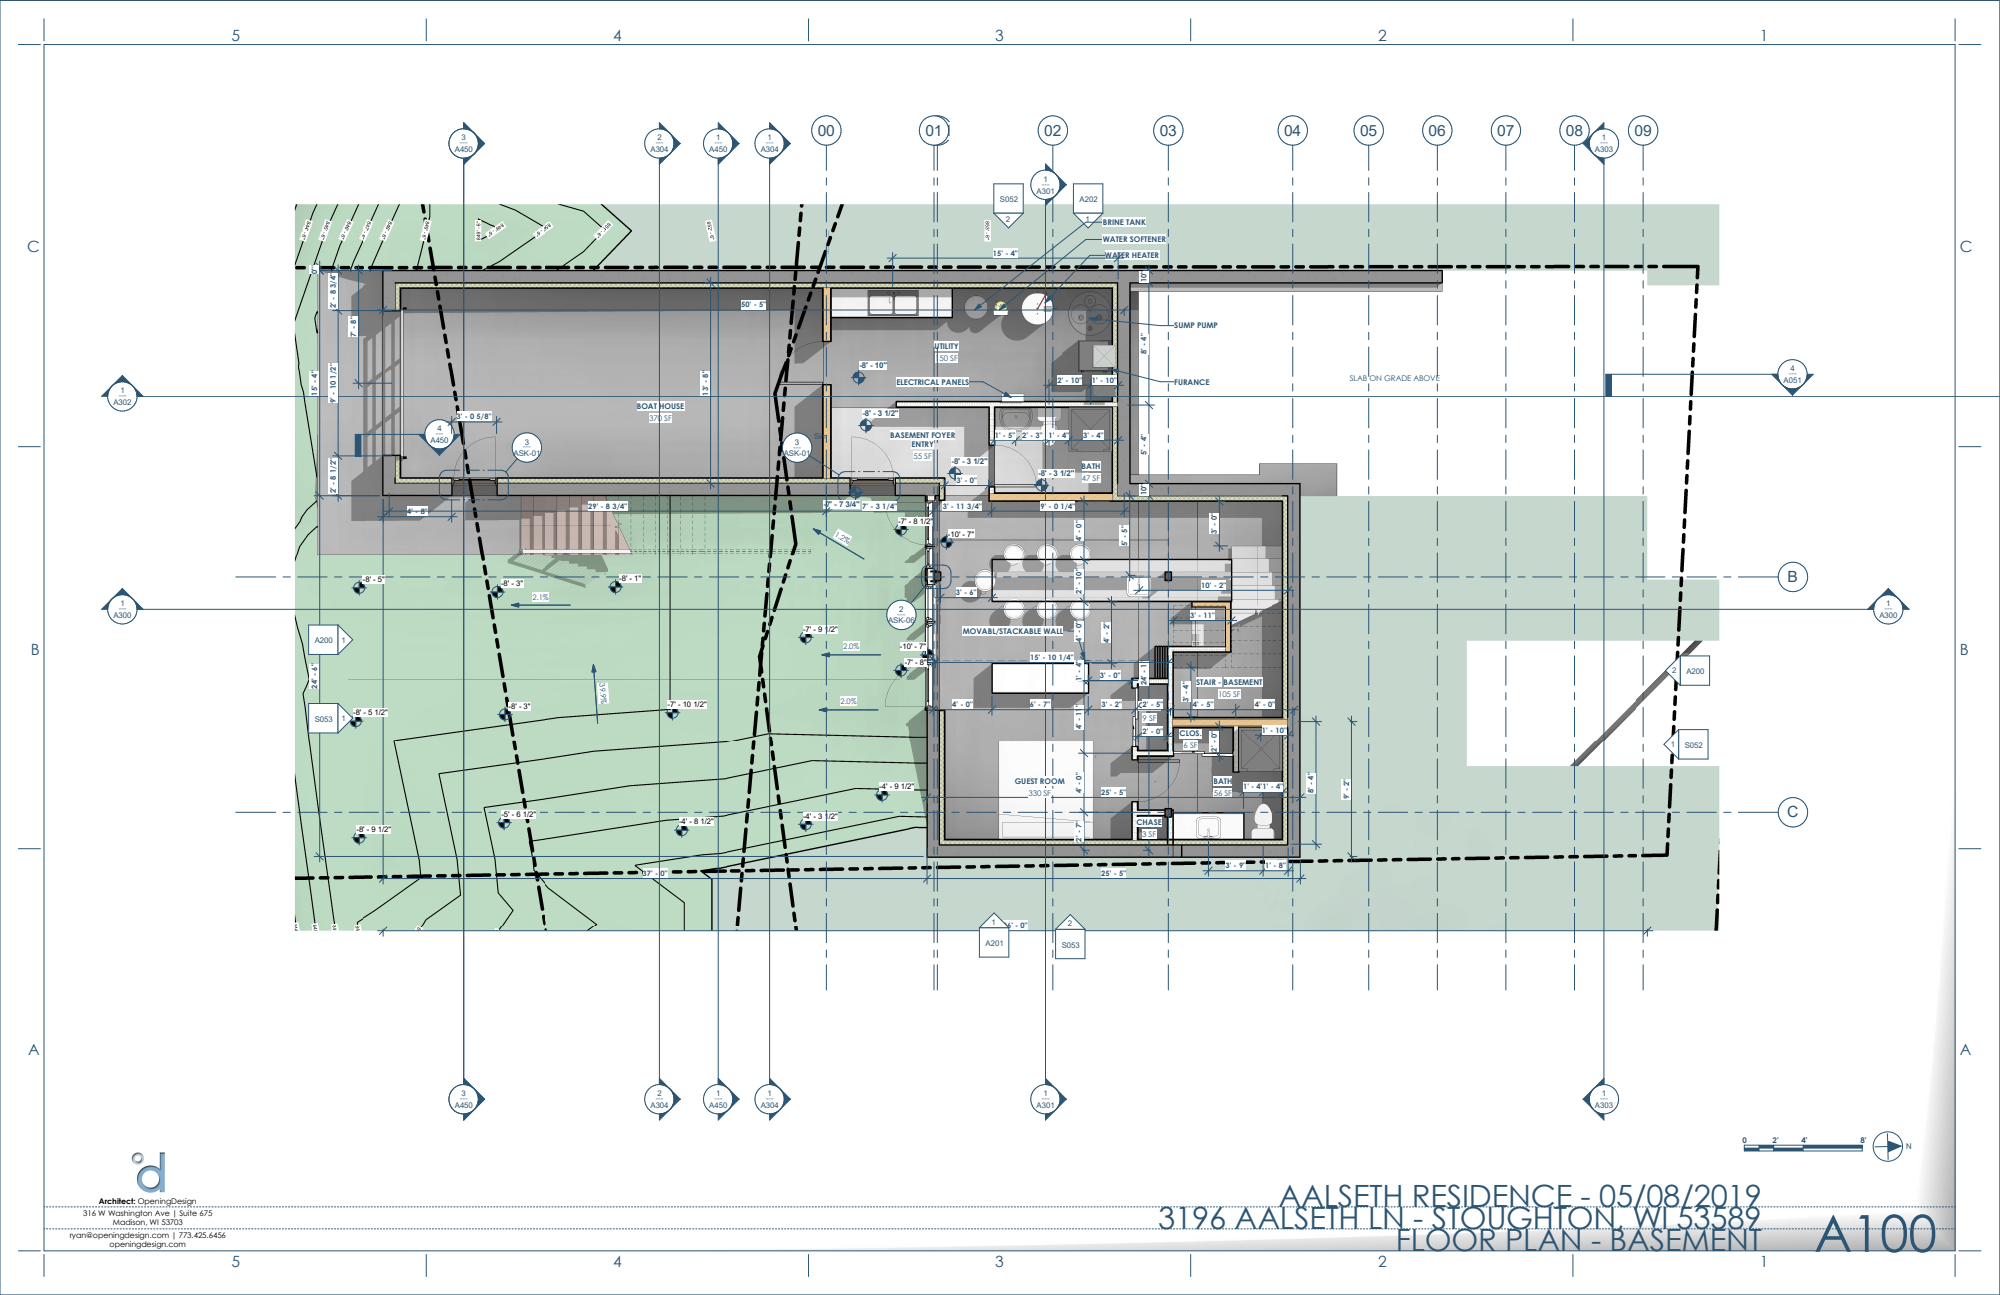
[picture p161: page 1]
BOAT HOUSE; UTILITY; STAIR - BASEMENT; BATH; WATER HEATER; BRINE TANK; WATER SOFTENER; --- ASK-01; Sim; SUMP PUMP; --- ASK-06; CHASE; CLOS.; GUEST ROOM; BASEMENT FOYER ENTRY; ELECTRICAL PANELS; FURANCE; Madison, WI 53703; openingdesign.com; AALSETH RESIDENCE - 05/08/2019

SLAB ON GRADE ABOVE

MOVABL/STACKABLE WALL

Architect: OpeningDesign
316 W Washington Ave | Suite 675

3196 AALSETH LN - STOUGHTON, WI 53589

ryan@openingdesign.com | 773.425.6456

FLOOR PLAN - BASEMENT

02

03

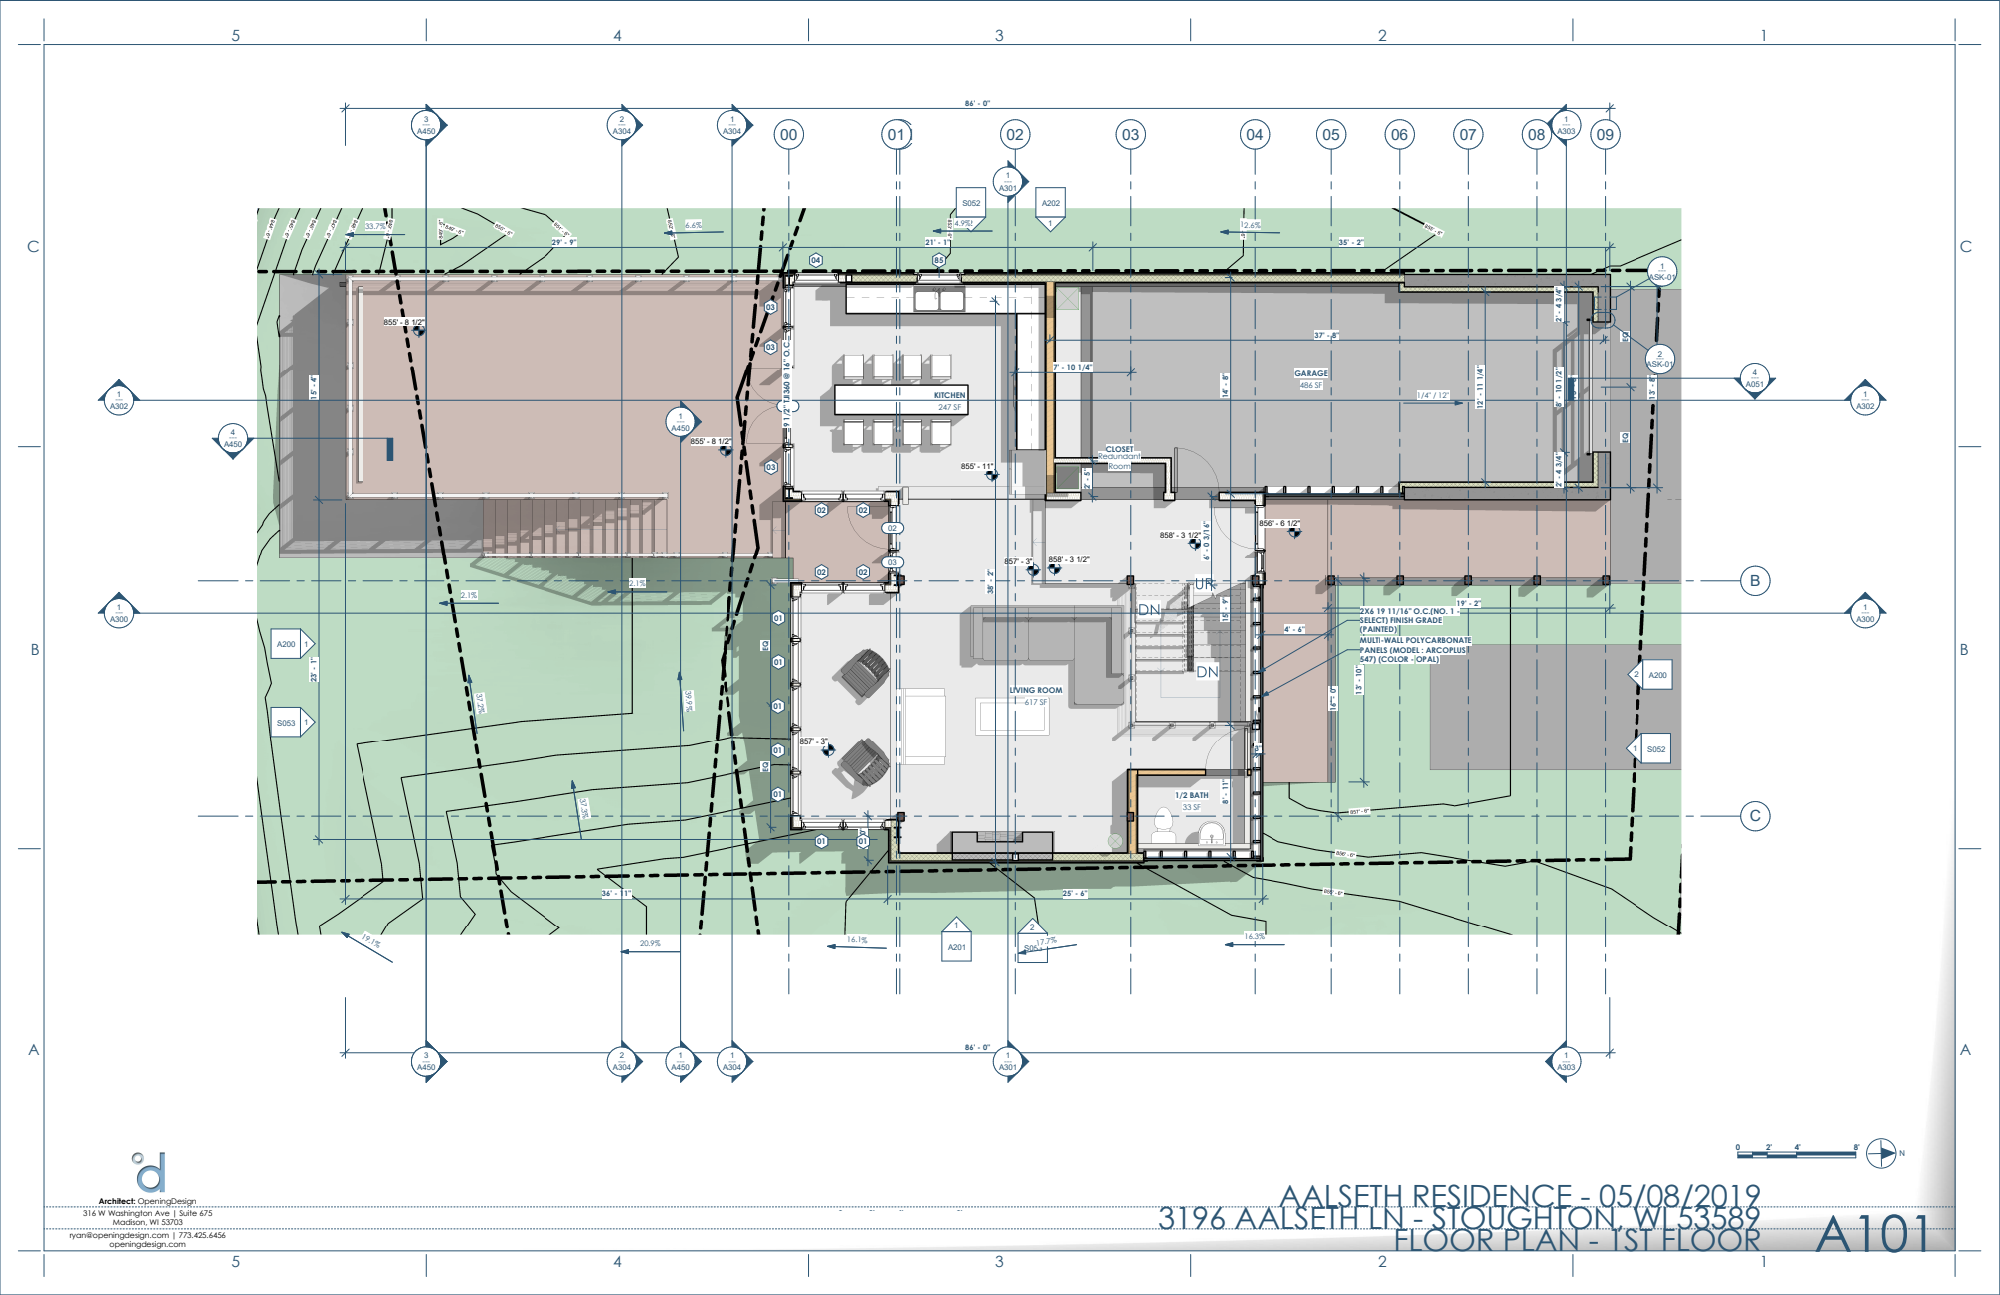
[picture p162: page 2]
GARAGE; 1/2 BATH; KITCHEN; LIVING ROOM; Redundant Room; CLOSET; --- ASK-01; 009 1/2" TJI360 @ ¹⁶" O.C.

SELECT) FINISH GRADE
(PAINTED)
MULTI-WALL POLYCARBONATE
PANELS (MODEL : ARCOPLUS
547) (COLOR - OPAL)

FLOOR PLAN - 1ST FLOOR

02

| | 03

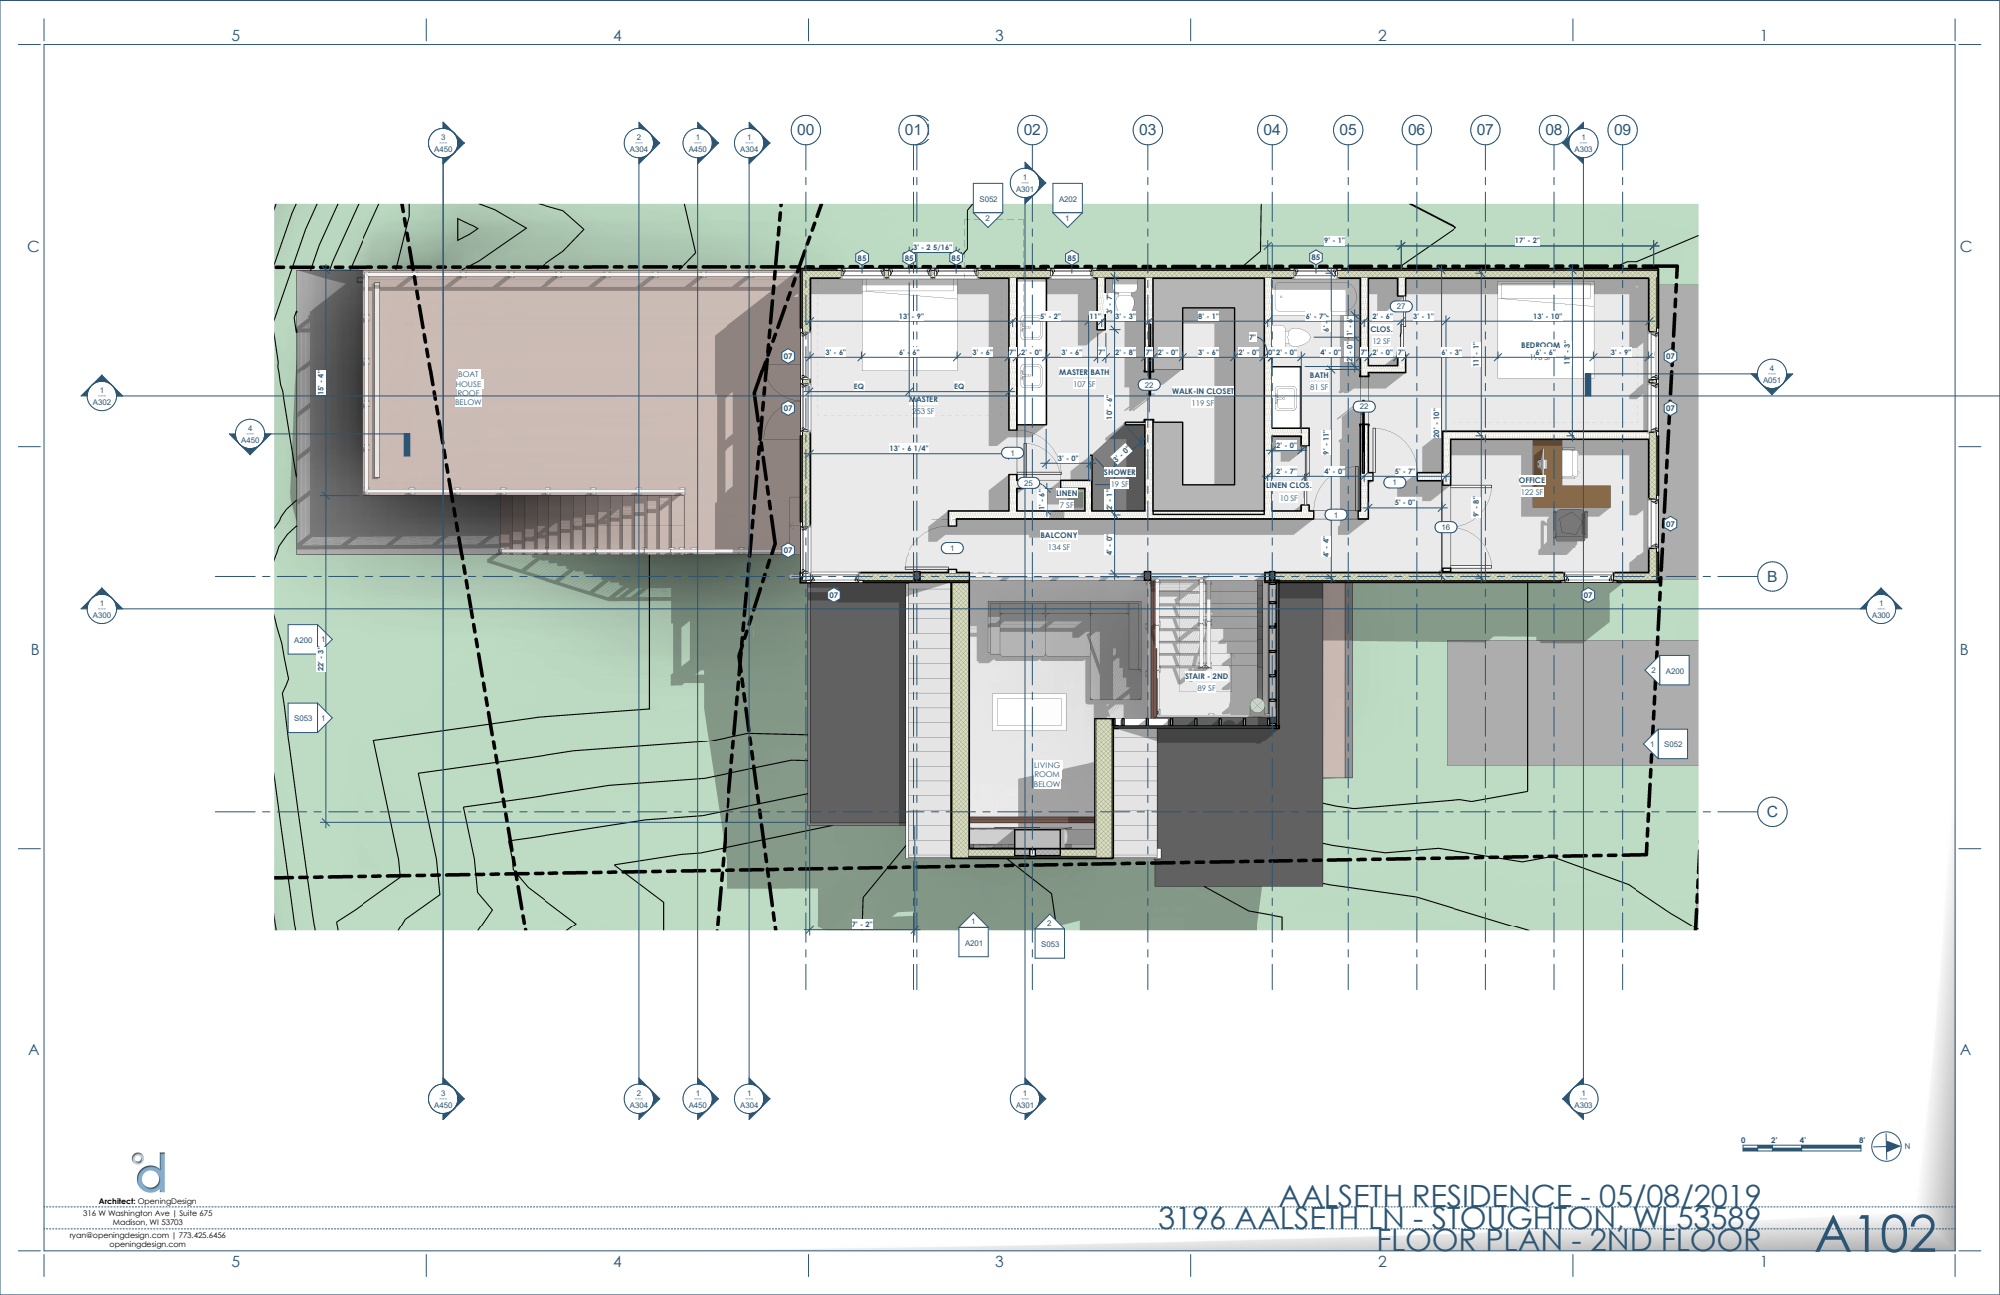
[picture p163: page 3]
MASTER; MASTER BATH; BATH; OFFICE; STAIR - 2ND; LIVING ROOM BELOW; BOAT HOUSE ROOF BELOW; BEDROOM; LINEN; CLOS.; LINEN CLOS.; SHOWER

WALK-IN CLOSET

BALCONY | 134 SF

FLOOR PLAN - 2ND FLOOR
